mbardin/Cyberinet/zMusic Composition Scores/scores/puzzleFistCompleteDraft - 2023-05-08.pdf

# Puzzle of a Park

## for the Cyberinet

## Matthew A. Bardin

(2023)

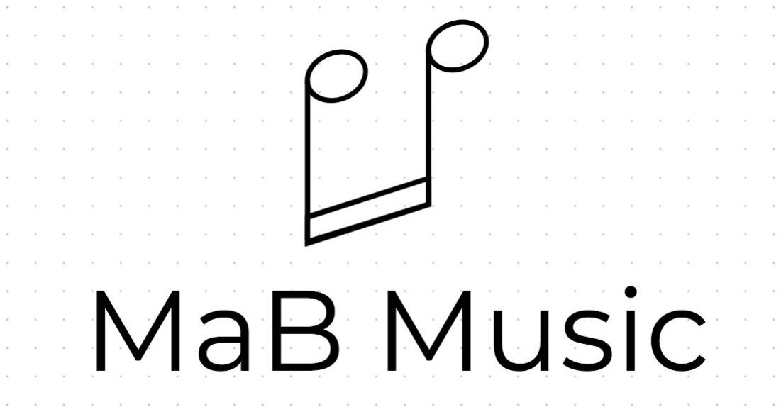
[picture p26: figure]

Program Note:
A pleasant stroll through a park, built through several interconnected ideas. The whole scene can'tcome together until it has been built up from its various smaller pieces. Ideas often take on a different context when observed in a vacuum instead of as a whole, much like putting a large puzzle together.

Performance Note:
While intended to be performed with the Cyberinet, this piece can be performed without it. To do this, a microphone and loop pedal are required. When using this setup, the Max patch (link given below) is not required. If one section of the music is performed out of sync, continue as if this was intended. Thematically, this represents trying to fit a piece of the puzzle where it doesn't actually go. At the beginning of the next section, pressing button 1 should resync the recordings. A short pause between each repetitsion can be done, but should not be an excessive pause.

When performing with the Cyberinet, the button expansion is required. Button 1 is programmed to trigger new recordings and playback, while button 2 can be used to stop the playback in the event of a chatastrophic failure. All of the electronic

On the Cyberinet:
The Cyberinet is an electronic enhancement to the standard B-flat clarinet. By replacing the mouthpiece and barrel with the Cyberinet, the performer and compsoer gain access to an integrated collection of sensors that collect various performance data. This data can be wirelessly transmitted to a computer for electronic processing and software control. An ever-growing list of optional expansions is also available to be connected to the Cyberinet to allow for the performer to customize the instrument ot their performance needs.

The complete list of hardware needed for this composition is:

The Cyberinet
Button Expansion
Microphone
Audio Interface
Computer running the Max patch available here:

On Notation:
This version of the score is intended to show the intended allignment of the previously recorded loops along with the voice currently being played by the soloist. If the solost only wants to look at their line without the playback indicated, that score is available at matthewbardin.com.
In this score, the performer should perform their line (the top of each system) from beginning to end without stopping. A short pause between each repetitsion can be done, but should not be an excessive pause.
Notes shown with a cross notehead indicate when a button should be pressed. These button presses, when performed in sync, will cause the current recording to stop, start the new recording, and playback all previous recordings in sync.

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

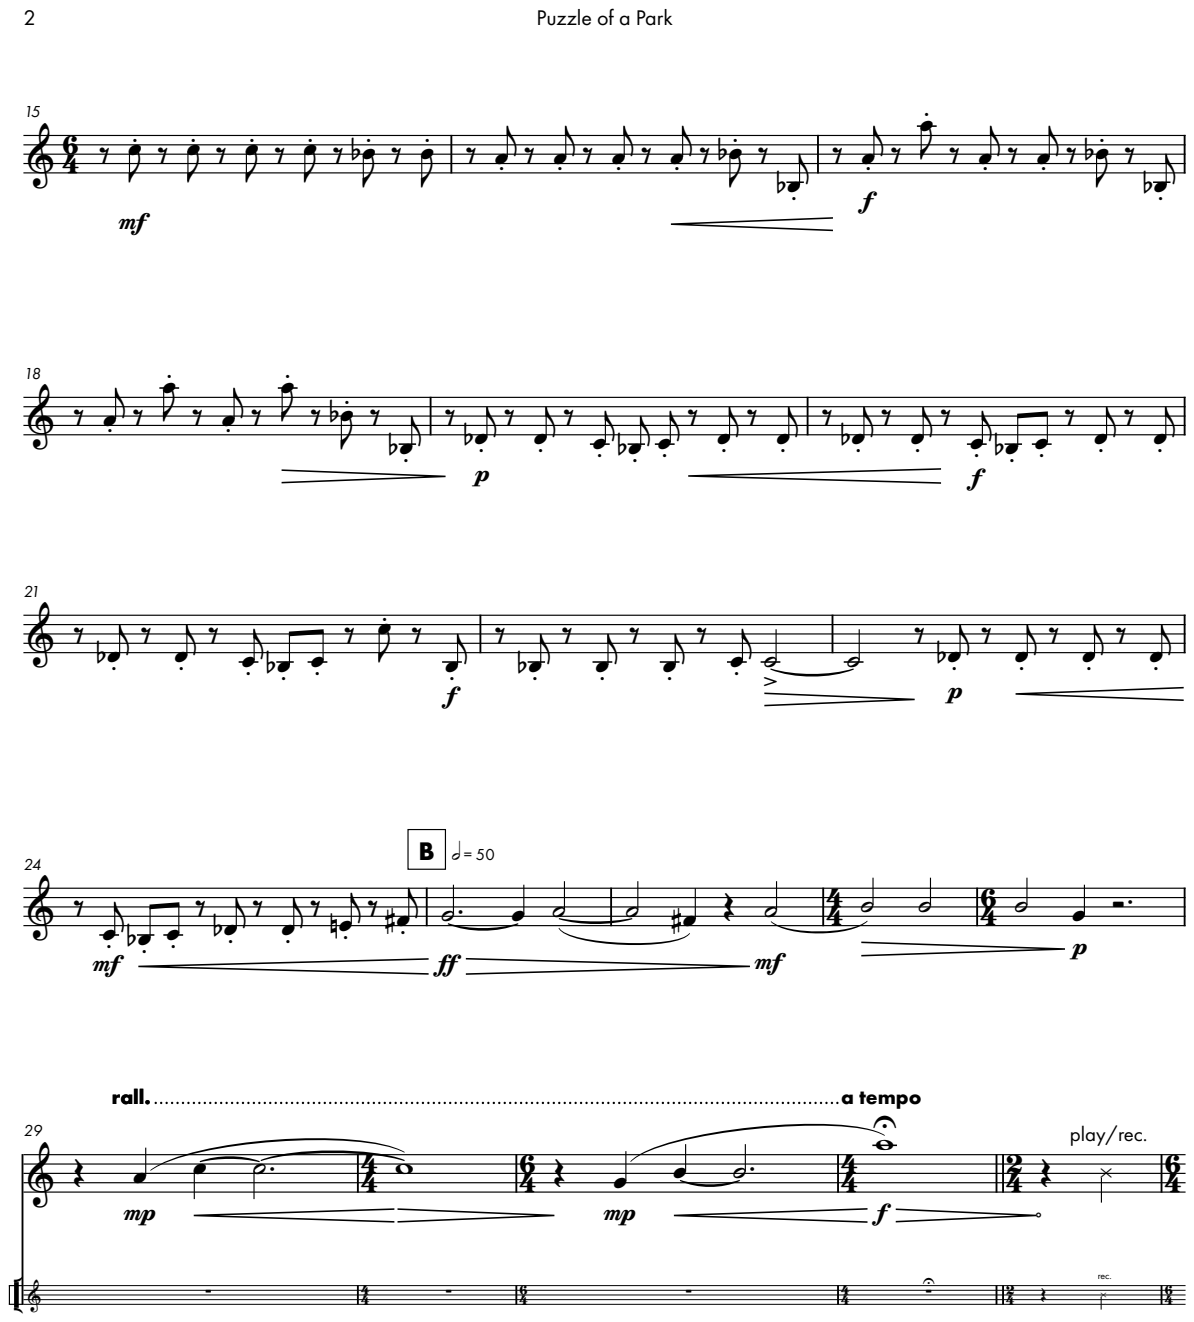
[picture p27: page 6]

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

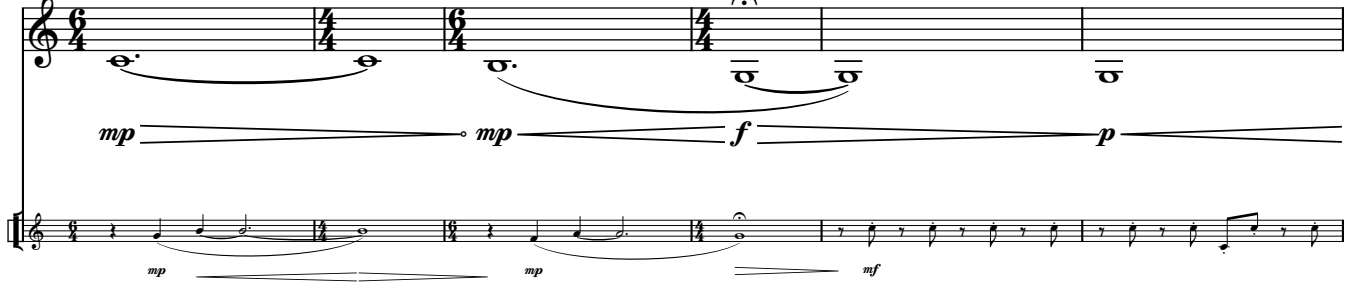
[picture p28: figure]

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

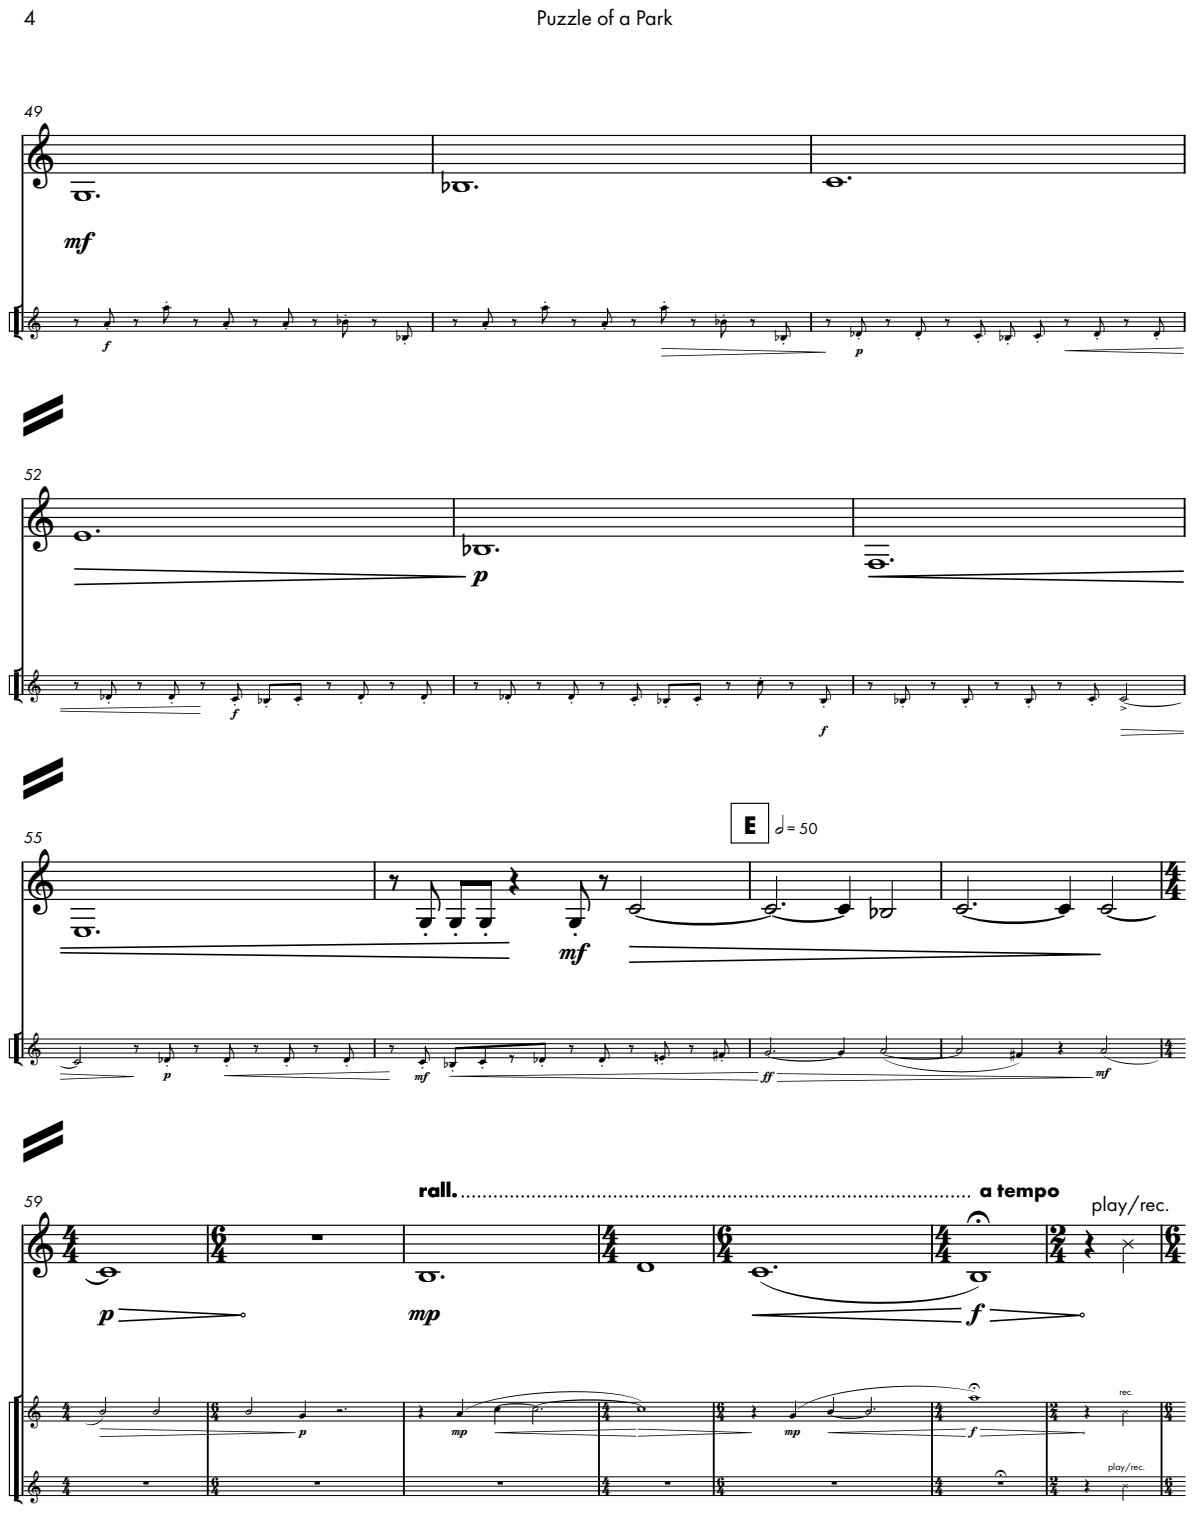
[picture p29: page 8]

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

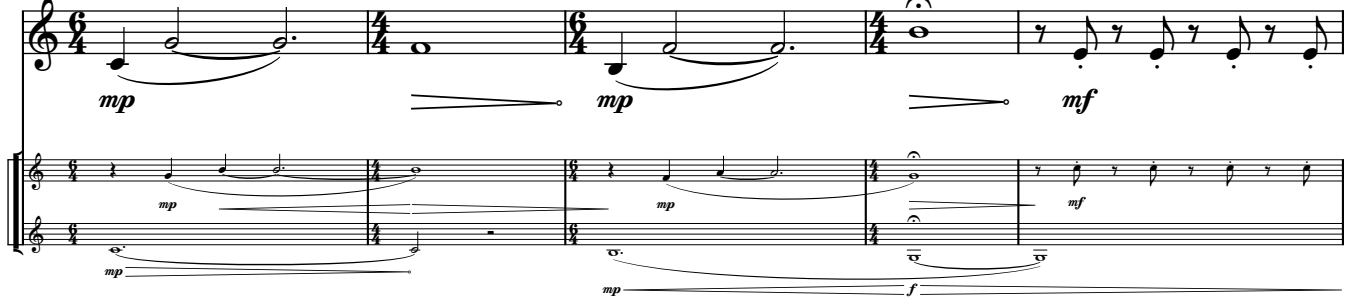
[picture p30: figure]

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

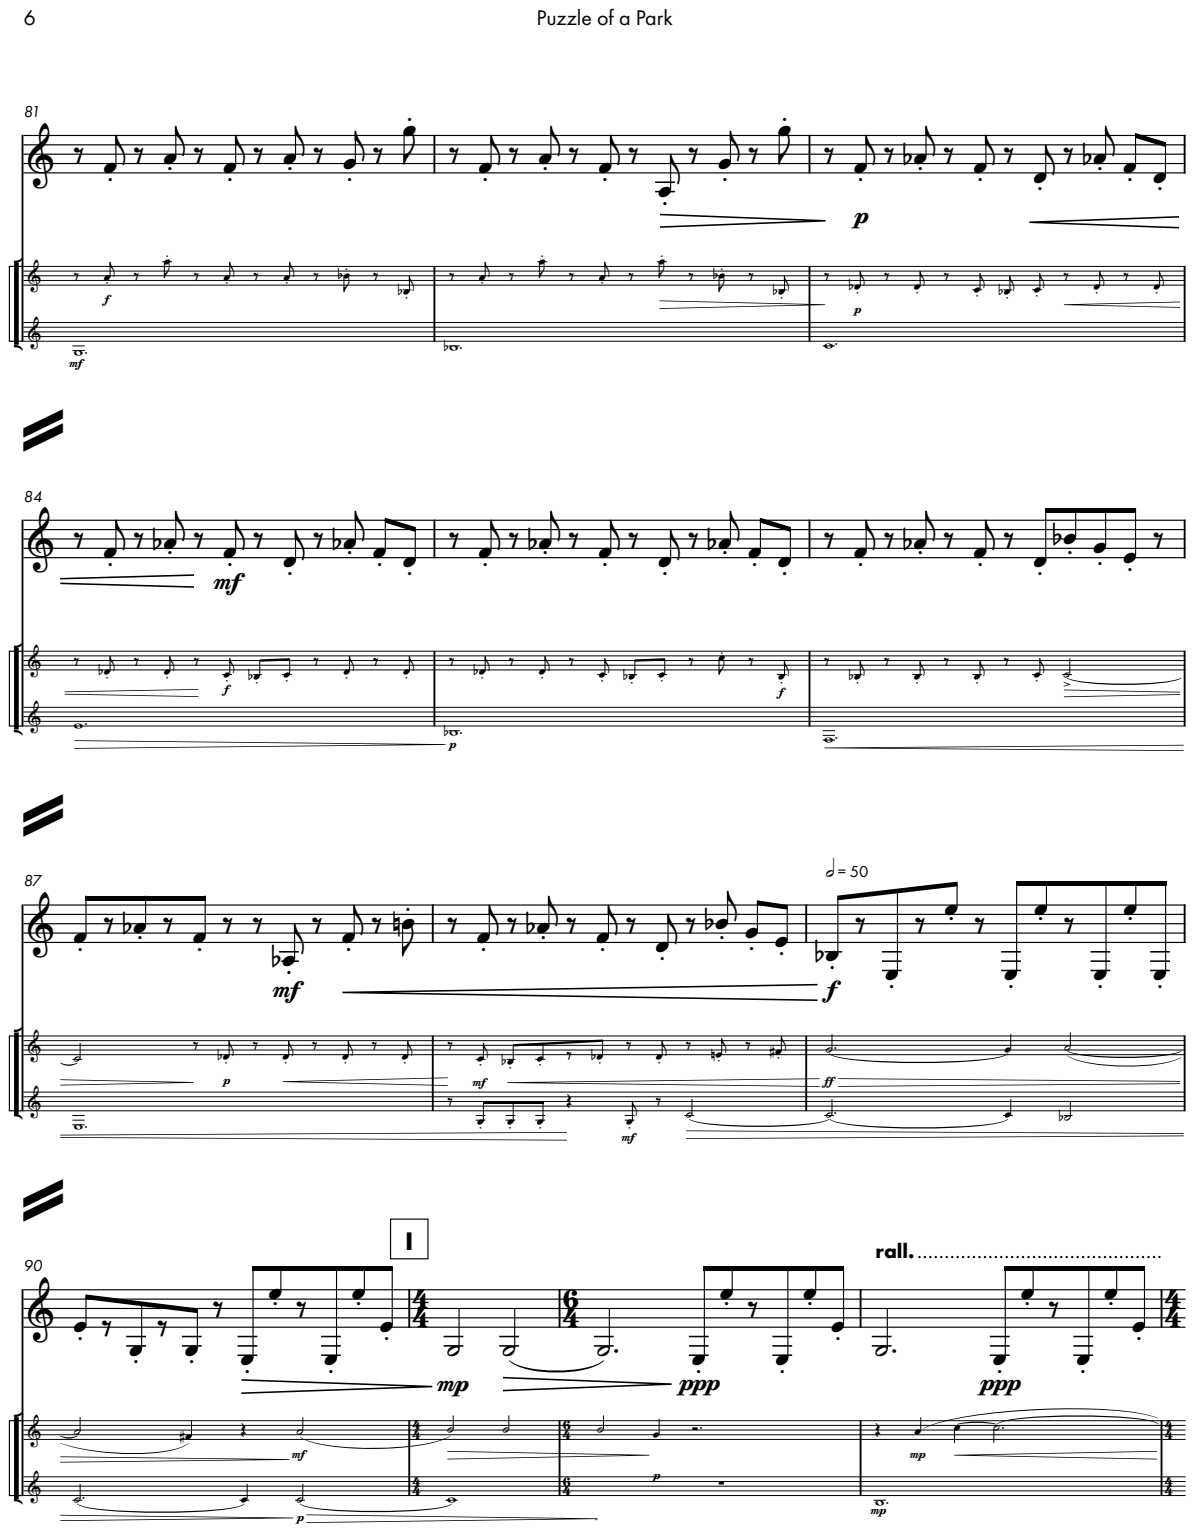
[picture p31: page 10]

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

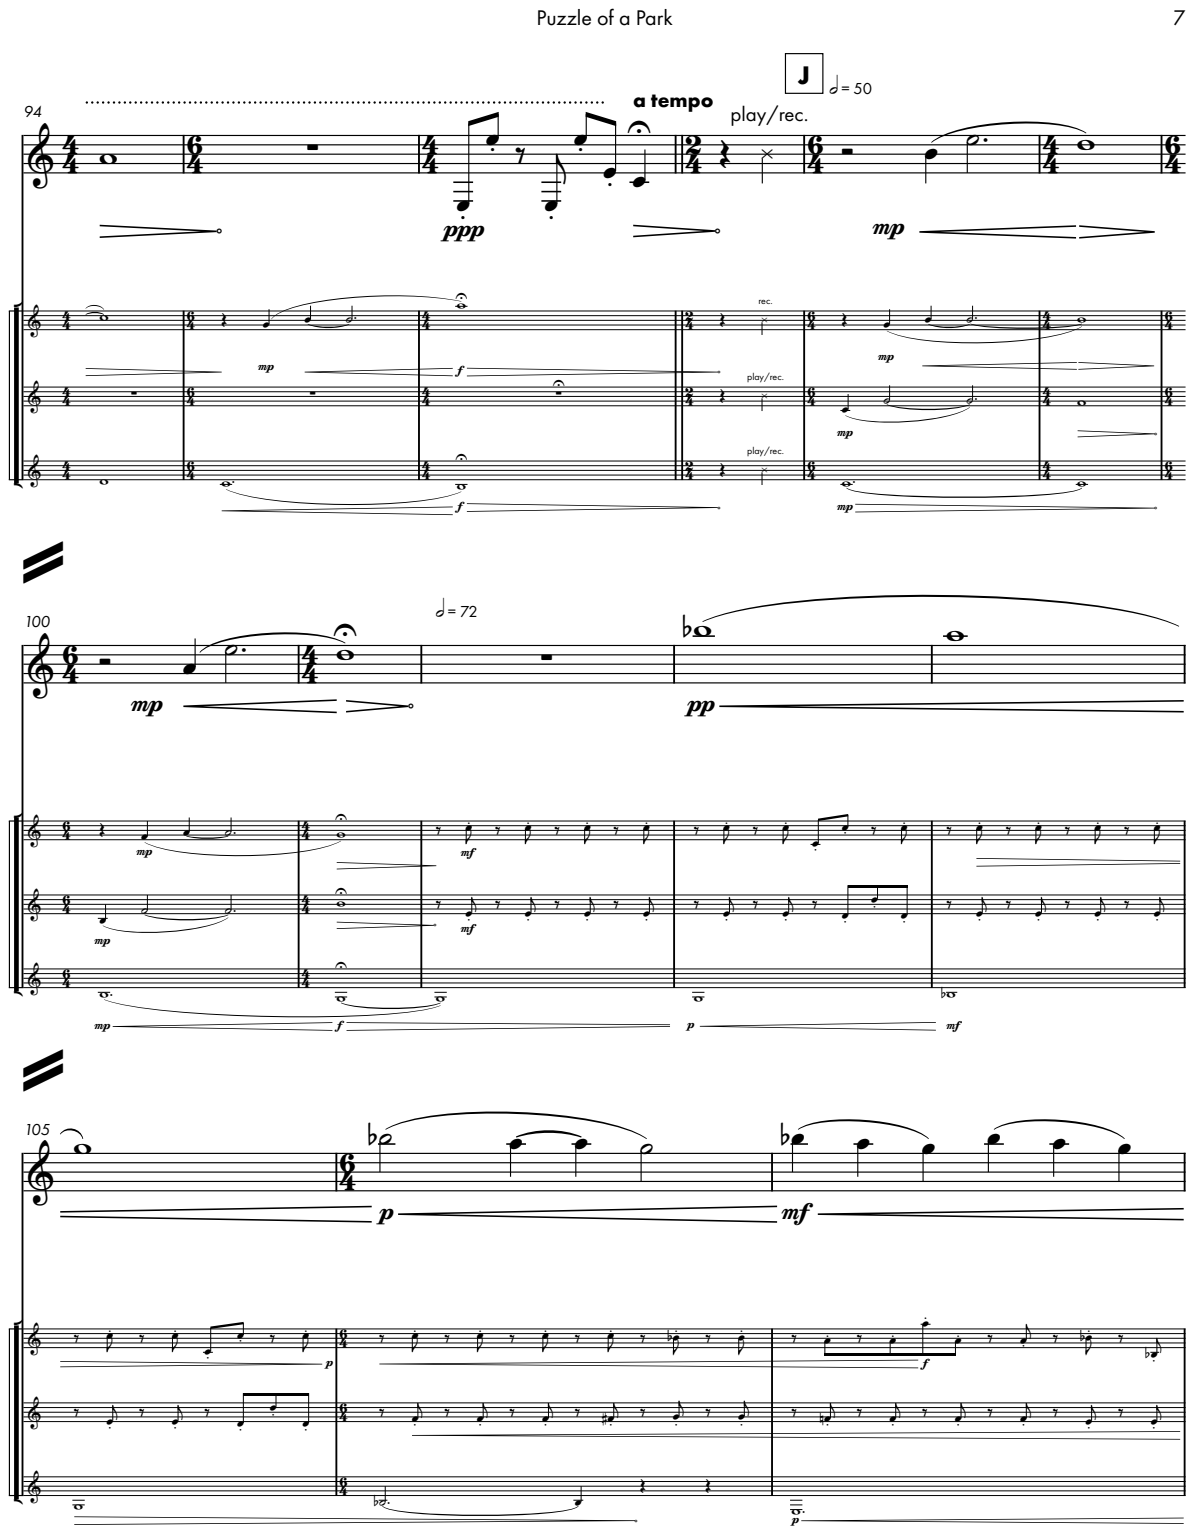
[picture p32: page 11]

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

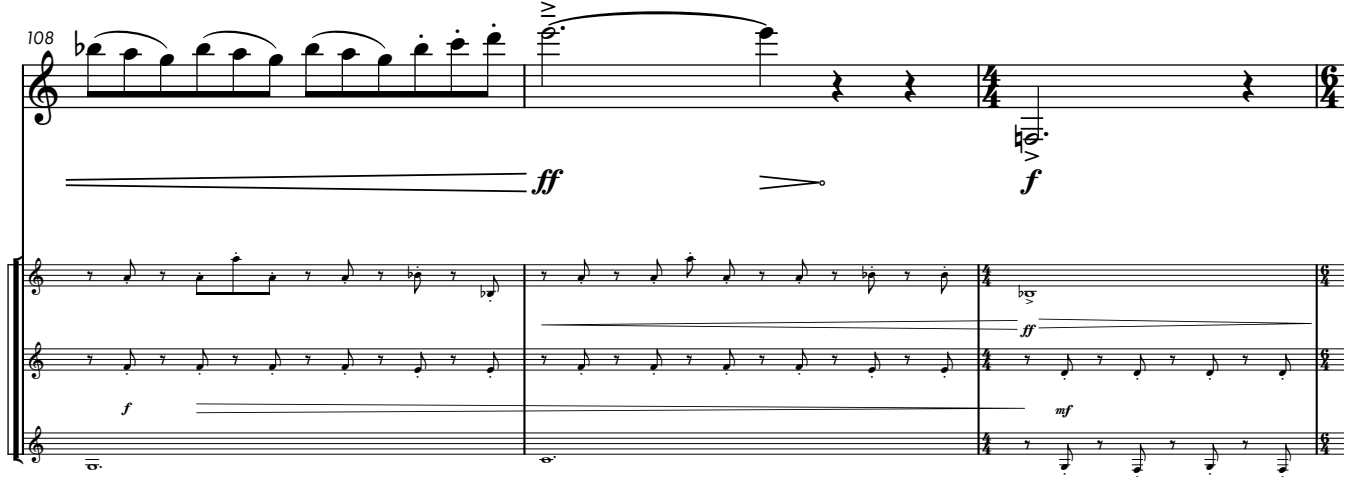
[picture p33: figure]
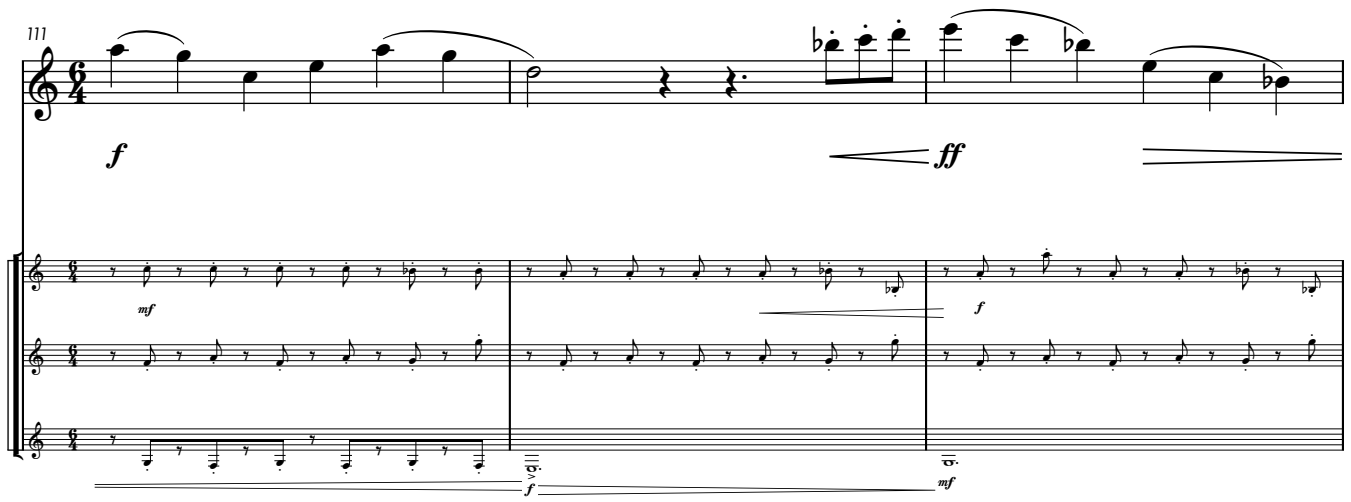
[picture p34: figure]
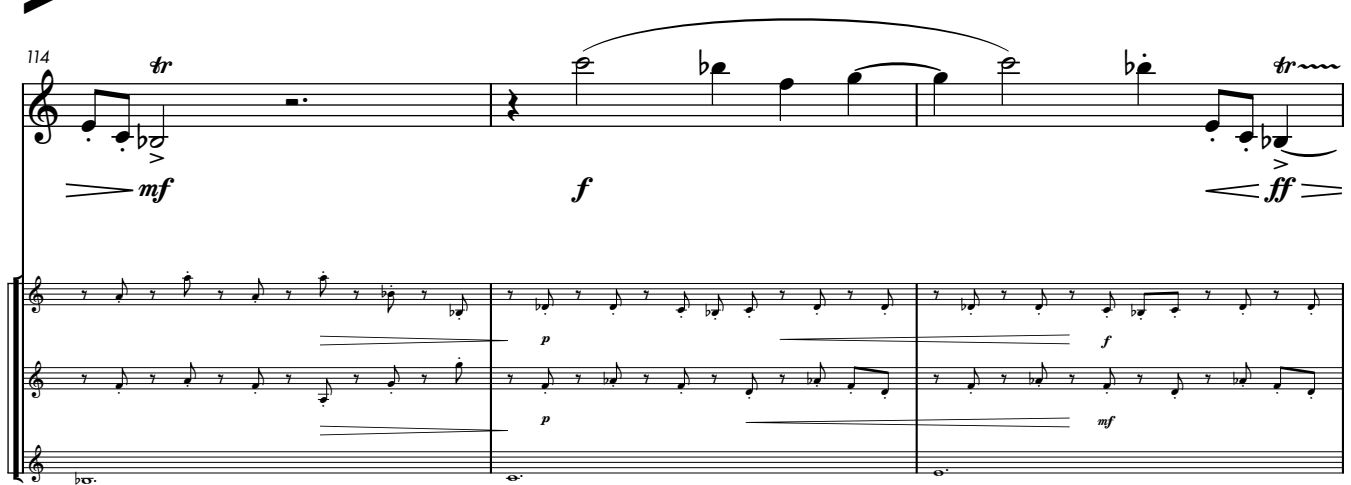
[picture p35: figure]

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

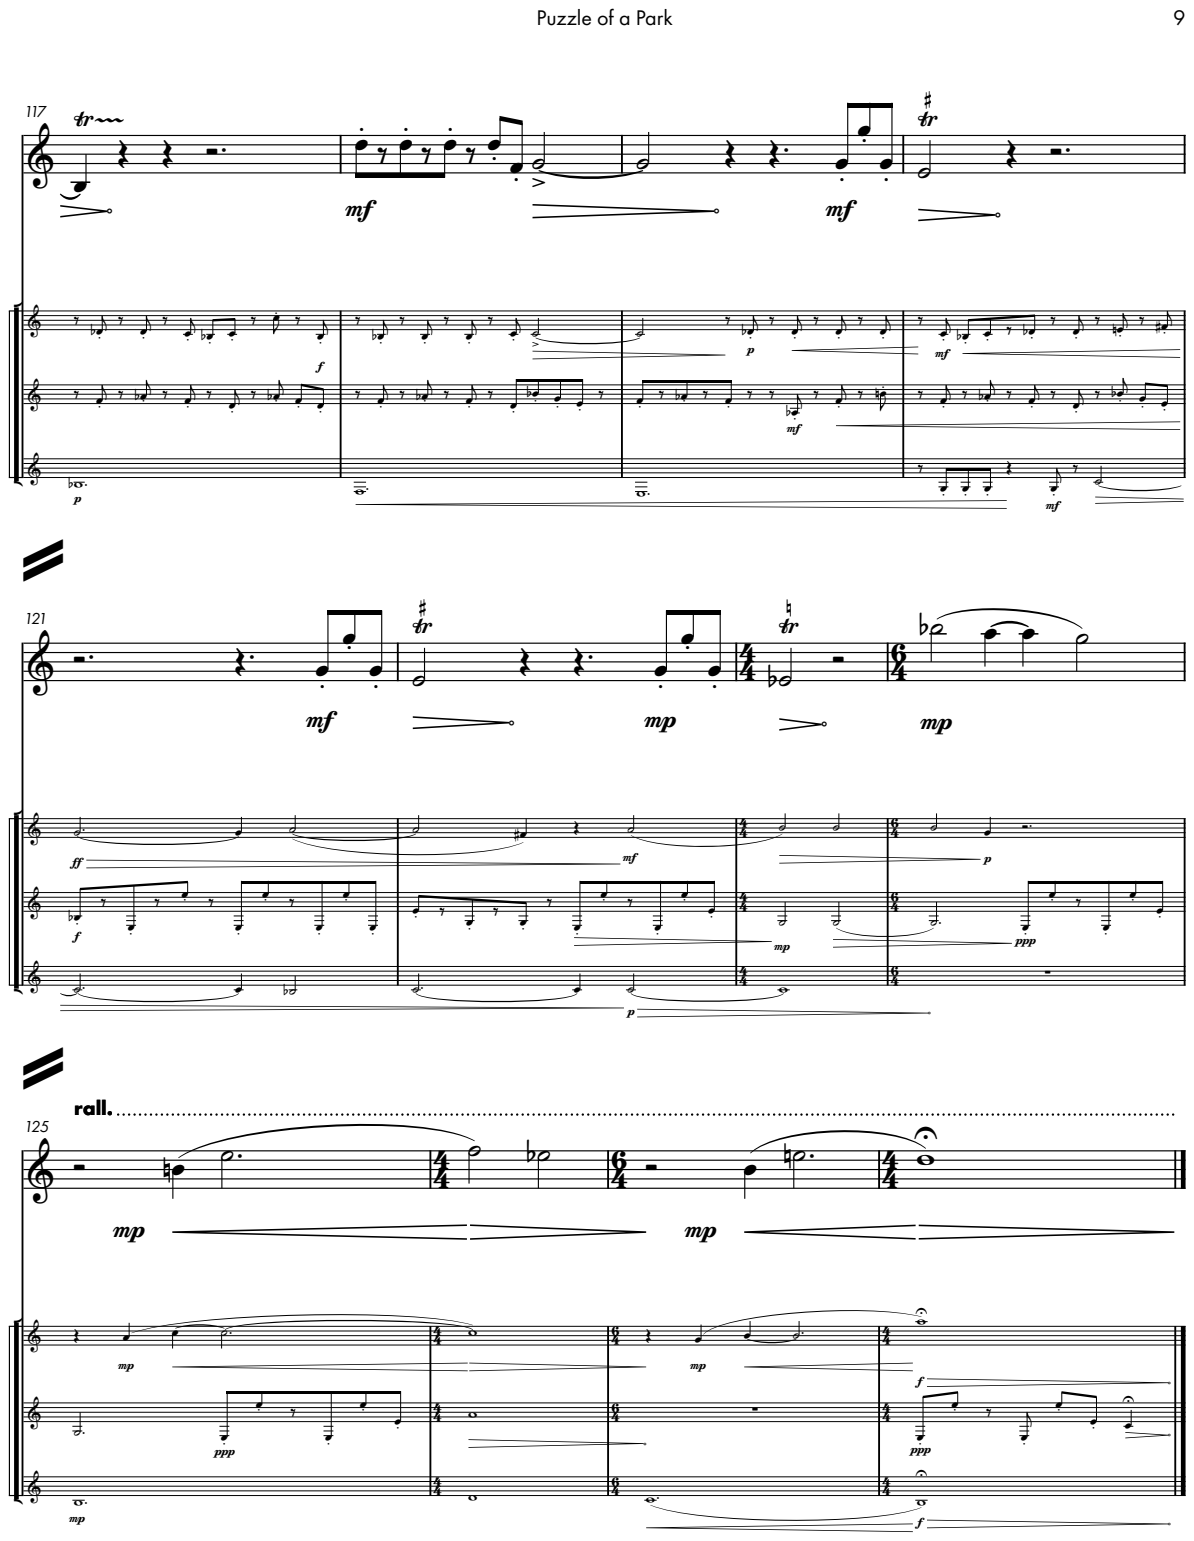
[picture p36: page 13]
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
