mbardin/Cyberinet/Music Composition Scores/raindrops/raindrops_Part1.pdf

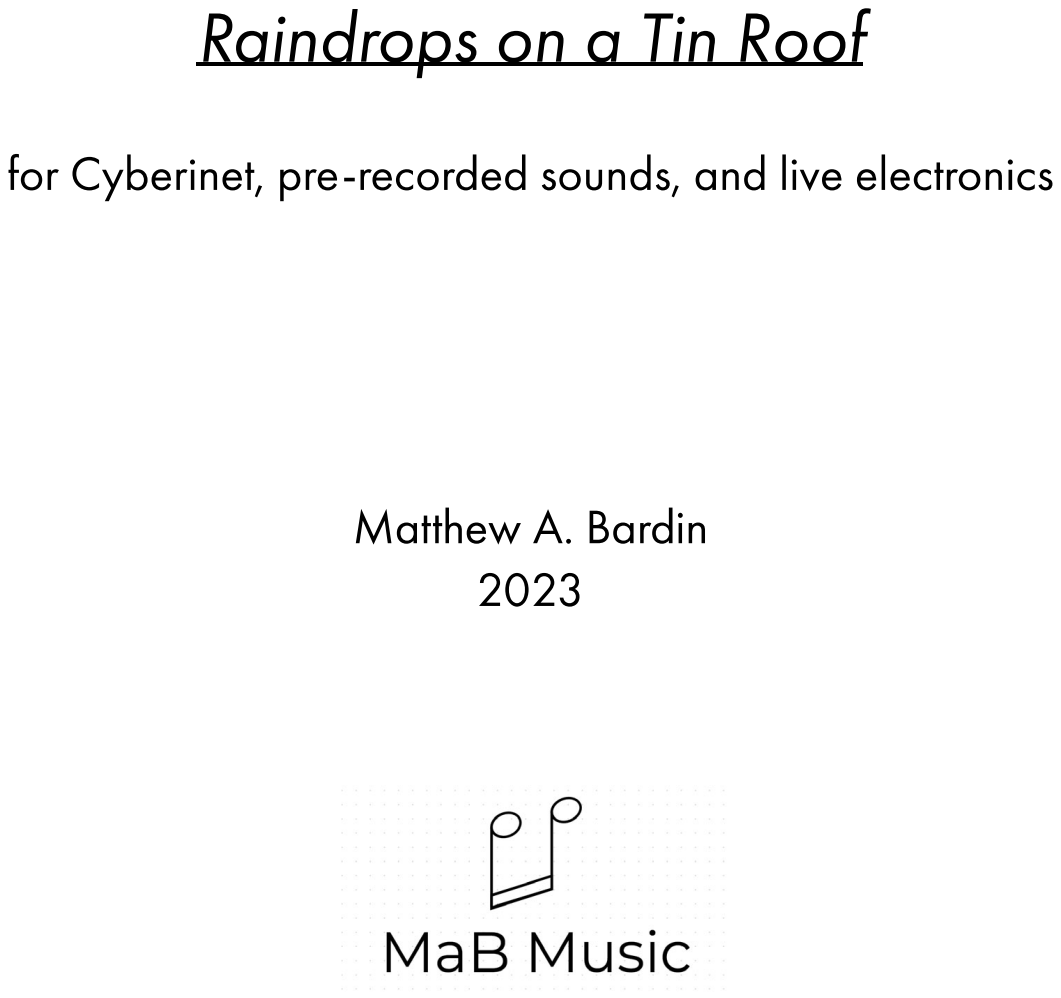
[picture p38: page 1]
