mbardin/Cyberinet/Music Composition Scores/raindrops/raindrops_Part19.pdf

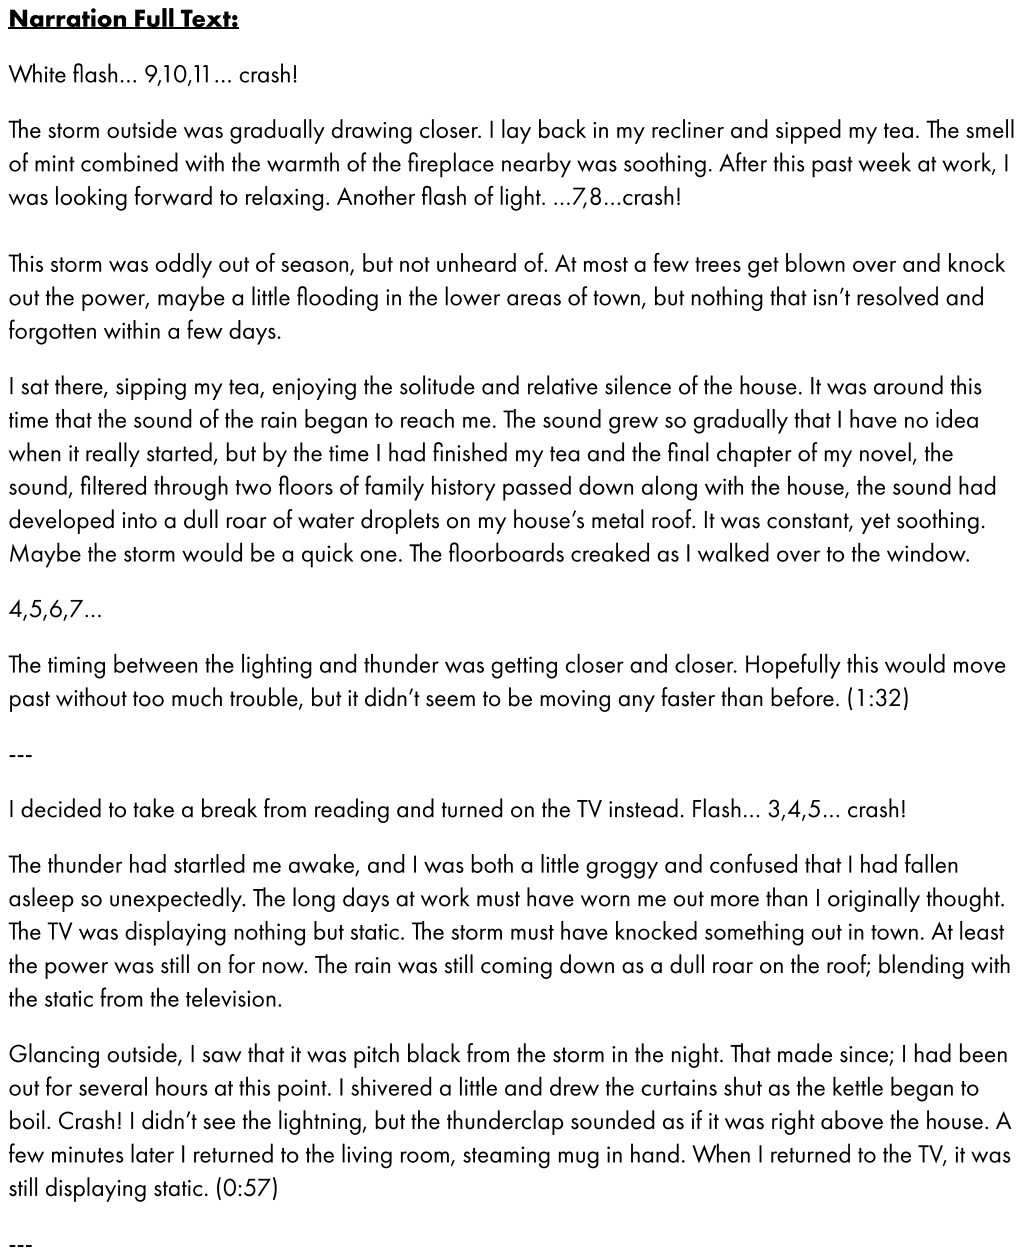
[picture p39: page 1]
