mbardin/Cyberinet/Music Composition Scores/raindrops/raindrops_Part21.pdf

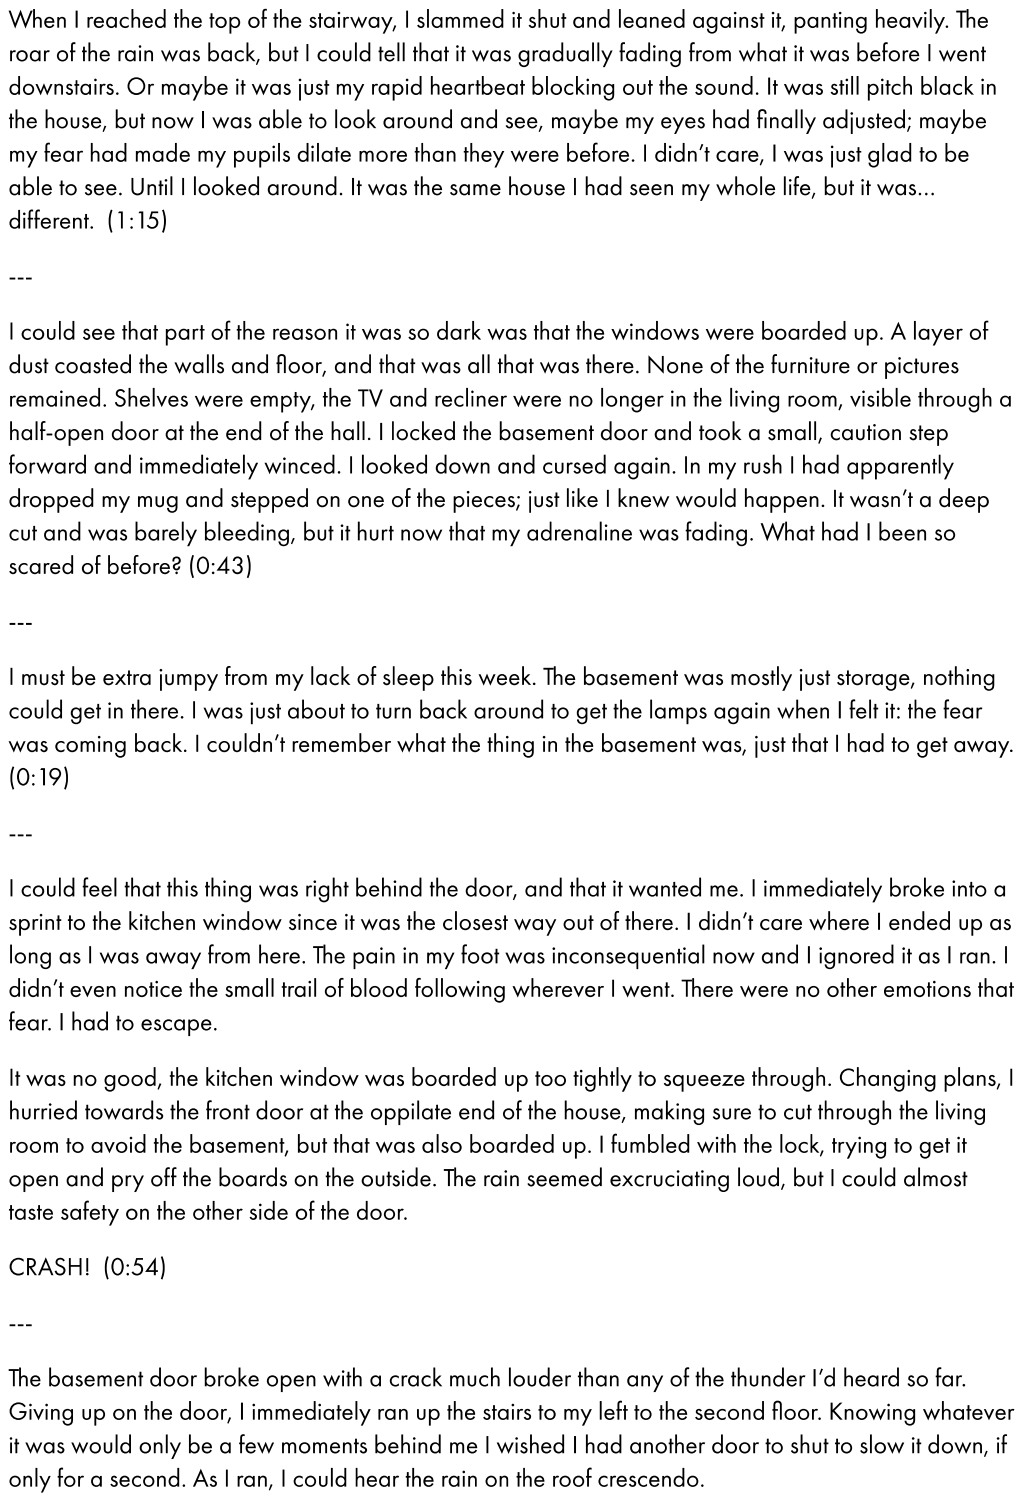
[picture p40: page 1]
