mbardin/Cyberinet/Music Composition Scores/raindrops/raindrops_Part22.pdf

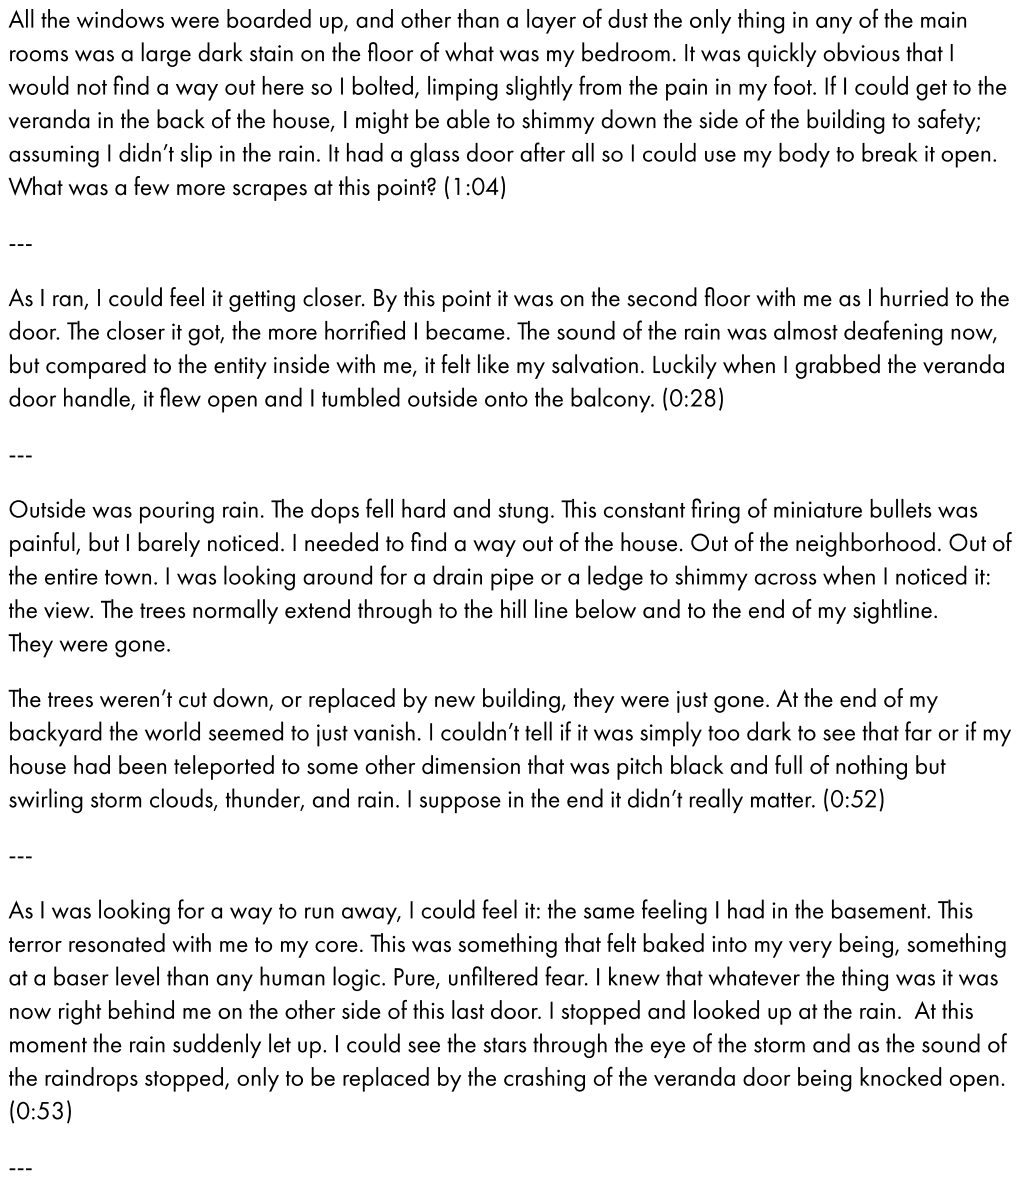
[picture p41: page 1]
