mbardin/Cyberinet/Music Composition Scores/raindrops/raindrops_Part3.pdf

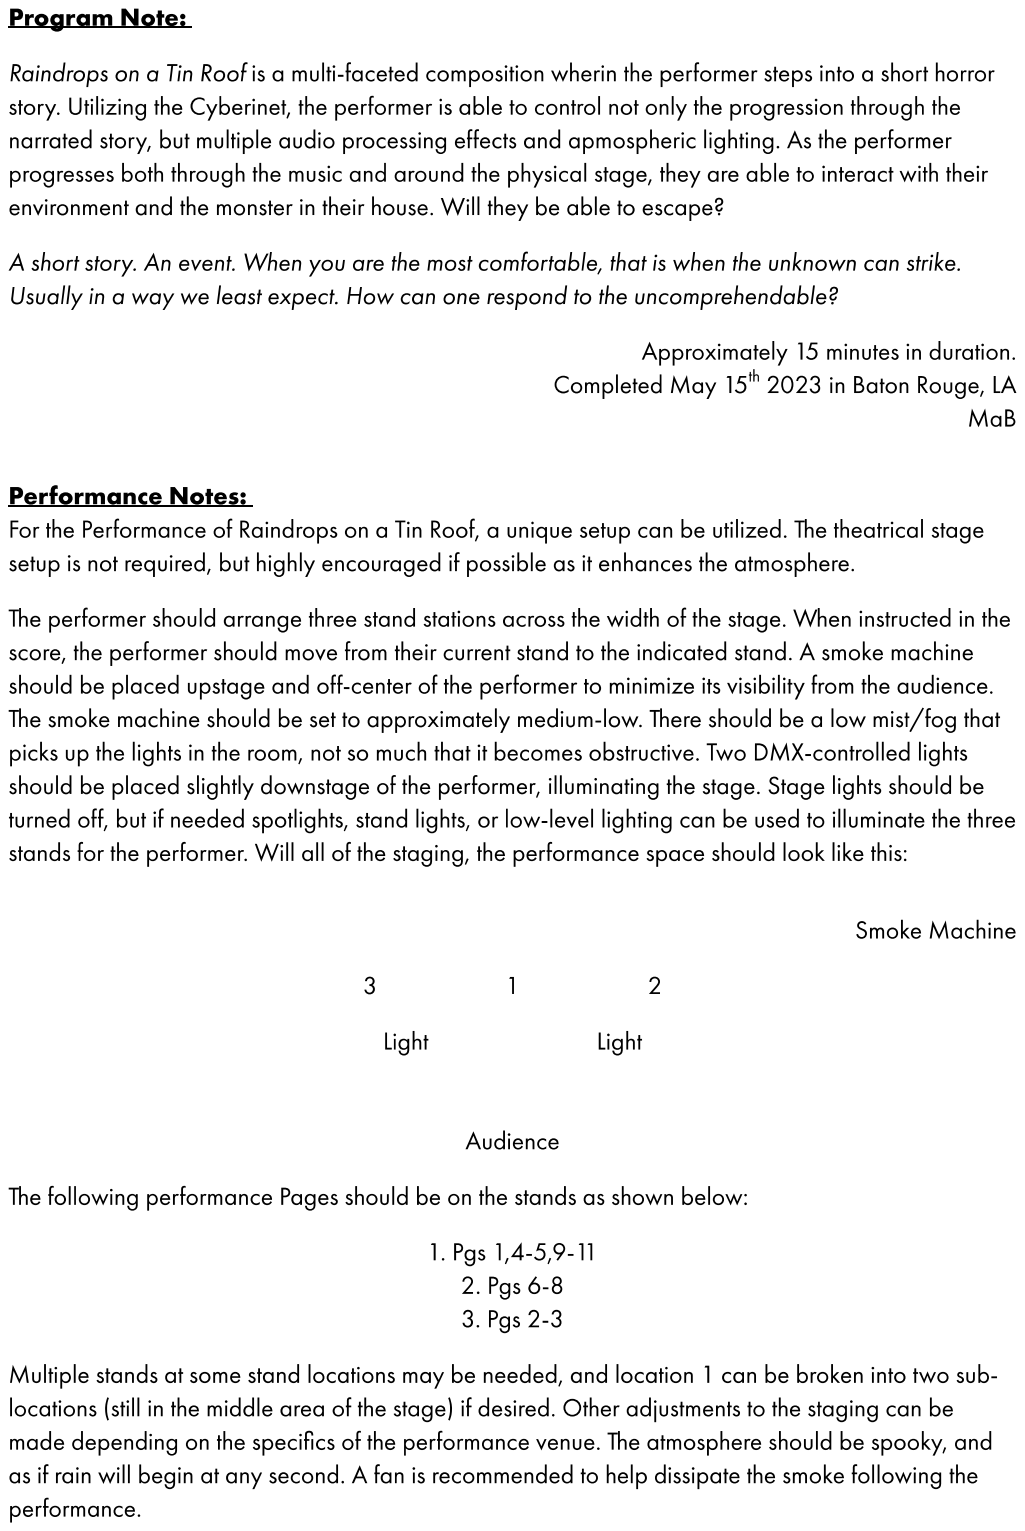
[picture p42: page 1]
