mbardin/Cyberinet/Music Composition Scores/raindrops/raindrops_Part4.pdf

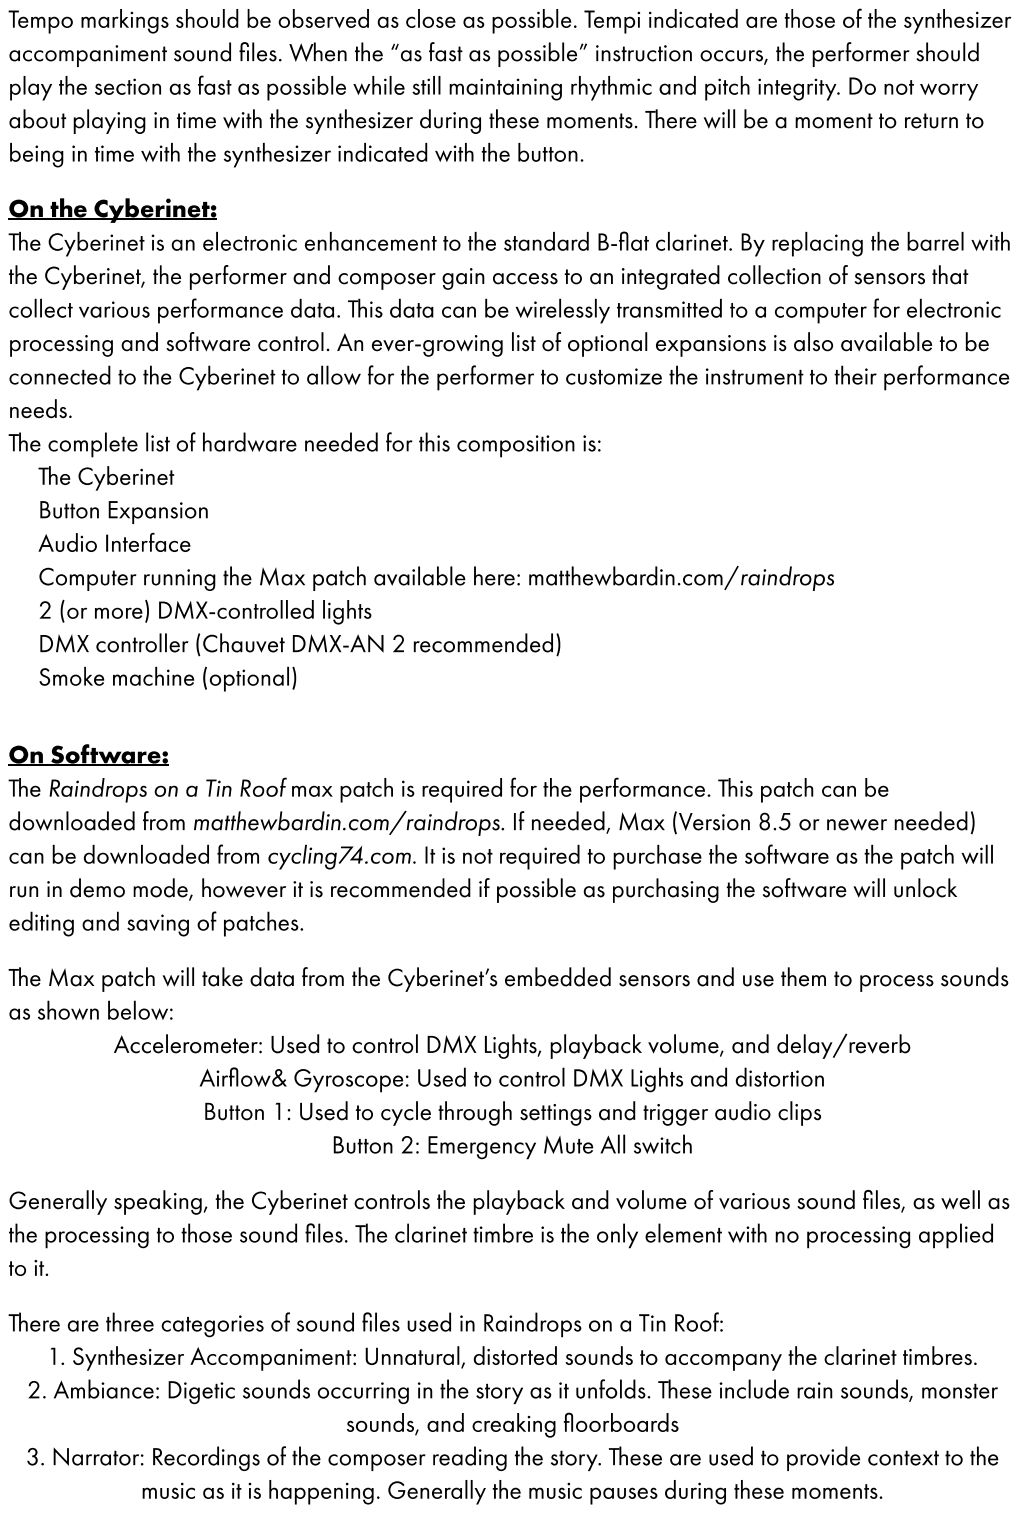
[picture p43: page 1]
