mbardin/Cyberinet/Music Composition Scores/raindrops/raindrops_Part5.pdf

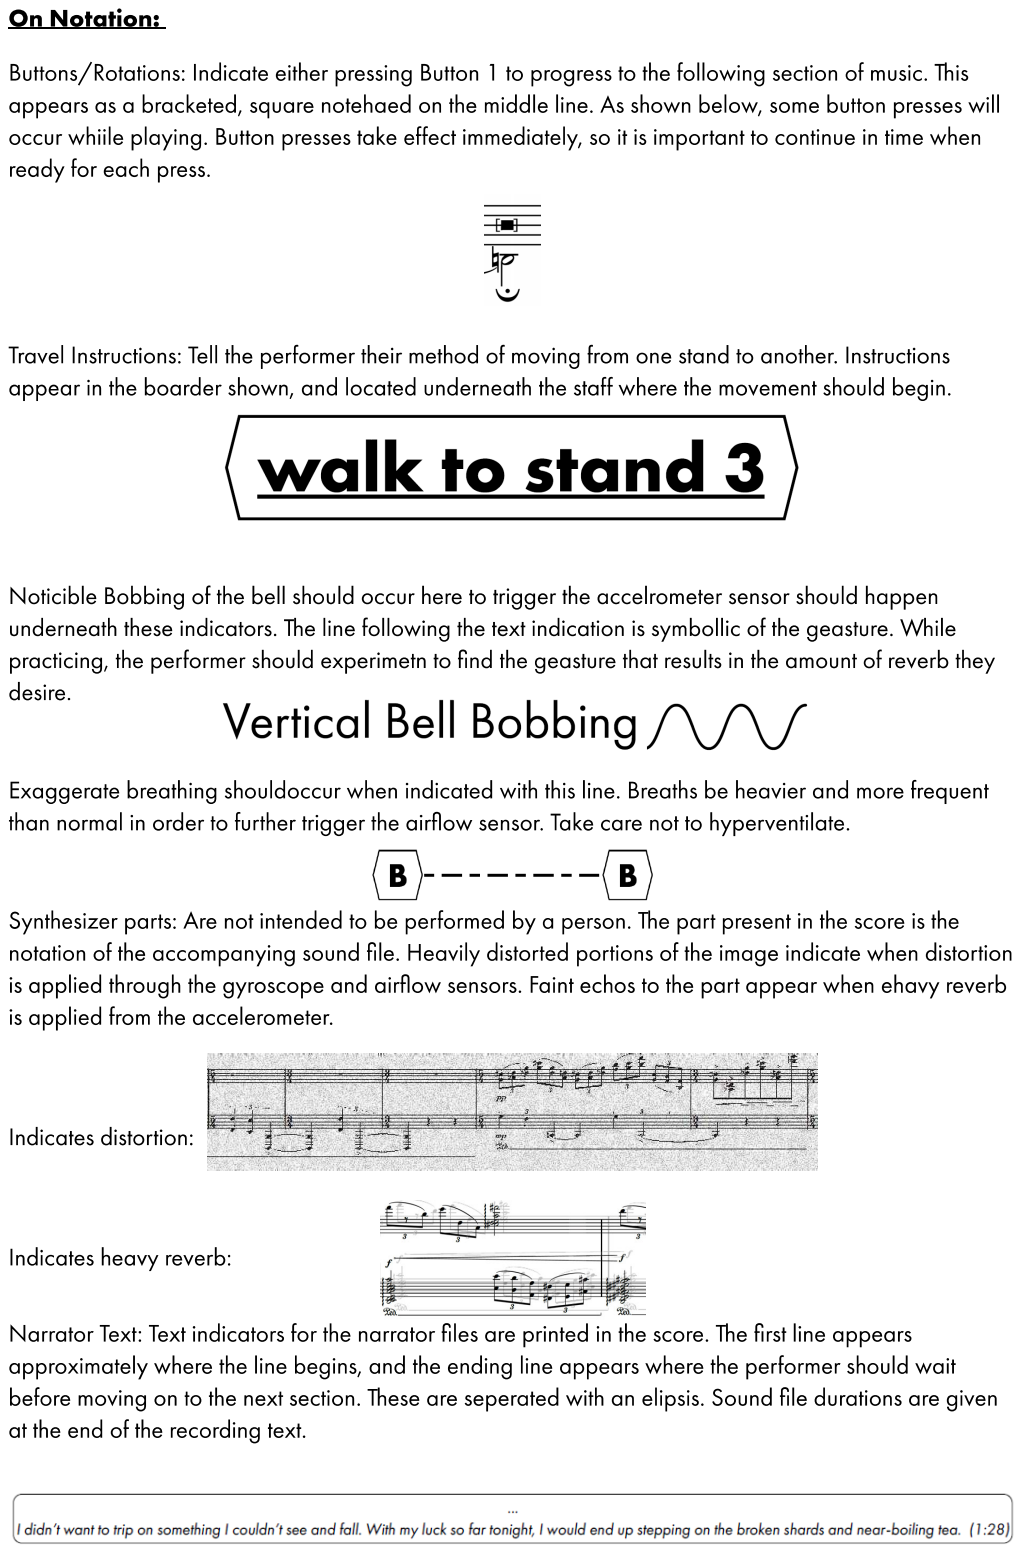
[picture p44: page 1]
