mbardin/Cyberinet/Music Composition Scores/New folder/Ethereal Presence - 2023-05-20_Part1.pdf

## Ethereal Presence

for Cyberinet

Matthew A. Bardin

2023
