mbardin/Cyberinet/Music Composition Scores/New folder/Ethereal Presence - 2023-05-20_Part13.pdf

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
