mbardin/Cyberinet/Music Composition Scores/New folder/puzzleFistCompleteDraft - 2023-05-20_Part1.pdf

# Puzzle of a Park

for the Cyberinet

Matthew A. Bardin
(2023)

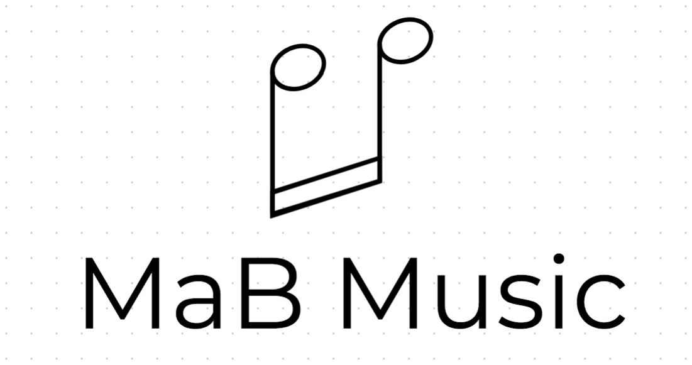
[picture p45: figure]
