mbardin/Cyberinet/other documentation/photos/71ZmRaGMQ4L._AC_SX679_.jpg

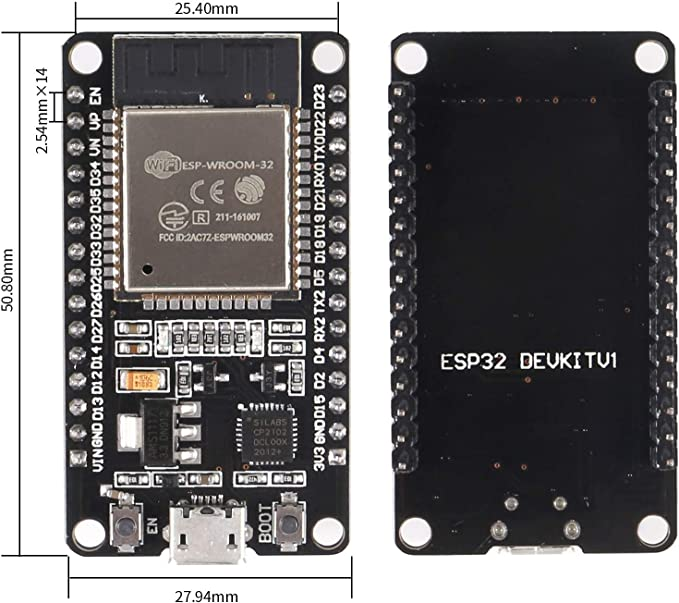
other documentation/photos/71ZmRaGMQ4L._AC_SX679_.jpg
