mbardin/Cyberinet/other documentation/photos/1683-07.jpg

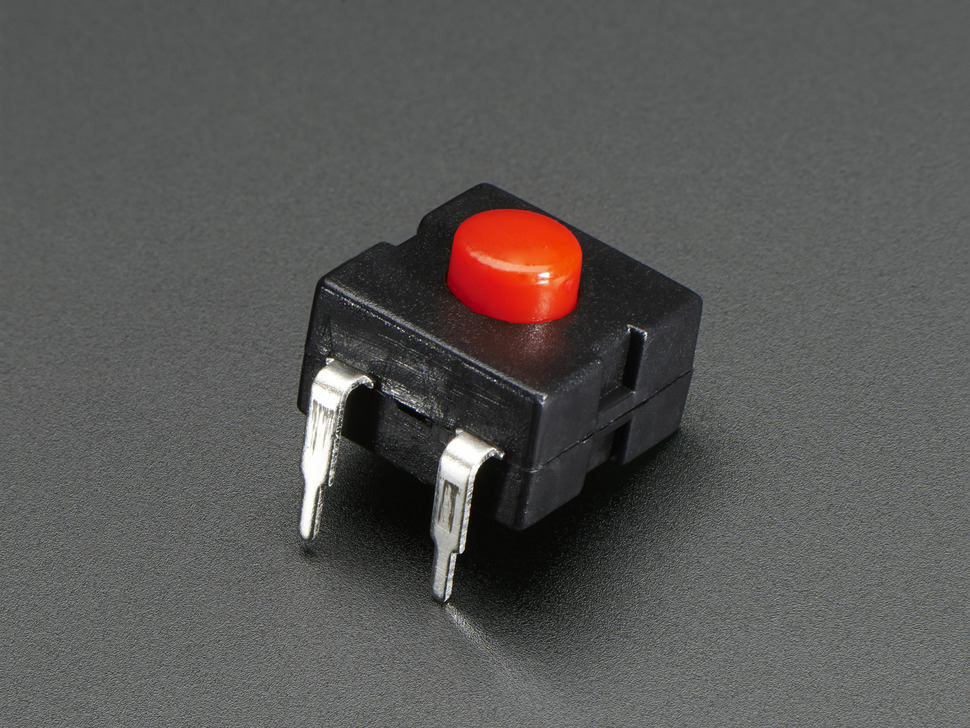
other documentation/photos/1683-07.jpg
