mbardin/Cyberinet/other documentation/photos/5180-01.jpg

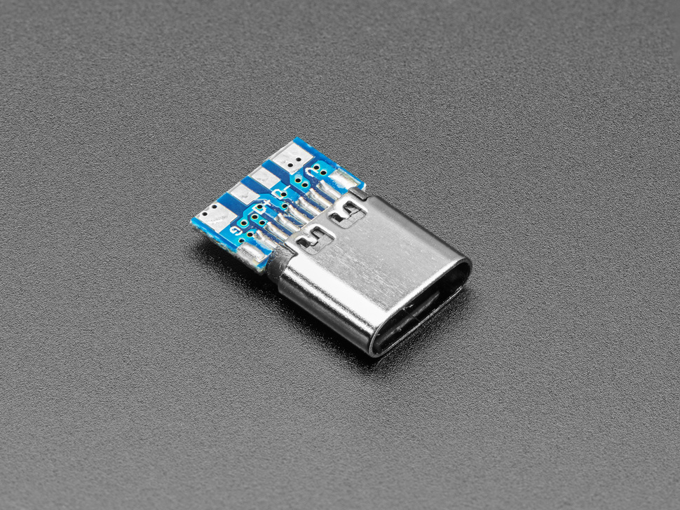
other documentation/photos/5180-01.jpg
