mbardin/Cyberinet/other documentation/photos/brun.jpg

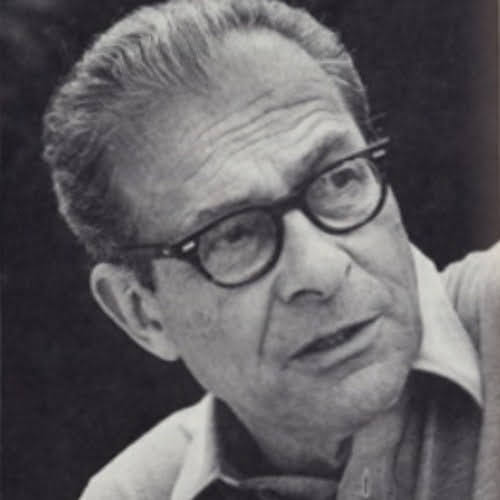
other documentation/photos/brun.jpg
