mbardin/Cyberinet/other documentation/photos/buttons1.2.png

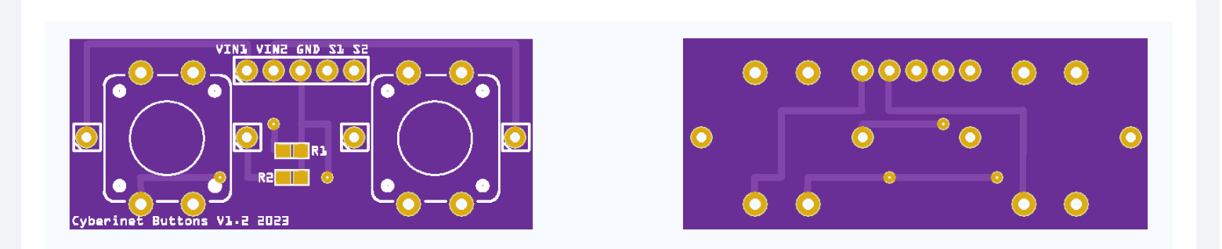
other documentation/photos/buttons1.2.png
