mbardin/Cyberinet/other documentation/photos/cage2.webp

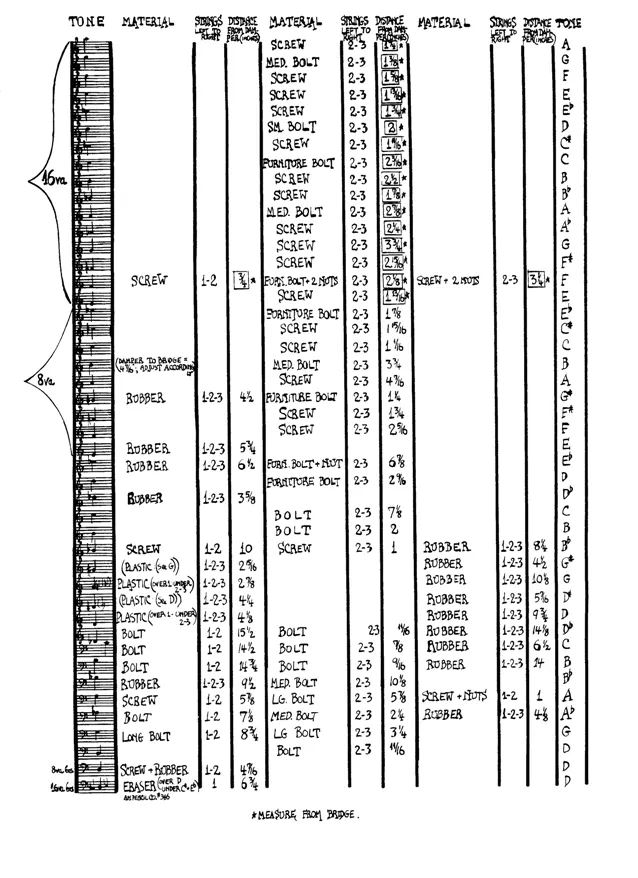
other documentation/photos/cage2.webp
