mbardin/Cyberinet/other documentation/photos/CNET.click~.png

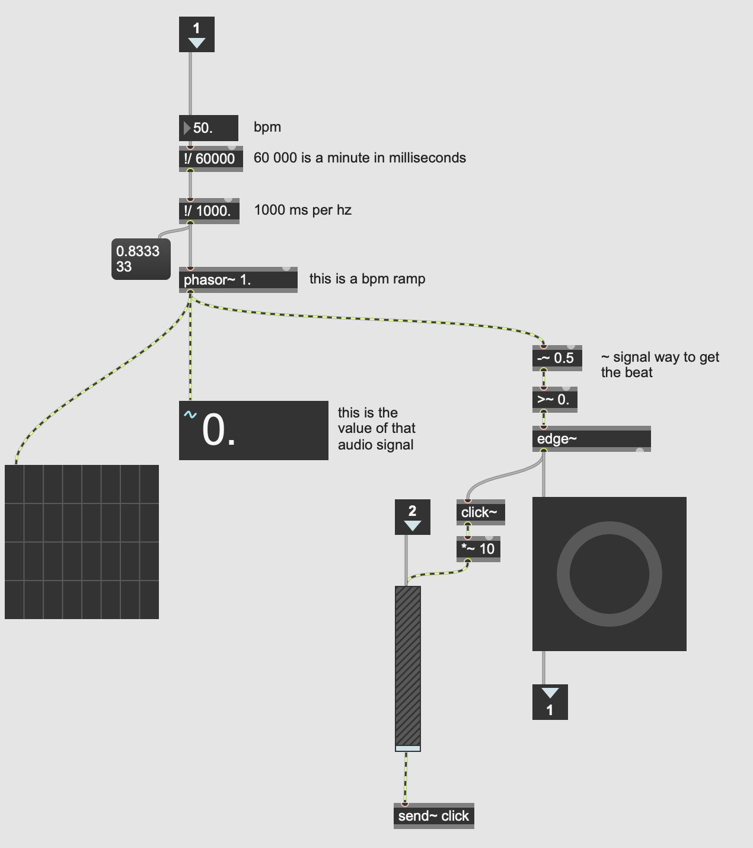
other documentation/photos/CNET.click~.png
