mbardin/Cyberinet/other documentation/photos/CNET.compressor~.png

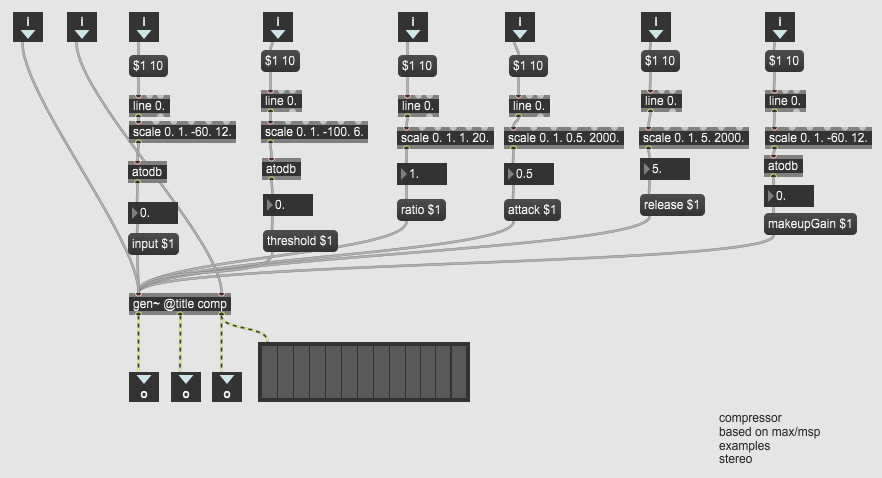
other documentation/photos/CNET.compressor~.png
