mbardin/Cyberinet/other documentation/photos/CNET.delay~.png

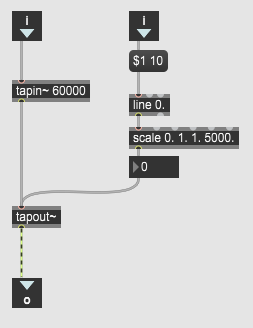
other documentation/photos/CNET.delay~.png
