mbardin/Cyberinet/other documentation/photos/CNET.dmx.png

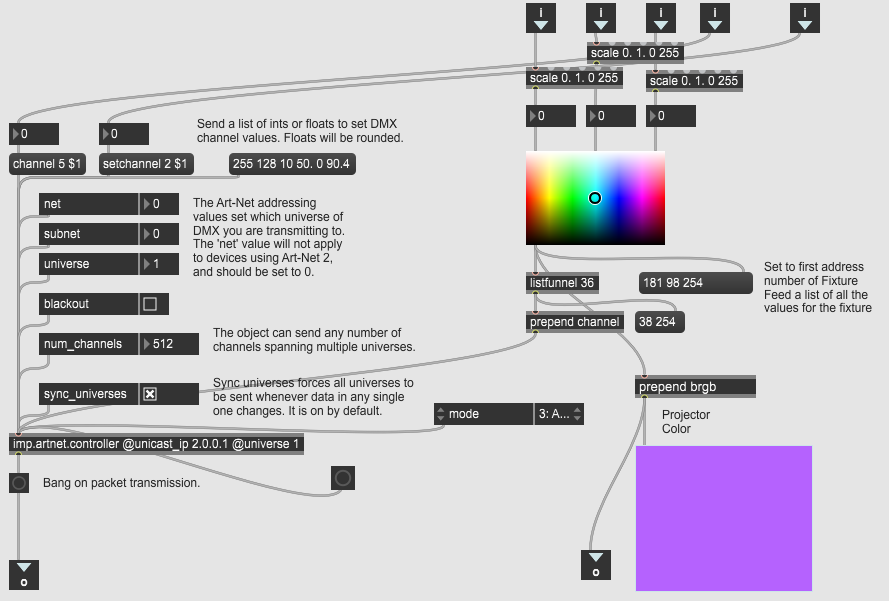
other documentation/photos/CNET.dmx.png
