mbardin/Cyberinet/other documentation/photos/CNET.feedbackDelay~.png

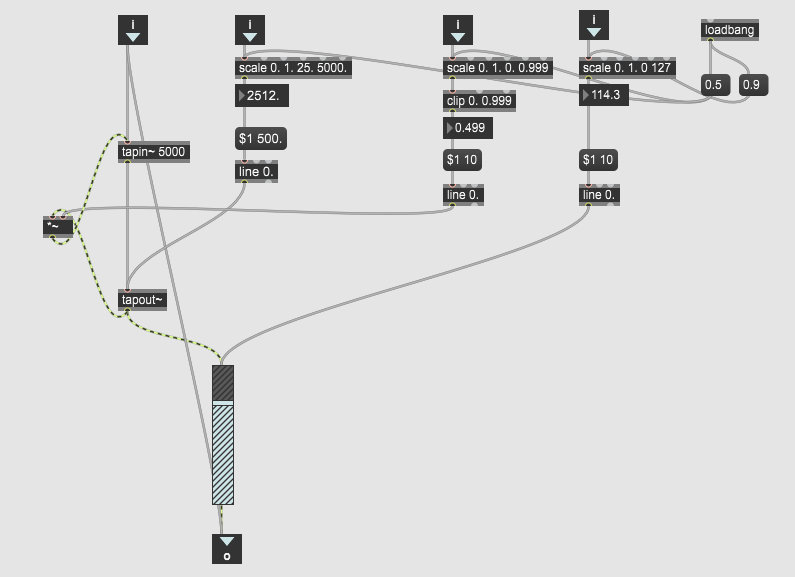
other documentation/photos/CNET.feedbackDelay~.png
