mbardin/Cyberinet/other documentation/photos/CNET.kStrong.png

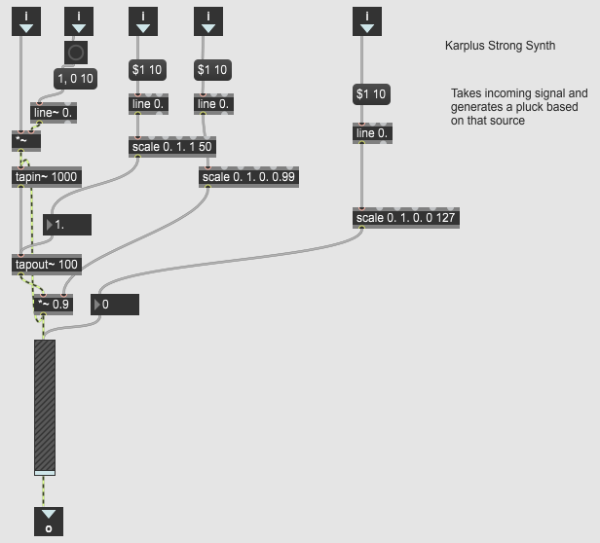
other documentation/photos/CNET.kStrong.png
