mbardin/Cyberinet/other documentation/photos/CNET.multDel~.png

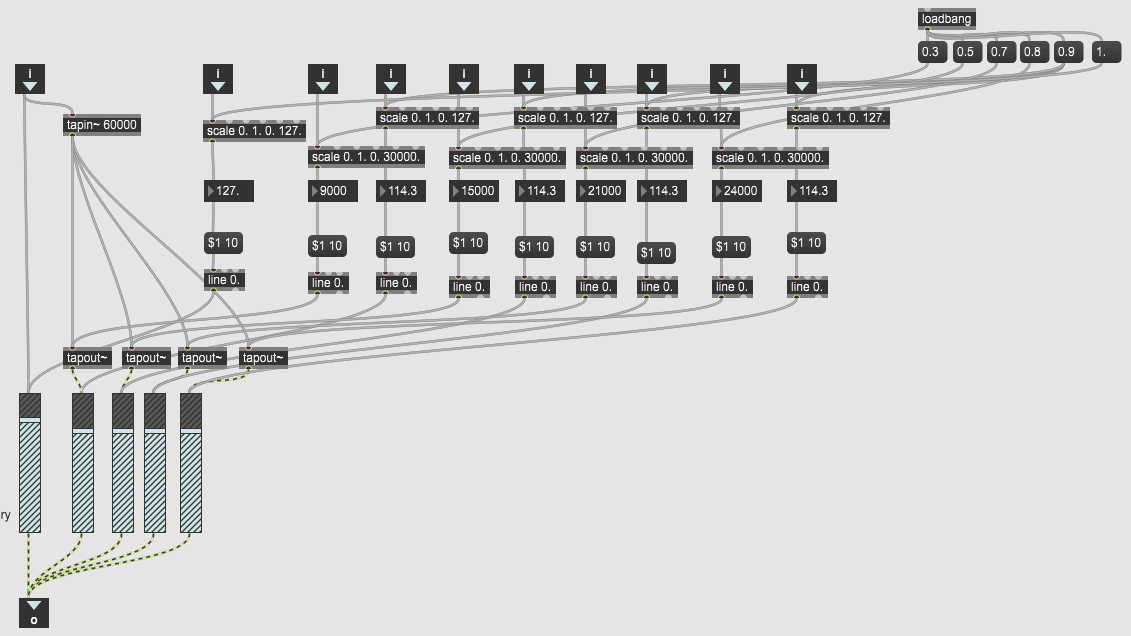
other documentation/photos/CNET.multDel~.png
