mbardin/Cyberinet/other documentation/photos/CNET.pitchShift~.png

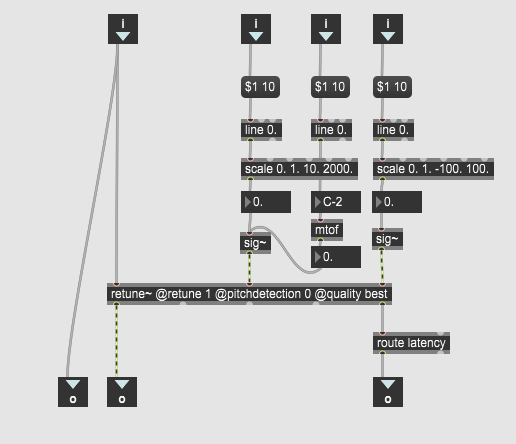
other documentation/photos/CNET.pitchShift~.png
