mbardin/Cyberinet/other documentation/photos/CNET.rangeSet.png

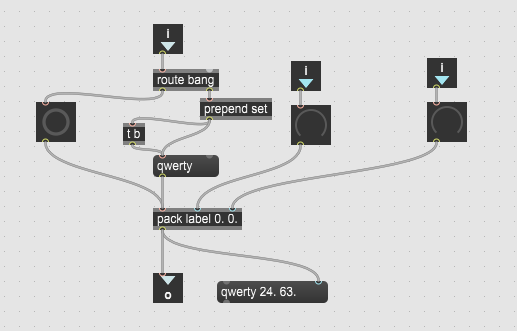
other documentation/photos/CNET.rangeSet.png
