mbardin/Cyberinet/other documentation/photos/CNET.receive.png

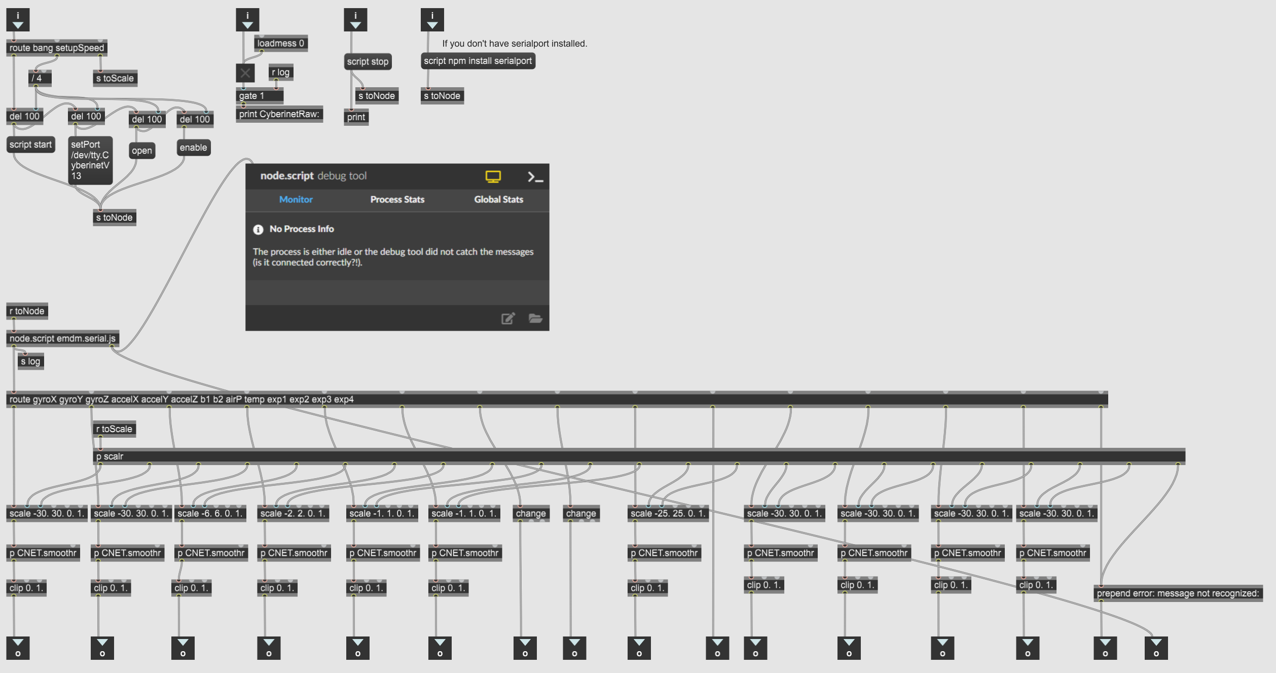
other documentation/photos/CNET.receive.png
