mbardin/Cyberinet/other documentation/photos/CNET.reverb~.png

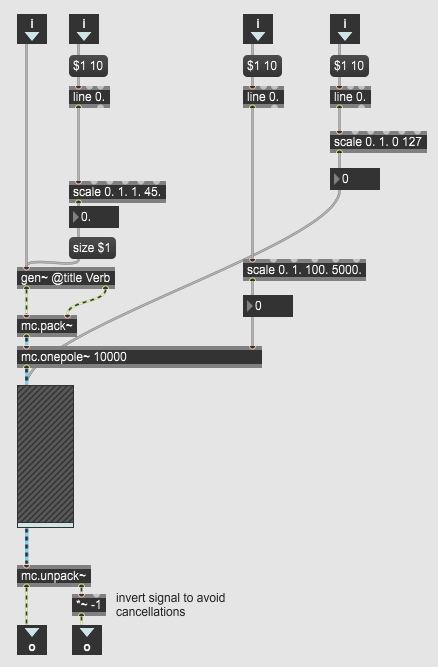
other documentation/photos/CNET.reverb~.png
