mbardin/Cyberinet/other documentation/photos/CNET.tuner~.png

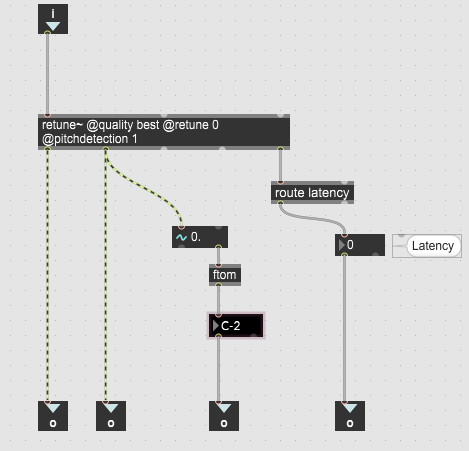
other documentation/photos/CNET.tuner~.png
