mbardin/Cyberinet/other documentation/photos/CNET.vibDelay~.png

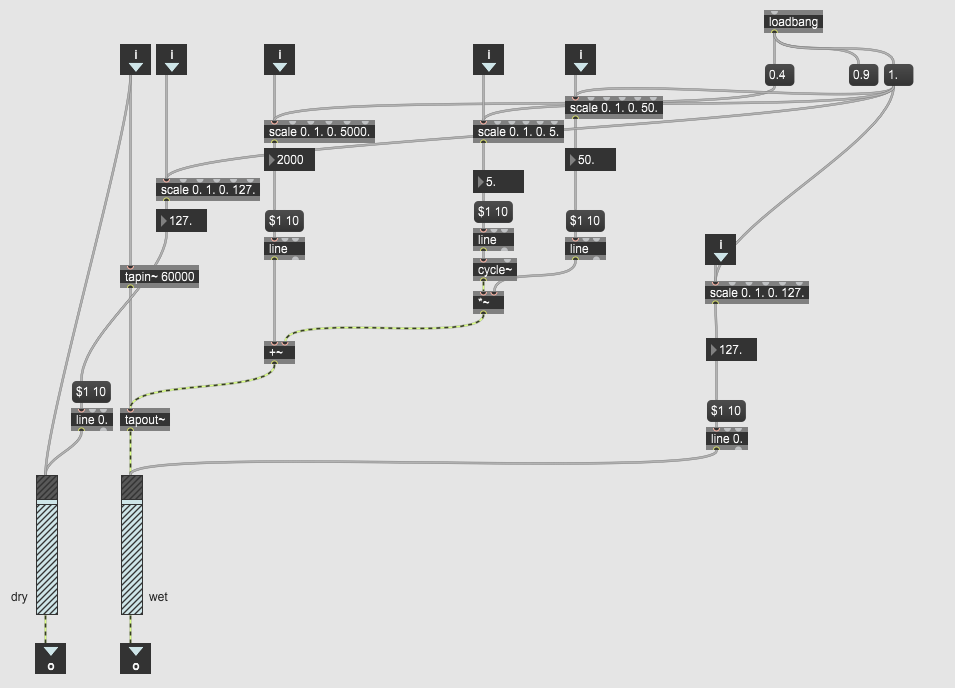
other documentation/photos/CNET.vibDelay~.png
