mbardin/Cyberinet/other documentation/photos/compInner.png

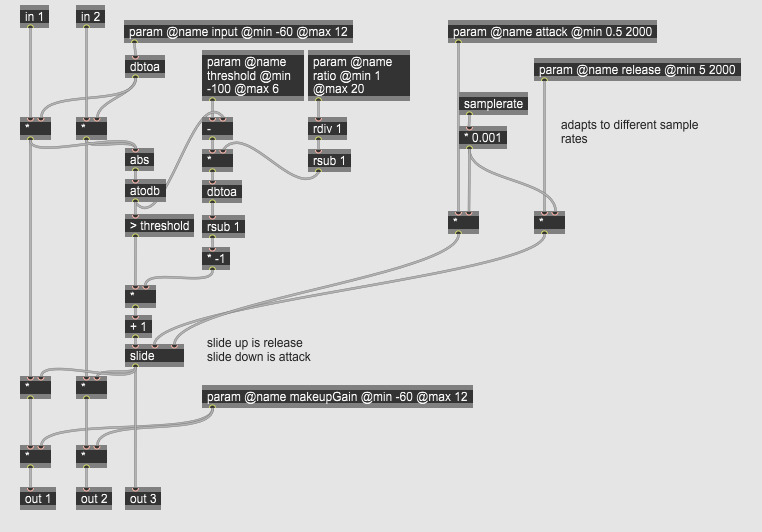
other documentation/photos/compInner.png
