mbardin/Cyberinet/other documentation/photos/compressorHelp.png

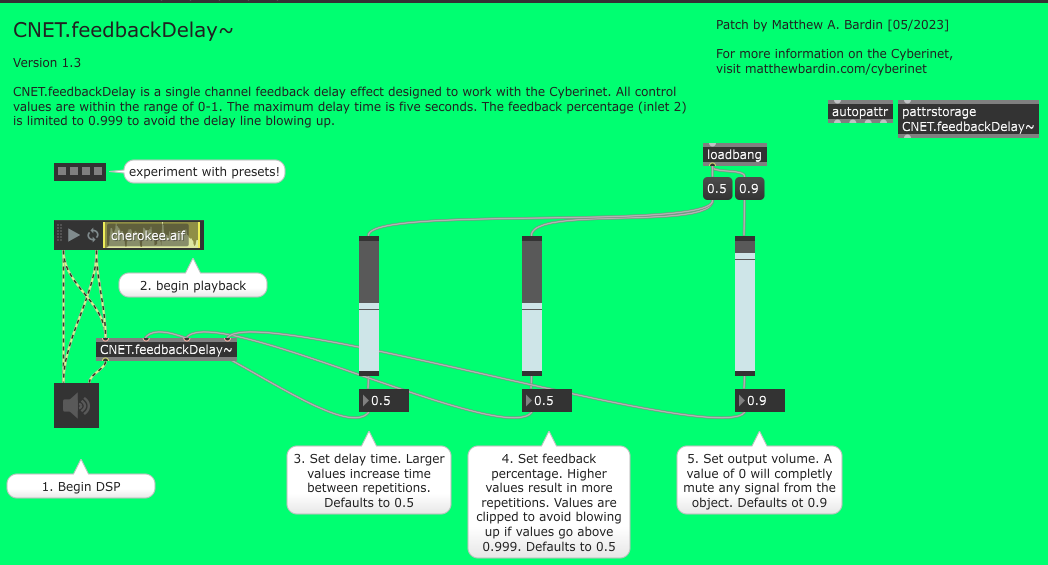
other documentation/photos/compressorHelp.png
