mbardin/Cyberinet/other documentation/photos/cyberinet v 1.3.png

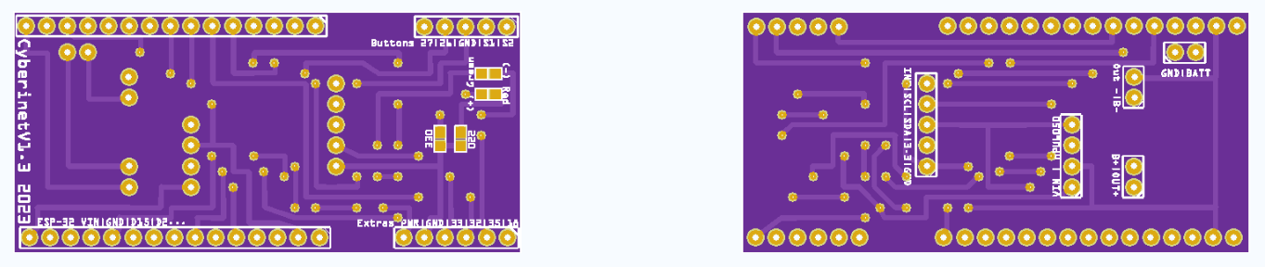
other documentation/photos/cyberinet v 1.3.png
