mbardin/Cyberinet/other documentation/photos/CyberneticsBook.jpg

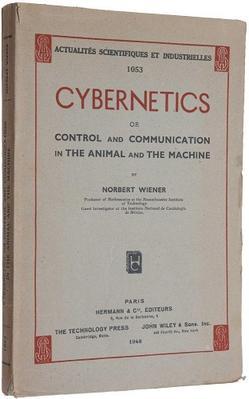
other documentation/photos/CyberneticsBook.jpg
