mbardin/Cyberinet/other documentation/photos/ethereal_pres.png

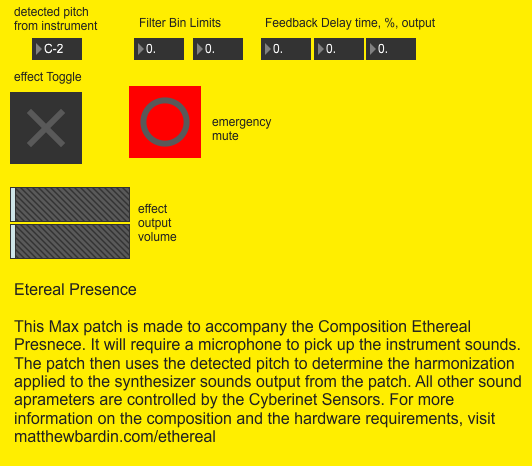
other documentation/photos/ethereal_pres.png
