mbardin/Cyberinet/other documentation/photos/ethereal_raw.png

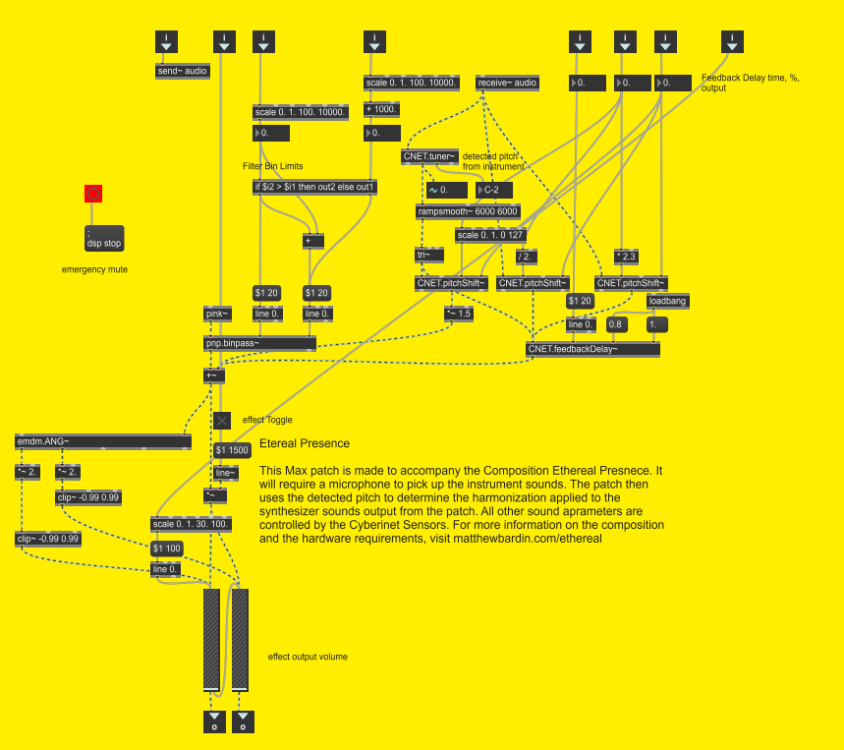
other documentation/photos/ethereal_raw.png
