mbardin/Cyberinet/other documentation/photos/frame.png

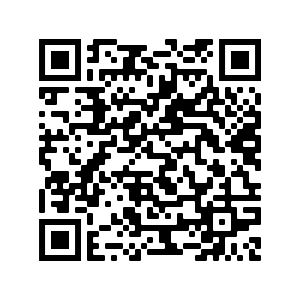
other documentation/photos/frame.png
