mbardin/Cyberinet/other documentation/photos/get6050.png

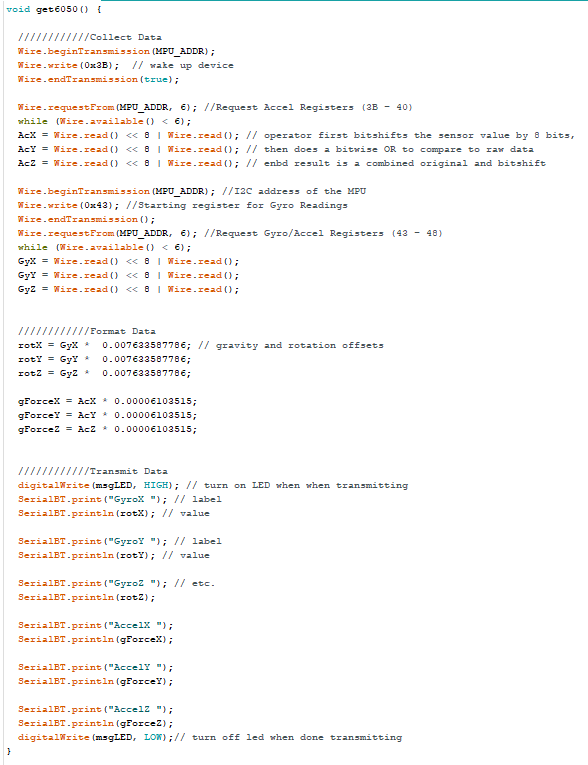
other documentation/photos/get6050.png
