mbardin/Cyberinet/other documentation/photos/getbuttonsgetair.png

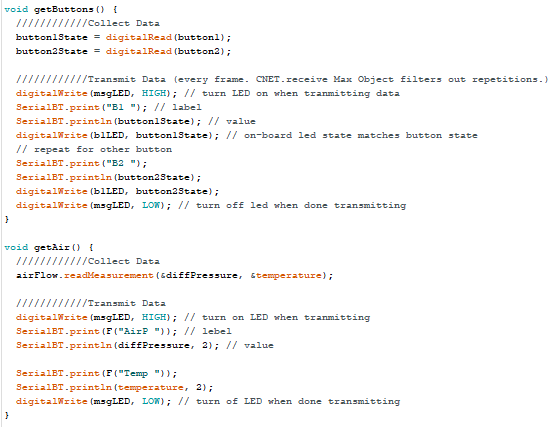
other documentation/photos/getbuttonsgetair.png
