mbardin/Cyberinet/other documentation/photos/github.png

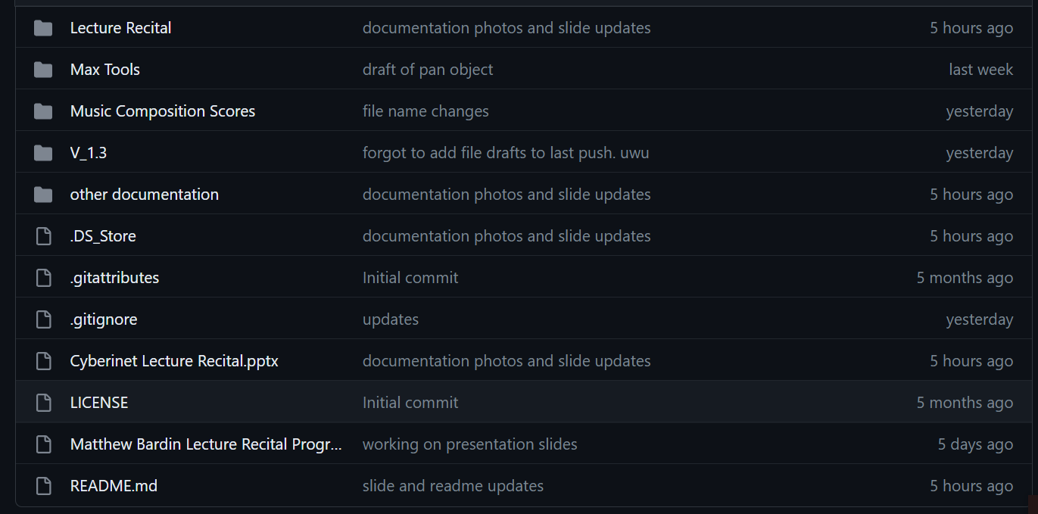
other documentation/photos/github.png
