mbardin/Cyberinet/other documentation/photos/IMG_0045.JPG

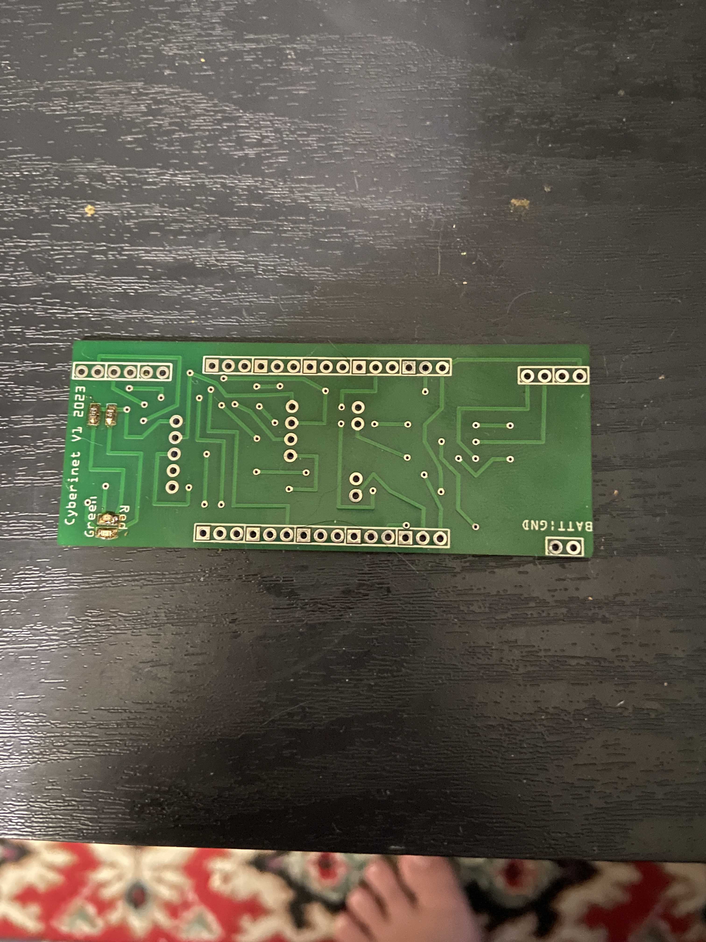
other documentation/photos/IMG_0045.JPG
