mbardin/Cyberinet/other documentation/photos/IMG_0046.JPG

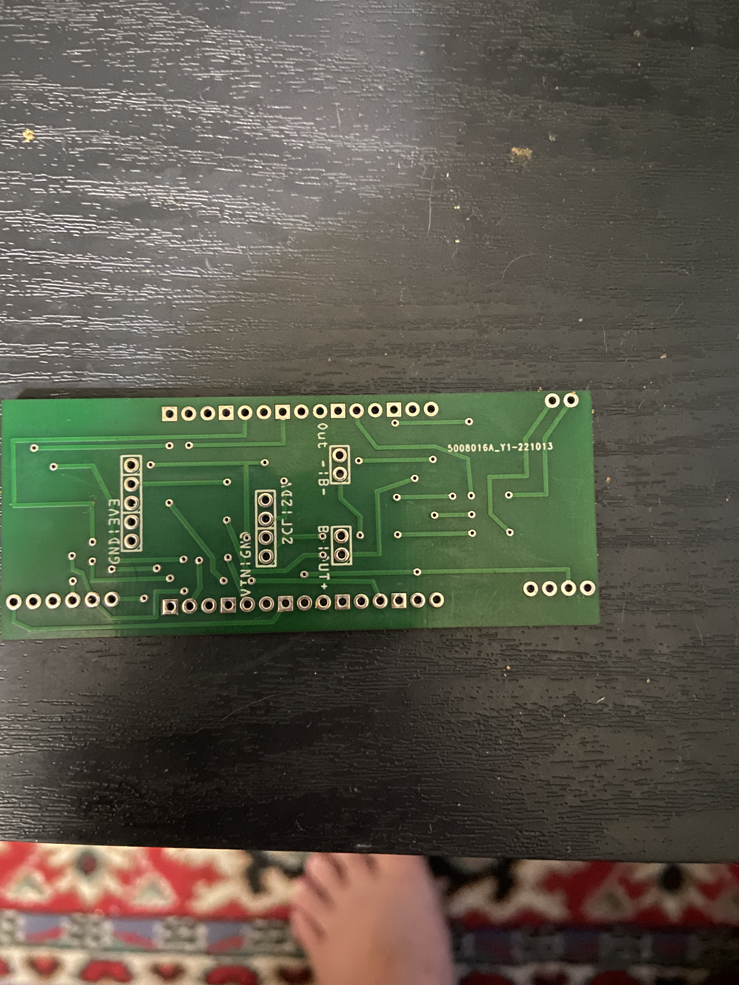
other documentation/photos/IMG_0046.JPG
