mbardin/Cyberinet/other documentation/photos/IMG_0047.JPG

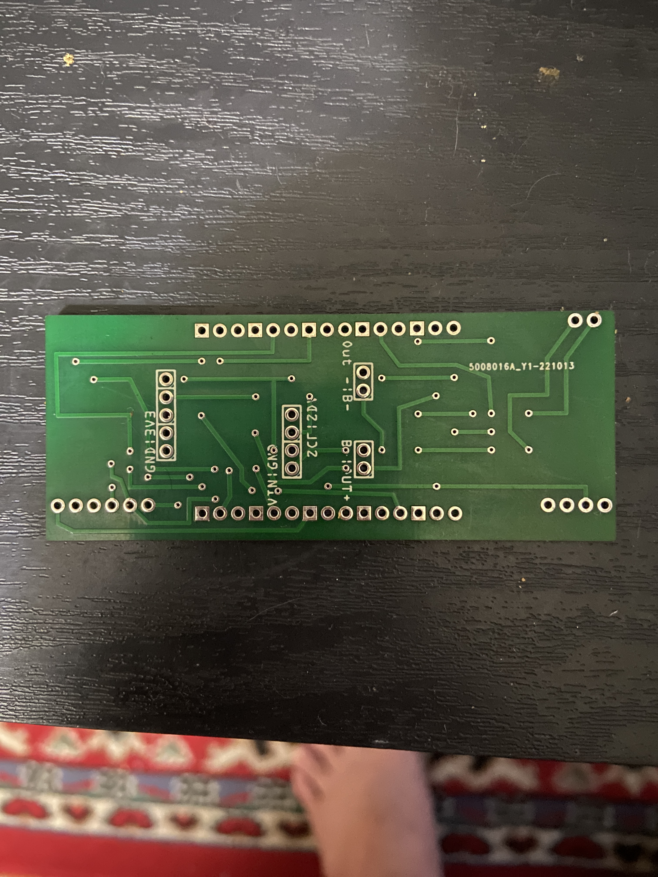
other documentation/photos/IMG_0047.JPG
