mbardin/Cyberinet/other documentation/photos/IMG_0048.JPG

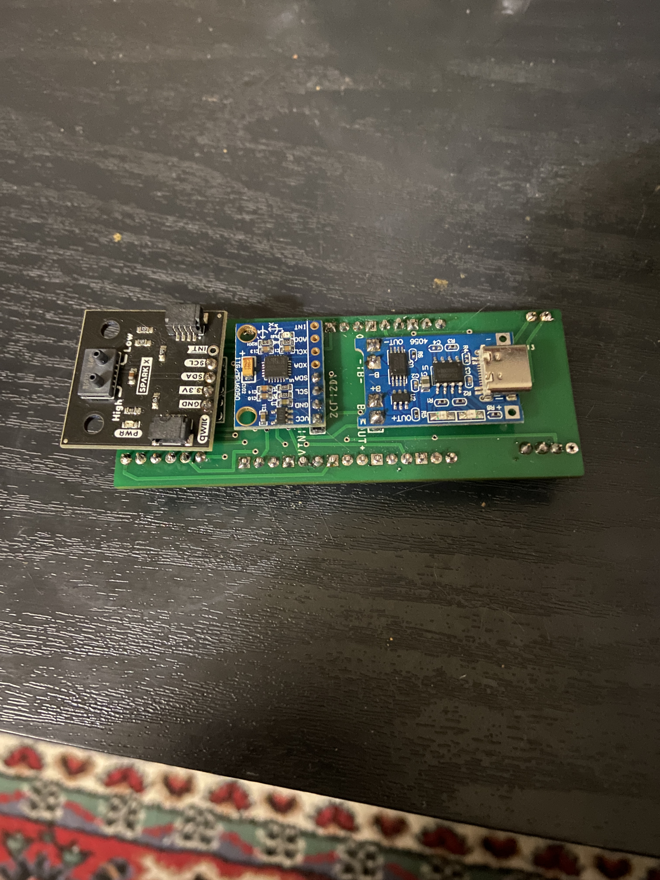
other documentation/photos/IMG_0048.JPG
