mbardin/Cyberinet/other documentation/photos/IMG_0049.JPG

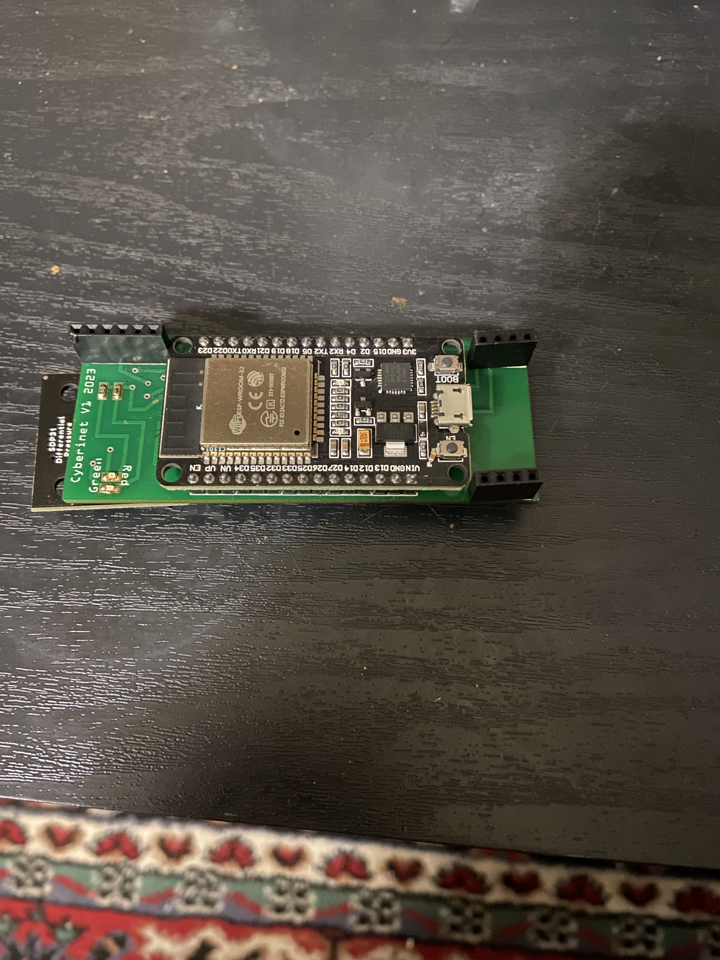
other documentation/photos/IMG_0049.JPG
