mbardin/Cyberinet/other documentation/photos/IMG_0824.JPG

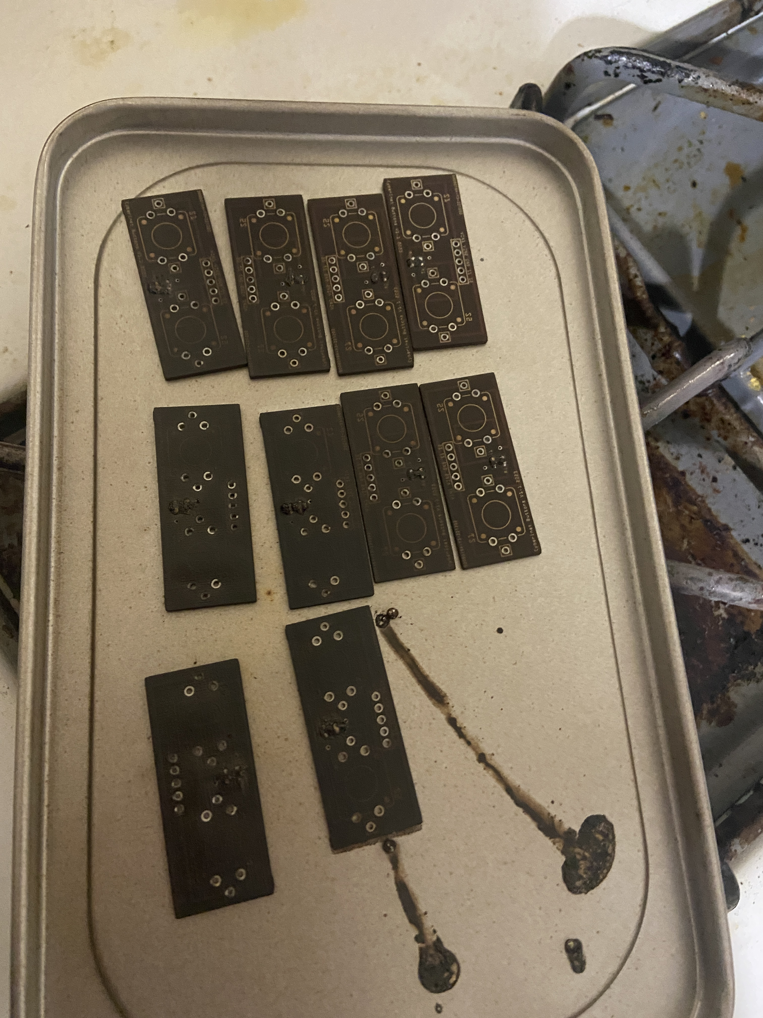
other documentation/photos/IMG_0824.JPG
