mbardin/Cyberinet/other documentation/photos/IMG_1205.JPG

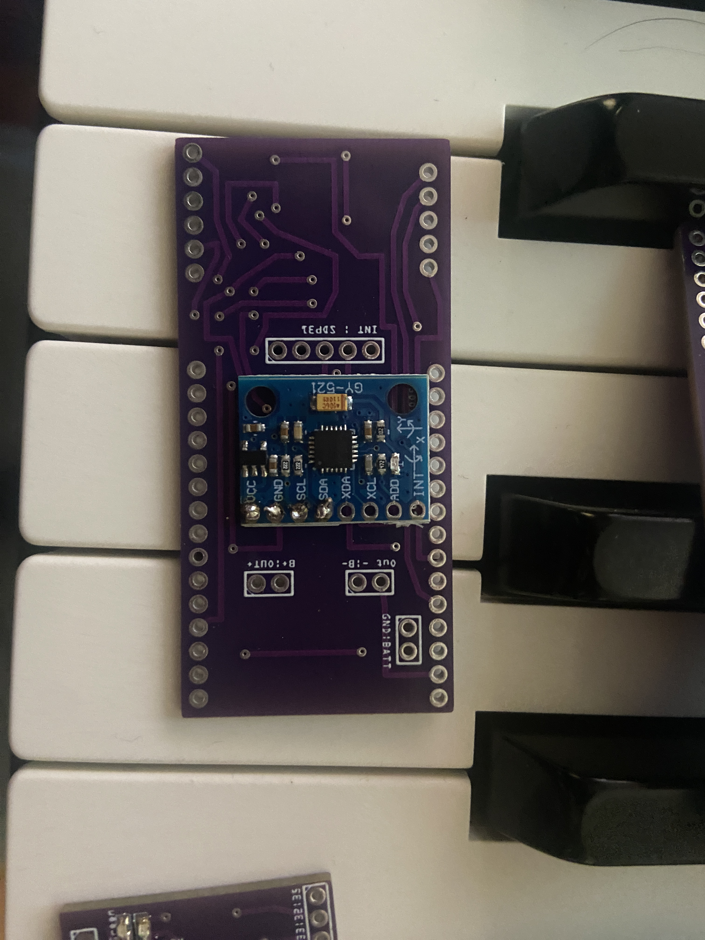
other documentation/photos/IMG_1205.JPG
