mbardin/Cyberinet/other documentation/photos/IMG_1206.JPG

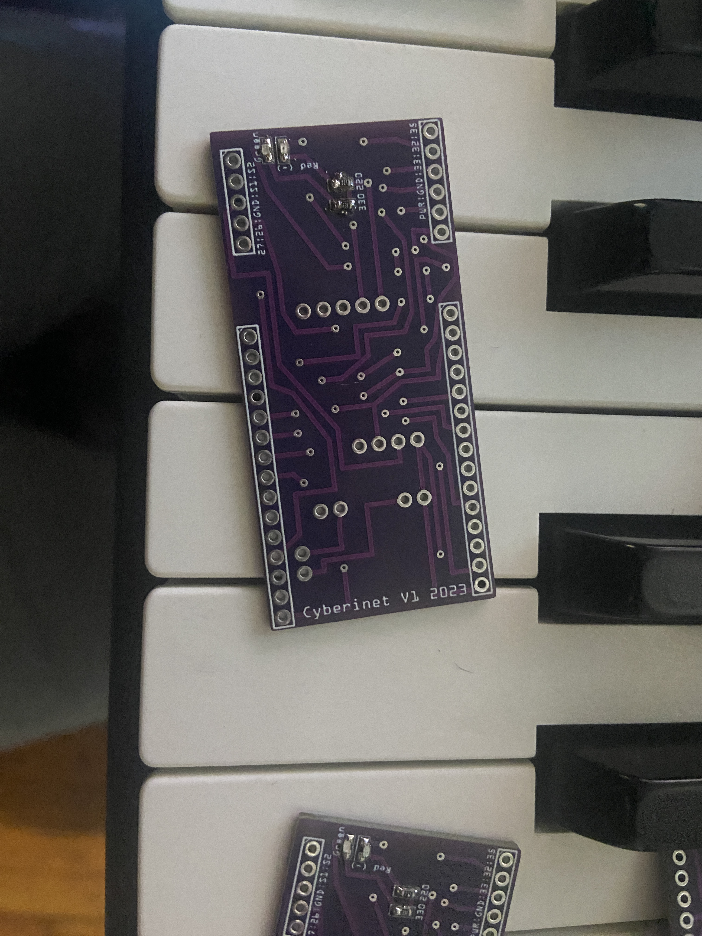
other documentation/photos/IMG_1206.JPG
