mbardin/Cyberinet/other documentation/photos/IMG_1208.JPG

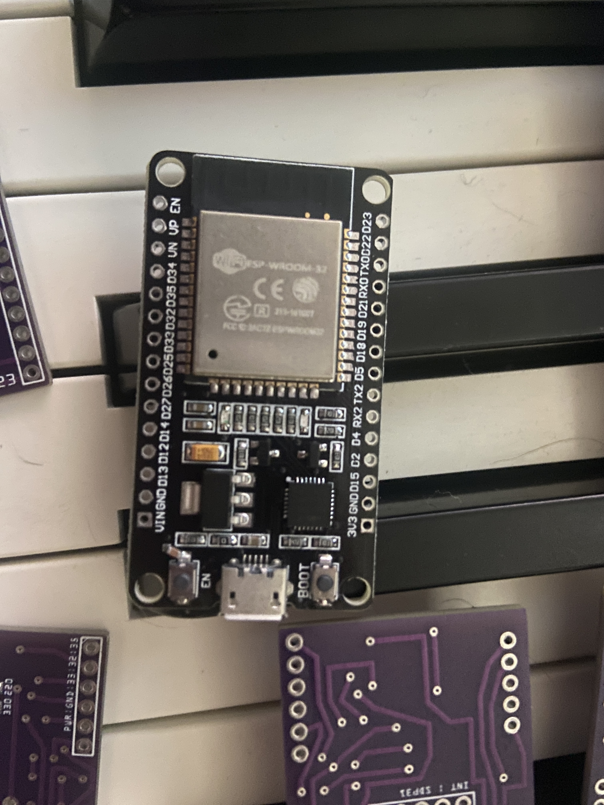
other documentation/photos/IMG_1208.JPG
