mbardin/Cyberinet/other documentation/photos/IMG_1250.PNG

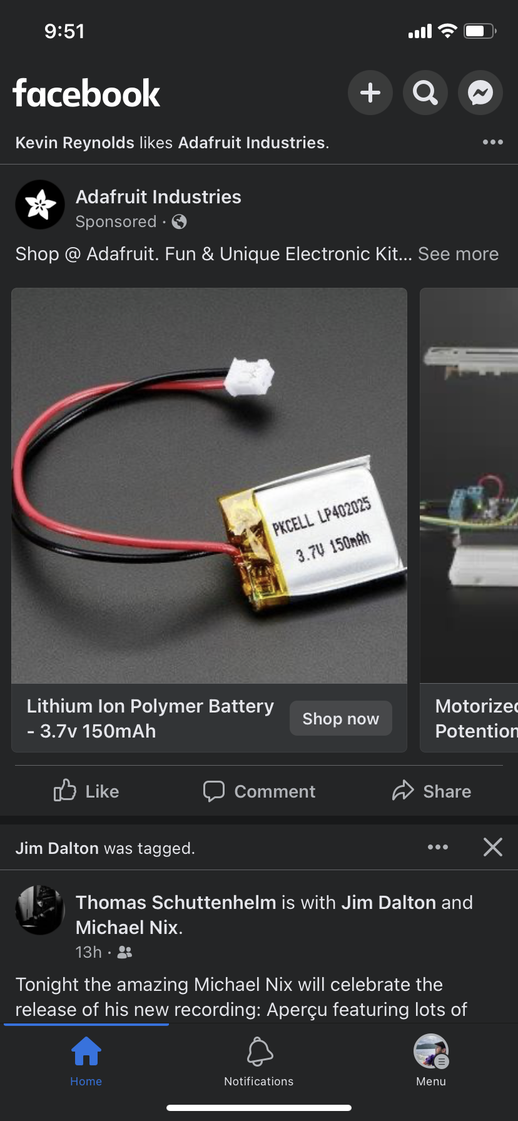
other documentation/photos/IMG_1250.PNG
