mbardin/Cyberinet/other documentation/photos/IMG_1270.JPG

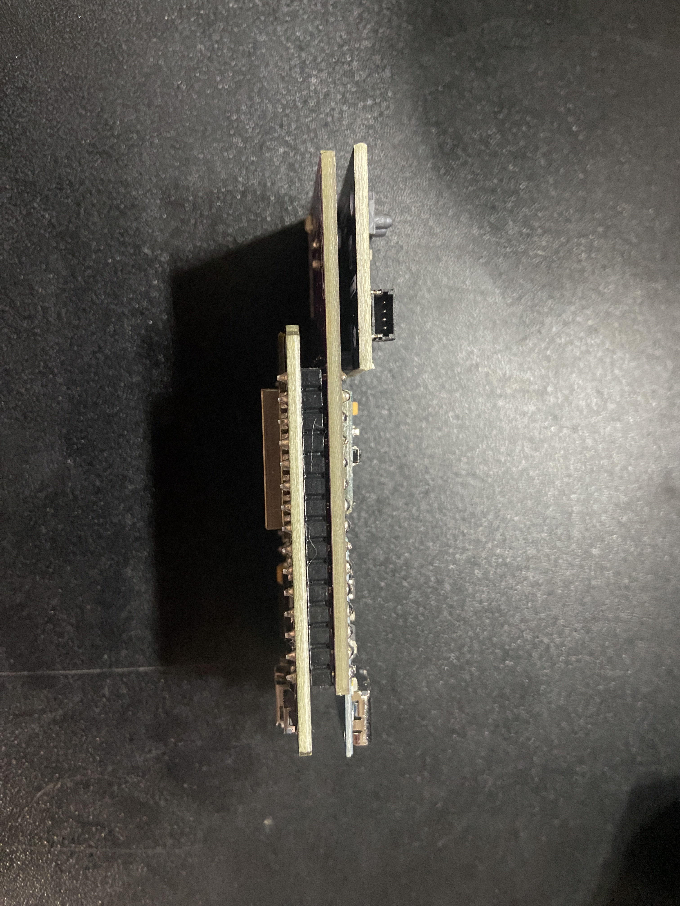
other documentation/photos/IMG_1270.JPG
