mbardin/Cyberinet/other documentation/photos/IMG_1960.JPG

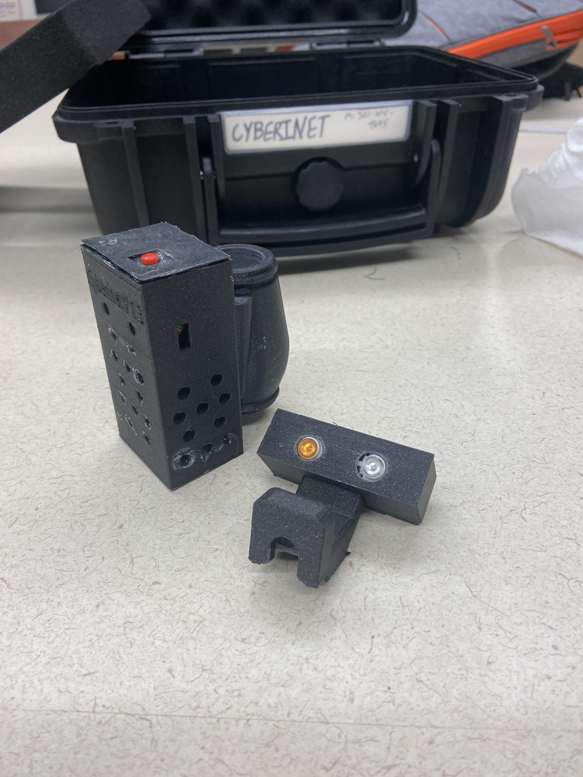
other documentation/photos/IMG_1960.JPG
