mbardin/Cyberinet/other documentation/photos/IMG_1961.JPG

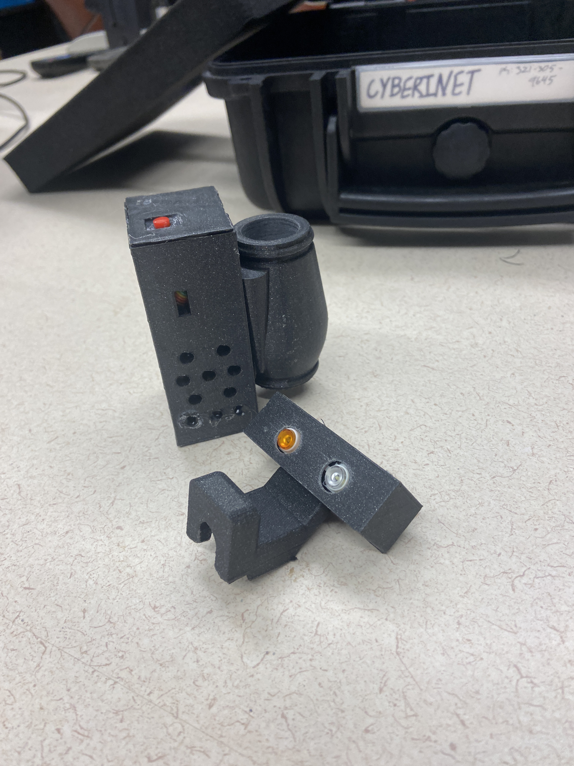
other documentation/photos/IMG_1961.JPG
