mbardin/Cyberinet/other documentation/photos/IMG_1962.JPG

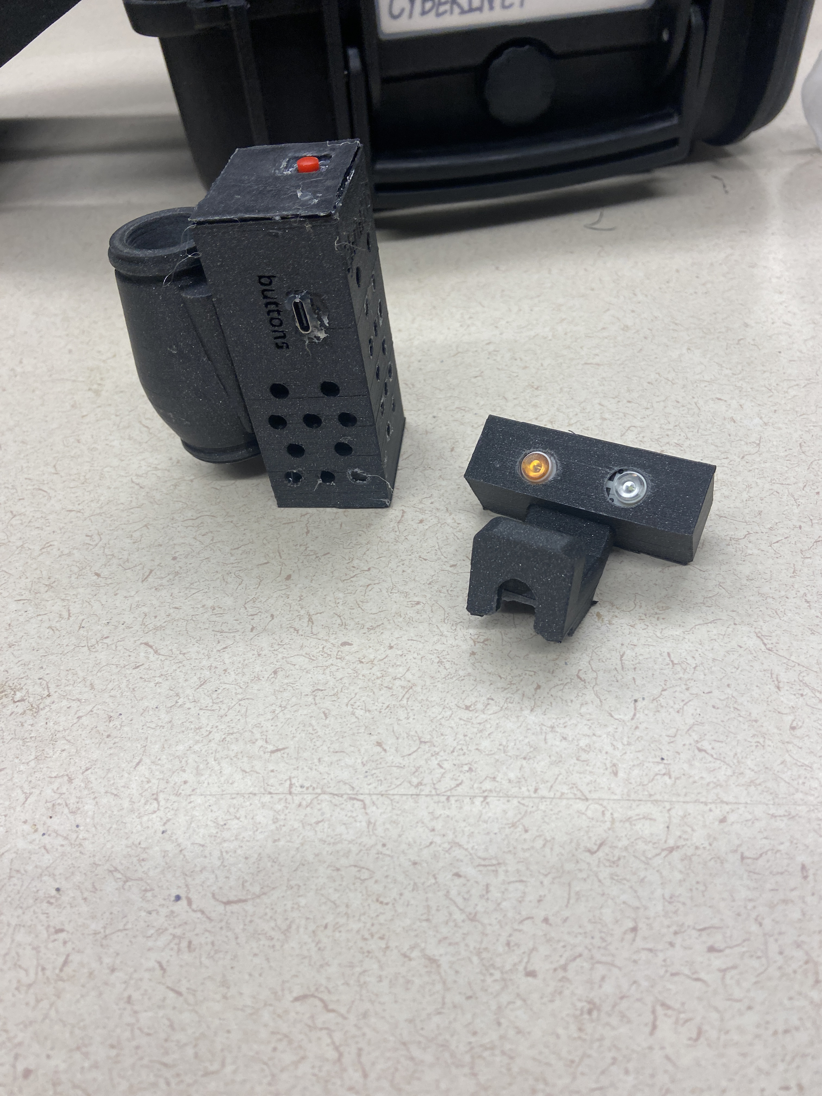
other documentation/photos/IMG_1962.JPG
