mbardin/Cyberinet/other documentation/photos/IMG_1963.JPG

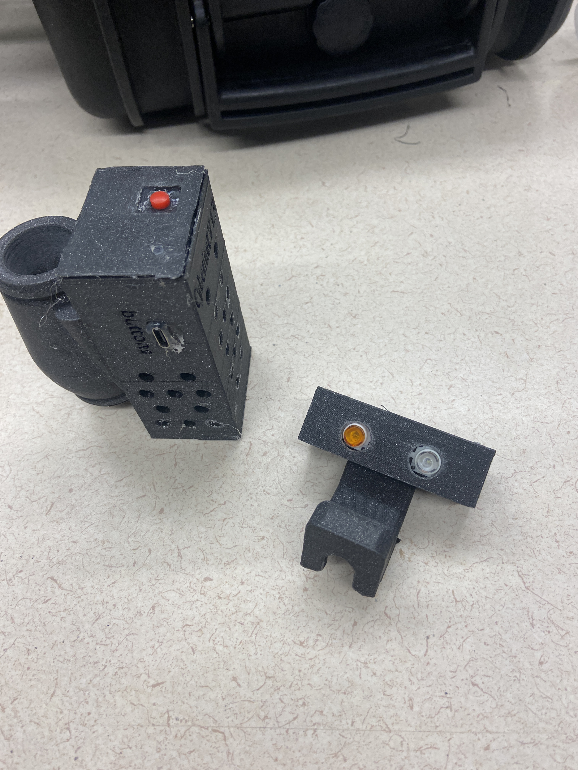
other documentation/photos/IMG_1963.JPG
