mbardin/Cyberinet/other documentation/photos/IMG_1964.JPG

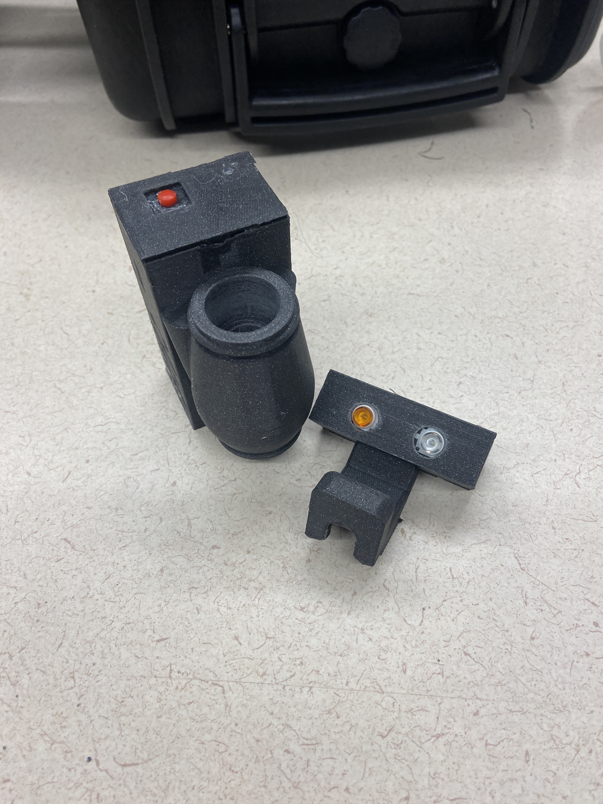
other documentation/photos/IMG_1964.JPG
