mbardin/Cyberinet/other documentation/photos/IMG_9734_1.jpg

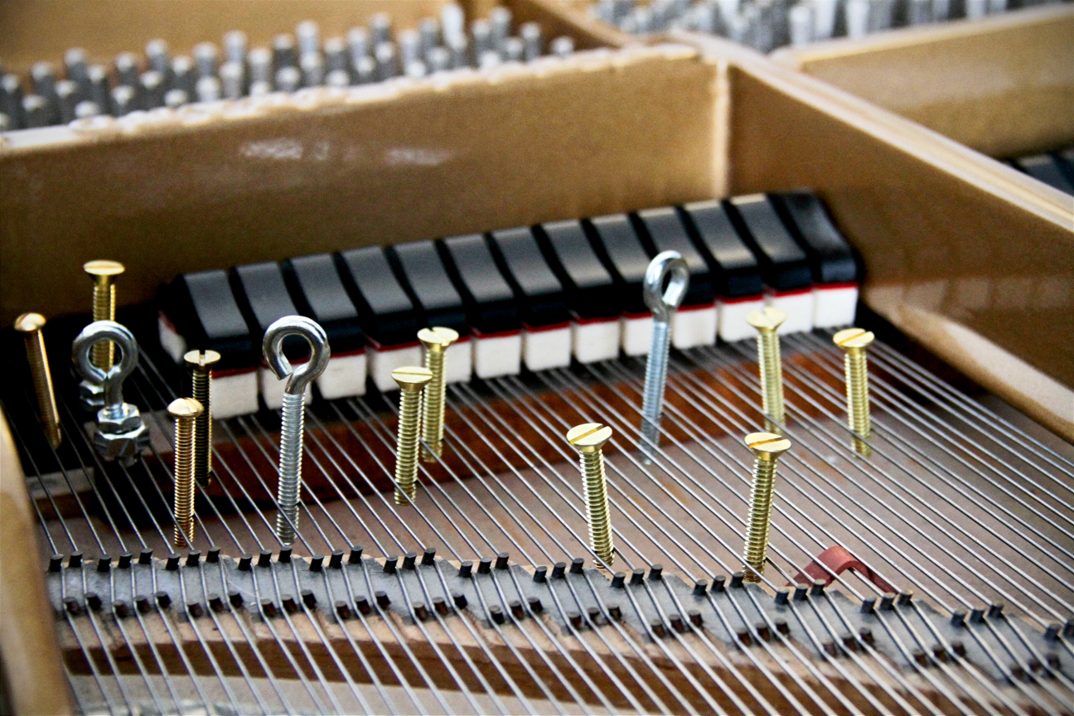
other documentation/photos/IMG_9734_1.jpg
