mbardin/Cyberinet/other documentation/photos/imporvPres.png

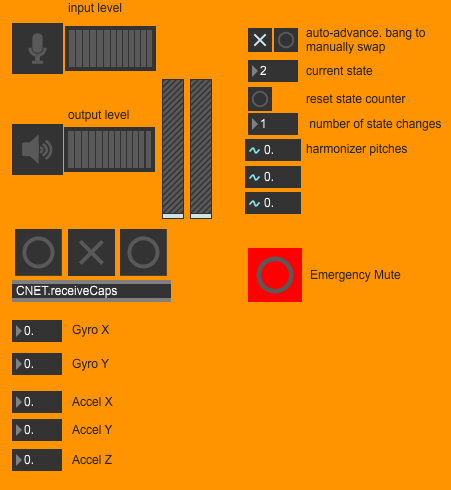
other documentation/photos/imporvPres.png
