mbardin/Cyberinet/other documentation/photos/improvRaw.png

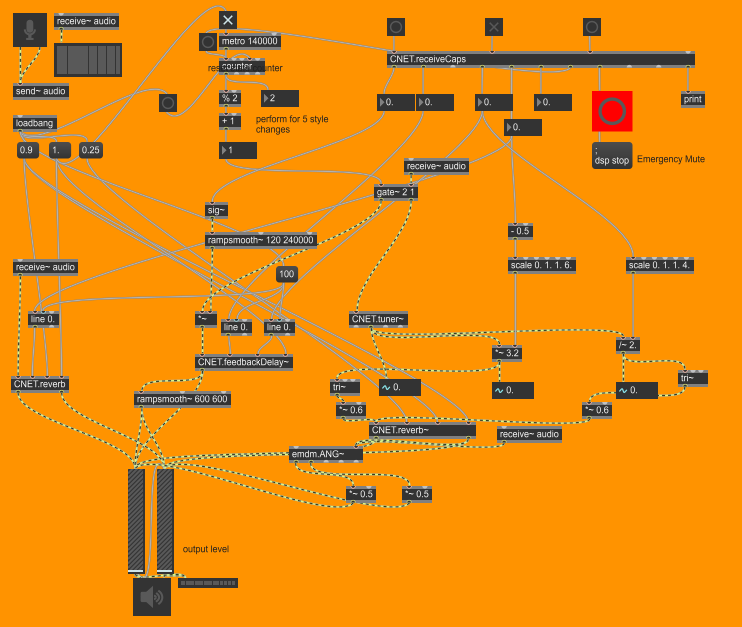
other documentation/photos/improvRaw.png
