mbardin/Cyberinet/other documentation/photos/kayn.jpg

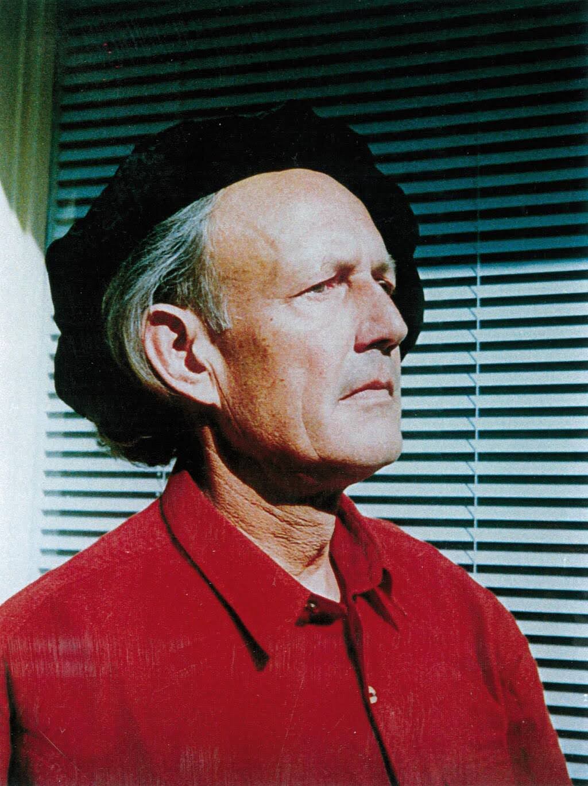
other documentation/photos/kayn.jpg
