mbardin/Cyberinet/other documentation/photos/Korg_microSAMPLER.jpg

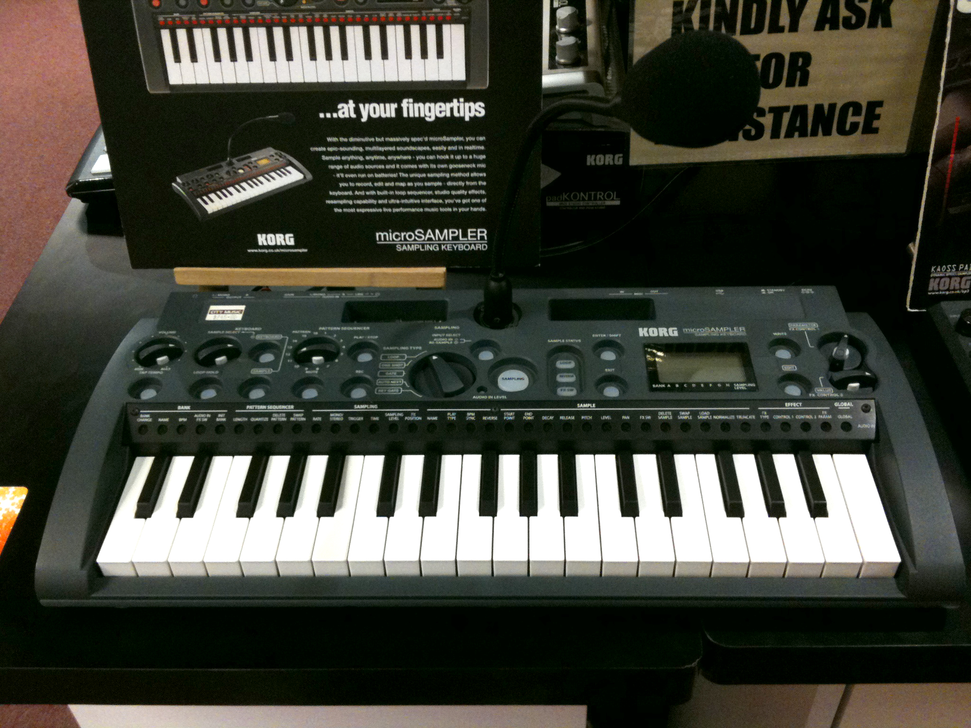
other documentation/photos/Korg_microSAMPLER.jpg
