mbardin/Cyberinet/other documentation/photos/M-A-O-clarinets.jpg

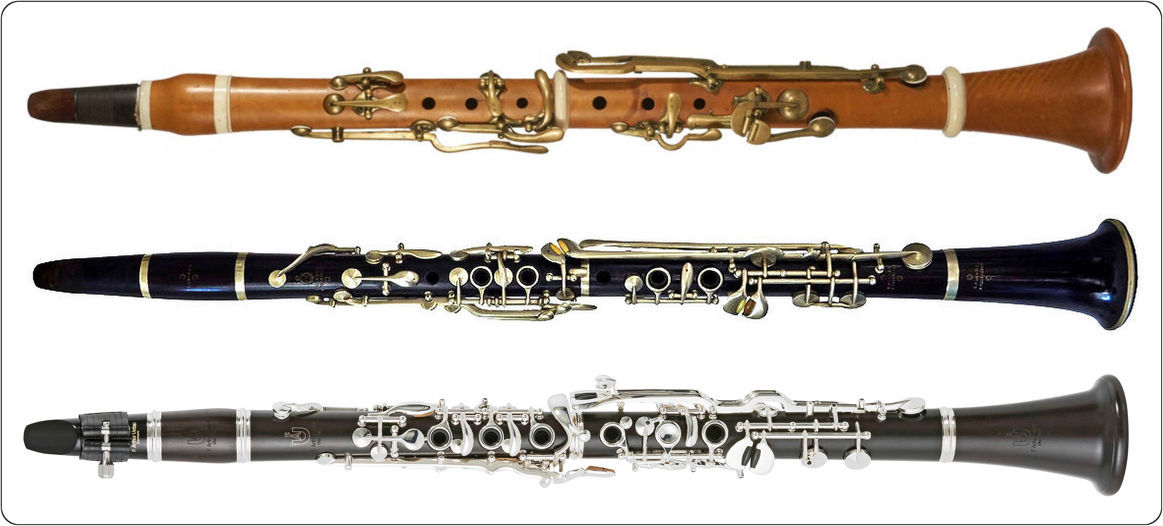
other documentation/photos/M-A-O-clarinets.jpg
