mbardin/Cyberinet/other documentation/photos/MIGSI.jpg

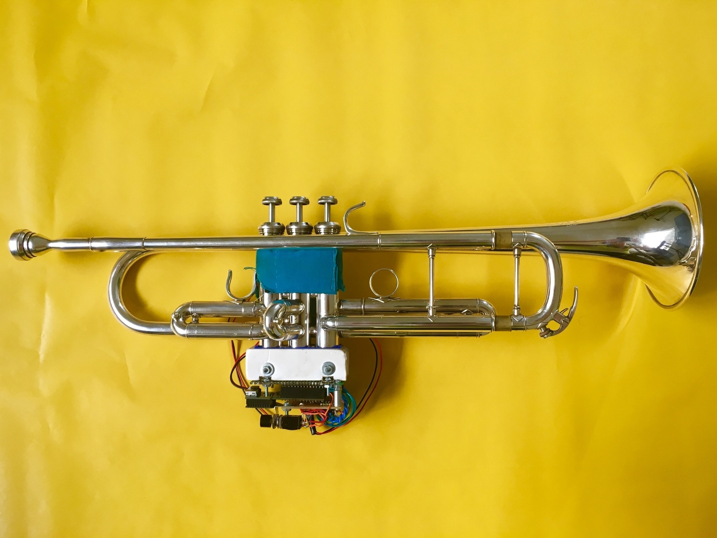
other documentation/photos/MIGSI.jpg
