mbardin/Cyberinet/other documentation/photos/migsi_mockup.jpg

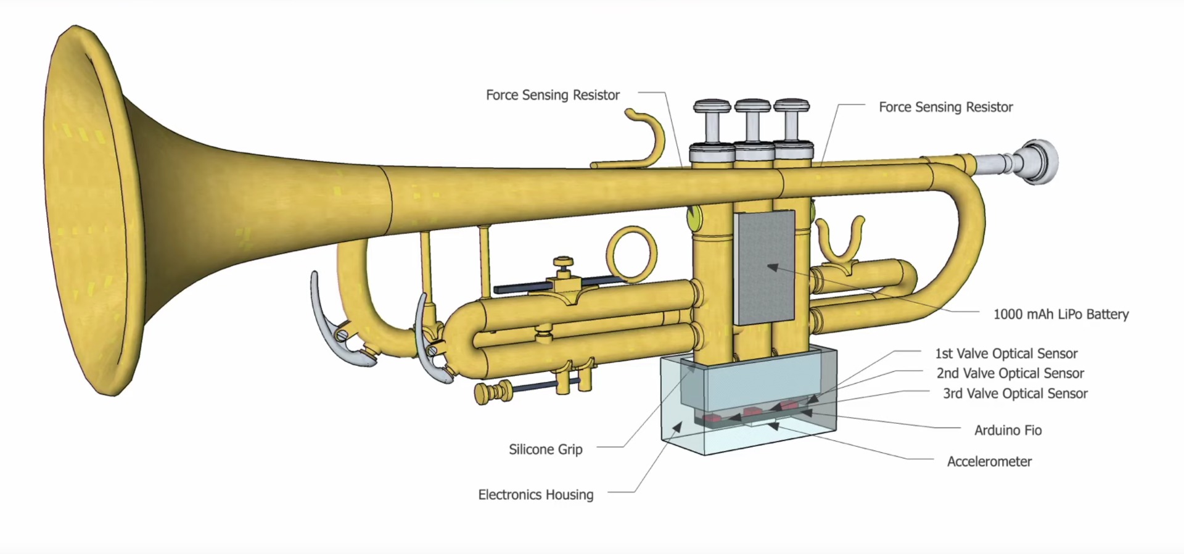
other documentation/photos/migsi_mockup.jpg
