mbardin/Cyberinet/other documentation/photos/oliveros.jpg

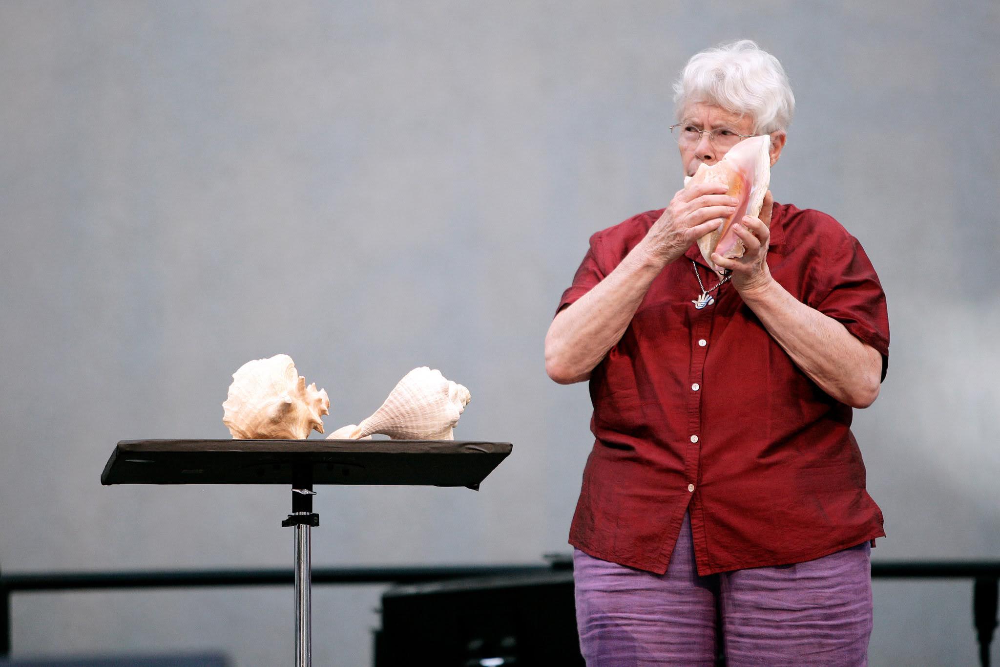
other documentation/photos/oliveros.jpg
