mbardin/Cyberinet/other documentation/photos/Omnipod-5_CGM_Pod_BT_1040x277.jpg

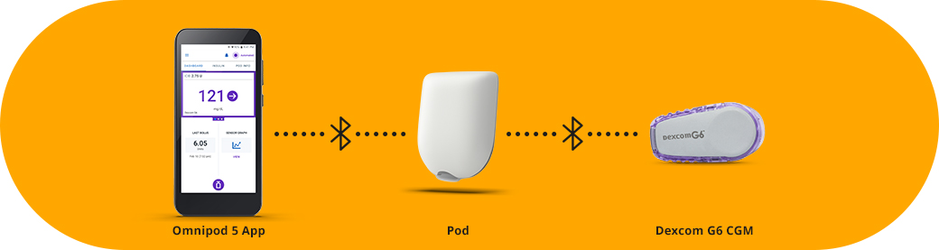
other documentation/photos/Omnipod-5_CGM_Pod_BT_1040x277.jpg
