mbardin/Cyberinet/other documentation/photos/palacio_quintin_cleo.jpg

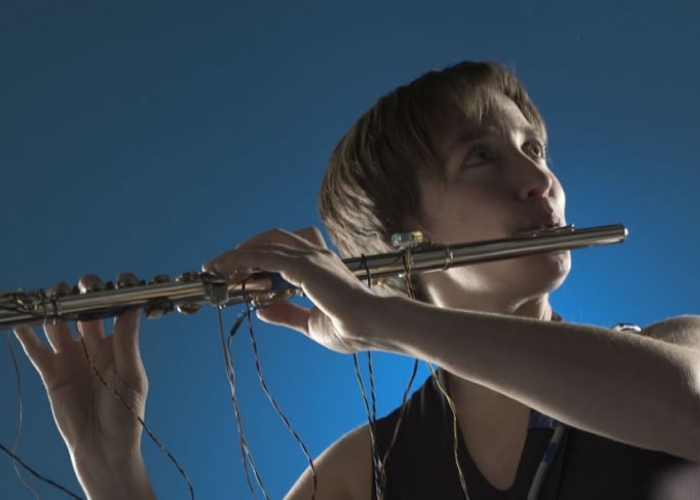
other documentation/photos/palacio_quintin_cleo.jpg
