mbardin/Cyberinet/other documentation/photos/PlayerPianoRoll.jpg

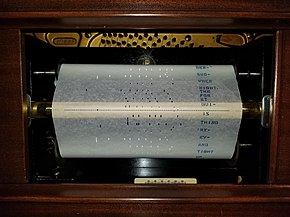
other documentation/photos/PlayerPianoRoll.jpg
