mbardin/Cyberinet/other documentation/photos/raindropspres.png

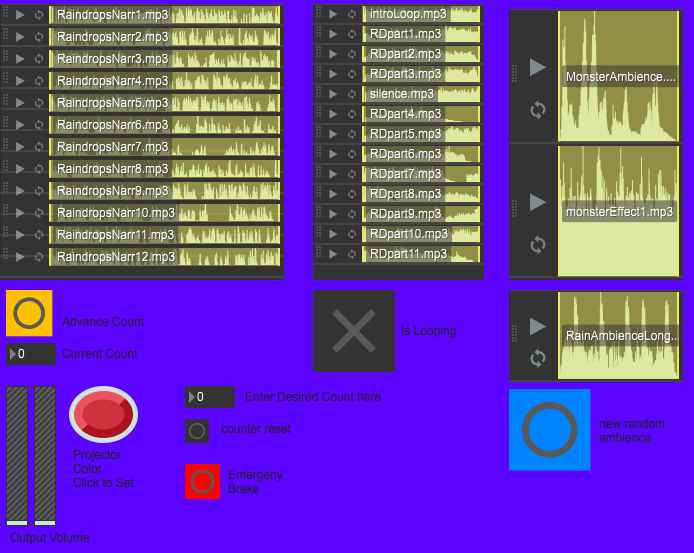
other documentation/photos/raindropspres.png
