mbardin/Cyberinet/other documentation/photos/raindropsRaw.png

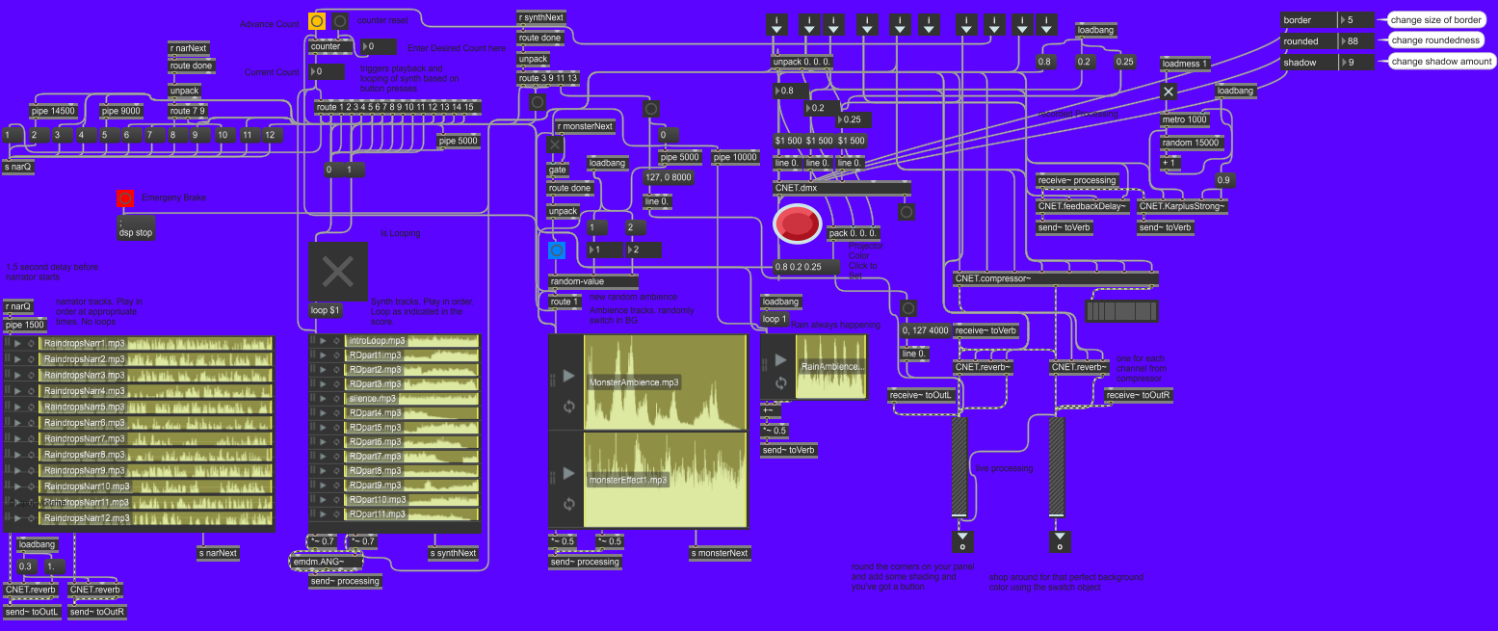
other documentation/photos/raindropsRaw.png
