mbardin/Cyberinet/other documentation/photos/sabre-right-hand.jpg

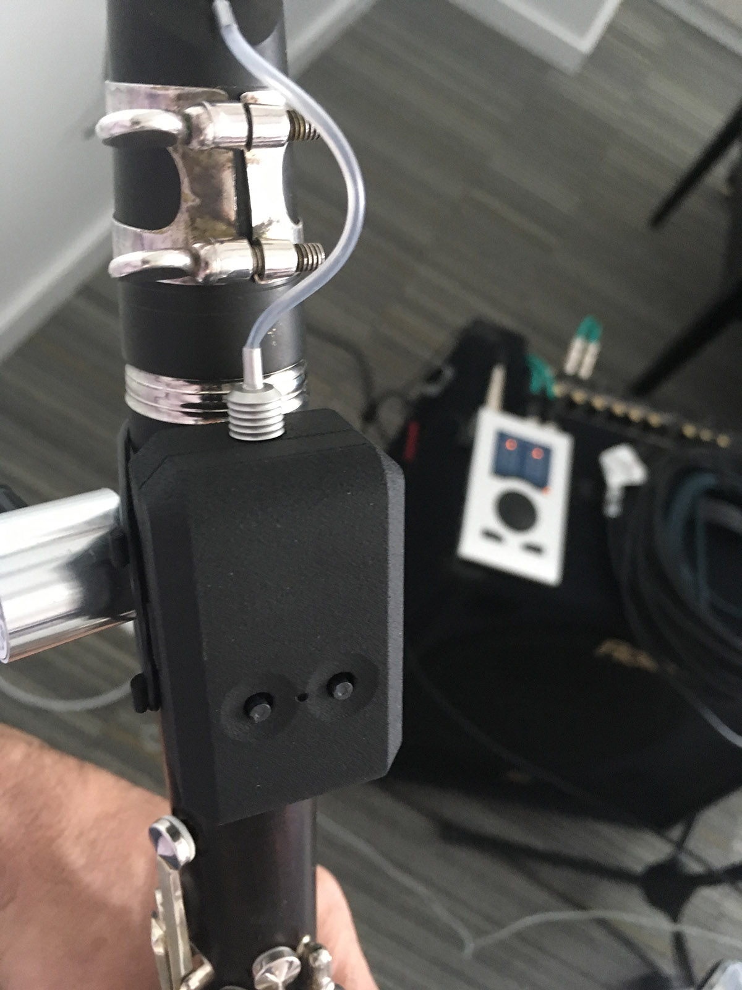
other documentation/photos/sabre-right-hand.jpg
