mbardin/Cyberinet/other documentation/photos/Screenshot 2023-03-19 142755.png

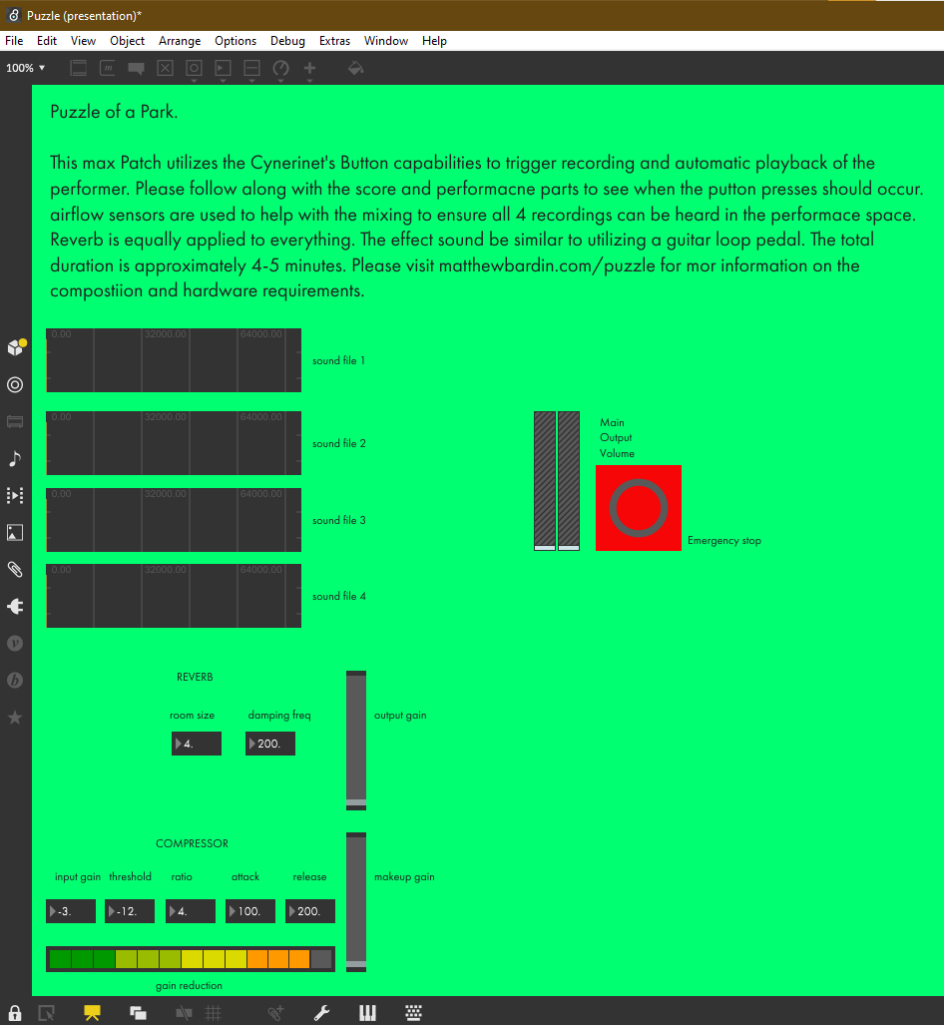
other documentation/photos/Screenshot 2023-03-19 142755.png
