mbardin/Cyberinet/other documentation/photos/Screenshot 2023-04-06 at 8.04.19 AM.png

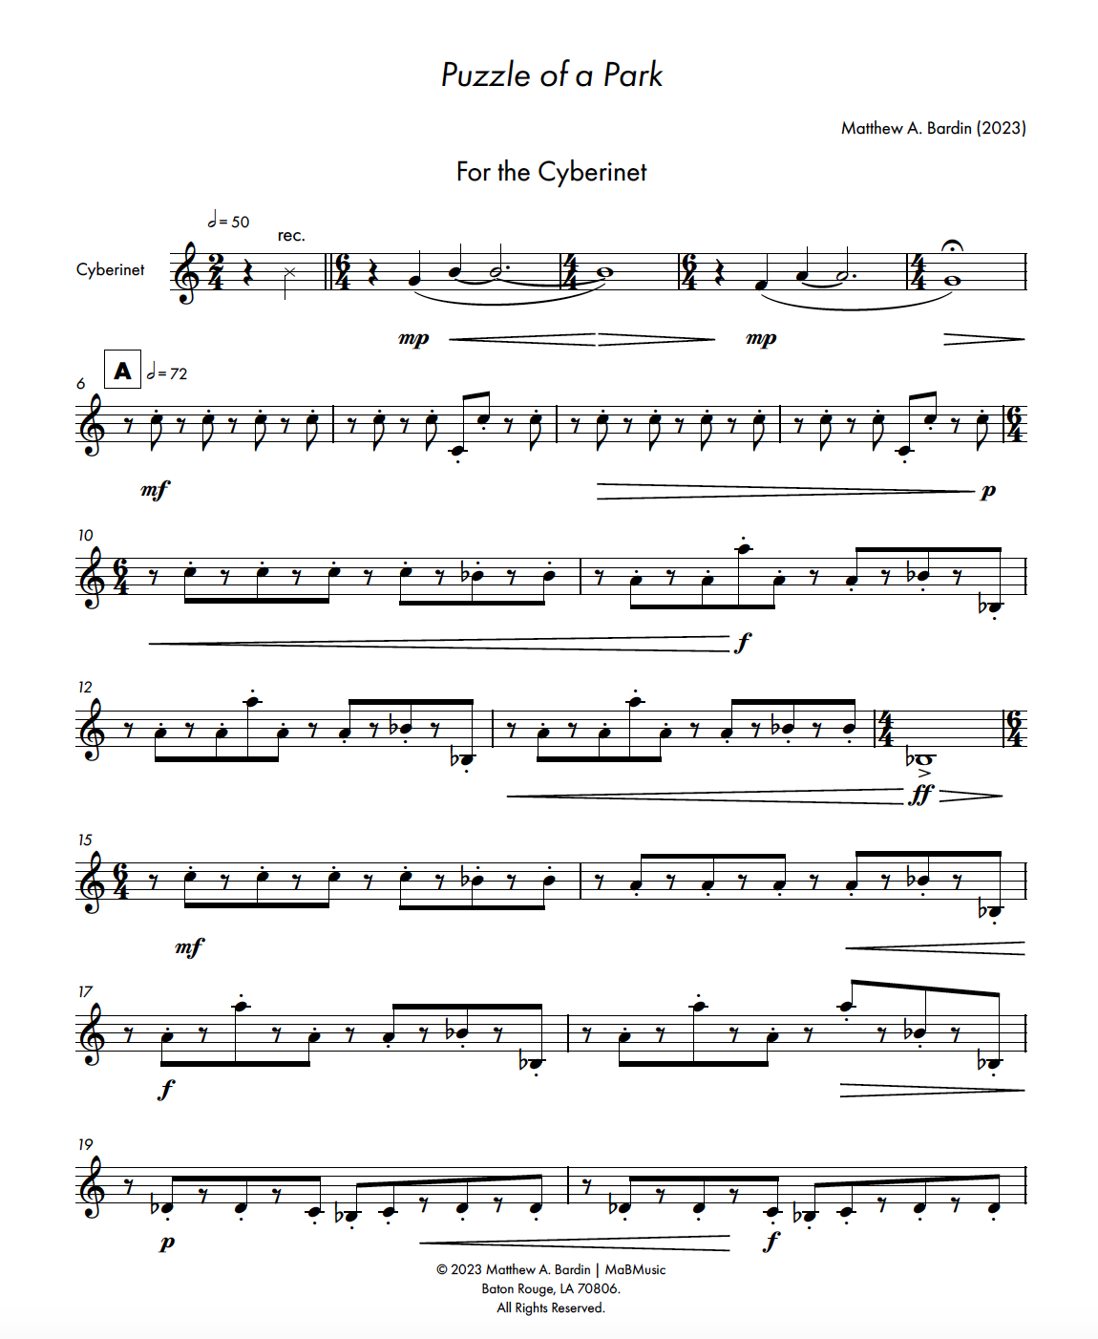
other documentation/photos/Screenshot 2023-04-06 at 8.04.19 AM.png
