mbardin/Cyberinet/other documentation/photos/Screenshot 2023-04-06 at 9.55.02 AM.png

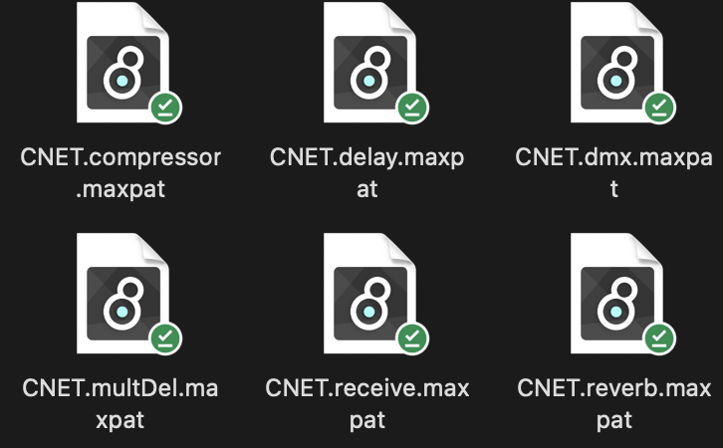
other documentation/photos/Screenshot 2023-04-06 at 9.55.02 AM.png
