mbardin/Cyberinet/other documentation/photos/Screenshot 2023-04-10 at 3.09.34 PM.png

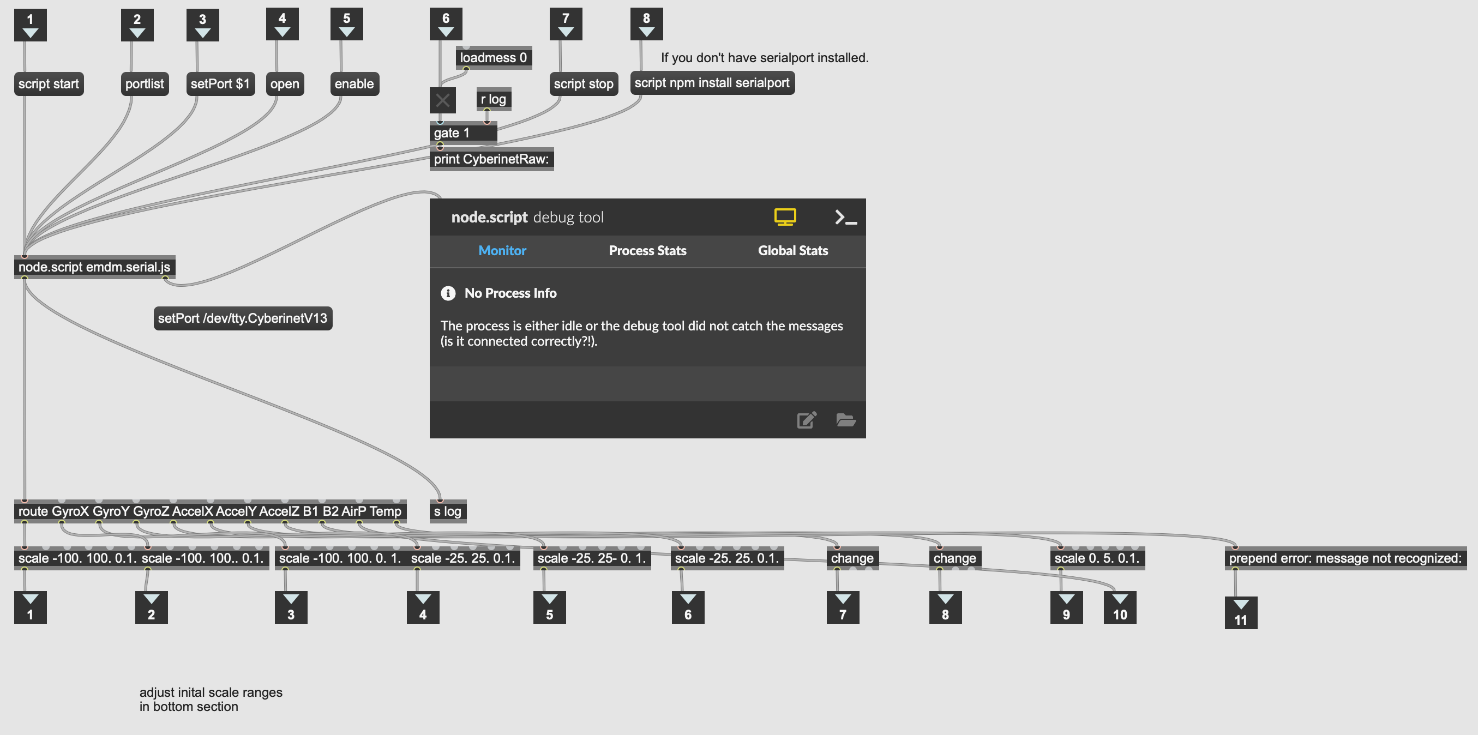
other documentation/photos/Screenshot 2023-04-10 at 3.09.34 PM.png
