mbardin/Cyberinet/other documentation/photos/Screenshot 2023-04-12 at 7.23.41 PM.png

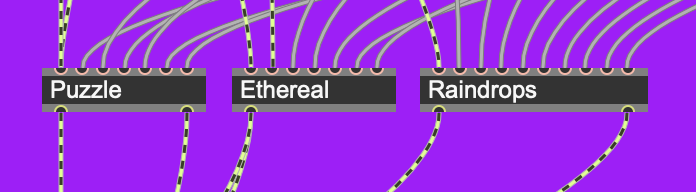
other documentation/photos/Screenshot 2023-04-12 at 7.23.41 PM.png
