mbardin/Cyberinet/other documentation/photos/Screenshot 2023-04-15 at 8.12.05 PM.png

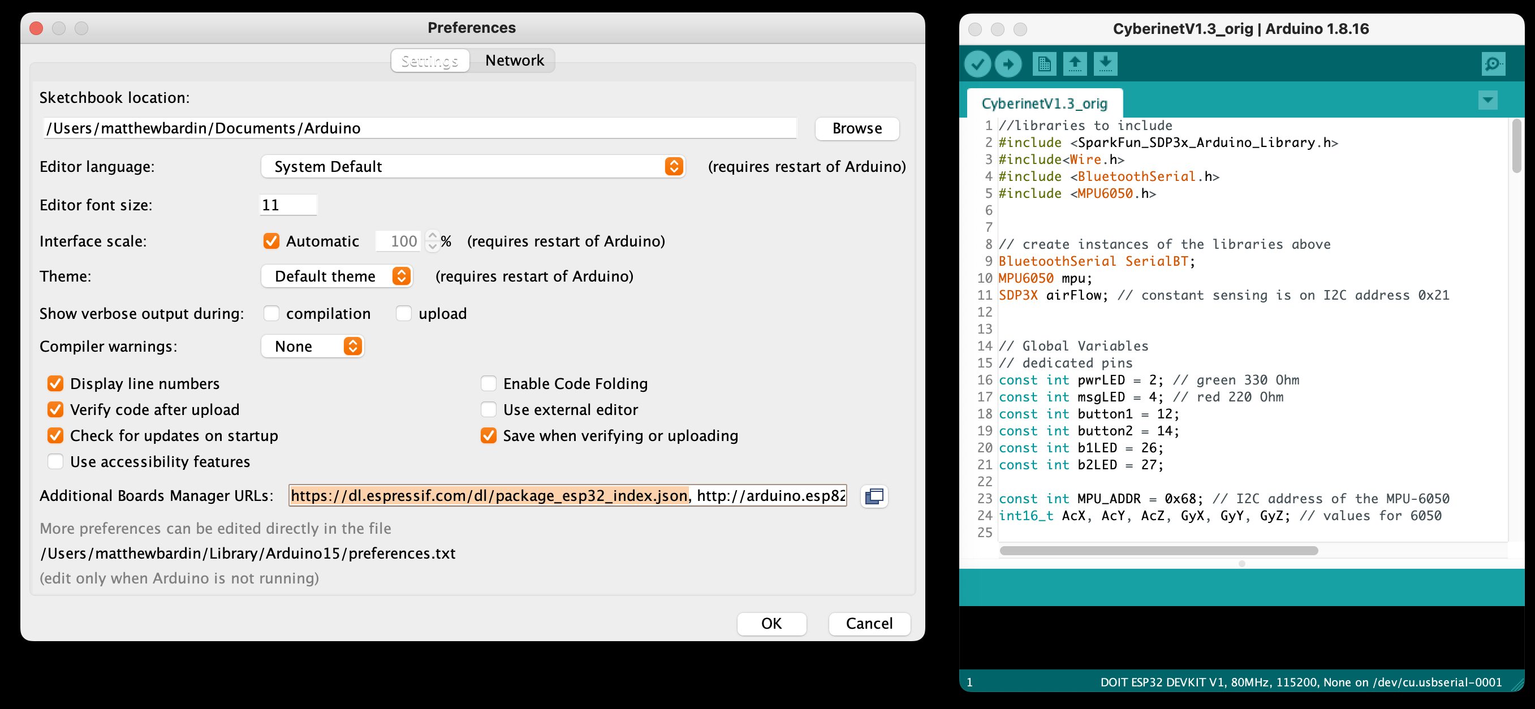
other documentation/photos/Screenshot 2023-04-15 at 8.12.05 PM.png
