mbardin/Cyberinet/other documentation/photos/Screenshot 2023-04-25 at 6.40.11 PM.png

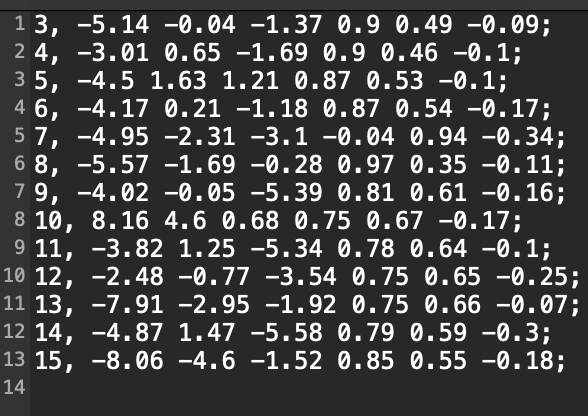
other documentation/photos/Screenshot 2023-04-25 at 6.40.11 PM.png
