mbardin/Cyberinet/other documentation/photos/Screenshot 2023-05-01 at 4.10.51 PM.png

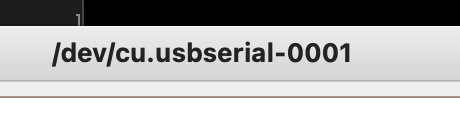
other documentation/photos/Screenshot 2023-05-01 at 4.10.51 PM.png
