mbardin/Cyberinet/other documentation/photos/Screenshot 2023-05-17 at 7.47.59 PM.png

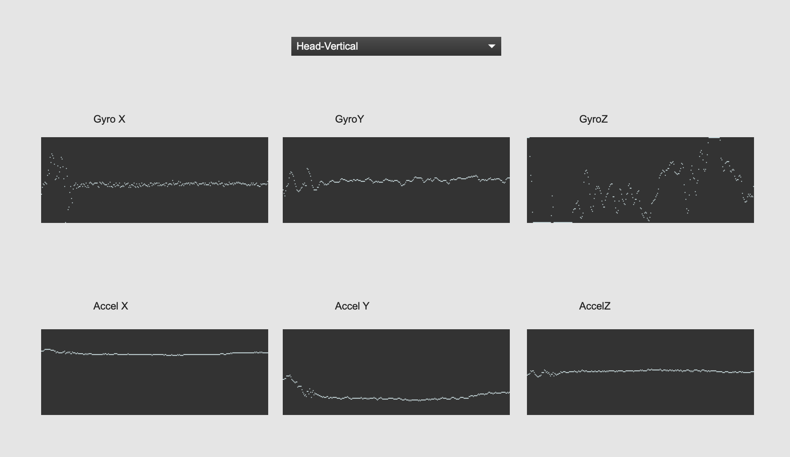
other documentation/photos/Screenshot 2023-05-17 at 7.47.59 PM.png
