mbardin/Cyberinet/other documentation/photos/Screenshot 2023-05-17 at 8.25.25 PM.png

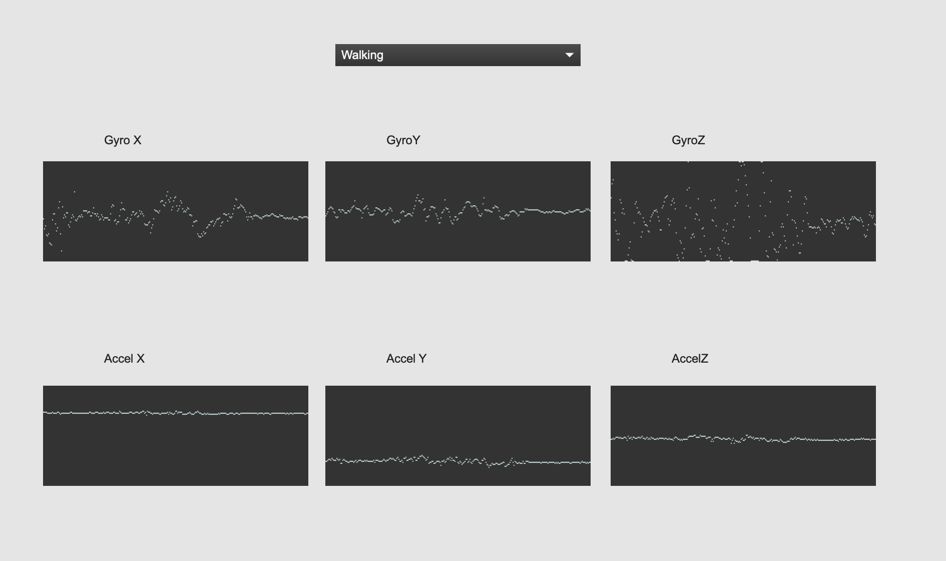
other documentation/photos/Screenshot 2023-05-17 at 8.25.25 PM.png
