mbardin/Cyberinet/other documentation/photos/Screenshot 2023-05-17 at 8.41.33 PM.png

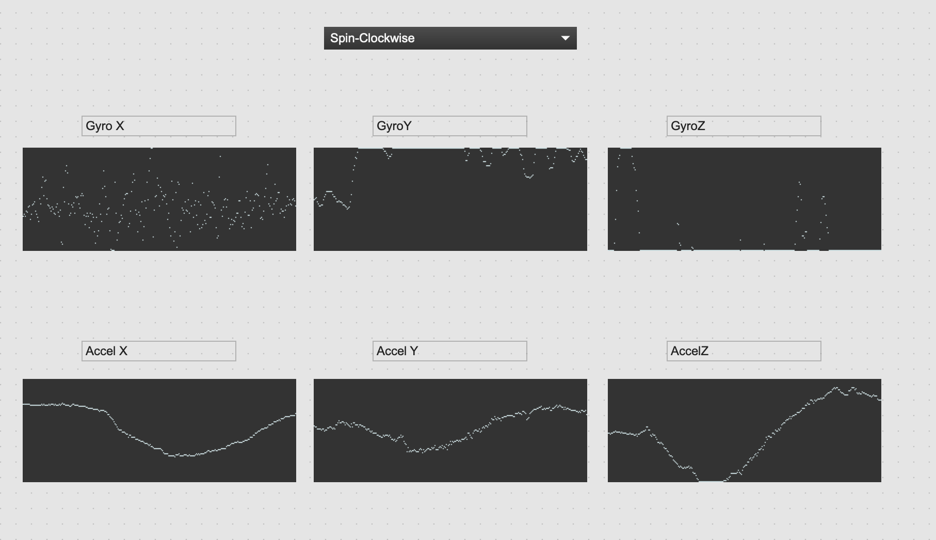
other documentation/photos/Screenshot 2023-05-17 at 8.41.33 PM.png
