mbardin/Cyberinet/other documentation/photos/Screenshot 2023-05-17 at 8.44.49 PM.png

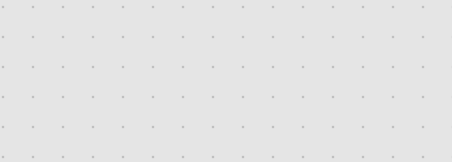
other documentation/photos/Screenshot 2023-05-17 at 8.44.49 PM.png
