mbardin/Cyberinet/other documentation/photos/Screenshot 2023-05-17 at 8.46.02 PM.png

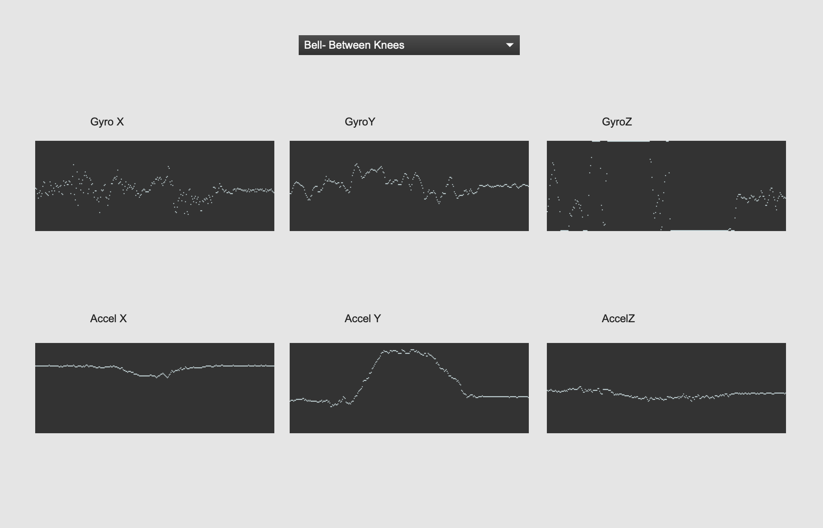
other documentation/photos/Screenshot 2023-05-17 at 8.46.02 PM.png
