mbardin/Cyberinet/other documentation/photos/smoothr.png

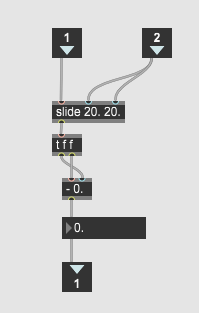
other documentation/photos/smoothr.png
