mbardin/Cyberinet/other documentation/photos/switchHelp.png

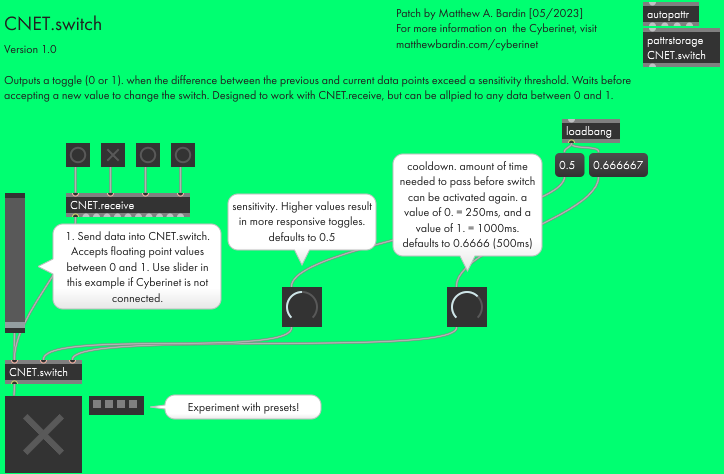
other documentation/photos/switchHelp.png
