mbardin/Cyberinet/other documentation/photos/TrumpetMutes.jpg

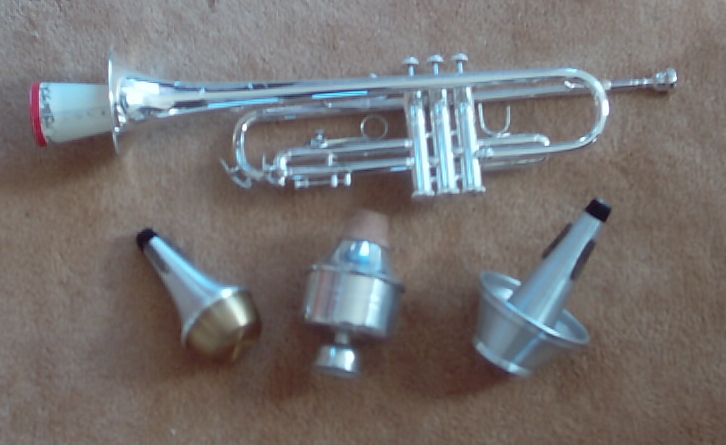
other documentation/photos/TrumpetMutes.jpg
