mbardin/Cyberinet/other documentation/photos/YSH000914_MIDI-Production-Center-3000-Limited-Edition-used-by-J-Dilla.jpg

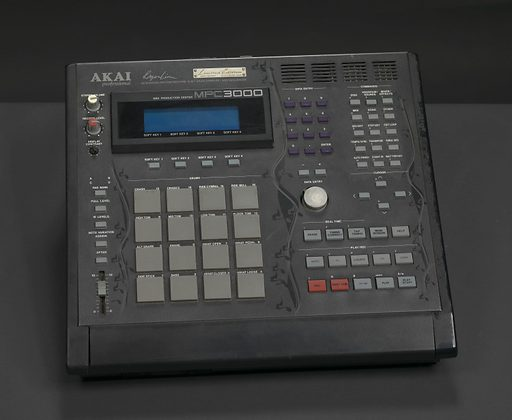
other documentation/photos/YSH000914_MIDI-Production-Center-3000-Limited-Edition-used-by-J-Dilla.jpg
