mbardin/Cyberinet/V1.3/PCBs/fsr_bb.png

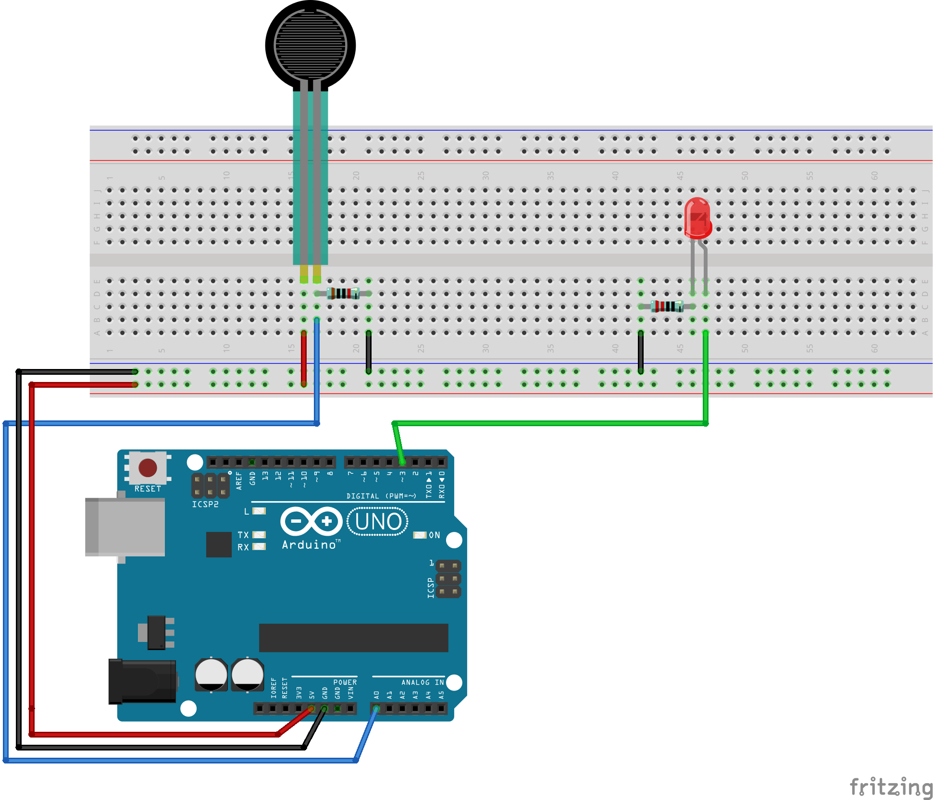
V1.3/PCBs/fsr_bb.png
