mbardin/Cyberinet/V1.3/PCBs/microphone/micBasic_pcb.png

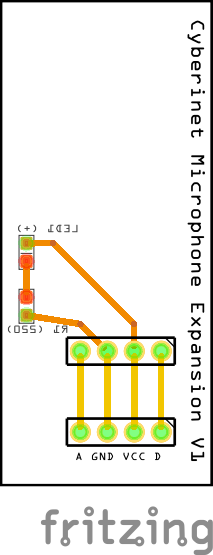
V1.3/PCBs/microphone/micBasic_pcb.png
