mbardin/Cyberinet/V_1.3/PCB Diagrams/Button Board/Screen Shot 2022-11-11 at 10.34.00 PM.png

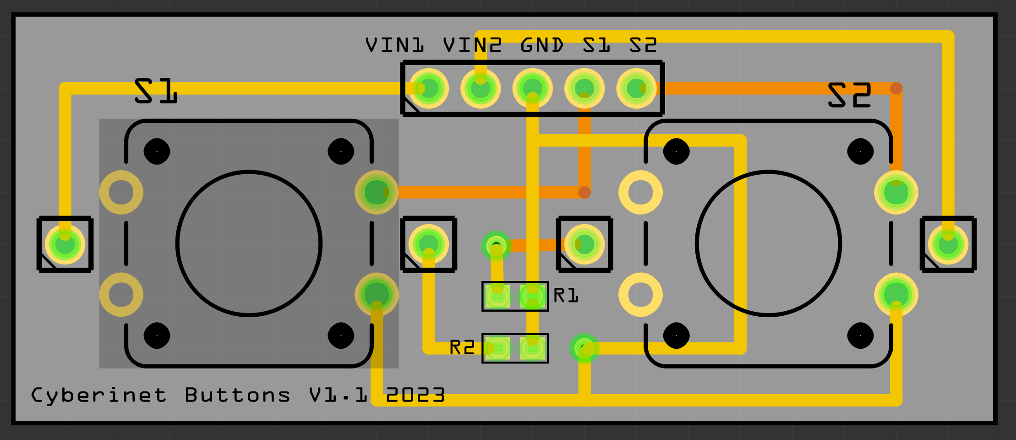
V_1.3/PCB Diagrams/Button Board/Screen Shot 2022-11-11 at 10.34.00 PM.png
