mbardin/Cyberinet/V_1.3/PCB Diagrams/Main Board/mainBoard.png

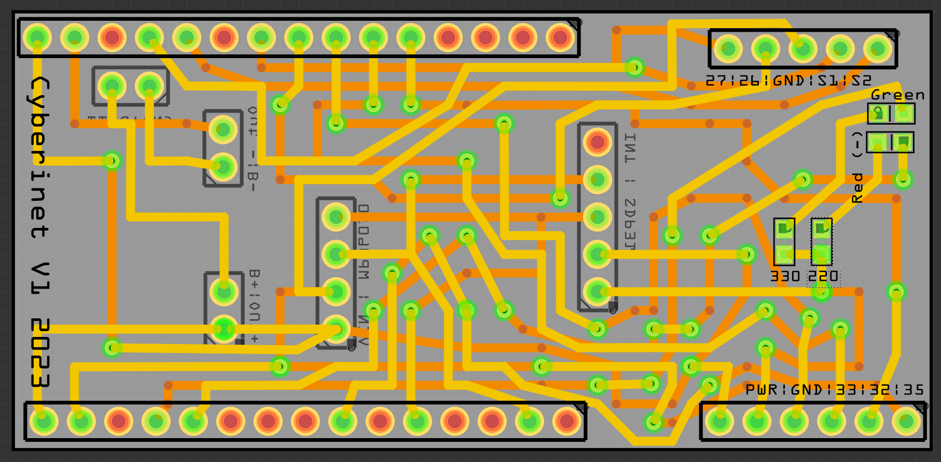
V_1.3/PCB Diagrams/Main Board/mainBoard.png
