mbardin/Cyberinet/zMusic Composition Scores/scores/materials/raindrops/planning diagrams/raindrops - 2023-03-05.pdf

# Raindrops on a Tin Roof

# for Cyberinet, pre-recorded sounds, and live electronics

# Matthew A. Bardin

2023


Program Note:
A short story. When you are the most comfortable, that is when the unknown can strike. Usually in a way we least expect.

Performance Notes:
For the Performance of Raindrops on a Tin Roof, a unique setup can be utilized. The theatrical stage setup is not required, but highly encouraged by the composer if possible as they enhance the atmosphere.

The performer should arrange three stands across the width of the stage. When instructed in the score, the performer should move from their current stand to the indicated stand. A smoke machine should be placed upstage and off-center of the performer to minimize its visibility from the audience. The smoke machine should be set to approximately medium-low. There should be a low mist/fog that picks up the lights in the room, not so much that it becomes obstructive.Two DMX-controlled lights should be placed slightly downstage of the performer, illuminating the stage. Stage lights should be turned off, but if needed spotlights, stand lights, or low-level lighting can be used to illuminate the three stands for the performer. Will all of the staging, the performance space should look like this:

Smoke Machine

3 | 1 | 2
Light | Light
| Audience

The following Performance Pages should be on the stands as shown below:

1. Pgs 1-2, 4-5, 9-10
2. Pgs 5-8
3. Pgs 2-4

Multiple stands at some stanf locations may be needed.

Adjustments to the staging can be made depending on the specifics of the performance venue. The atmosphere should be spooky, and as if rain will begin at any second. A fan is recommended to help dissipate the smoke following the performance.

Tempo markings should be observed as close as possible. Tempi indicated are those of the synthesizer accompaniment sound files. When the “as fast as possible” instruction occurs, the performer should play the section as fast as possible while still maintaining rhythmic and pitch integrity. Do not worry about playing in time with the synthesizer during these moments. There will be a moment to return to being in time with the synthesizer indicated with the button.

On Software:
The Raindrops on a Tin Roof Max Patch is required for the performance. This patch can be downloaded from matthewbardin.com/raindrops. If needed, Max (Version 8.5 or newer needed) can be downloaded from cycling74.com. It is not required to purchase the software as the patch will run in demo mode, however it is recommended if possible as purchasing the software will unlock editing and saving of patches.

The Max patch will take data from the Cyberinet’s embedded sensors and use them to process sounds as shown below:

Gyroscope:Used to control reverb and panning Accelerometer: Used to control DMX Lights, playback volume, and delay Airflow: Used to control DMX Lights, playback volume, and distortion Button 1: Used to cycle through settings and trigger audio clips Button 2: Emergency Mute All switch

Largely speaking, the Cyberinet controls the volume of various sound files on playback, as well as the processing to those sound files. The clarinet timbre is the only element with no processing applied to it.

There are three categories of sound files used in Raindrops on a Tin Roof:
1. Synthesizer Accompaniment: Unnatural, distorted sounds to accompany the clarinet timbres.
2. Ambiance: Digetic sounds occurring in the story as it unfolds. These include rain sounds, monster sounds, and creaking floorboards
3. Narrator: Recordings of the composer reading the story. These are used to provide context to the music as it is happening. Generally the music pauses during these moments.

On Hardware:
The performer will need the Cyberinet as well as the button expansion to perform Raindrops on a Tin Roof. In addition to the items listed under ‘Performance Notes’, The performer will require a computer to run the software patch. This computer can be either Windows or MacOS. The software patch will run on either devices. A USB-to-DMX adapter for each of the lights are also needed as they will be controlled from the max patch.

On Notation:
Cross Noteheads: Indicate pressing Button 1 to progress to the following section of music.

Vamp: Repeat the indicated music as many times as wanted or needed. Each vamp should occur at least 3 times. All other repeats occur once.

Metric Relations: eighth notes are constant throughout whenever a time signature change occurs.

Travel Instructions: Tell the performer their method of moving from one stand to another. This text is always underlined.

Movement Indicators: Indicate exaggerated movements or breathing. Exaggerated movements should generally be swaying or small steps to trigger the gyroscope more. Exaggerate breathing should be heavier and more frequent breaths than normal in order to further trigger the airflow sensor. Take care not to hyperventilate.

Synthesizer parts: Are not intended to be performed by a person. The part present in the score is the notation of the accompanying sound file. This notation does not reflect the specific processing applied to the sounds as that will change with each performance, but general indications are given to help the performer stay in time with the accompaniment.

Narrator Text: Text indicators for the narrator files are printed in the score. The first and last line are printed; separated with an ellipsis (...). The duration of the file is also provided. This text is always boxed and italicized.

Print Versions of the score arrive hole punched for storage, but are kept loose for arrangement on the stands. Extra copies of necessary pages are provided

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

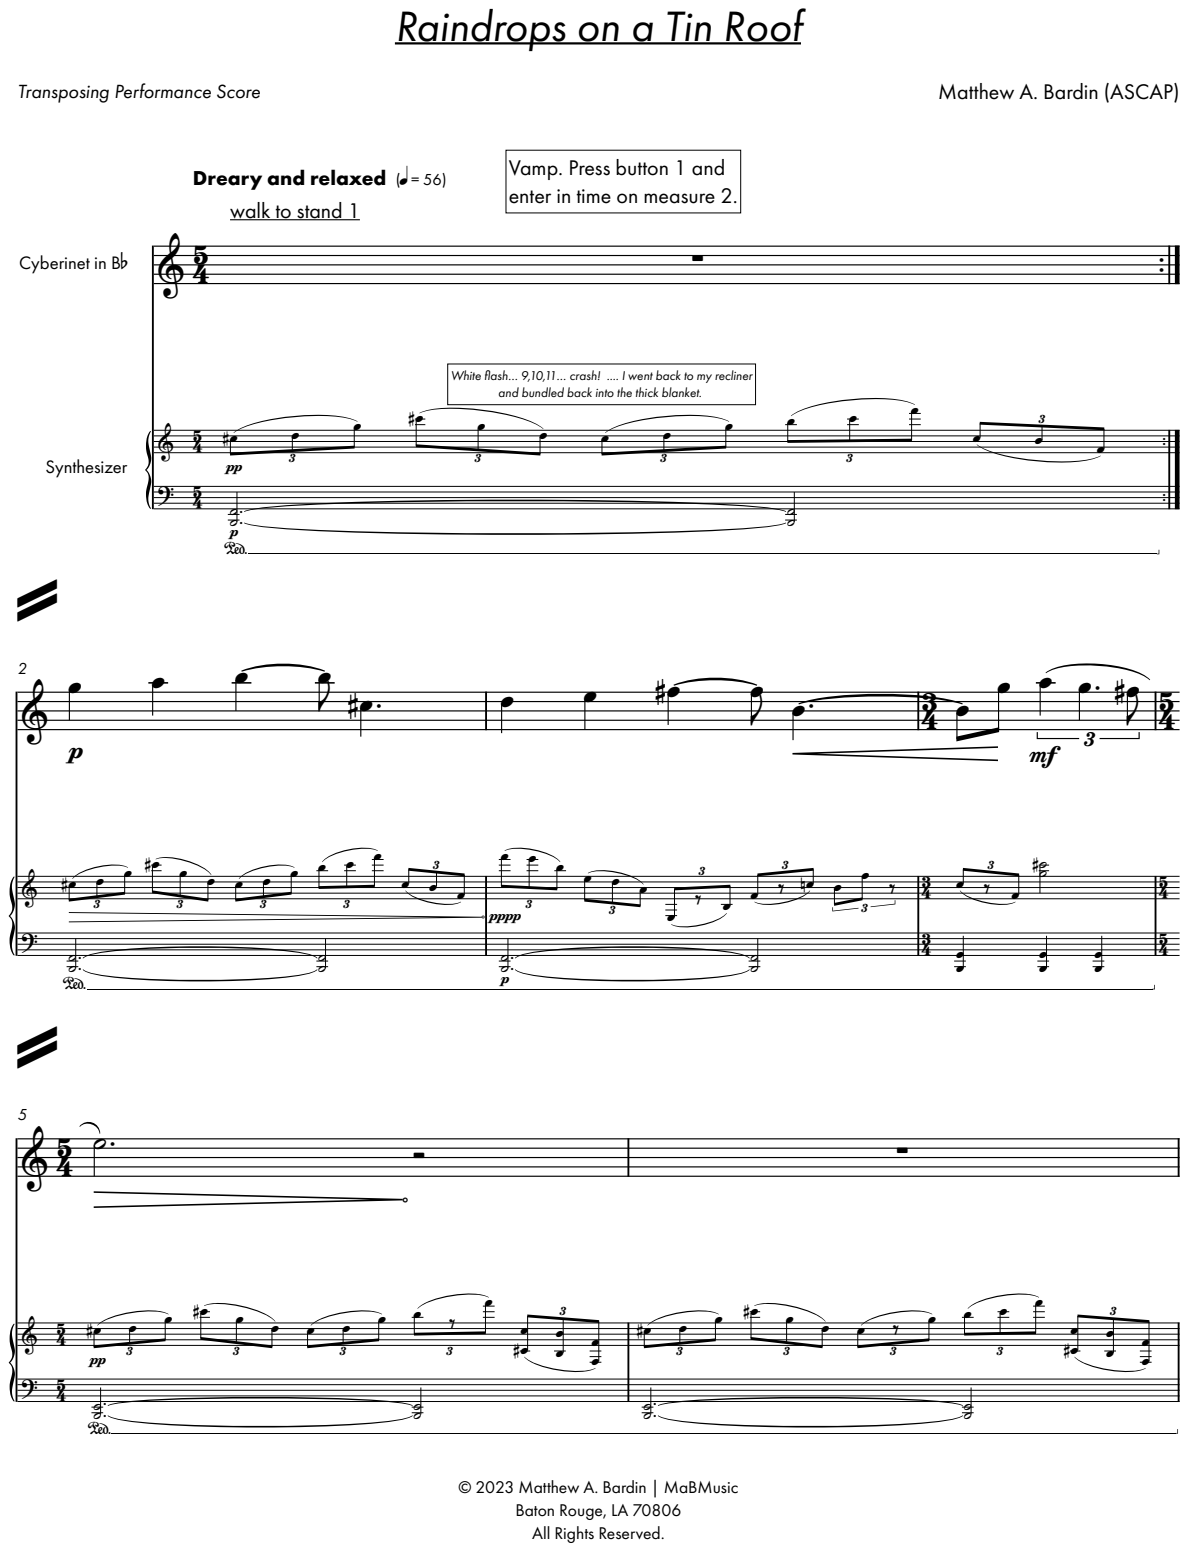
[picture p199: page 7]

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

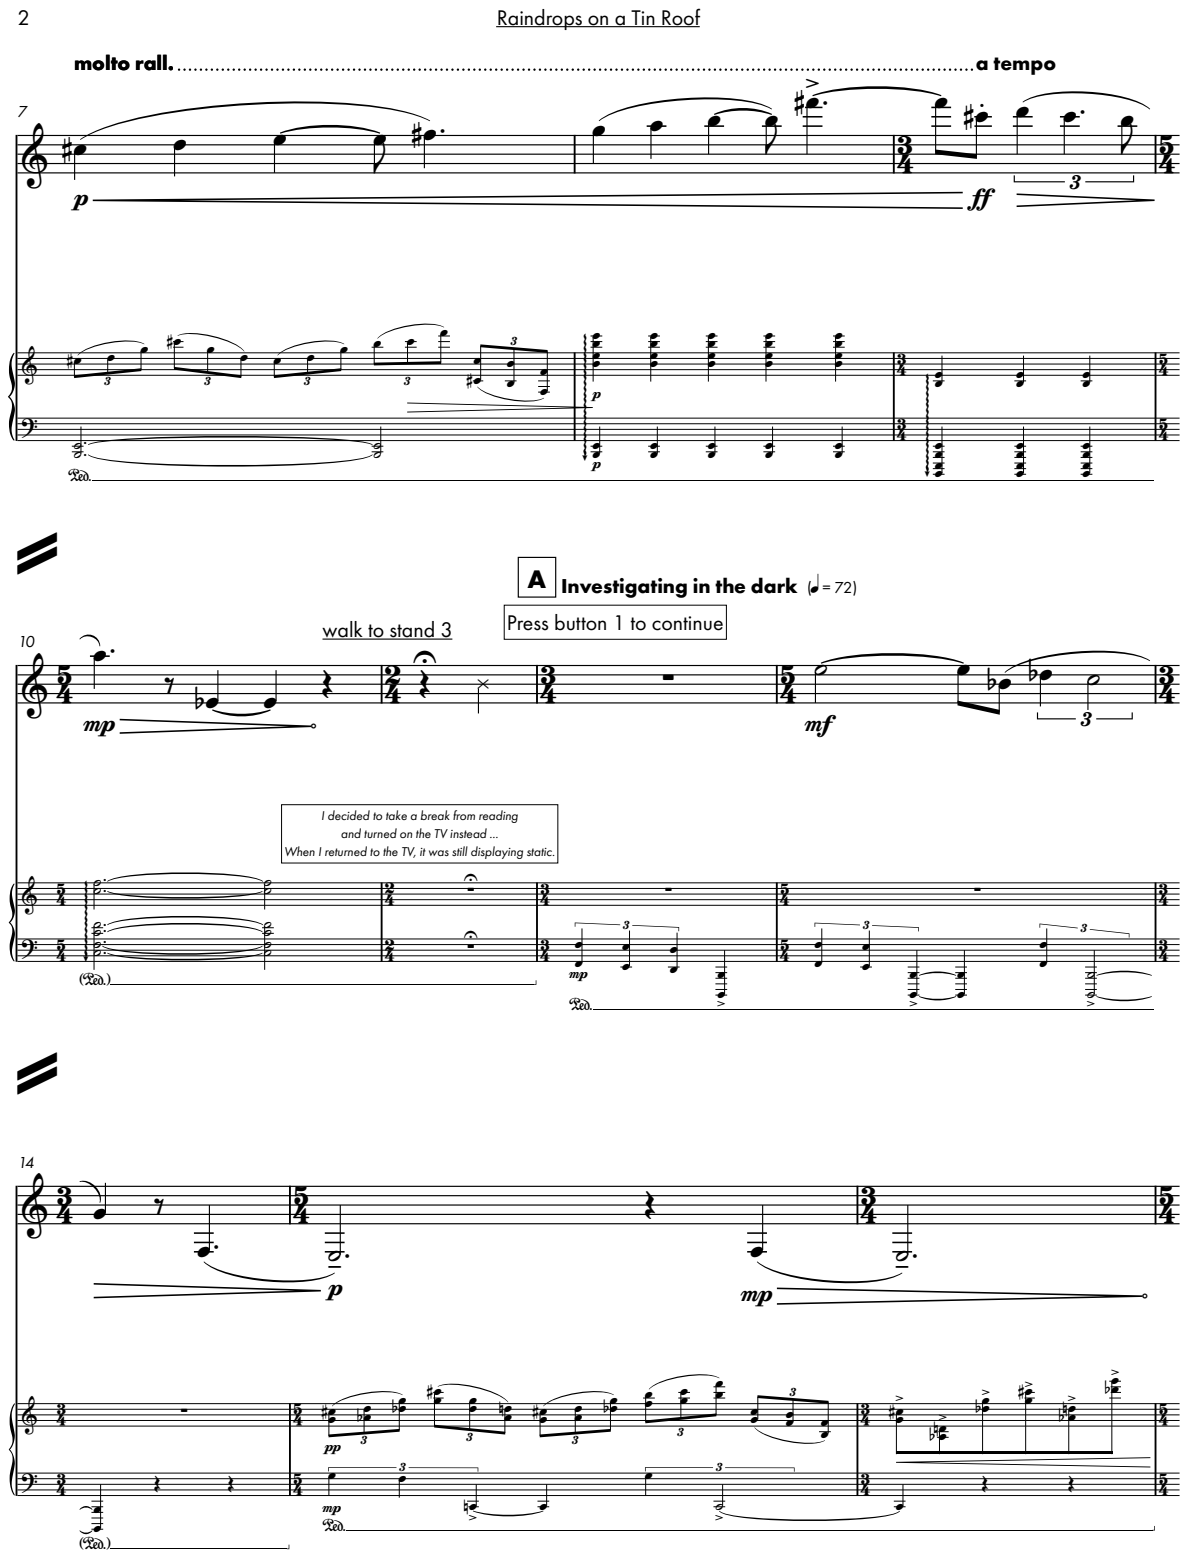
[picture p200: page 8]

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

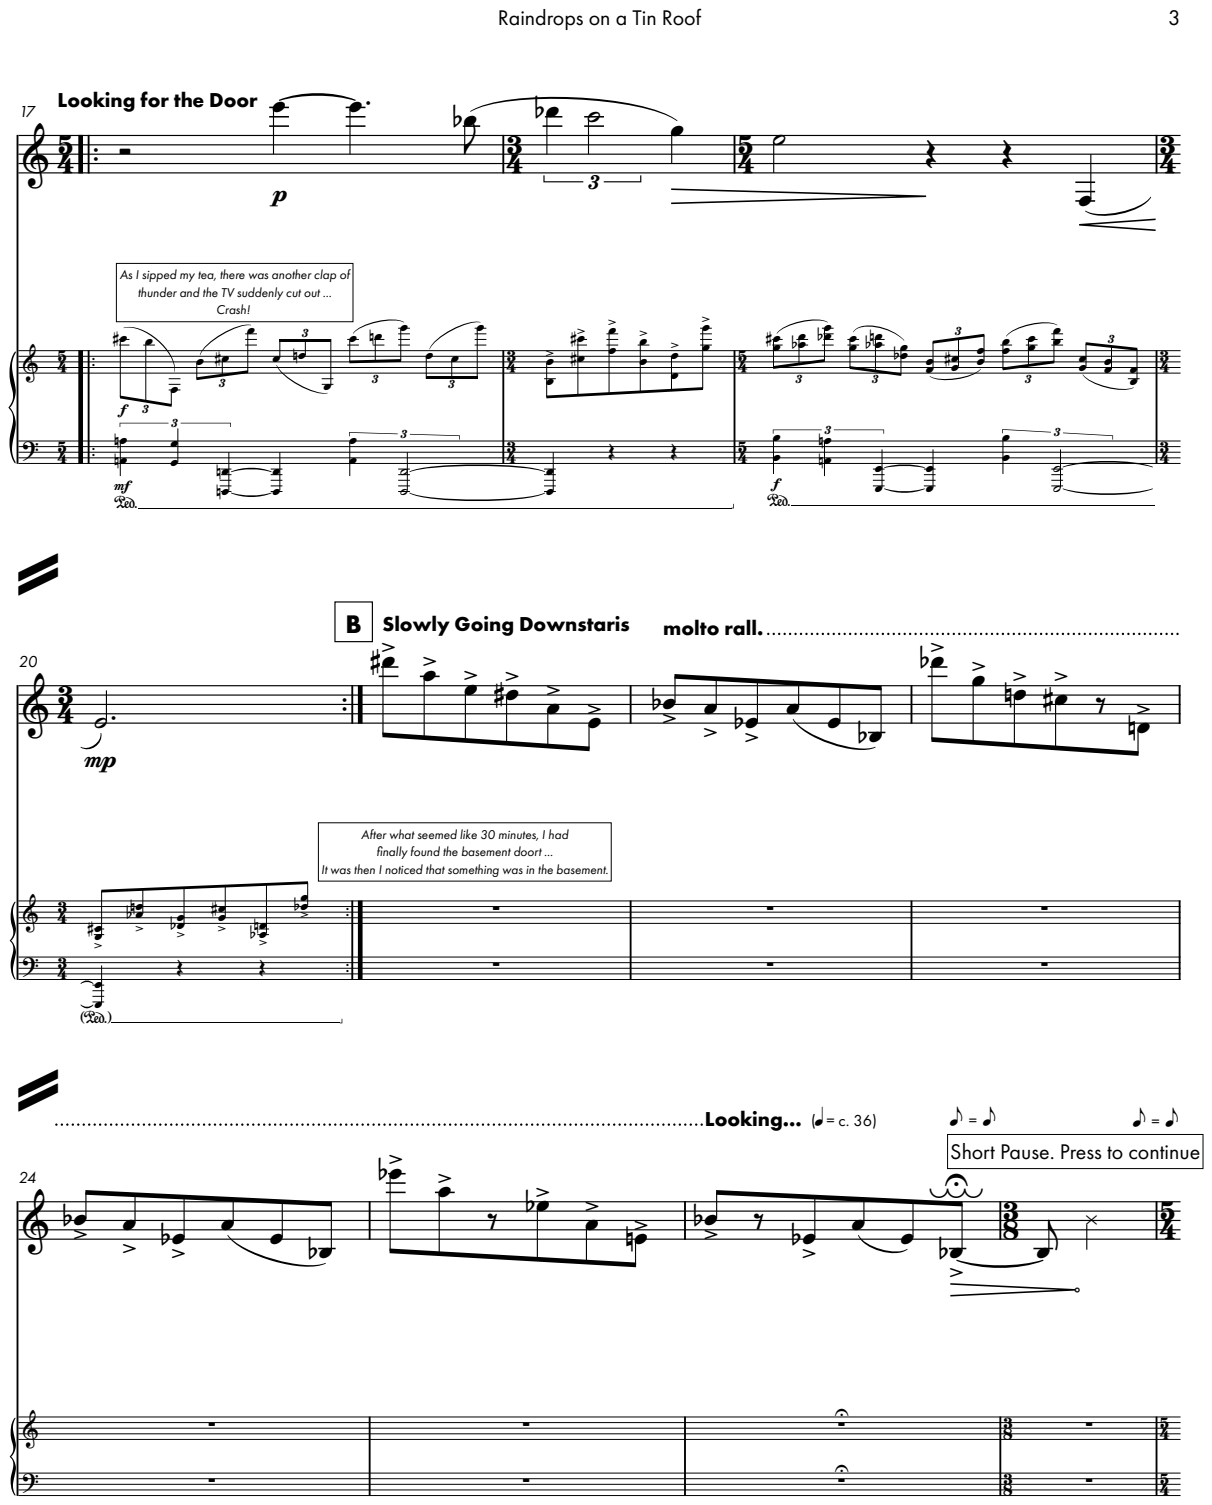
[picture p201: page 9]

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

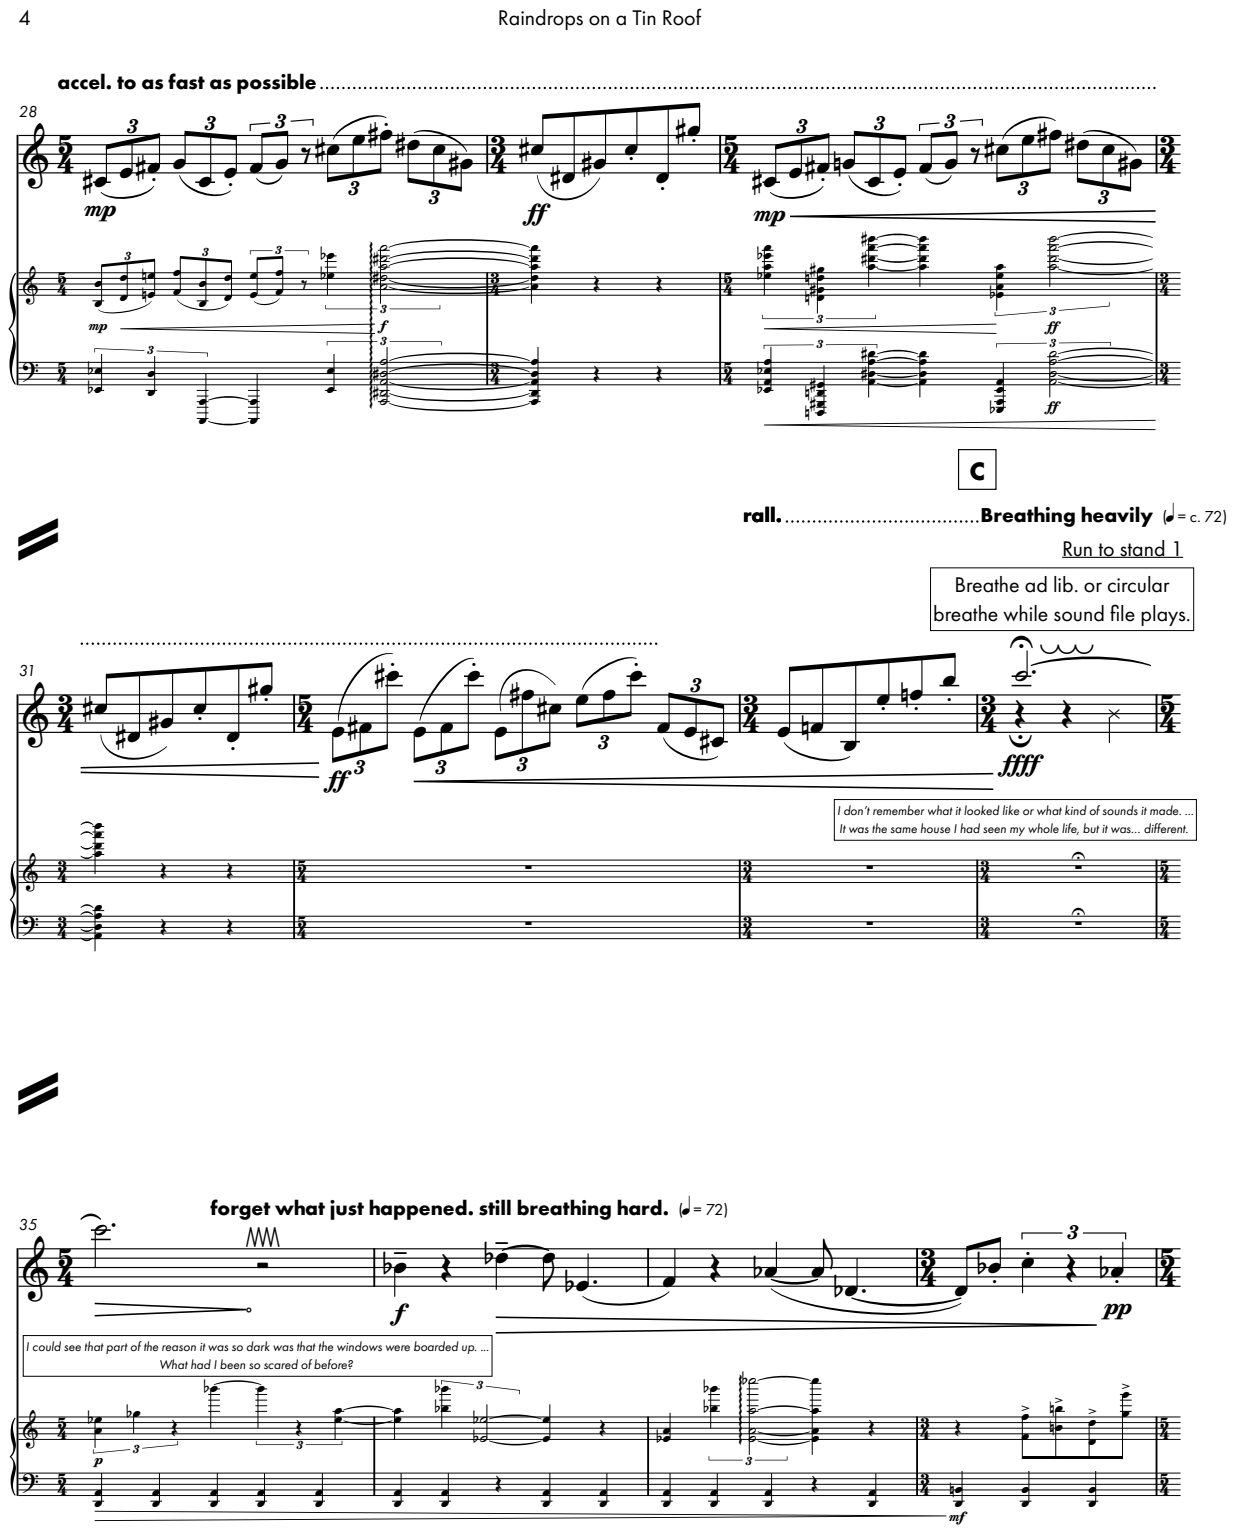
[picture p202: page 10]

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

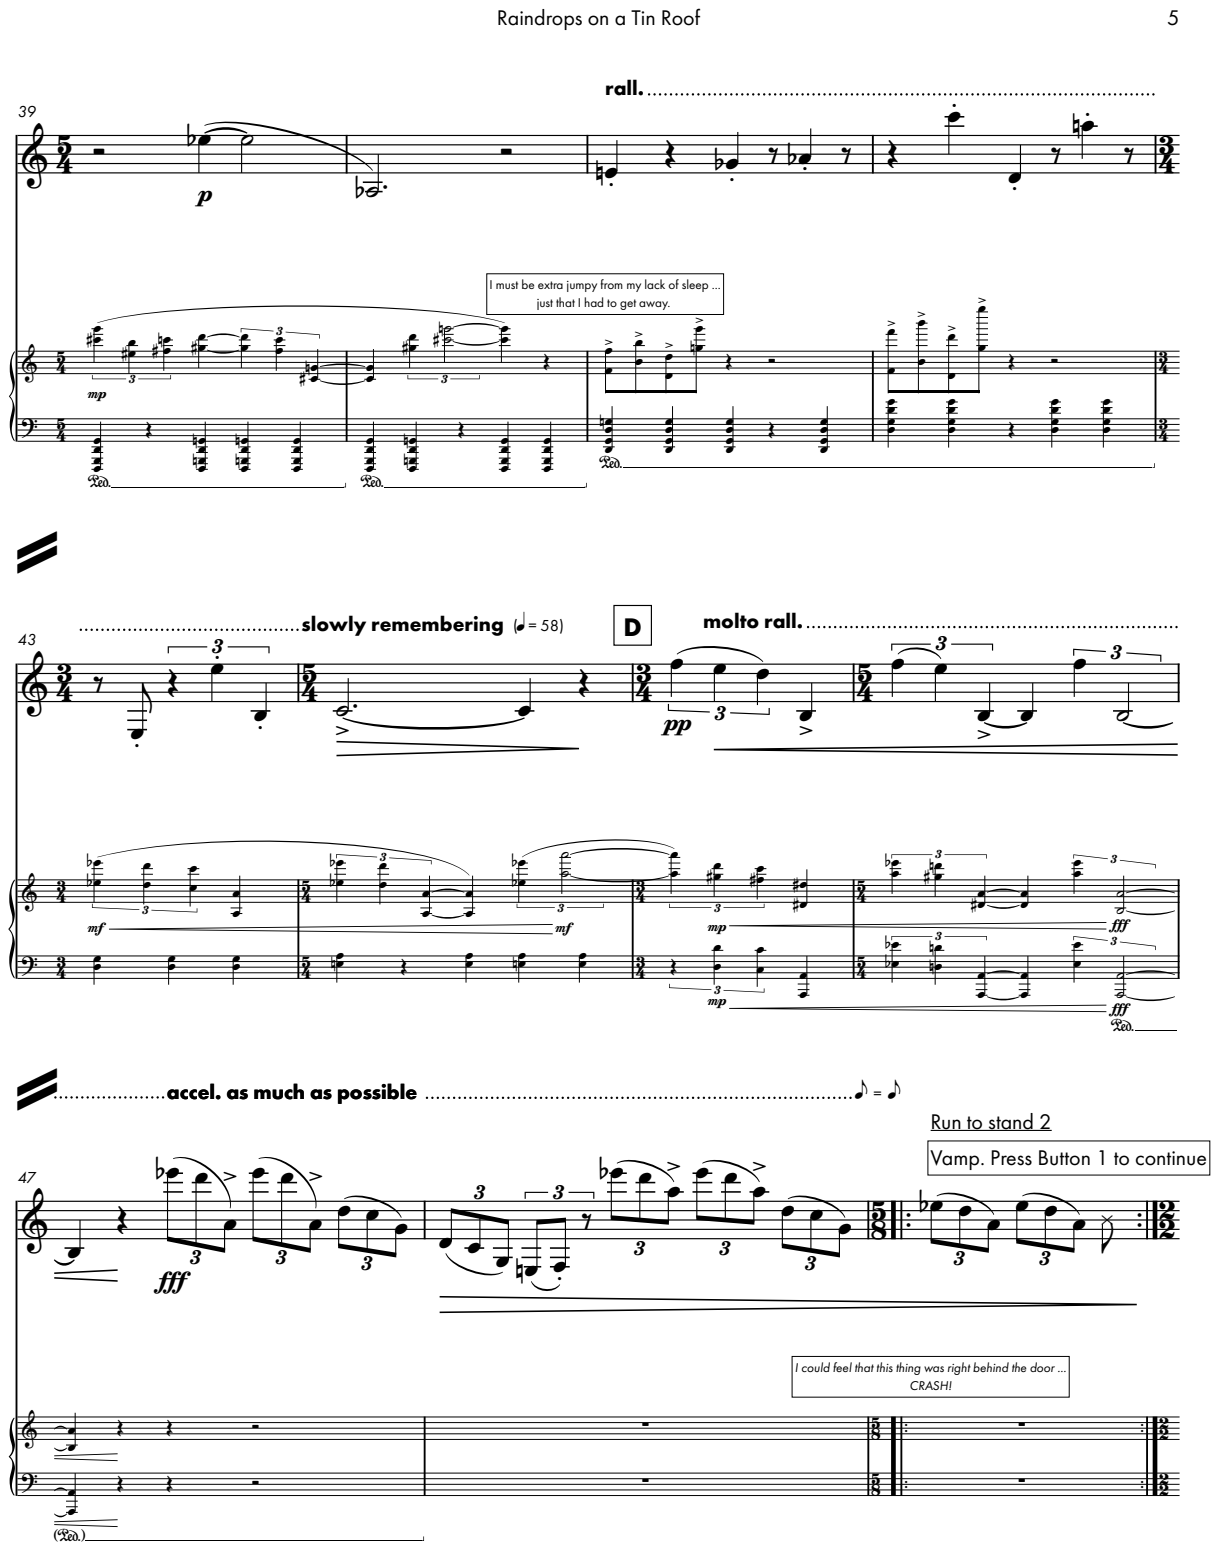
[picture p203: page 11]

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

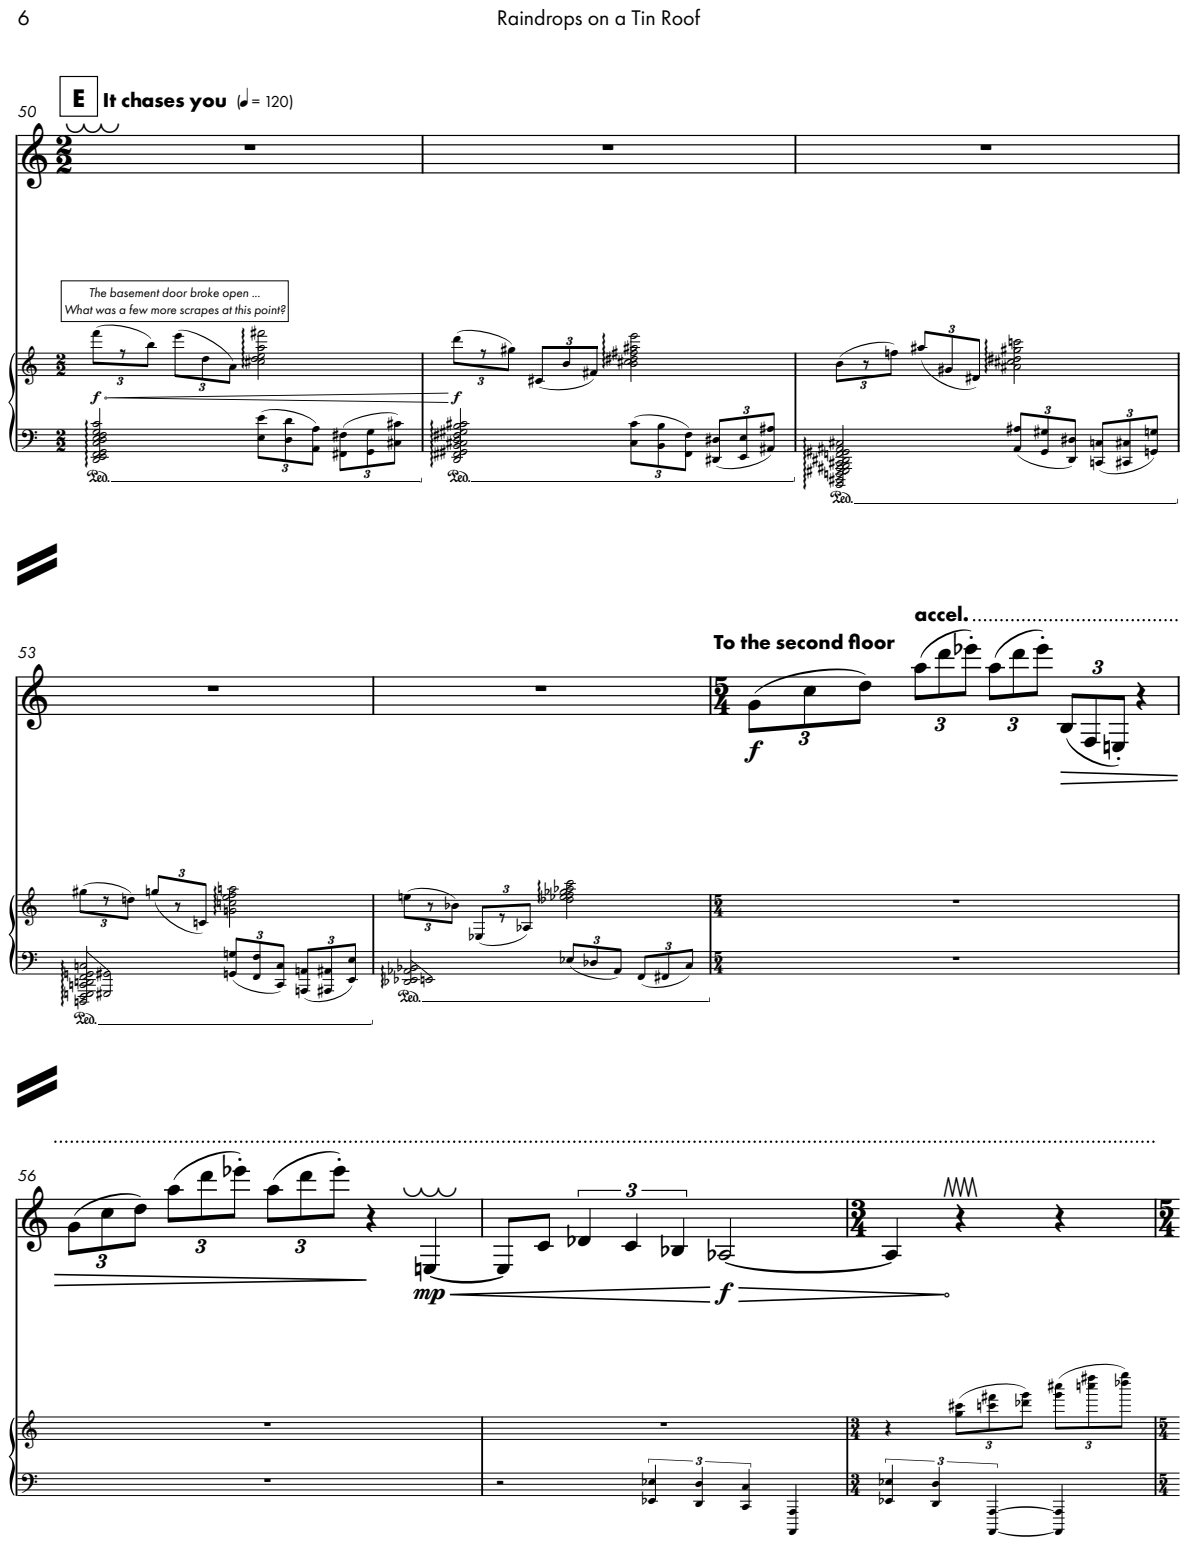
[picture p204: page 12]

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

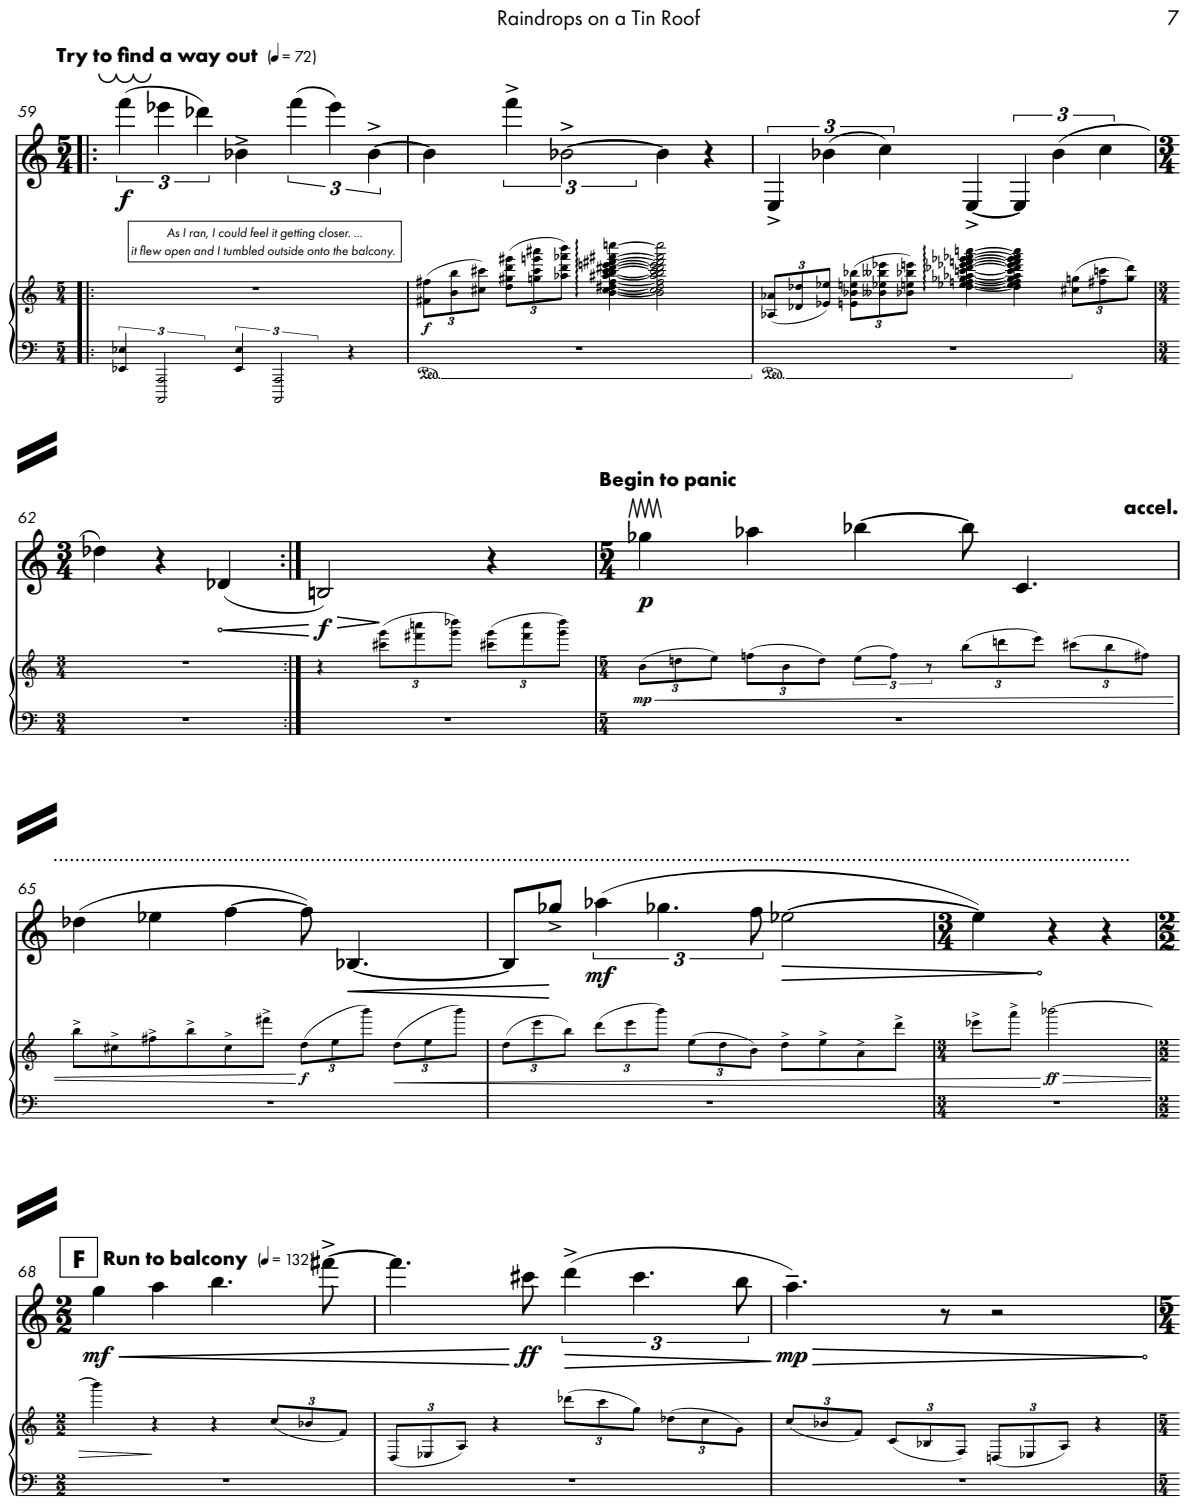
[picture p205: page 13]

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

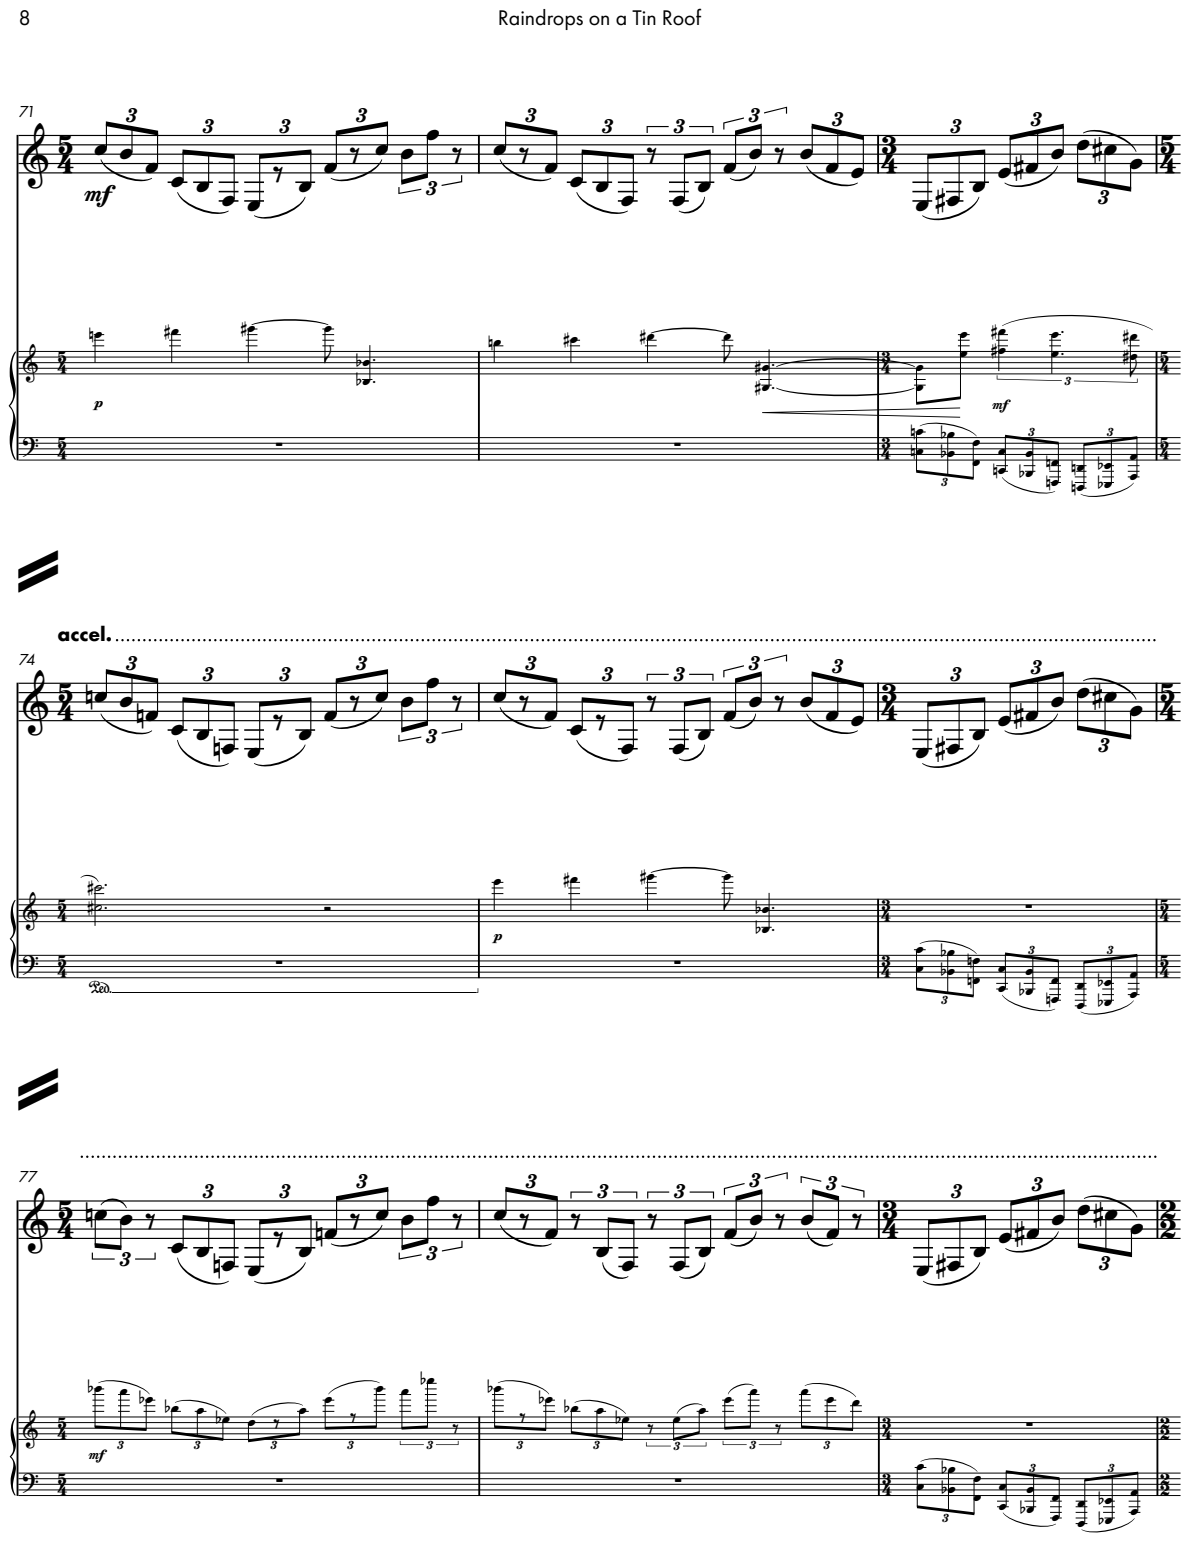
[picture p206: page 14]

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

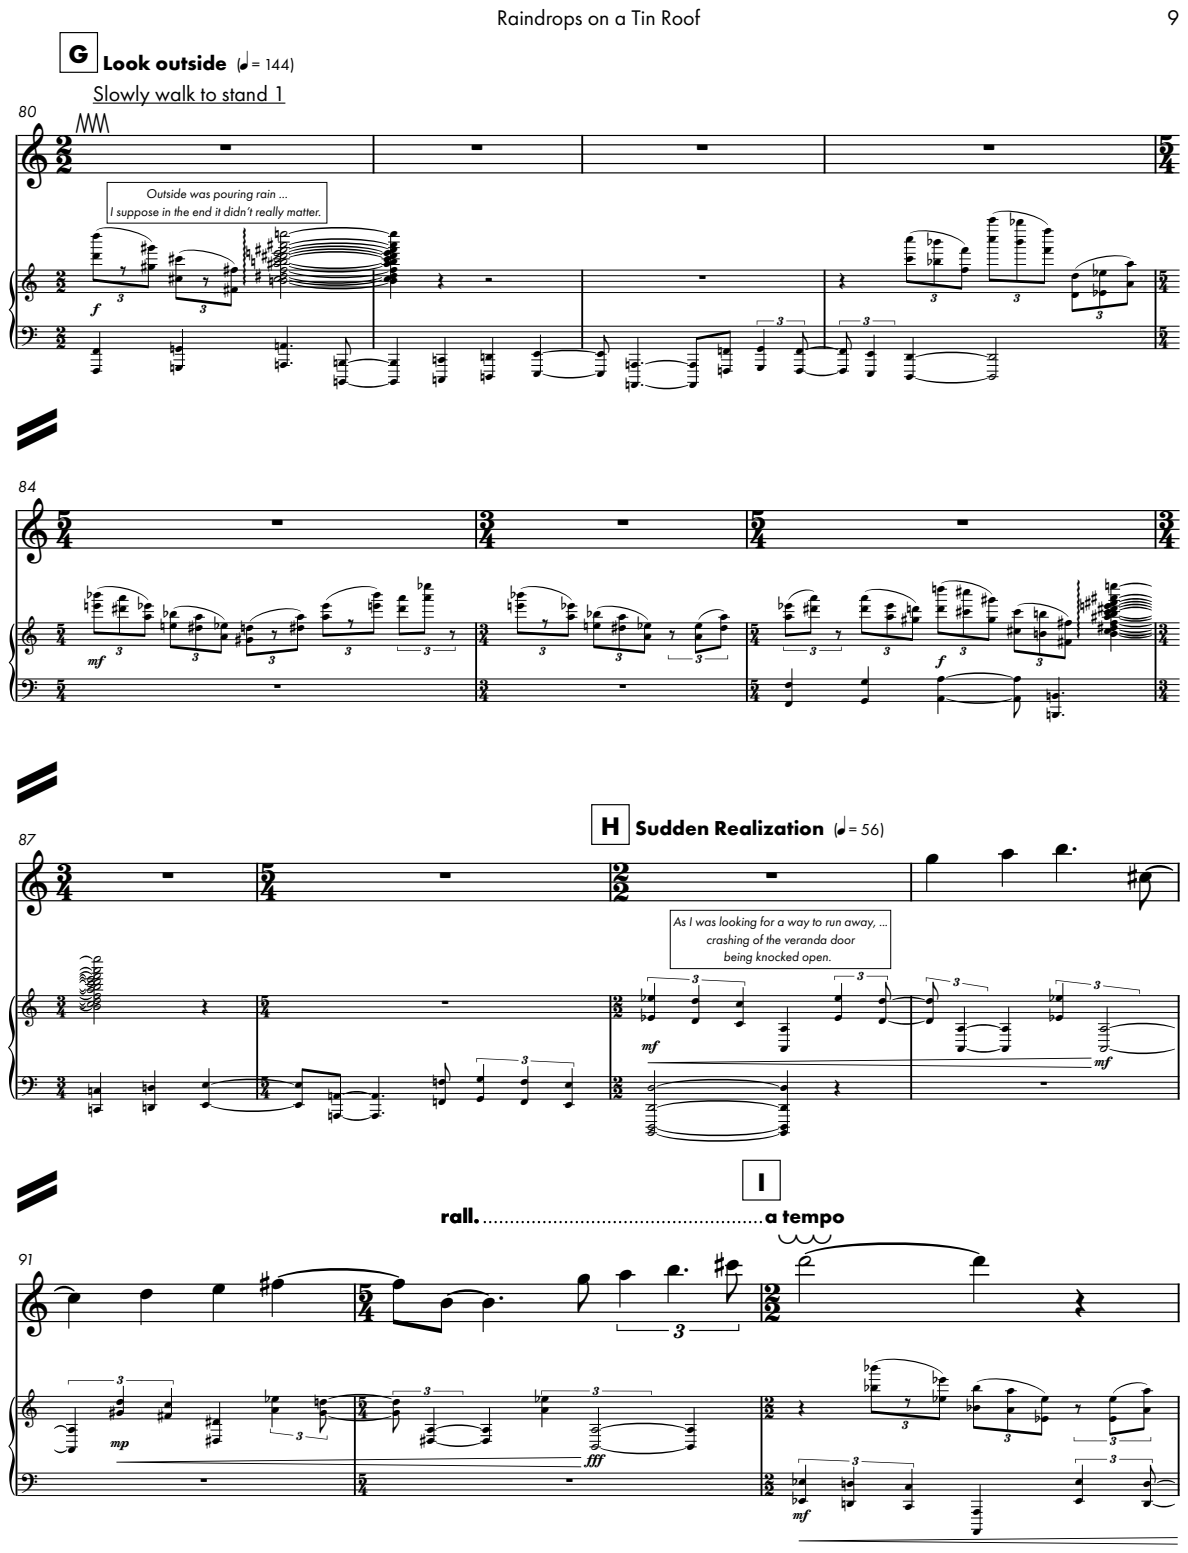
[picture p207: page 15]

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

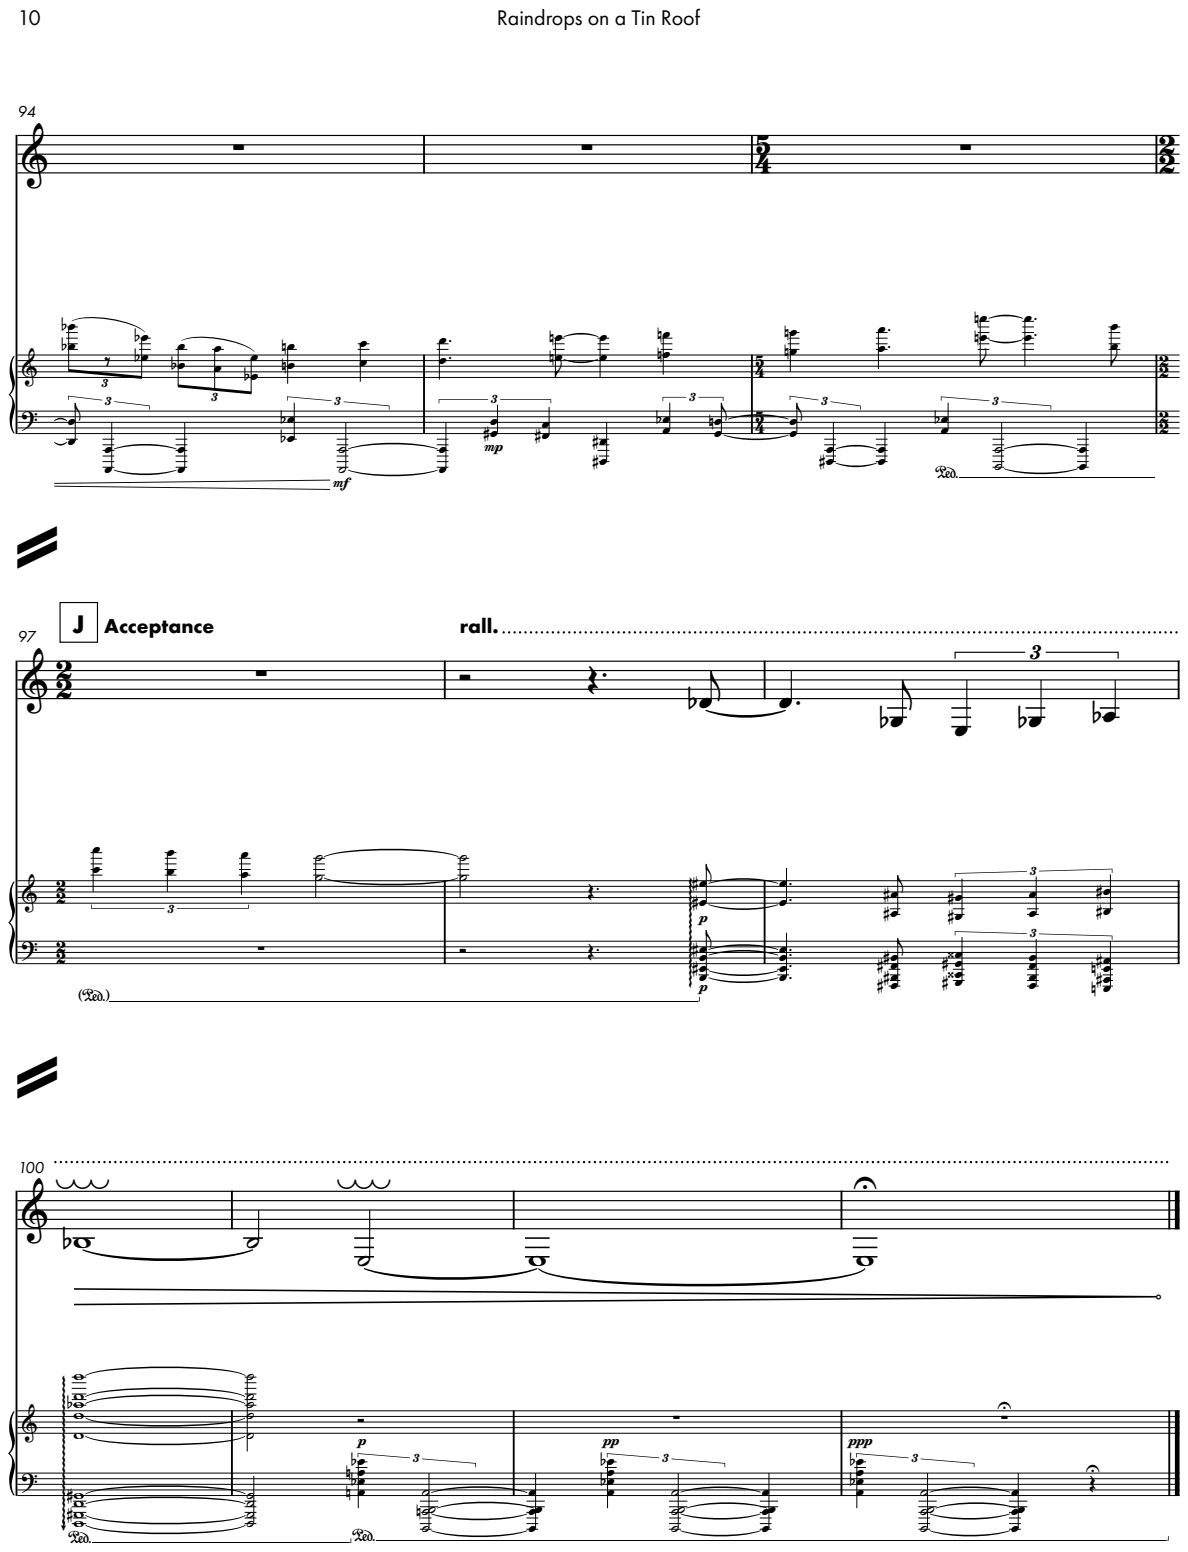
[picture p208: page 16]
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
