mbardin/Cyberinet/zMusic Composition Scores/performances/Lecture Recital/Bardin Lecture Recital Materials/compressorGen.png

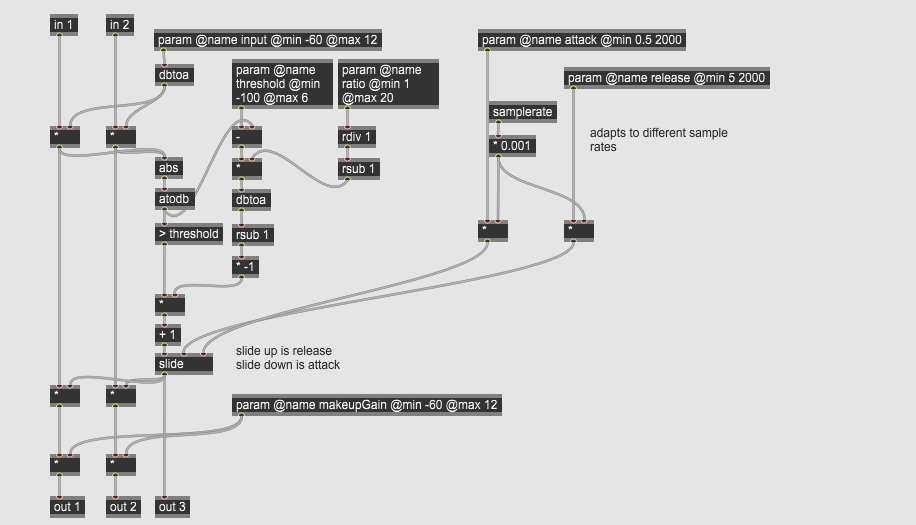
zMusic Composition Scores/performances/Lecture Recital/Bardin Lecture Recital Materials/compressorGen.png
