mbardin/Cyberinet/zMusic Composition Scores/scores/materials/raindrops/planning diagrams/IMG_1228.JPG

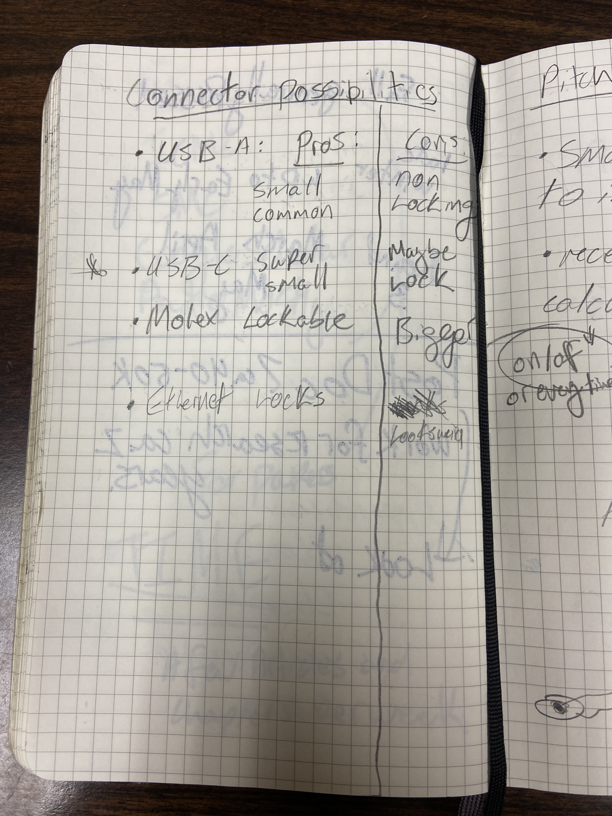
zMusic Composition Scores/scores/materials/raindrops/planning diagrams/IMG_1228.JPG
