mbardin/Cyberinet/other documentation/photos/CNET.test.png

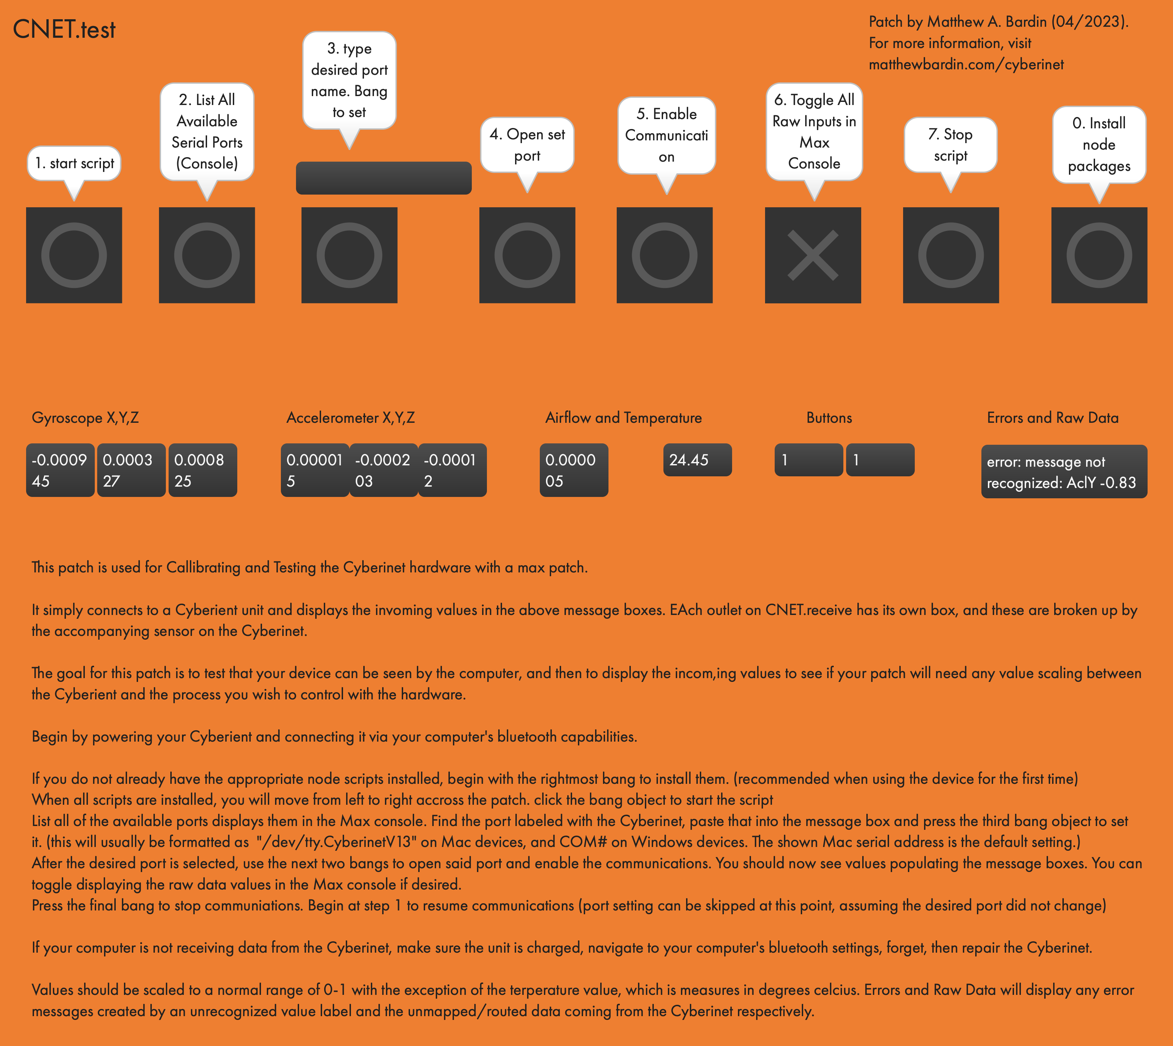
other documentation/photos/CNET.test.png
