mbardin/Cyberinet/zMusic Composition Scores/performances/Lecture Recital/Bardin Lecture Recital Materials/Puzzle of a park - Solo Voice Only.pdf

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

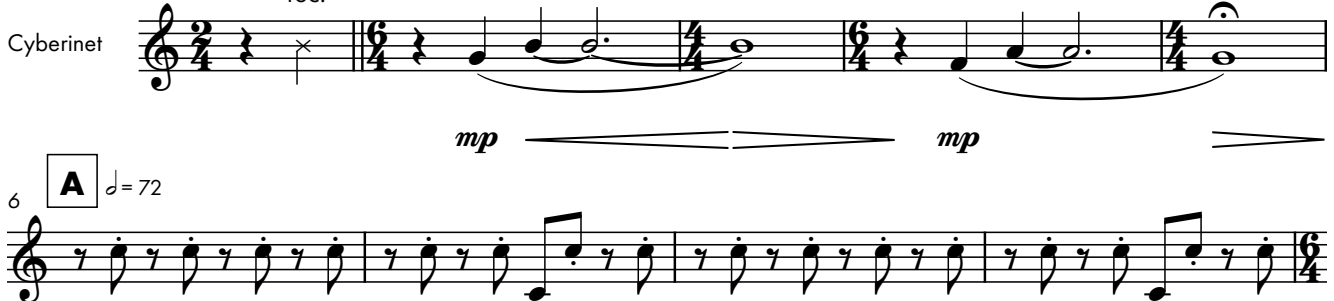
[picture p242: figure]

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

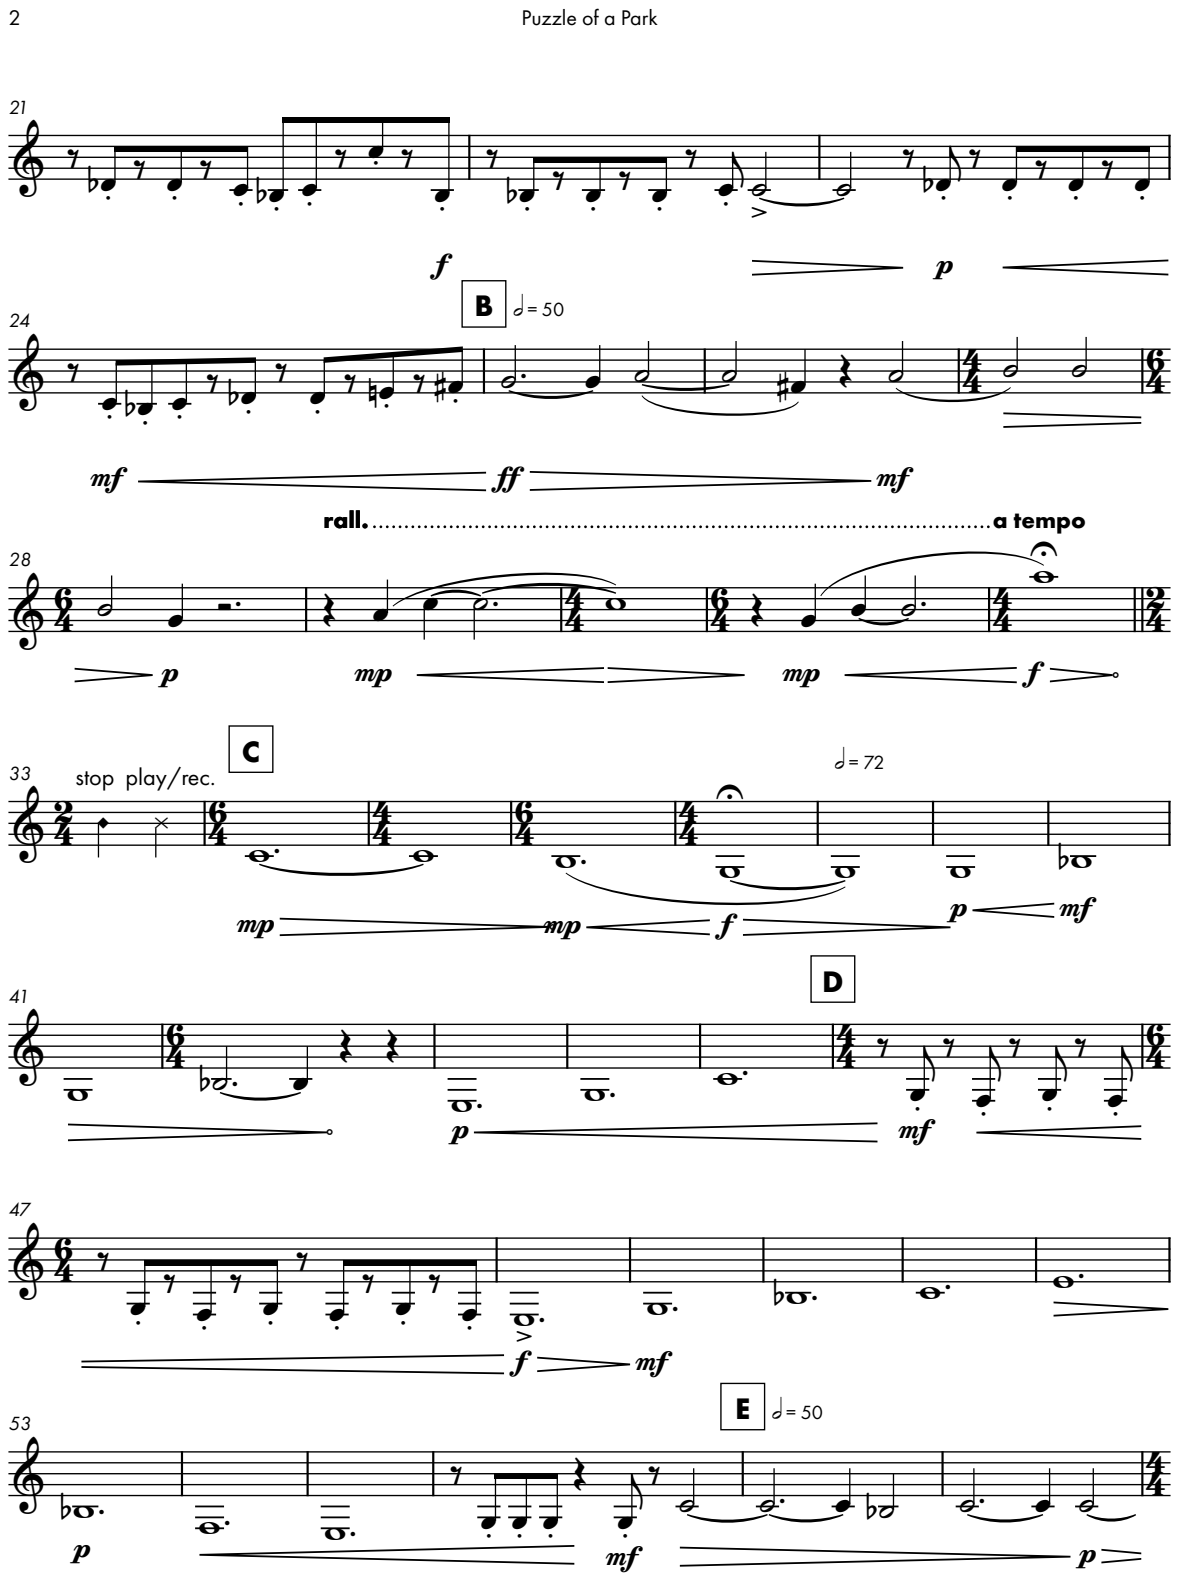
[picture p243: page 2]

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

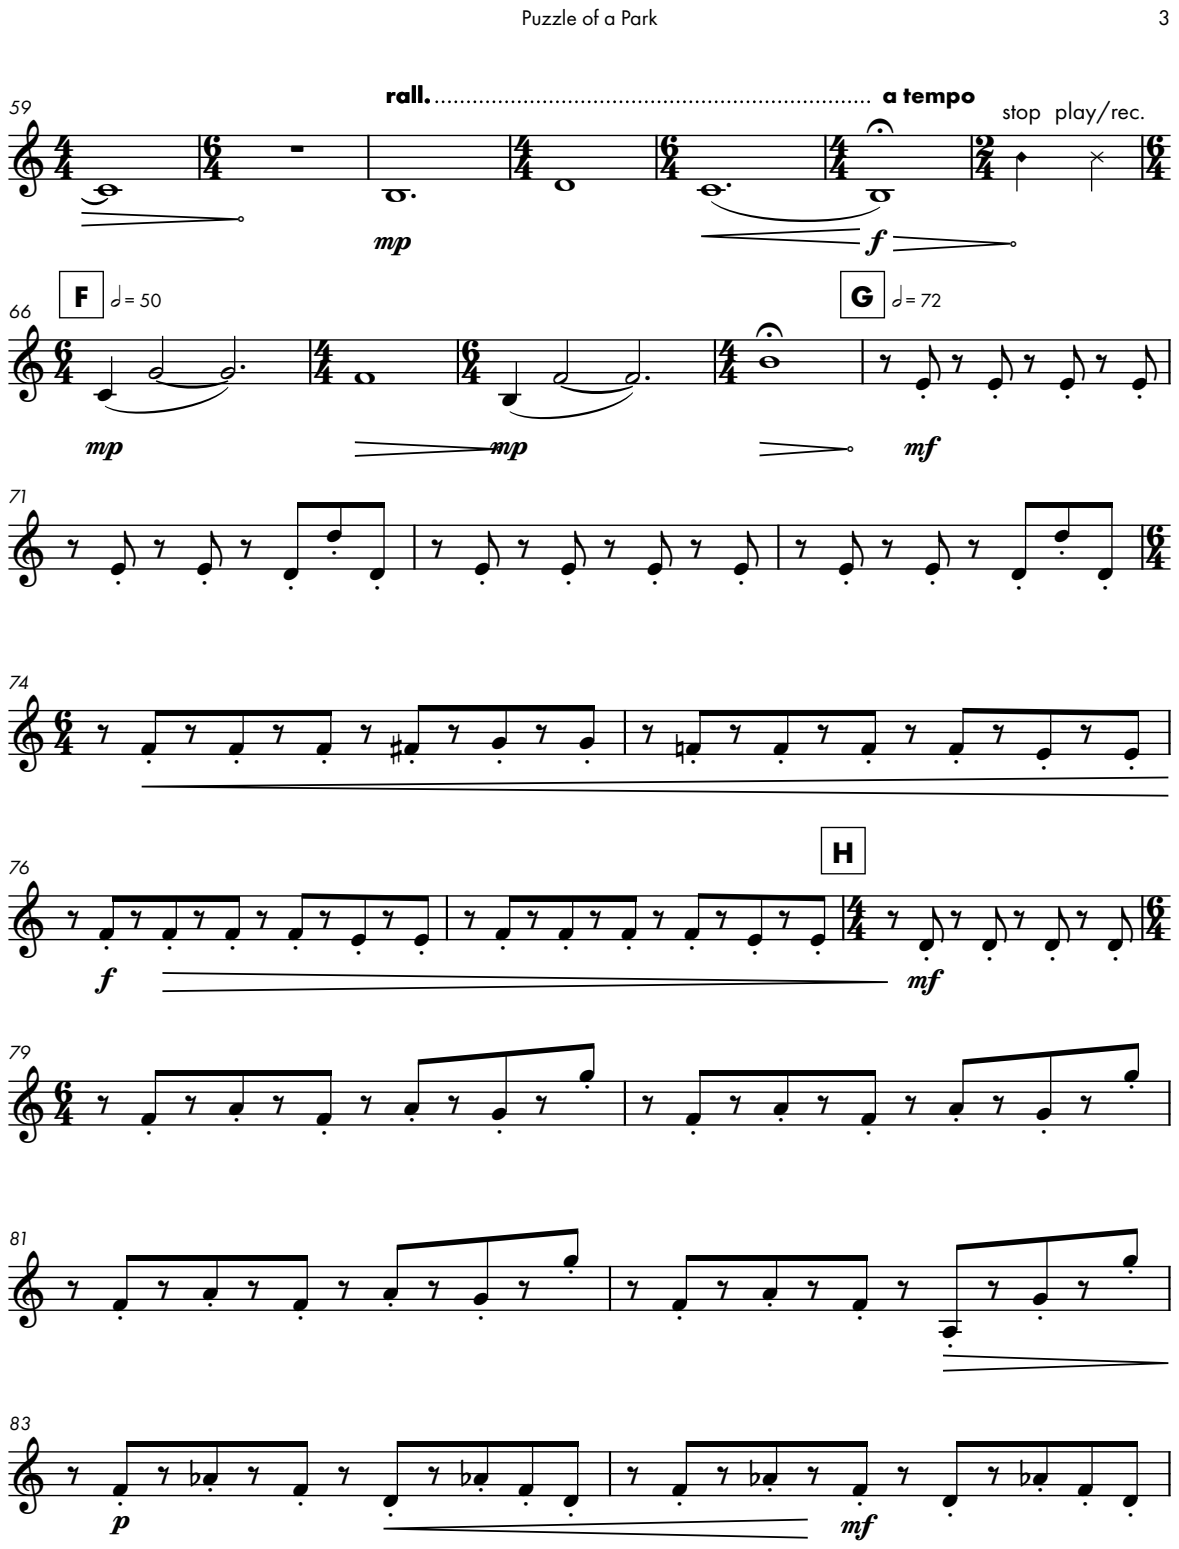
[picture p244: page 3]

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

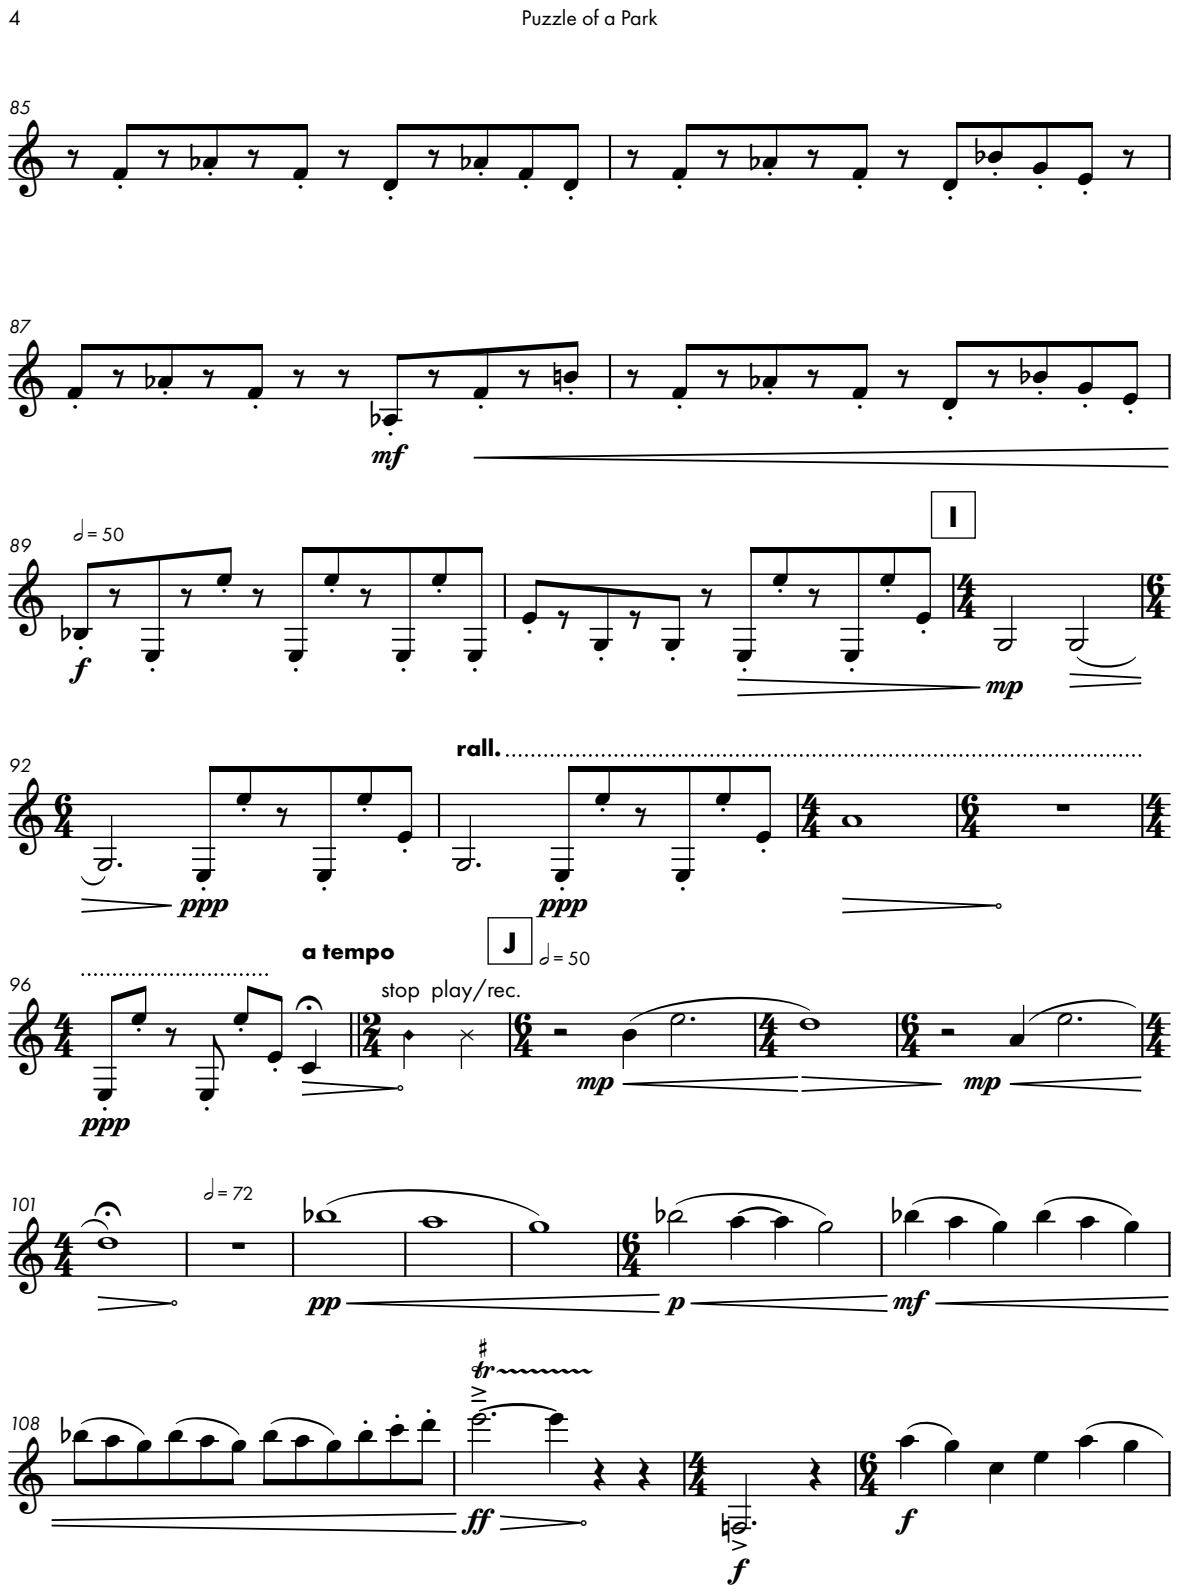
[picture p245: page 4]

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

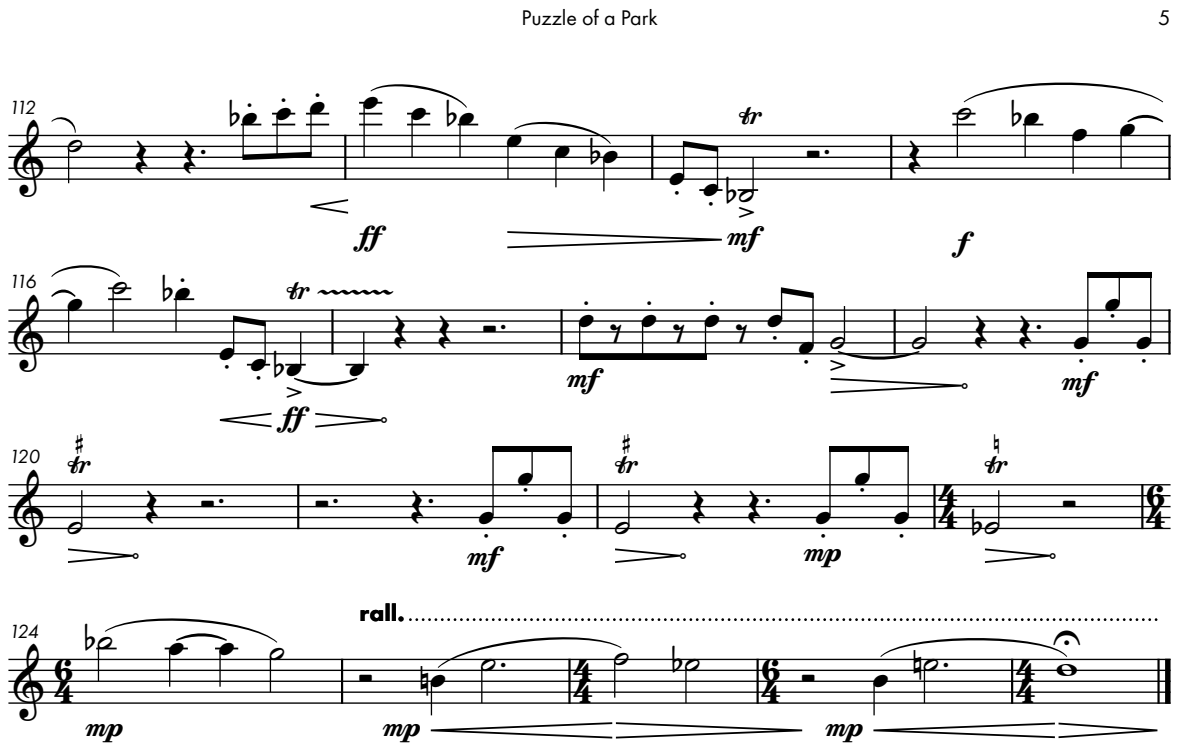
[picture p246: page 5]
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
