mbardin/Cyberinet/zMusic Composition Scores/scores/materials/raindrops/planning diagrams/raindrops - 2023-02-22.pdf

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

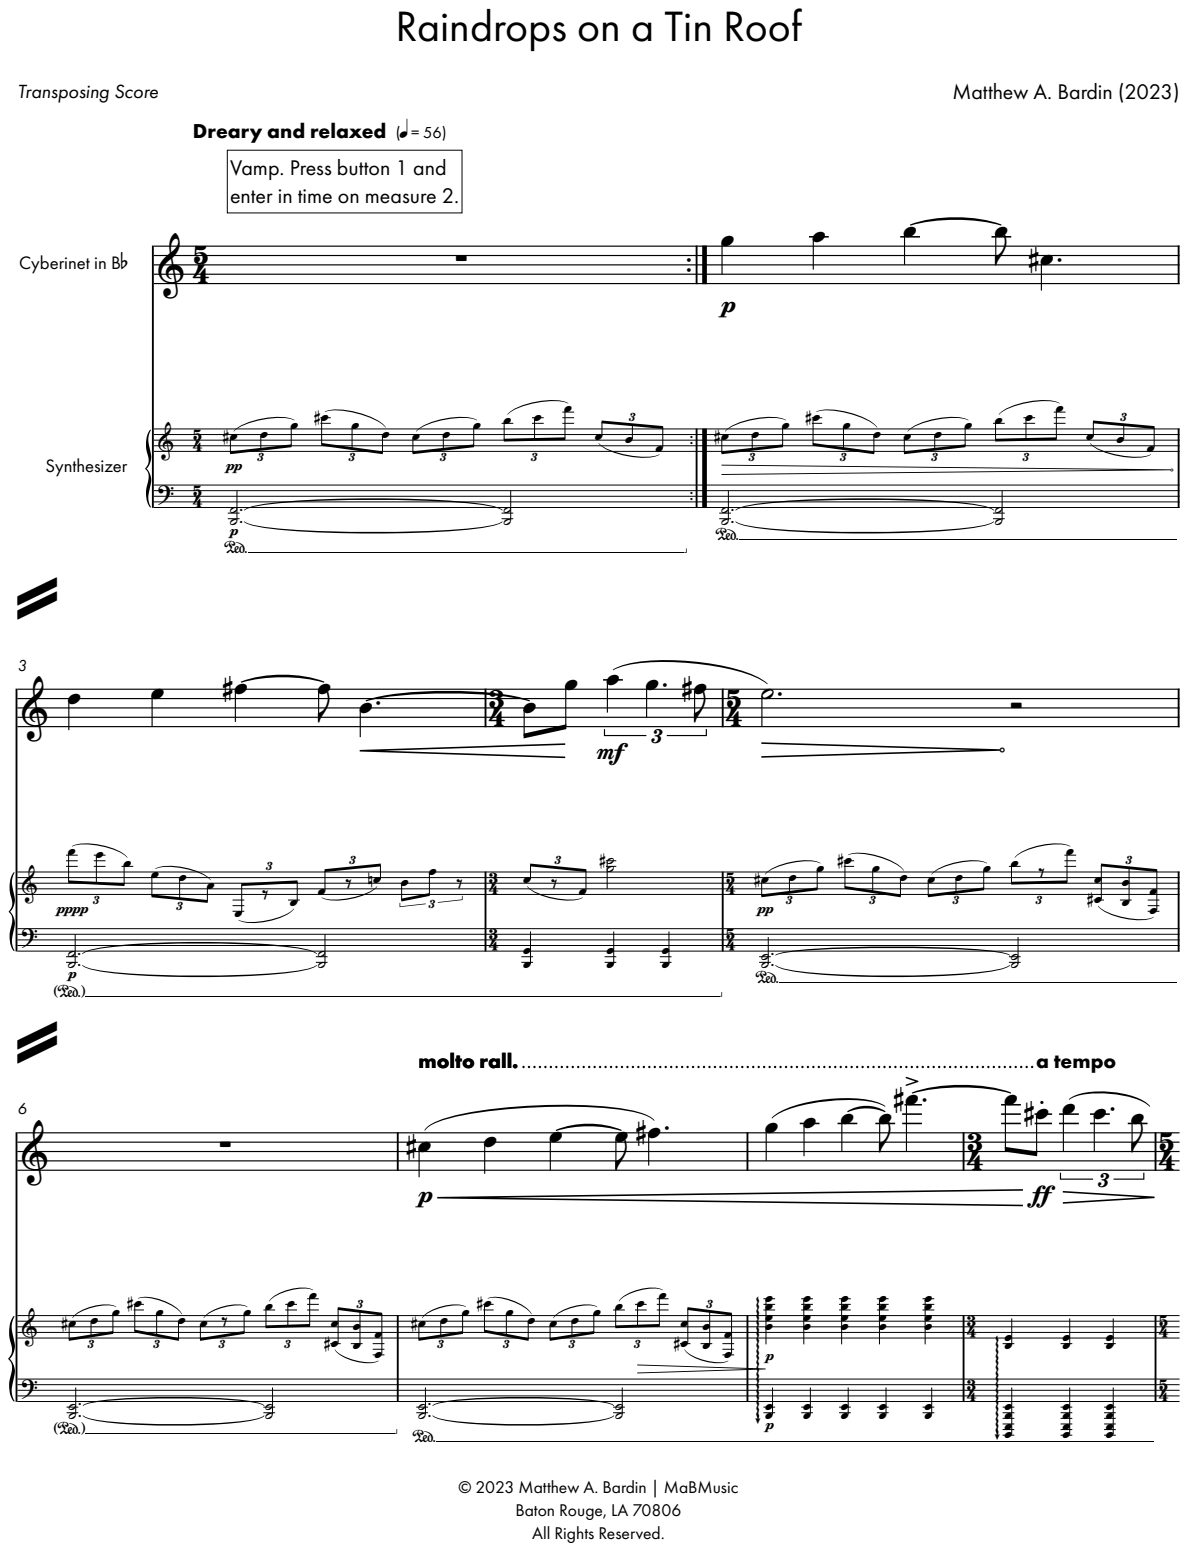
[picture p247: page 1]

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

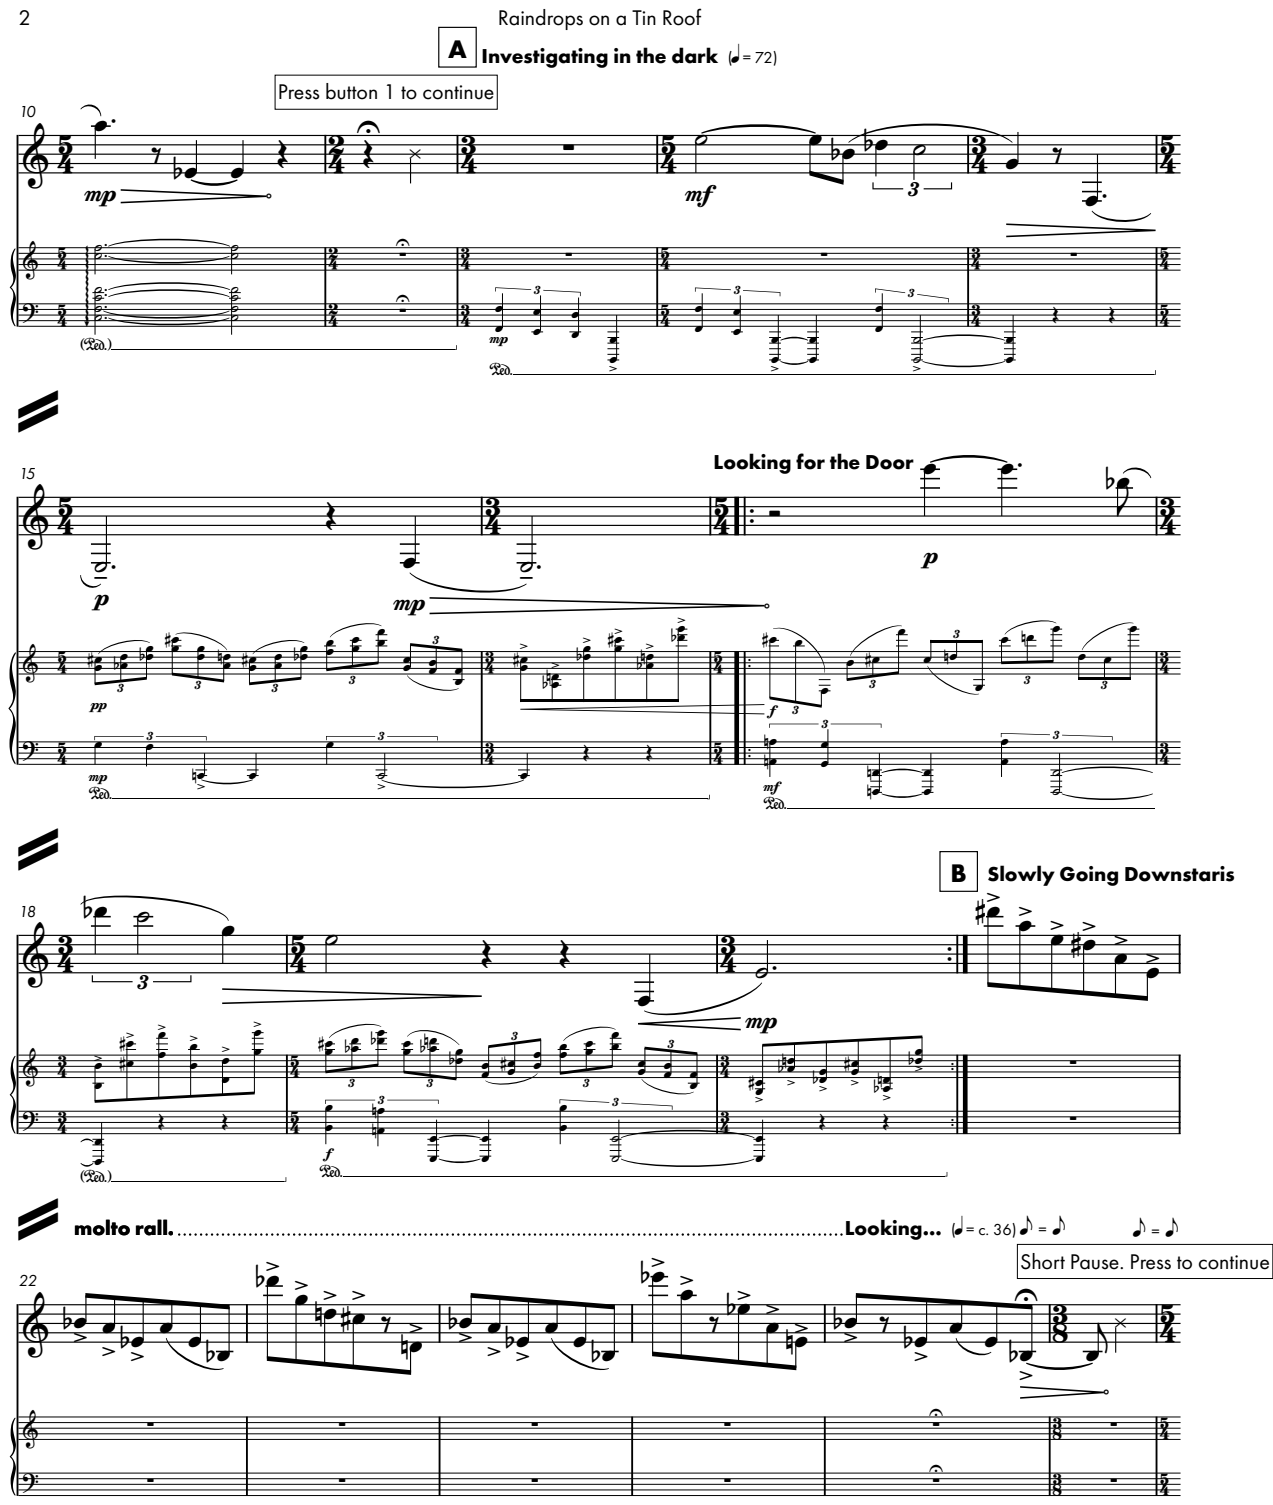
[picture p248: page 2]

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

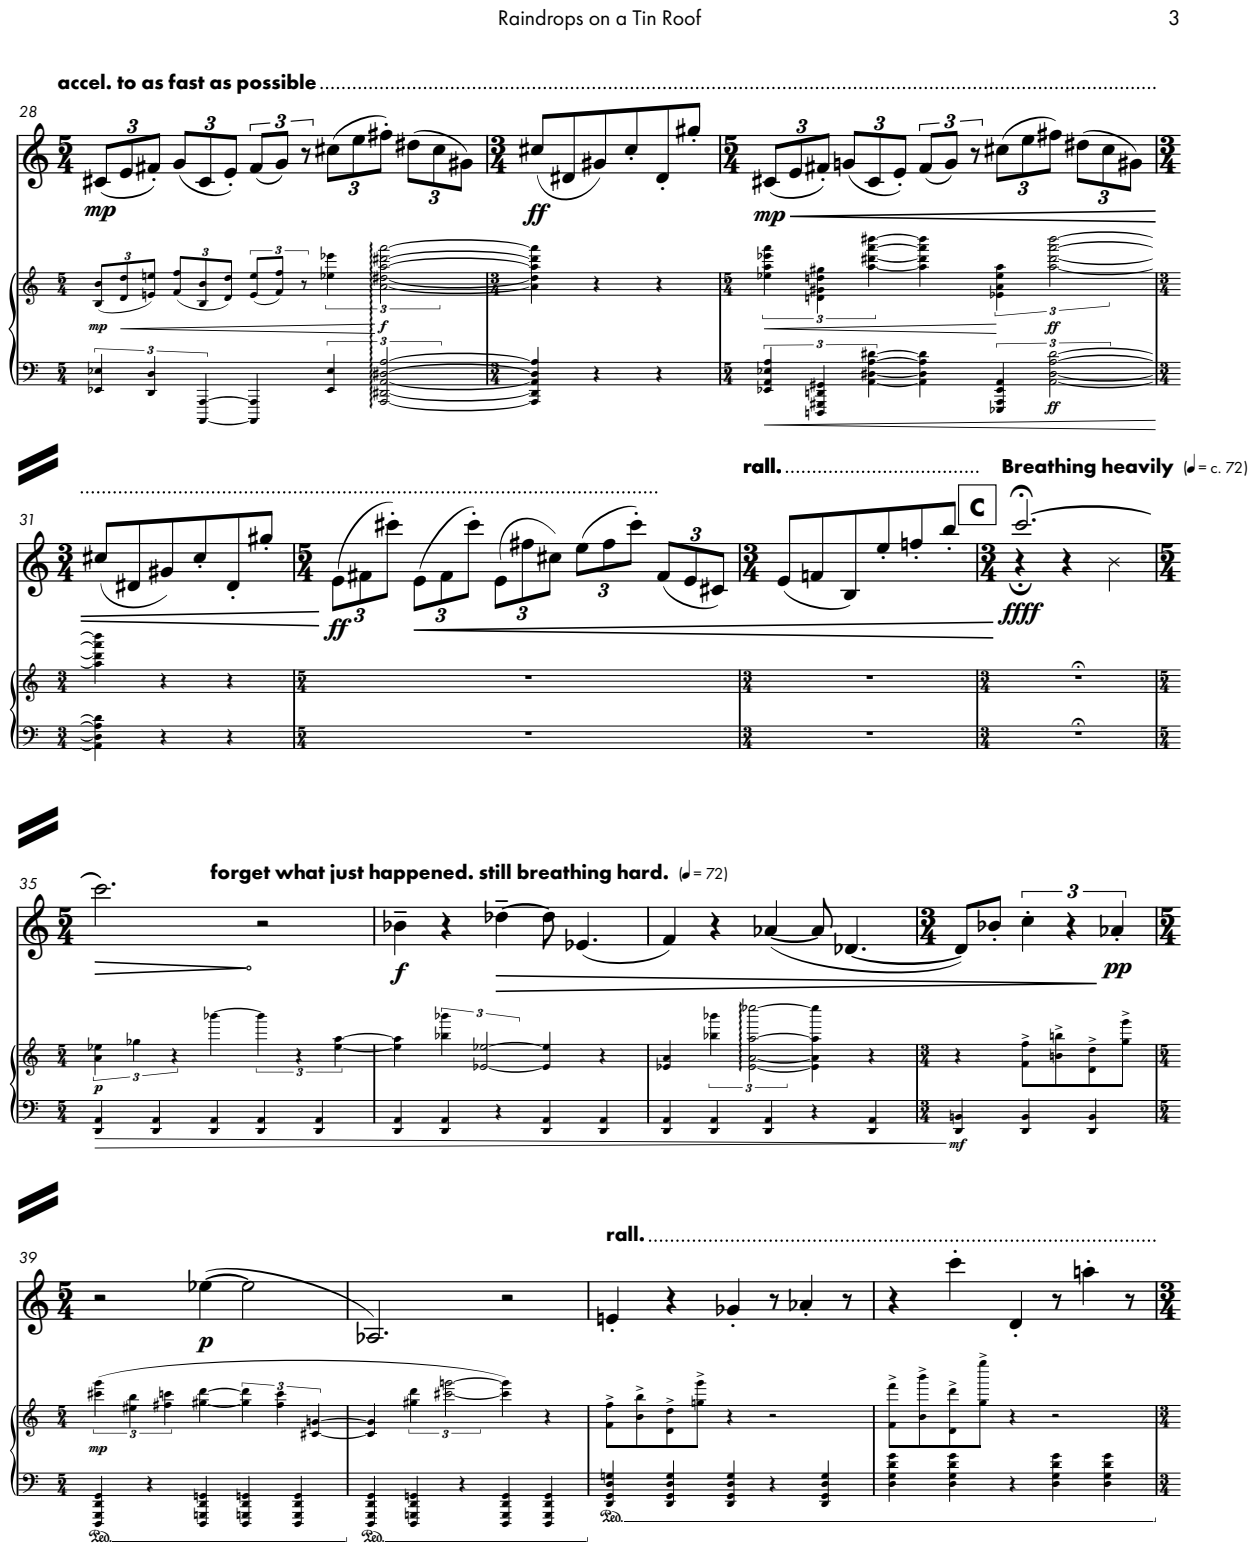
[picture p249: page 3]

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

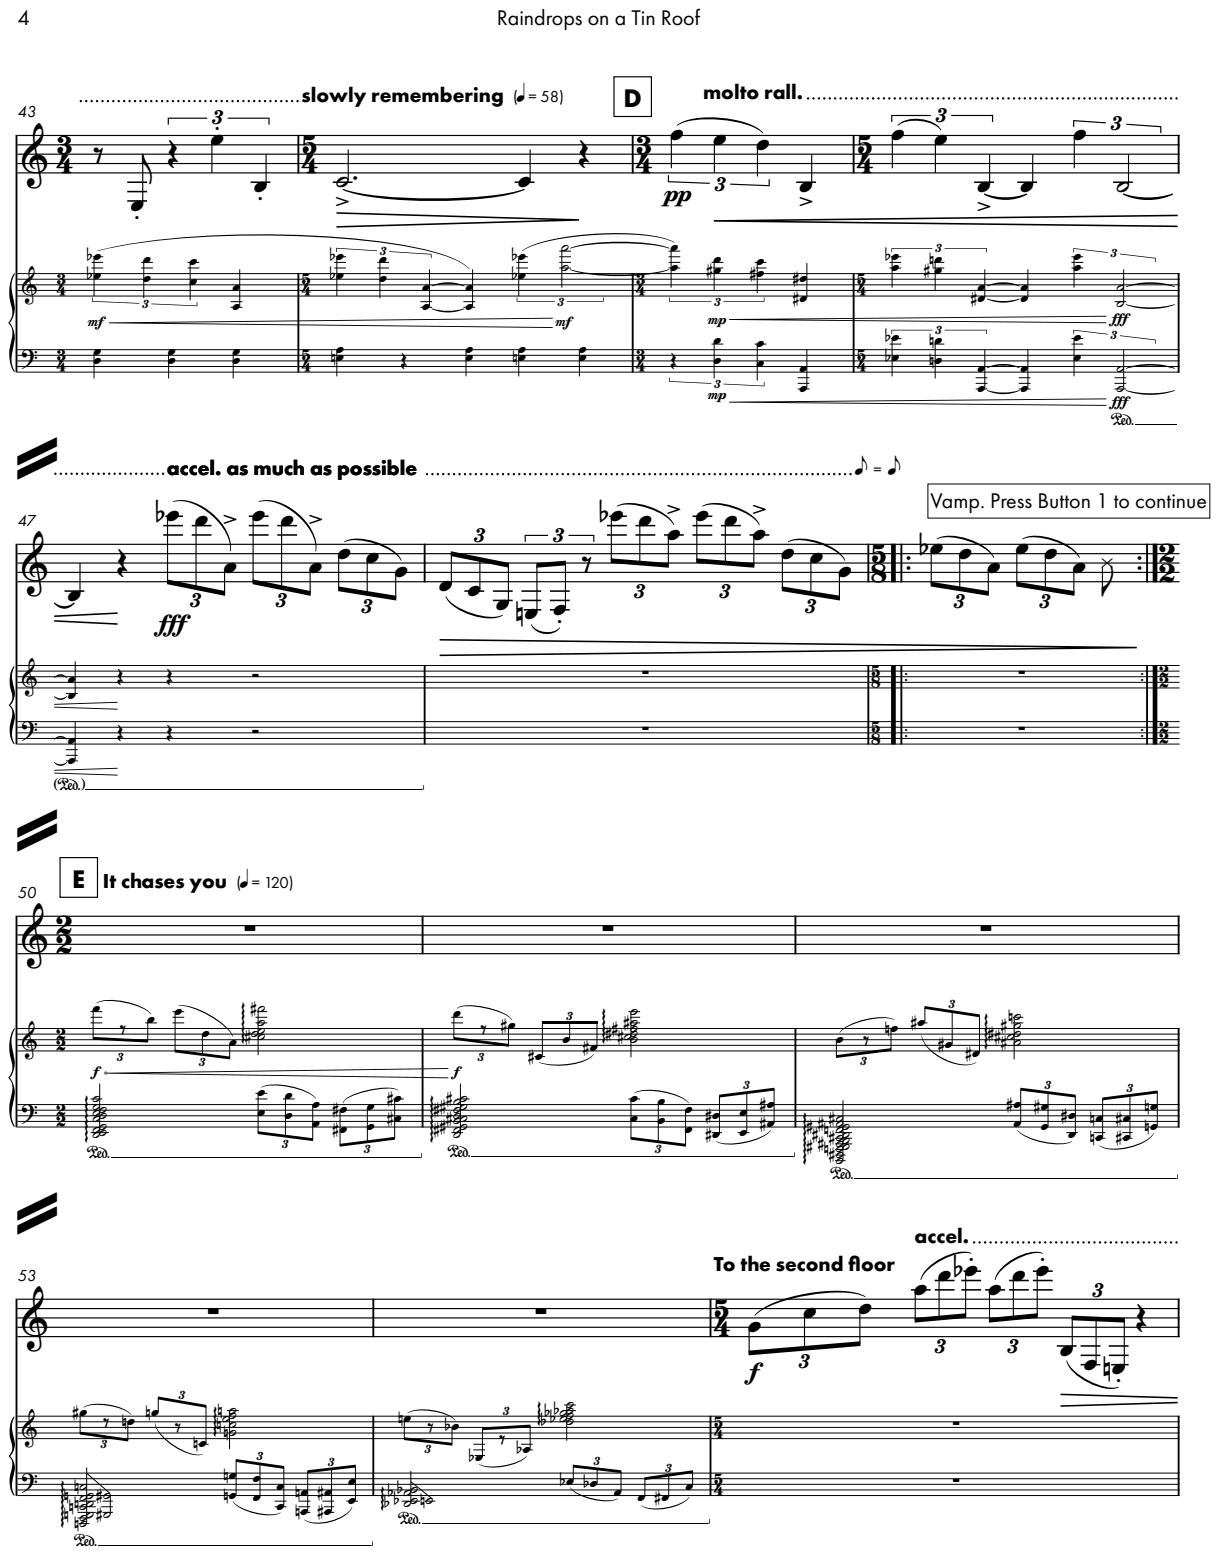
[picture p250: page 4]

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

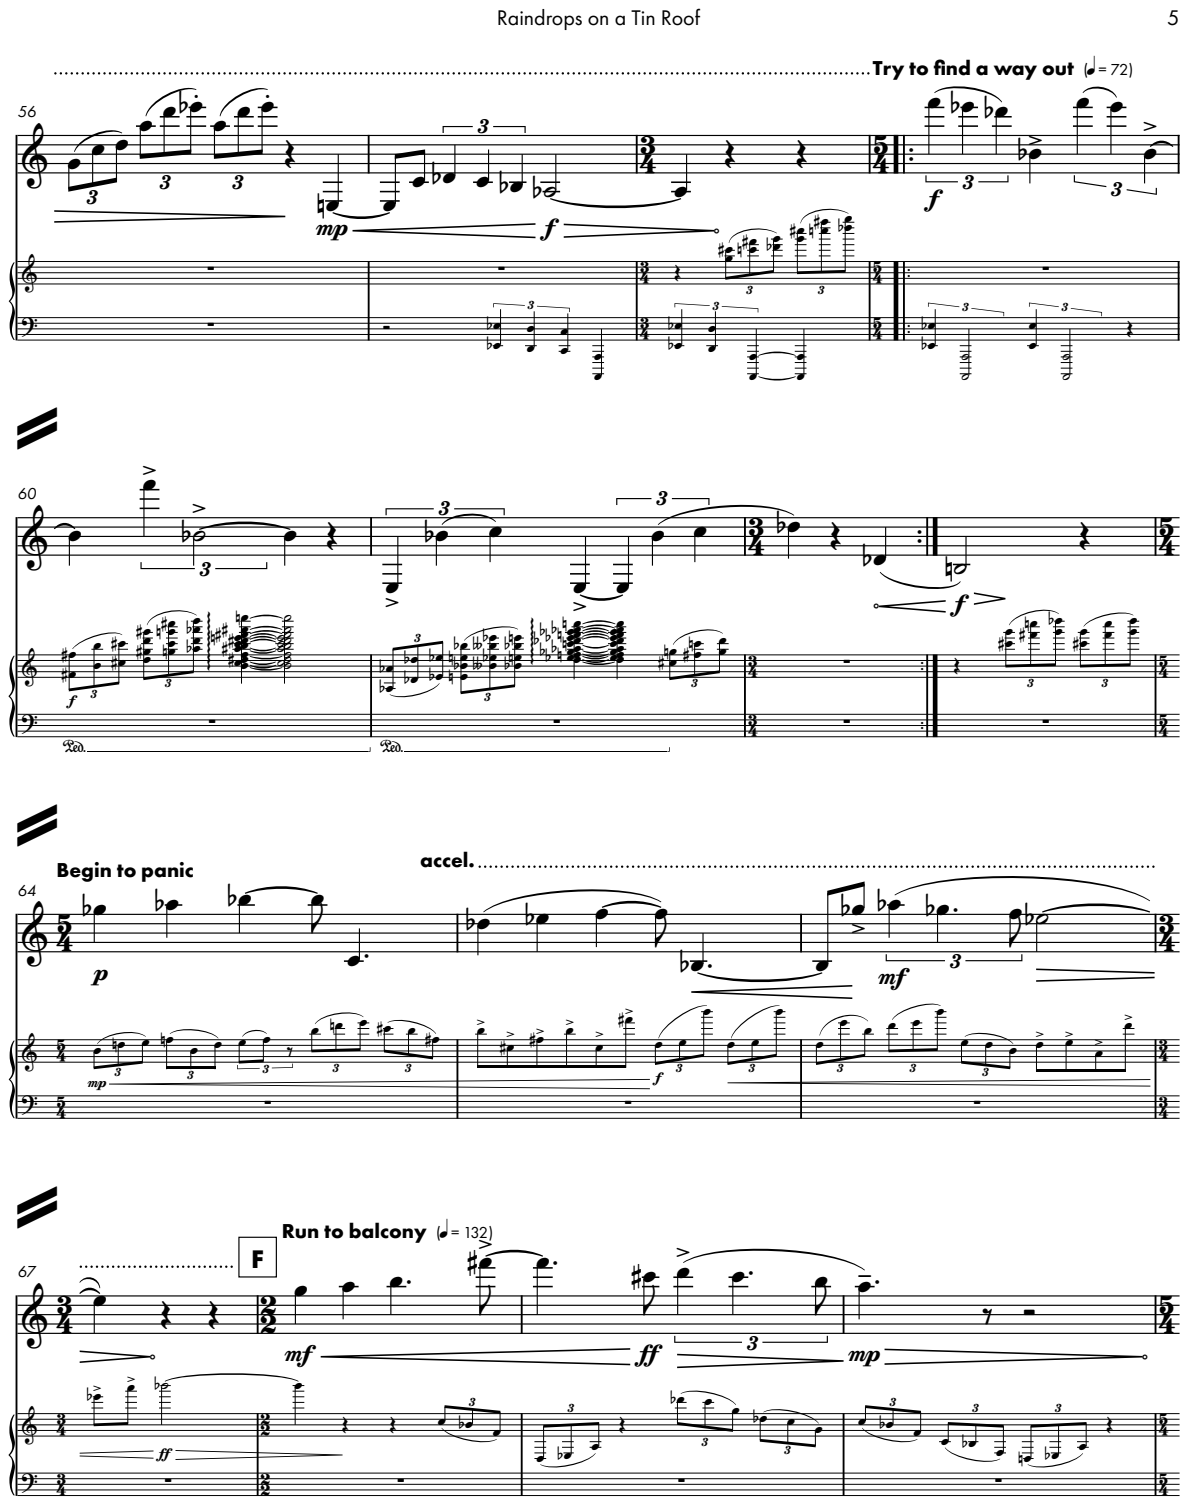
[picture p251: page 5]

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

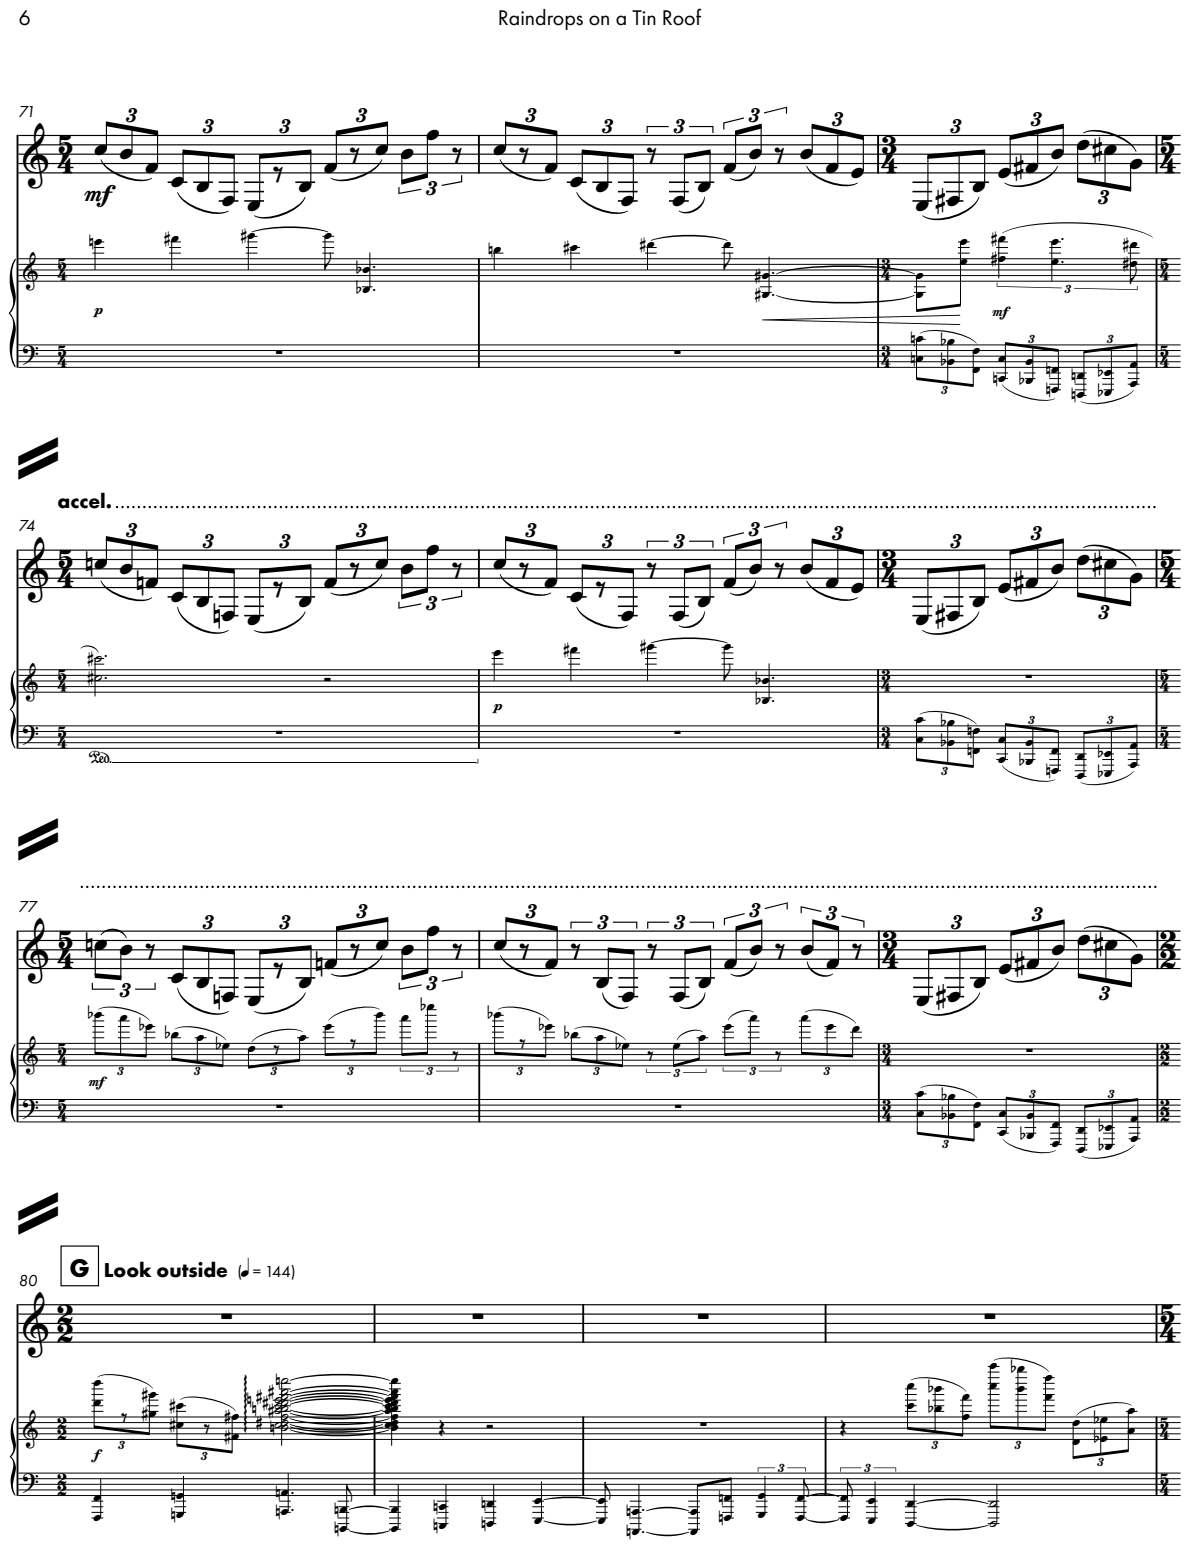
[picture p252: page 6]

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

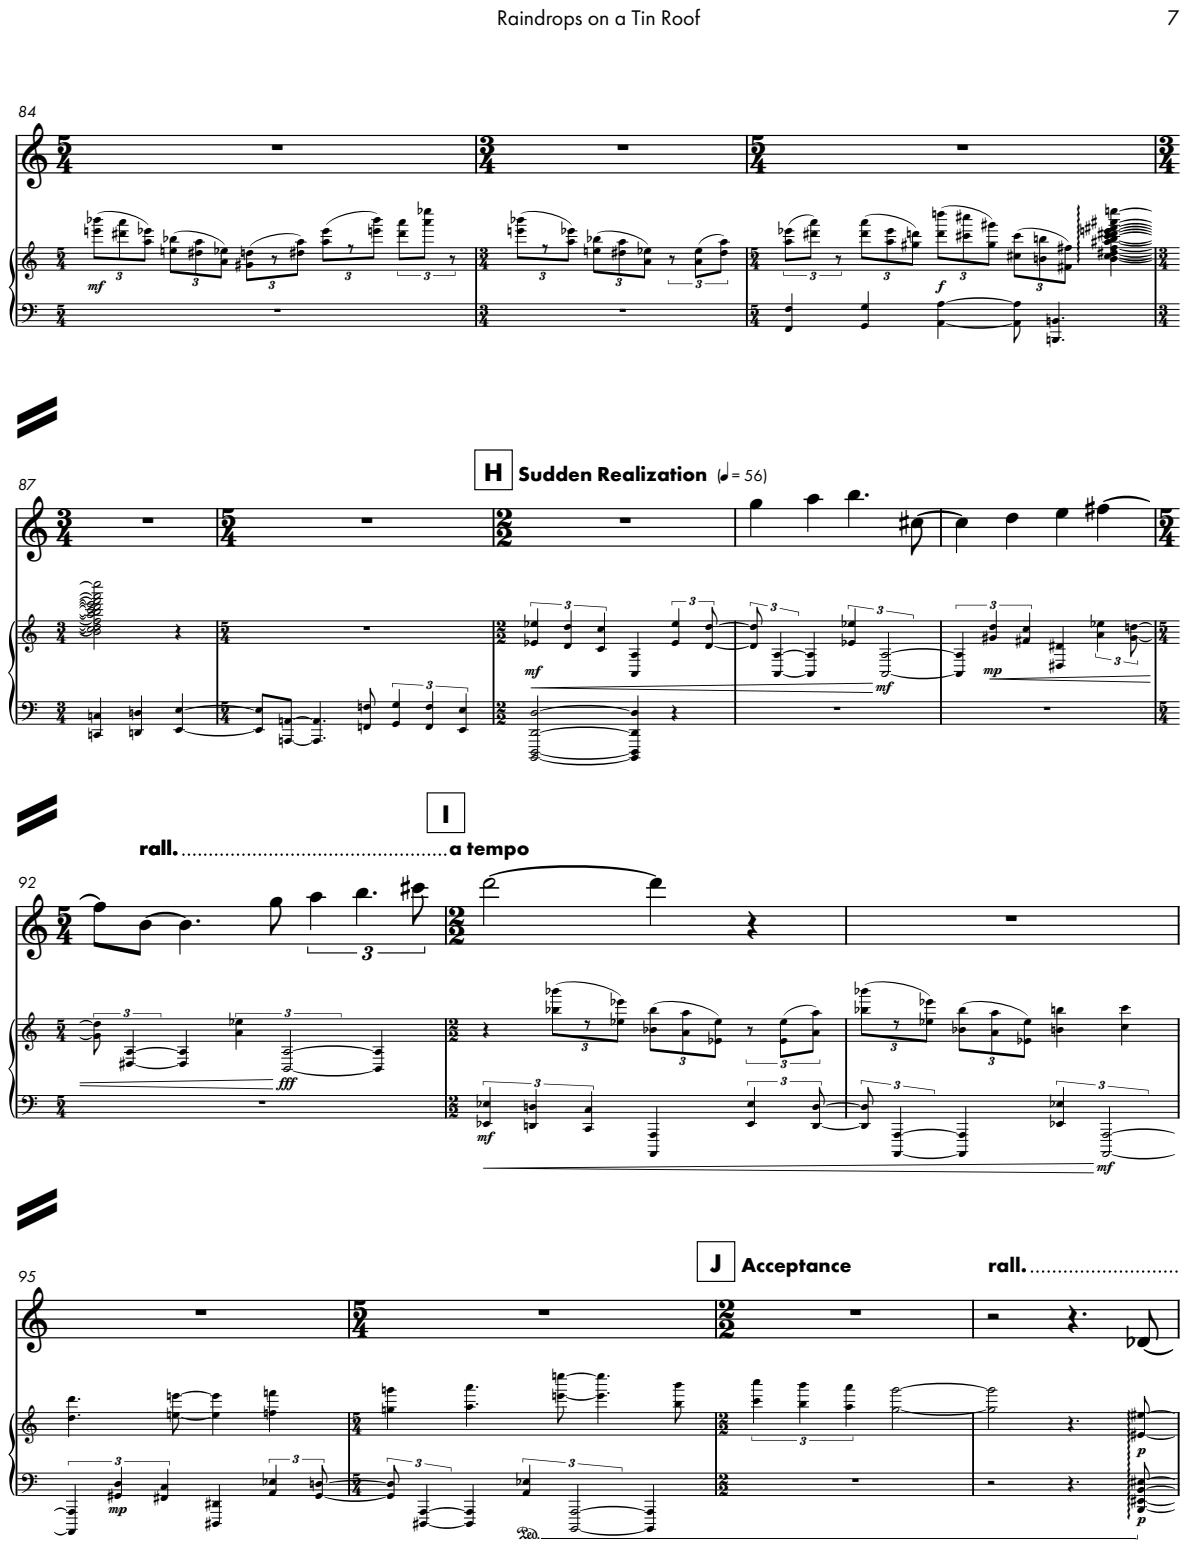
[picture p253: page 7]

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

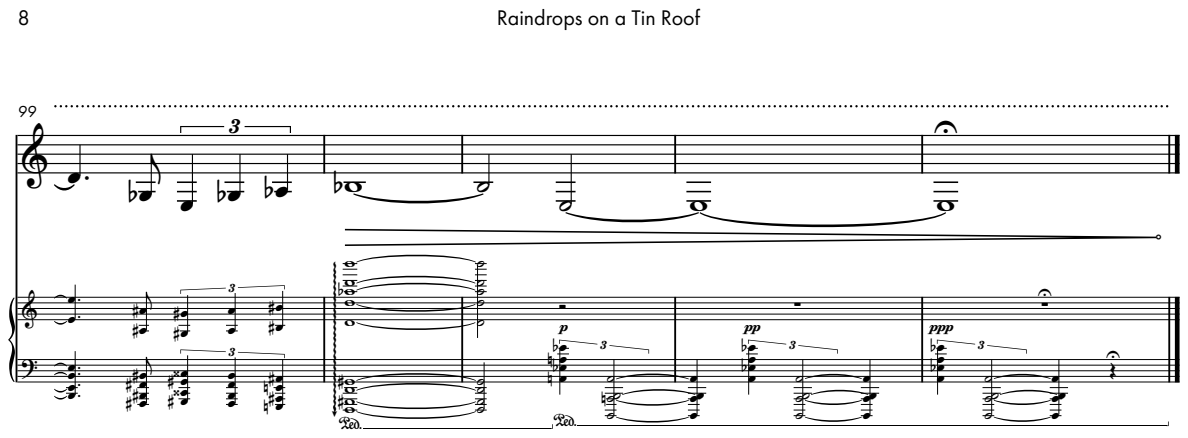
[picture p254: page 8]
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
