mbardin/Cyberinet/zMusic Composition Scores/scores/materials/raindrops/planning diagrams/raindrops - 2023-02-21.pdf

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

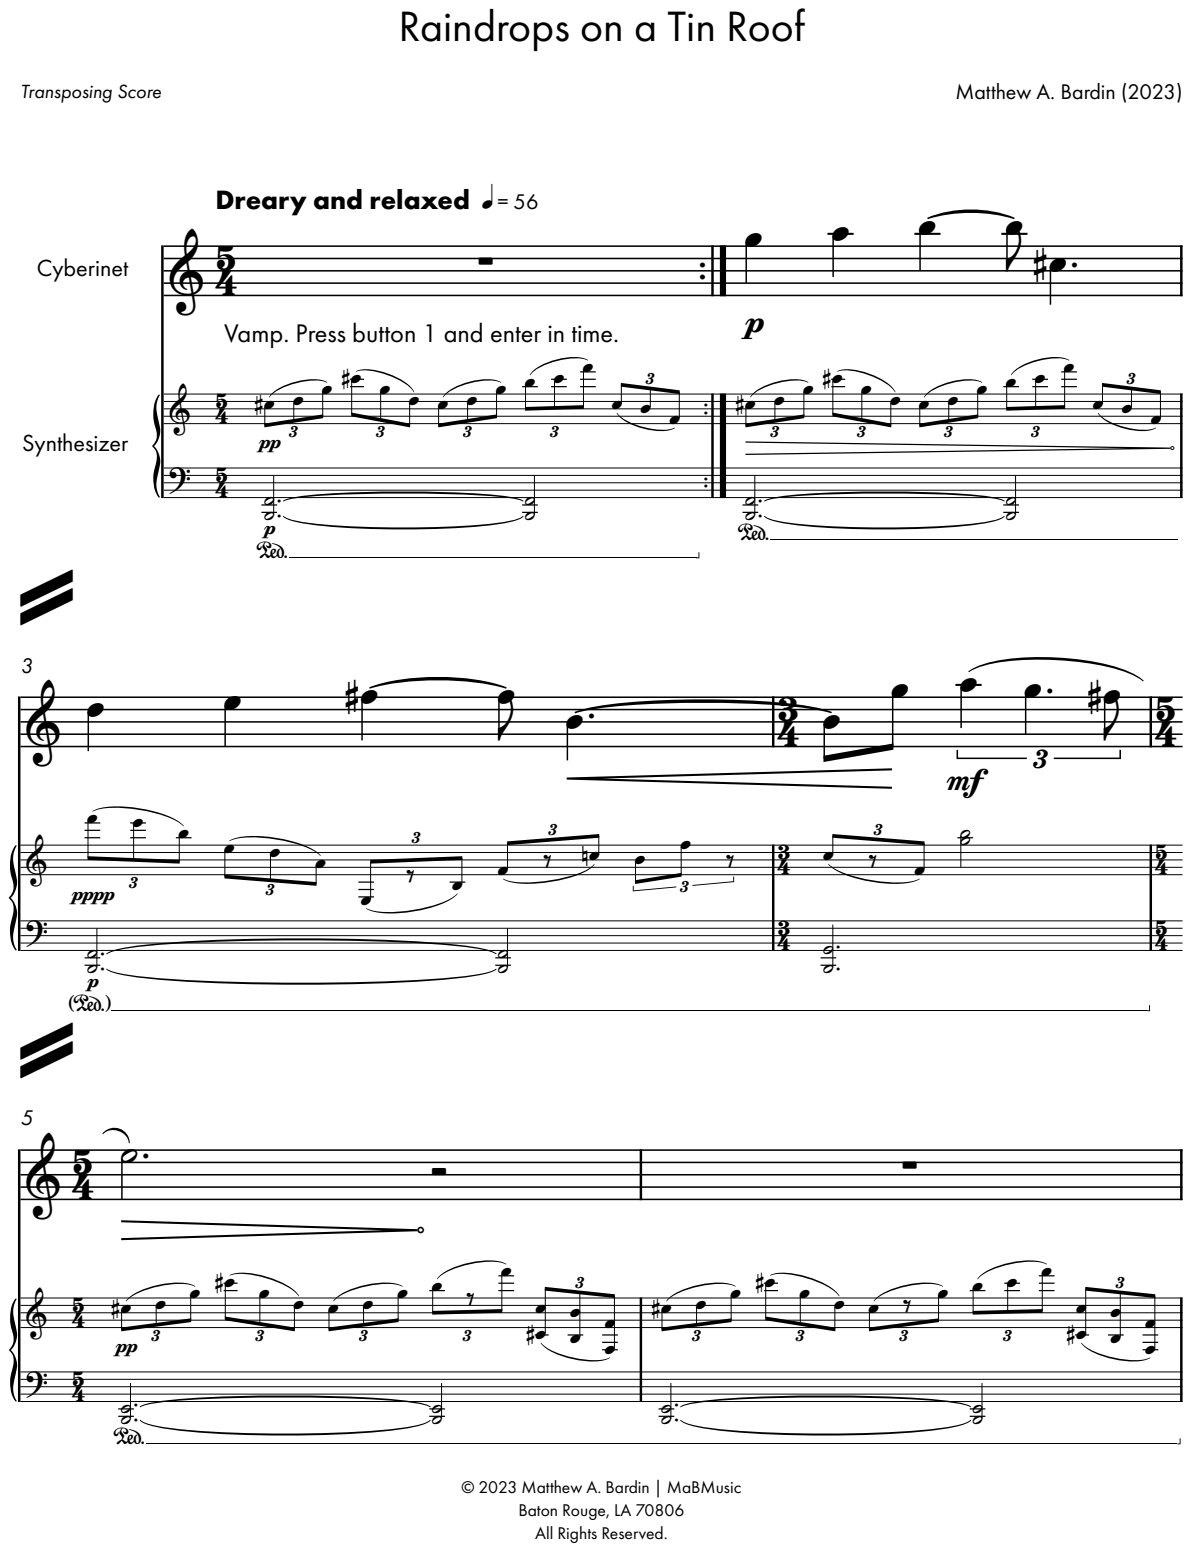
[picture p255: page 1]

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

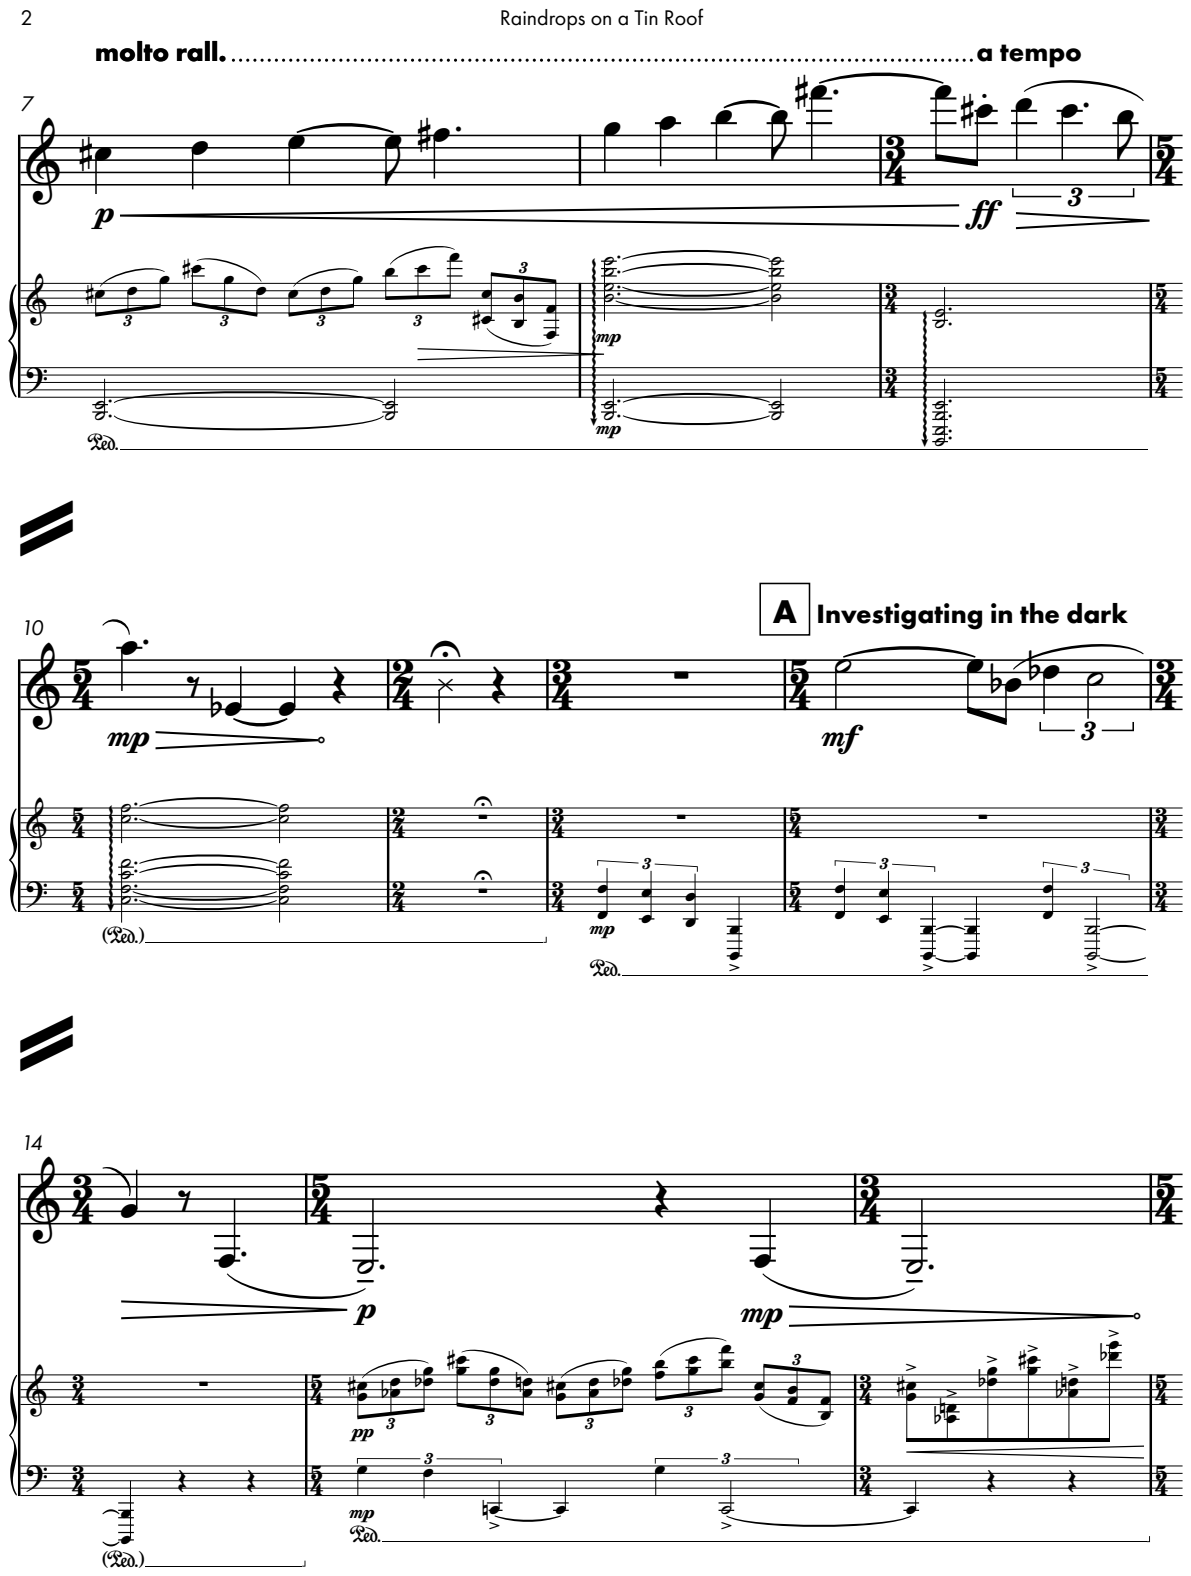
[picture p256: page 2]

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

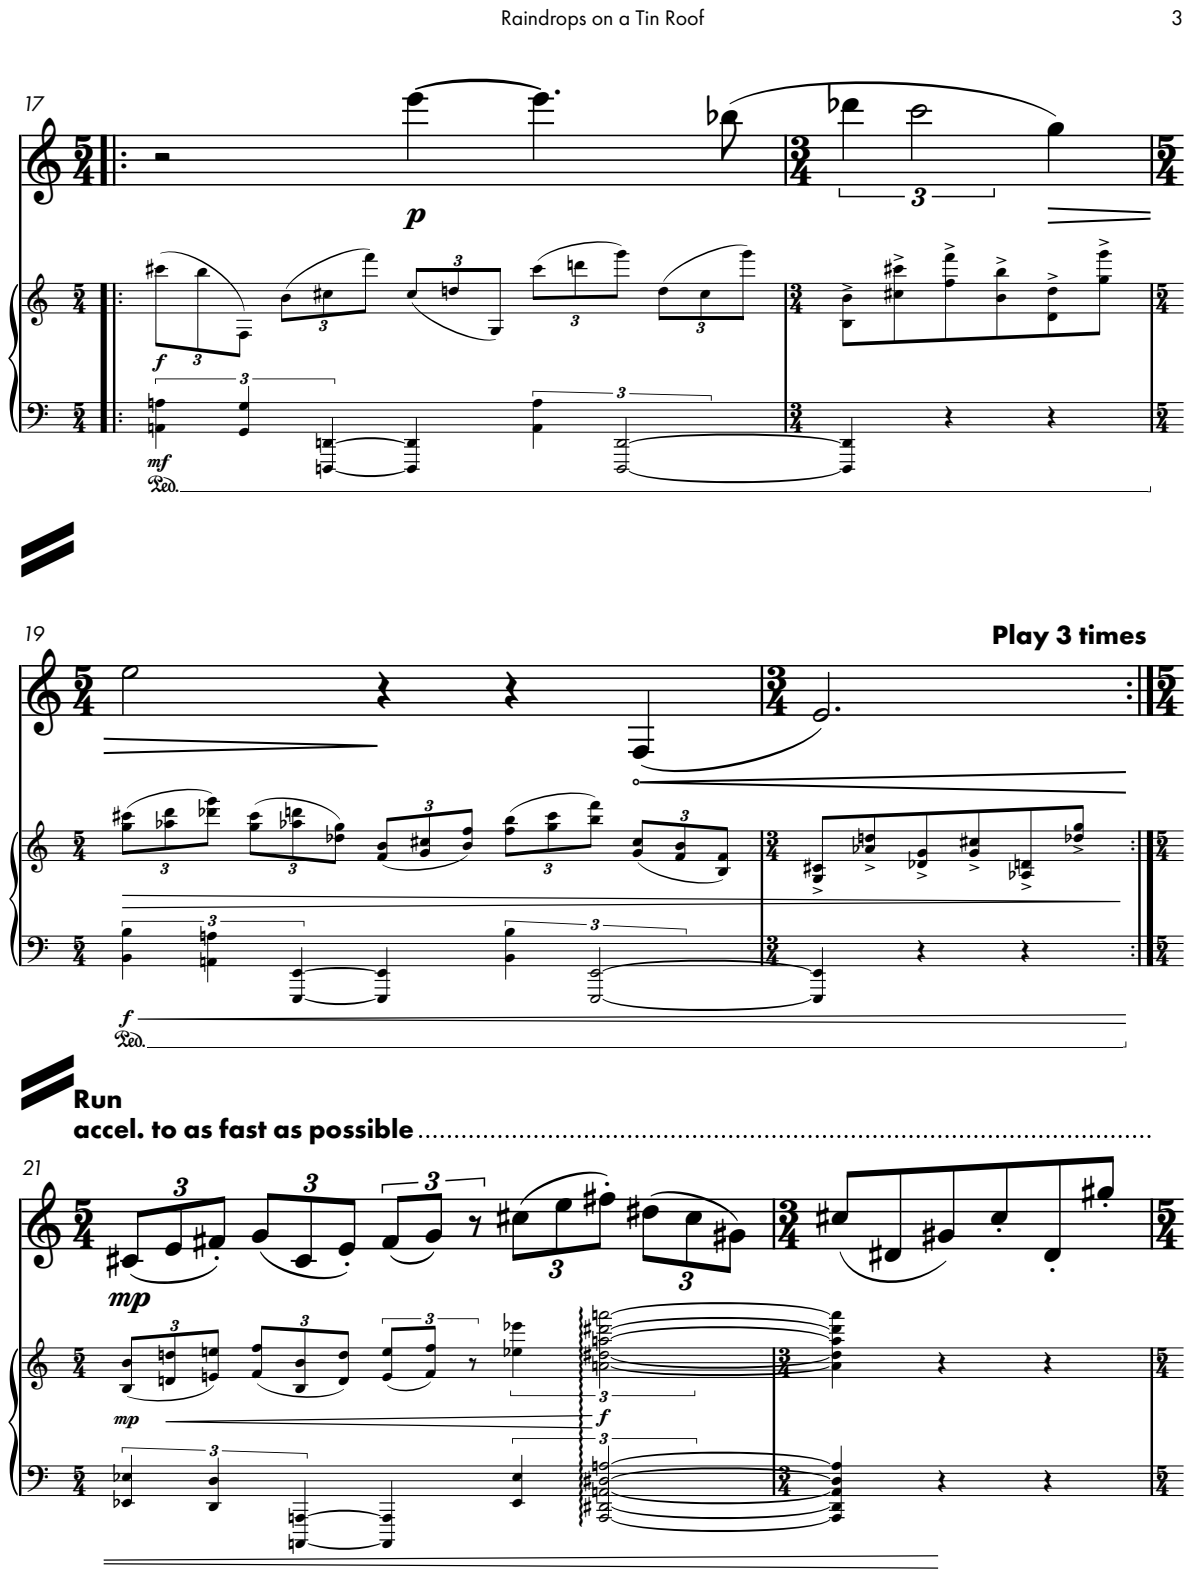
[picture p257: page 3]

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

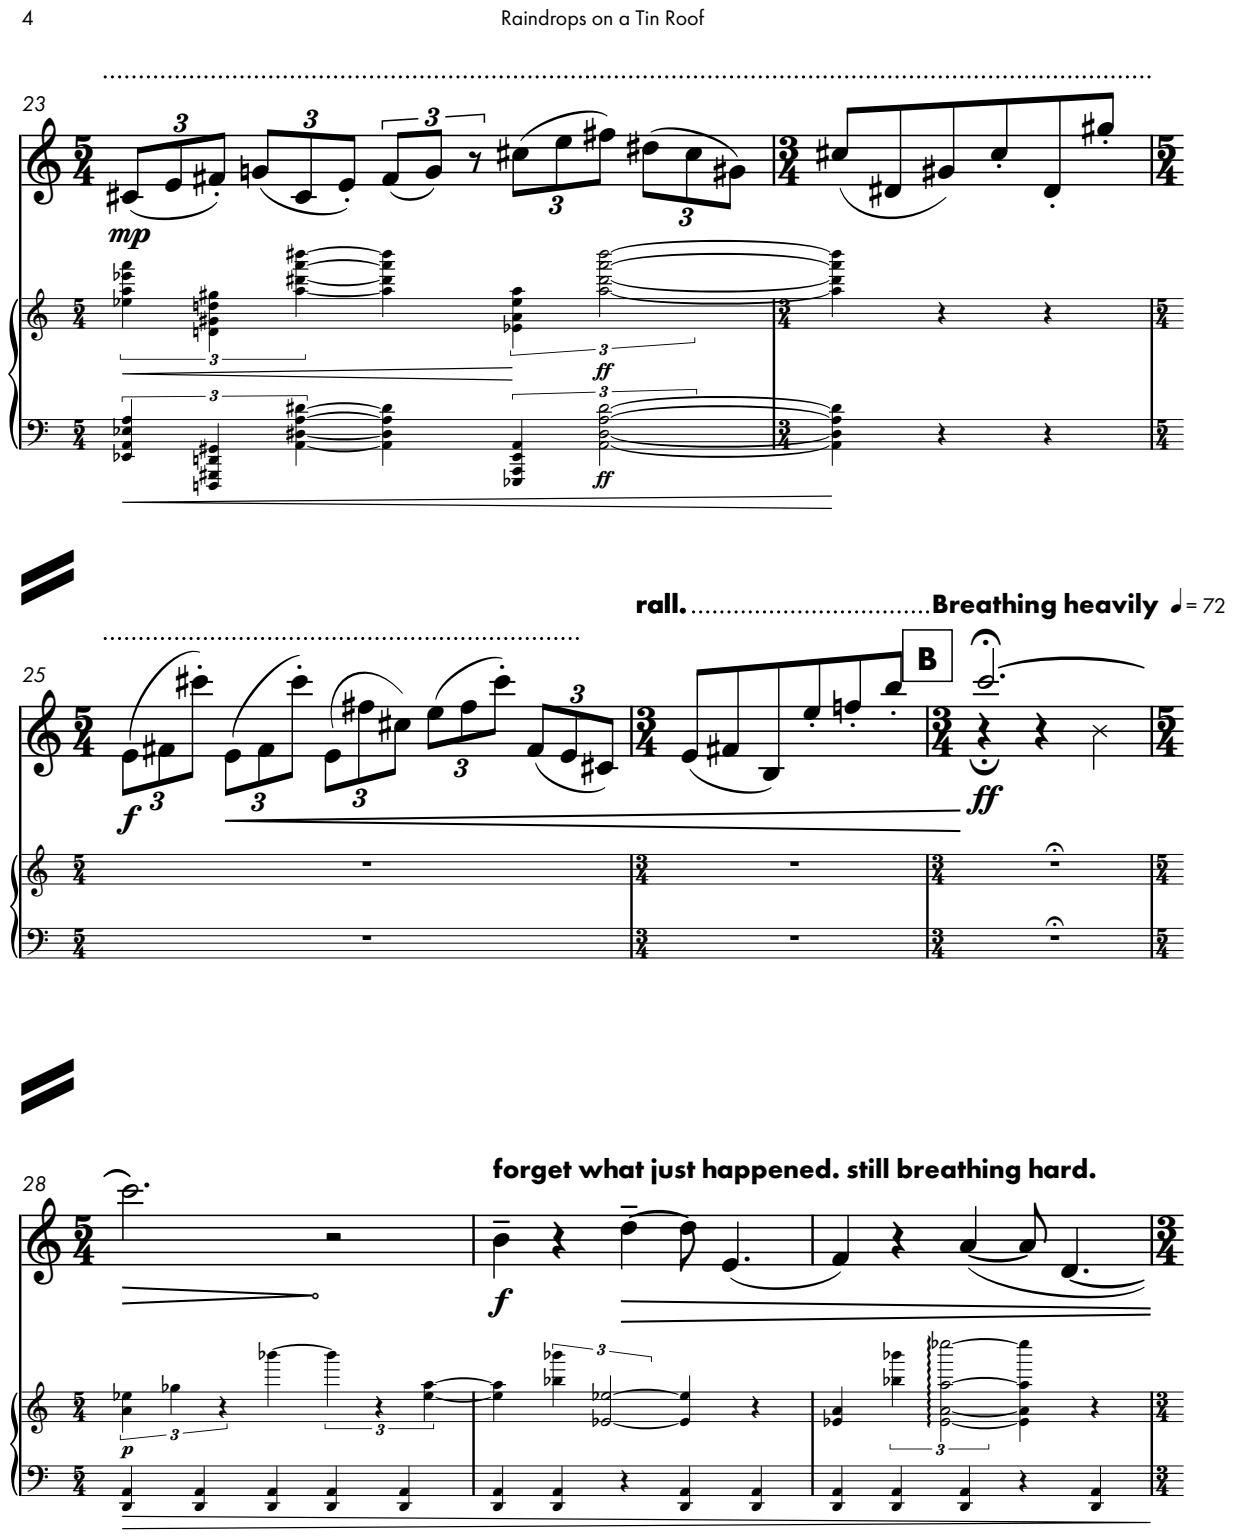
[picture p258: page 4]

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

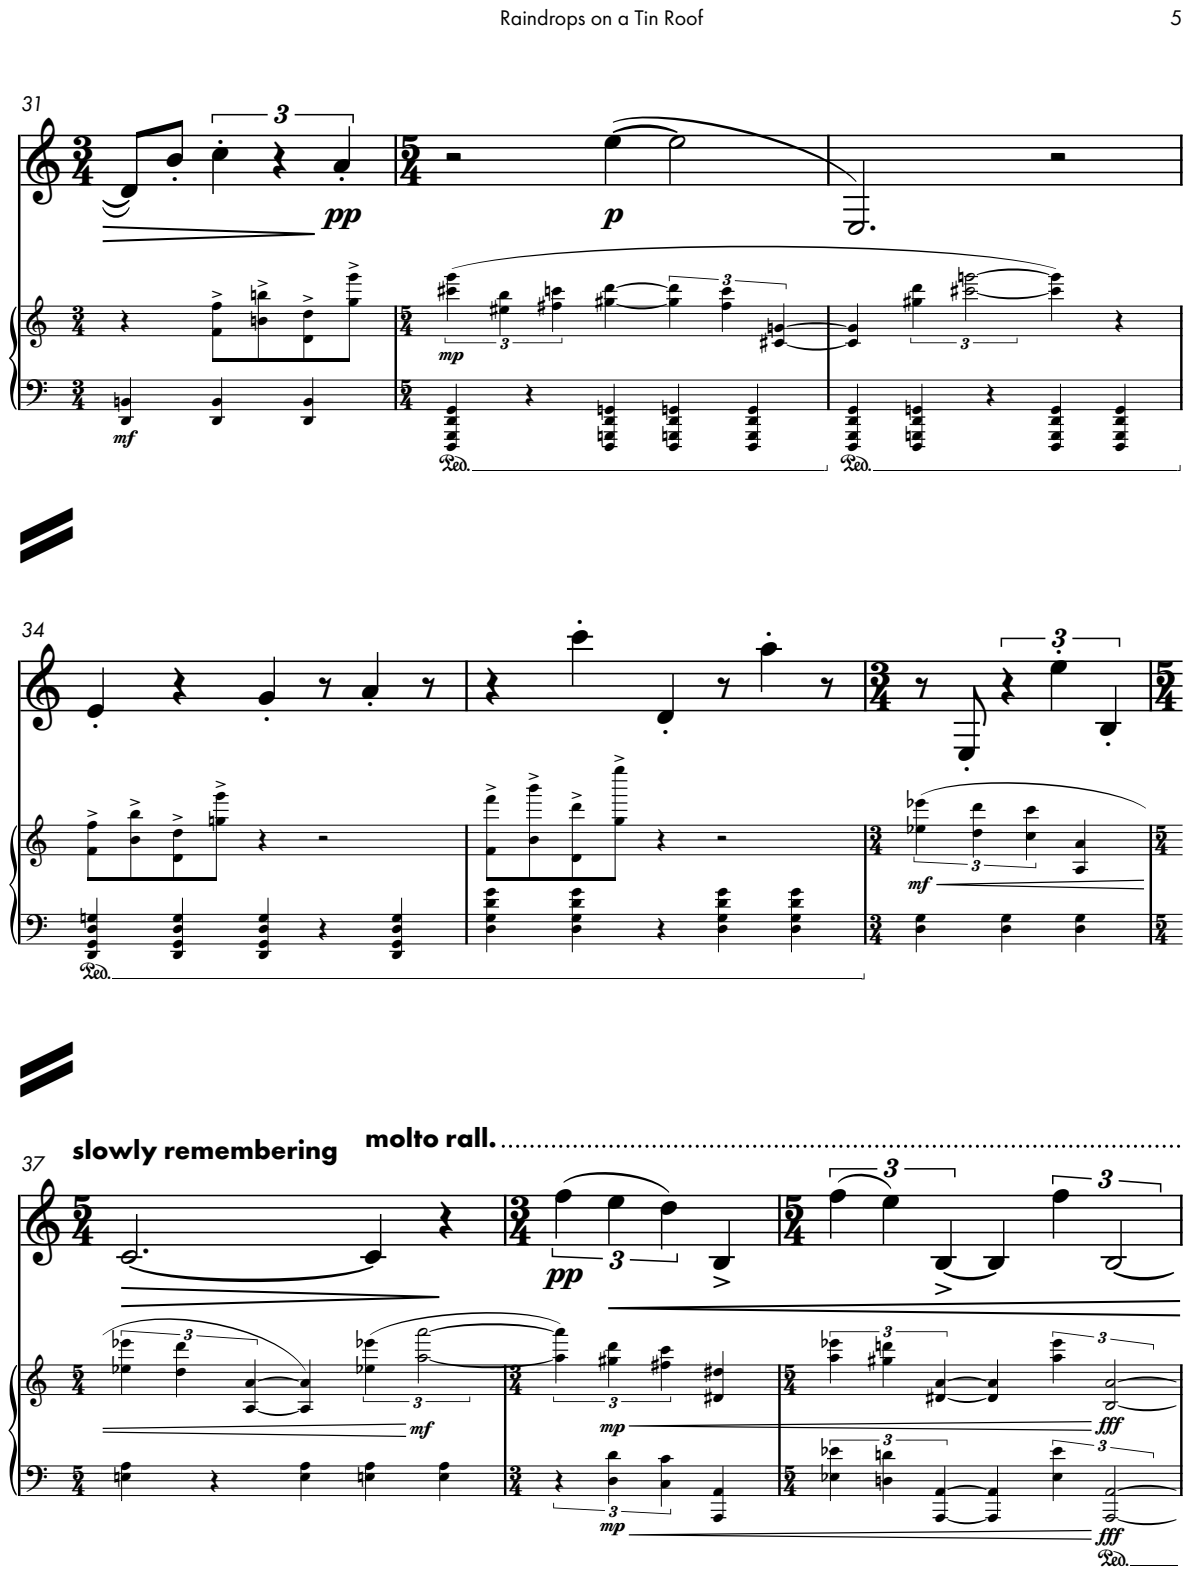
[picture p259: page 5]

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

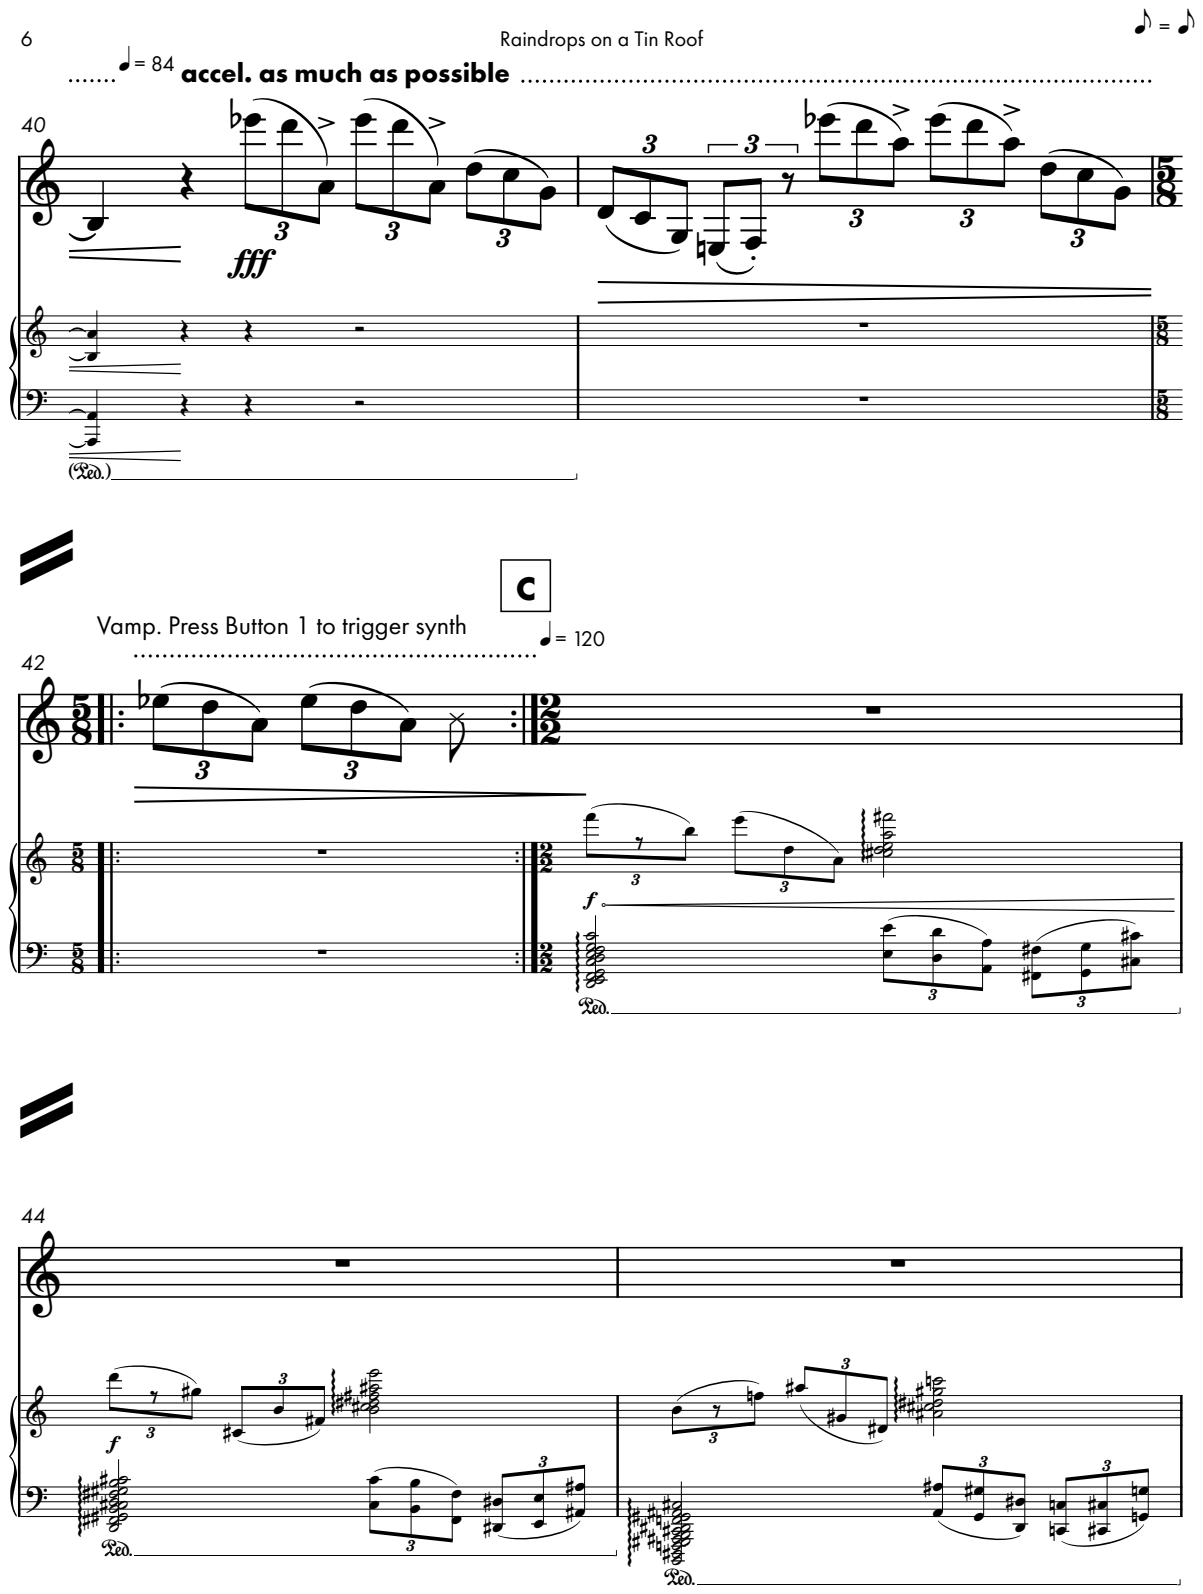
[picture p260: page 6]

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

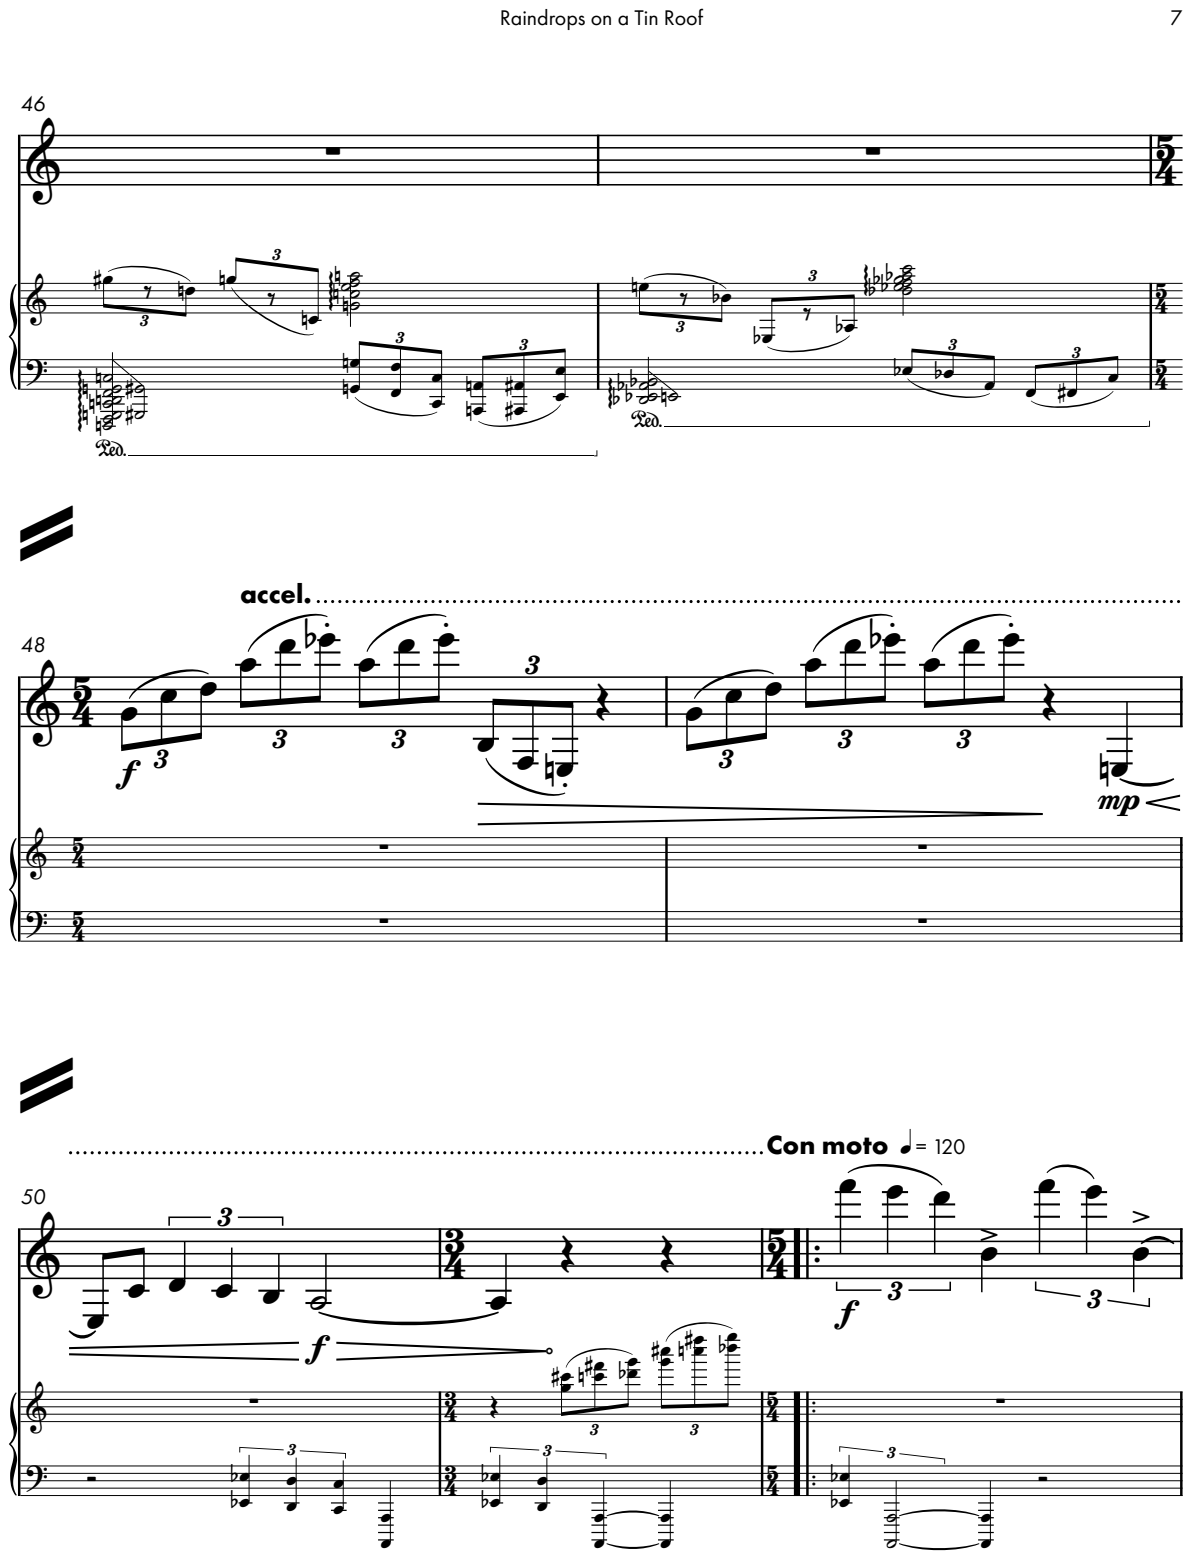
[picture p261: page 7]

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

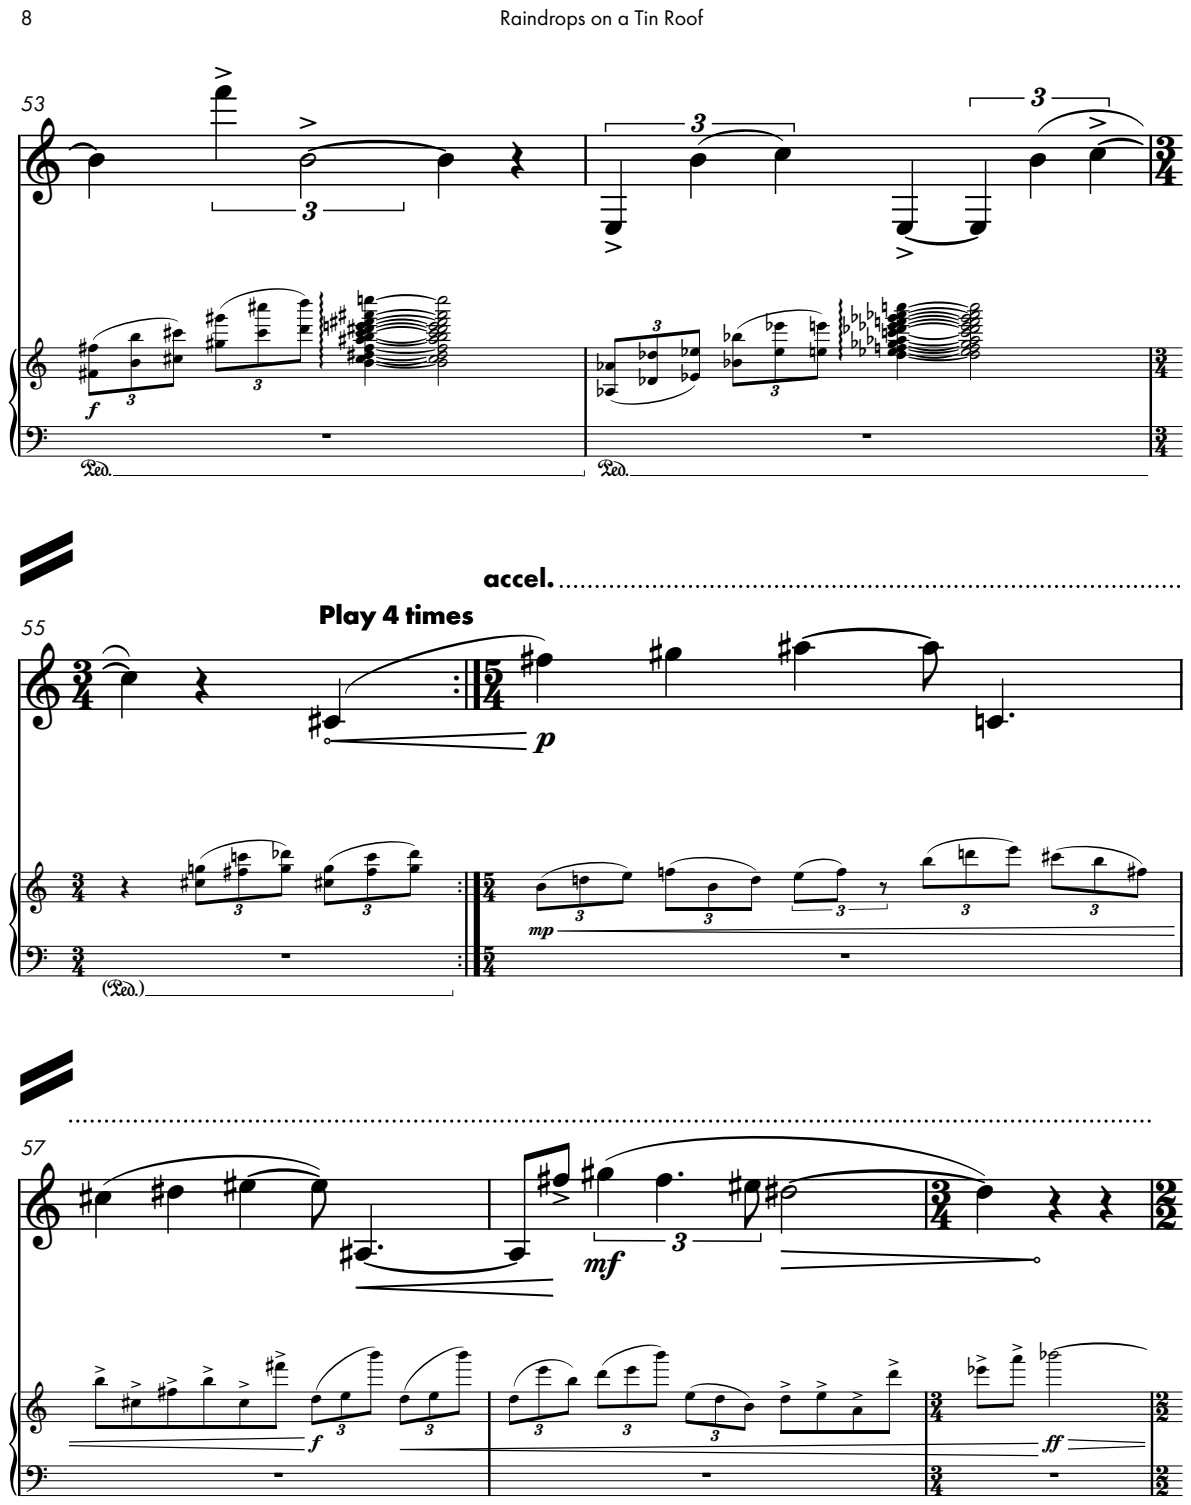
[picture p262: page 8]

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

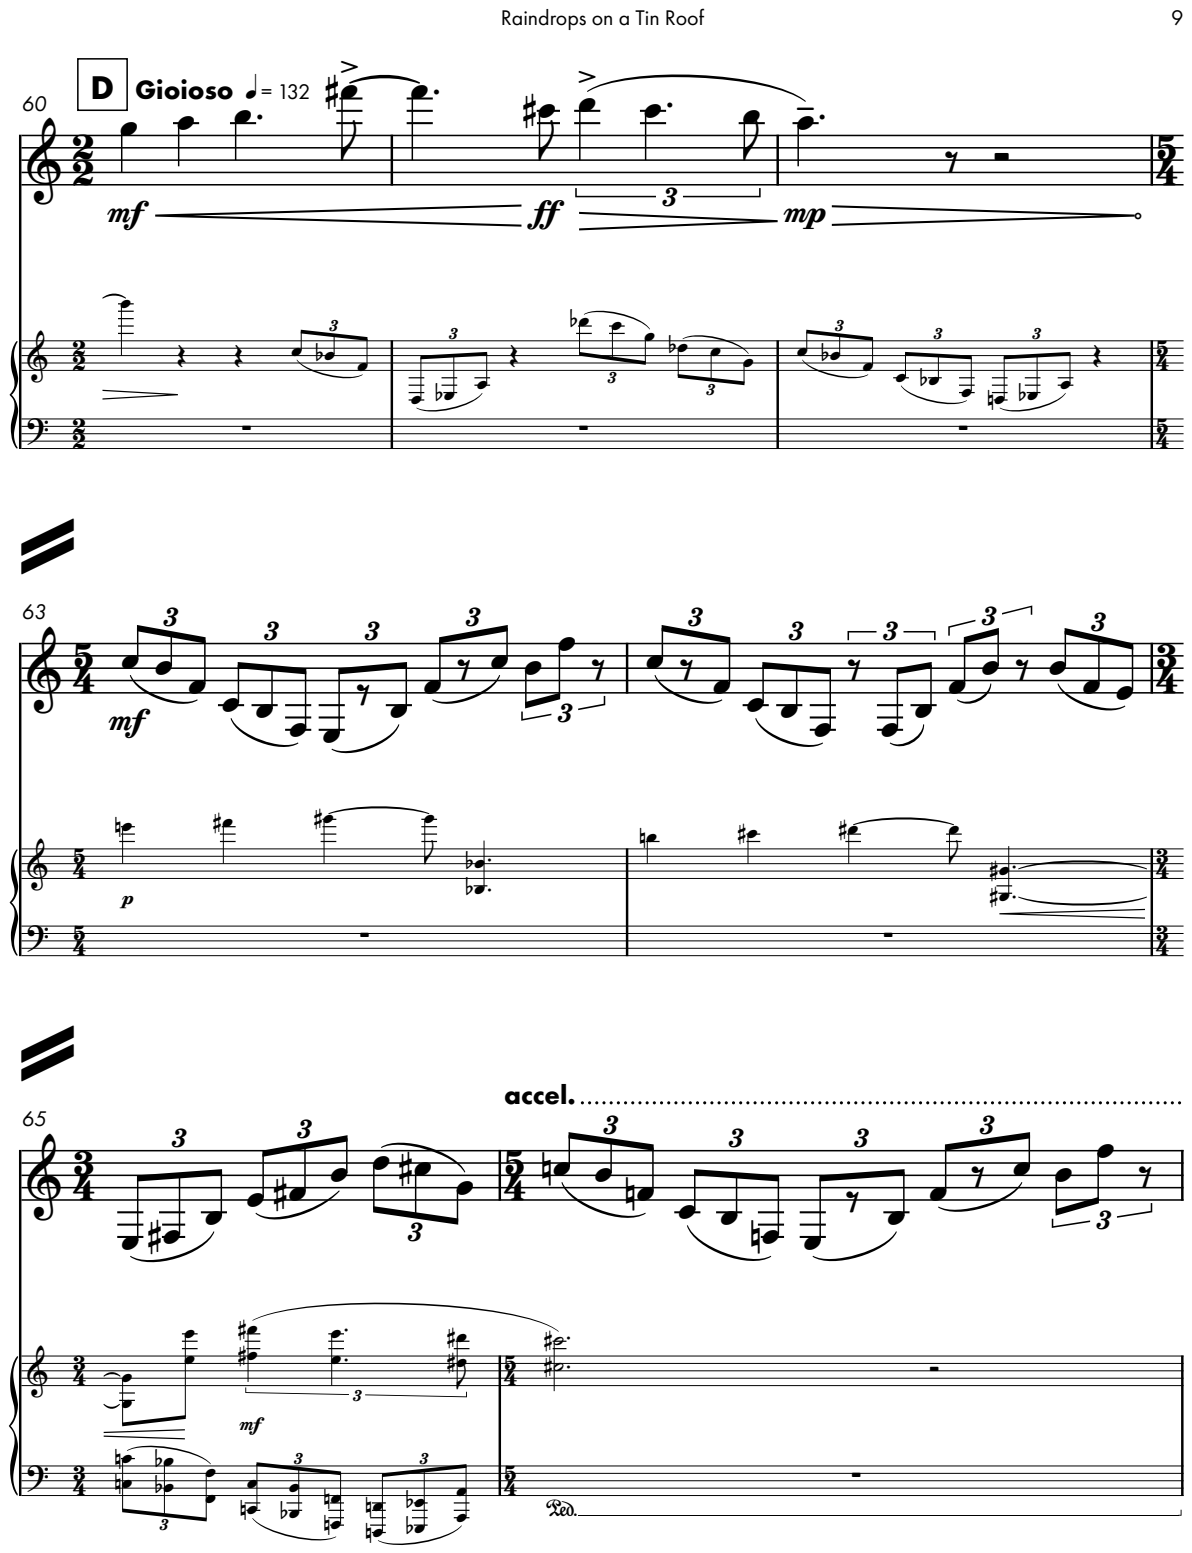
[picture p263: page 9]

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

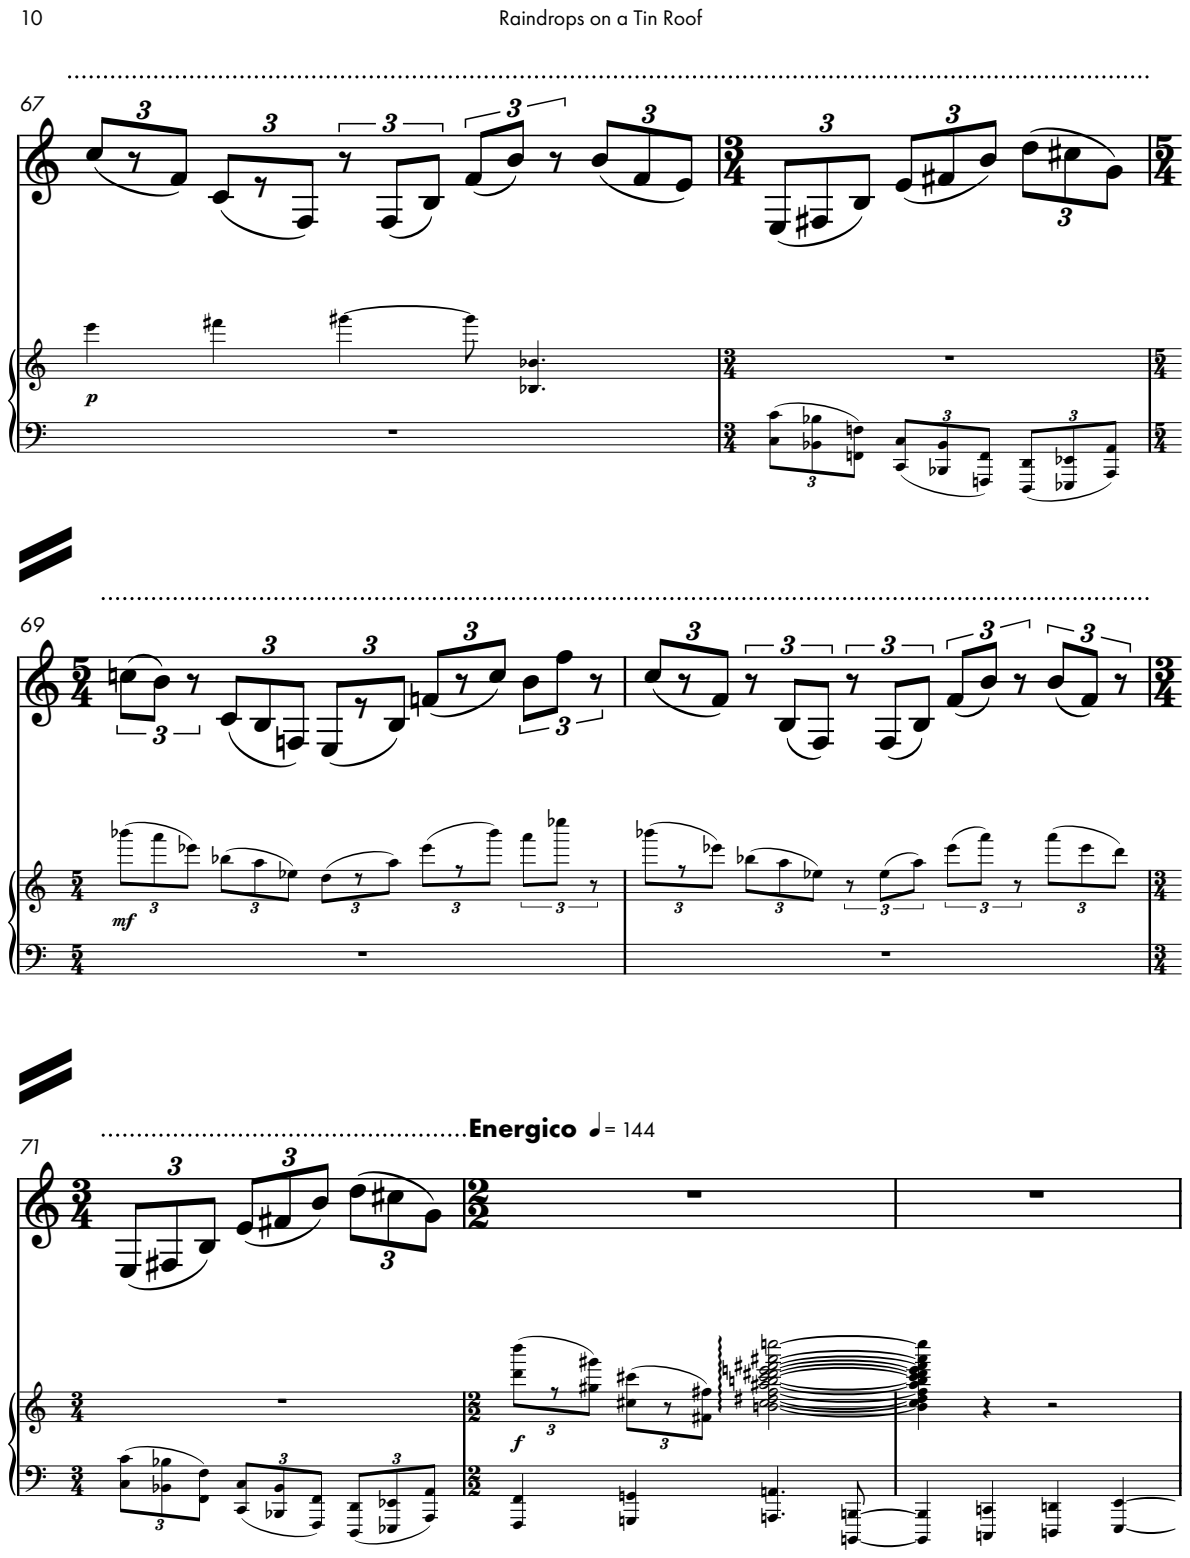
[picture p264: page 10]

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

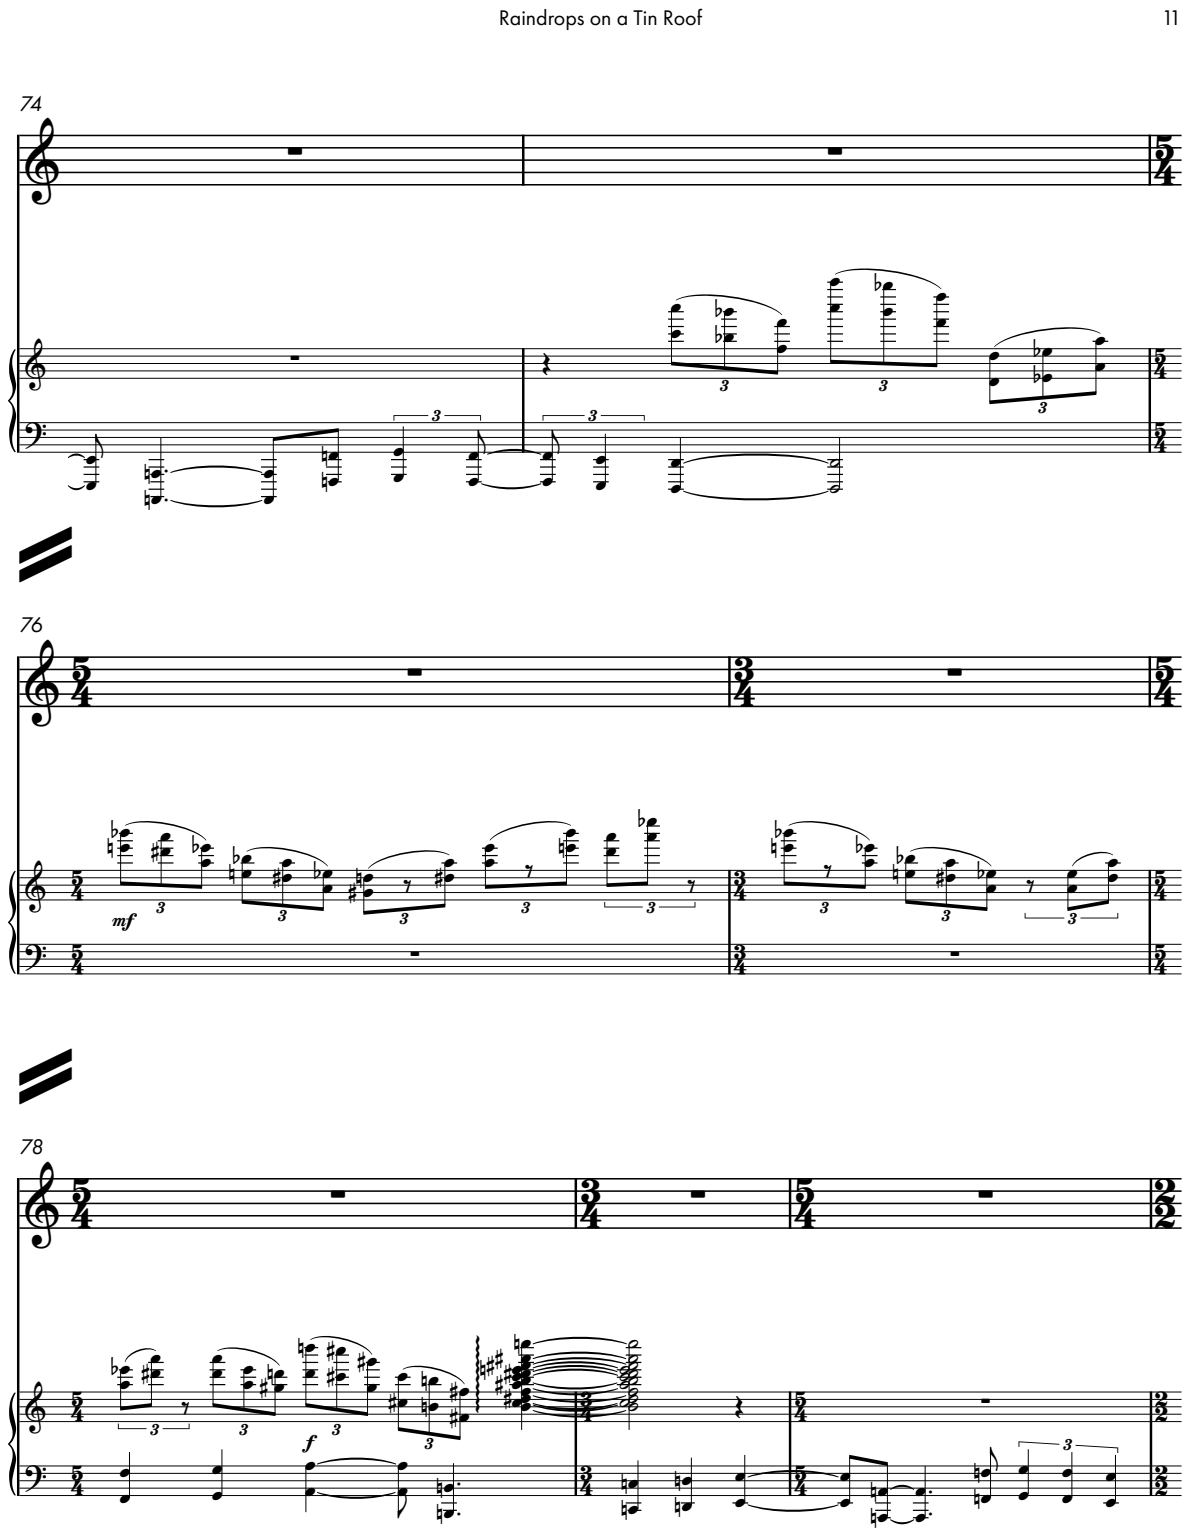
[picture p265: page 11]

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

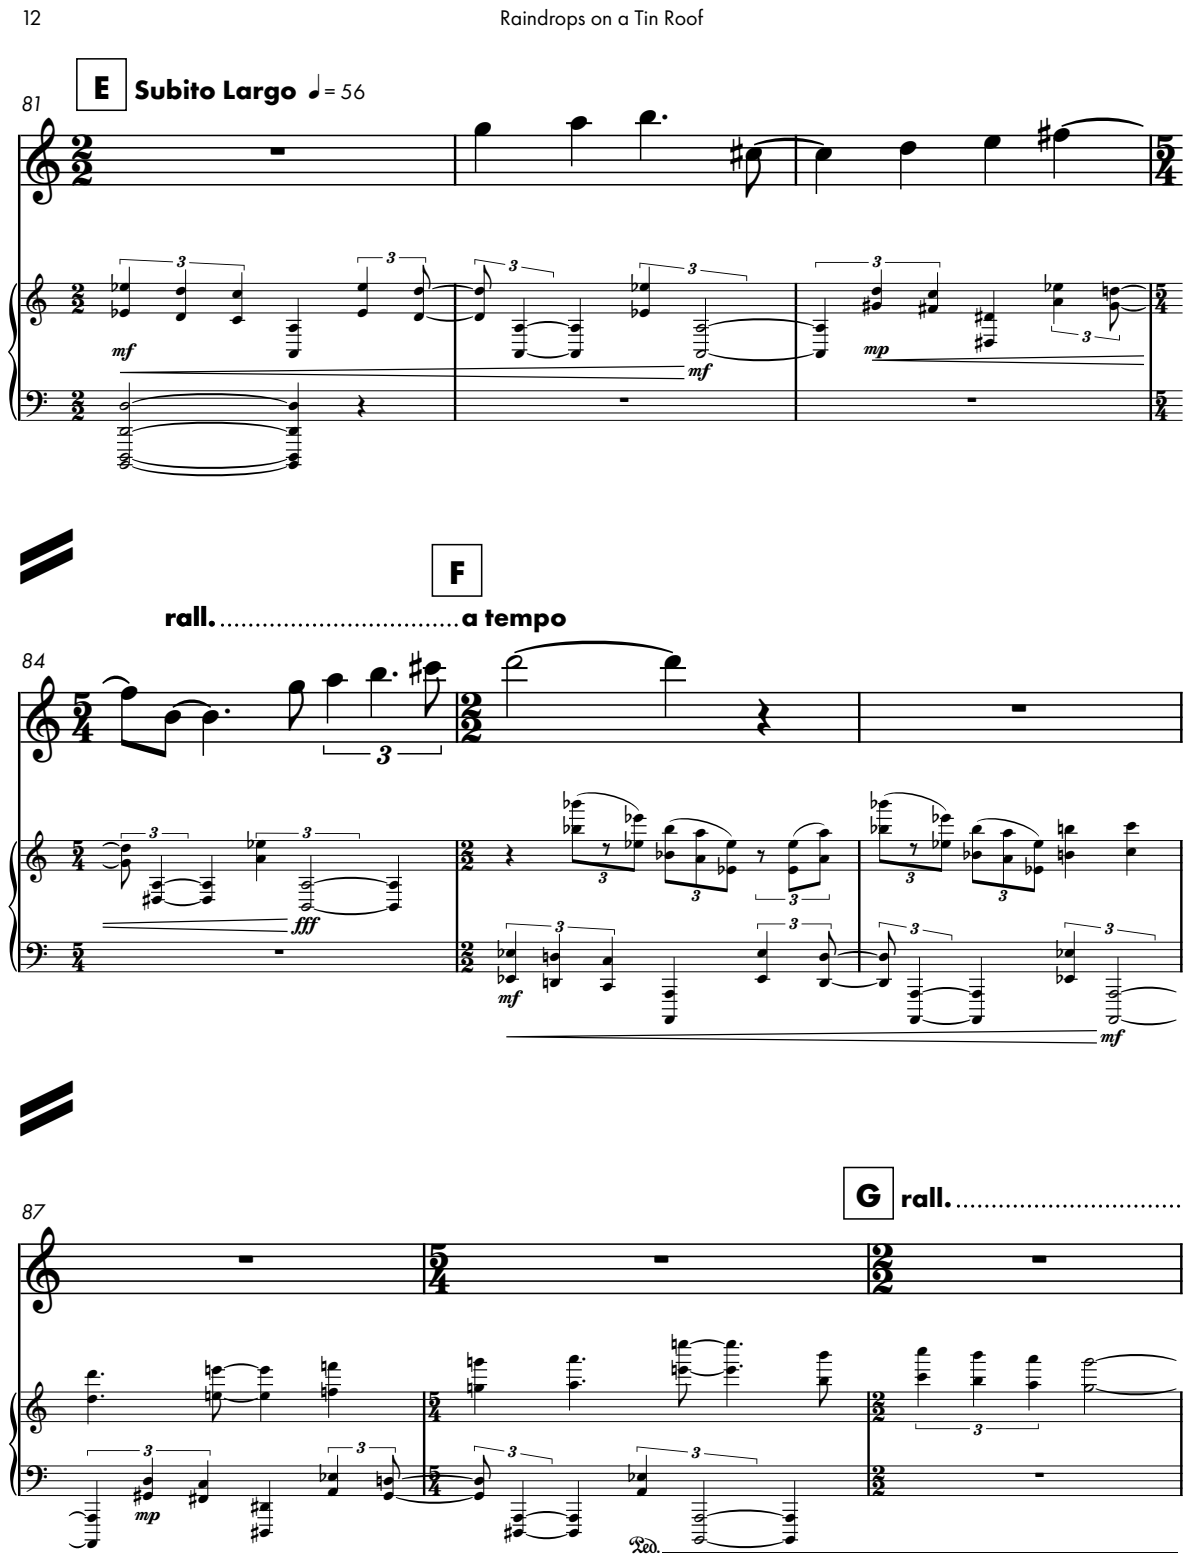
[picture p266: page 12]

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

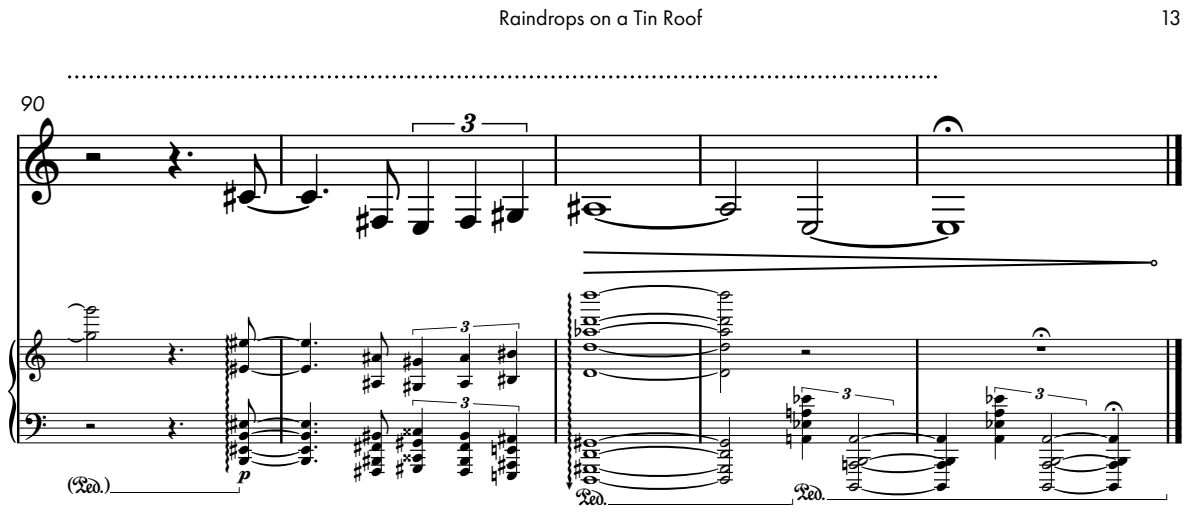
[picture p267: page 13]
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
