mbardin/Cyberinet/zMusic Composition Scores/scores/materials/raindrops/planning diagrams/raindrops - 2023-02-16.pdf

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

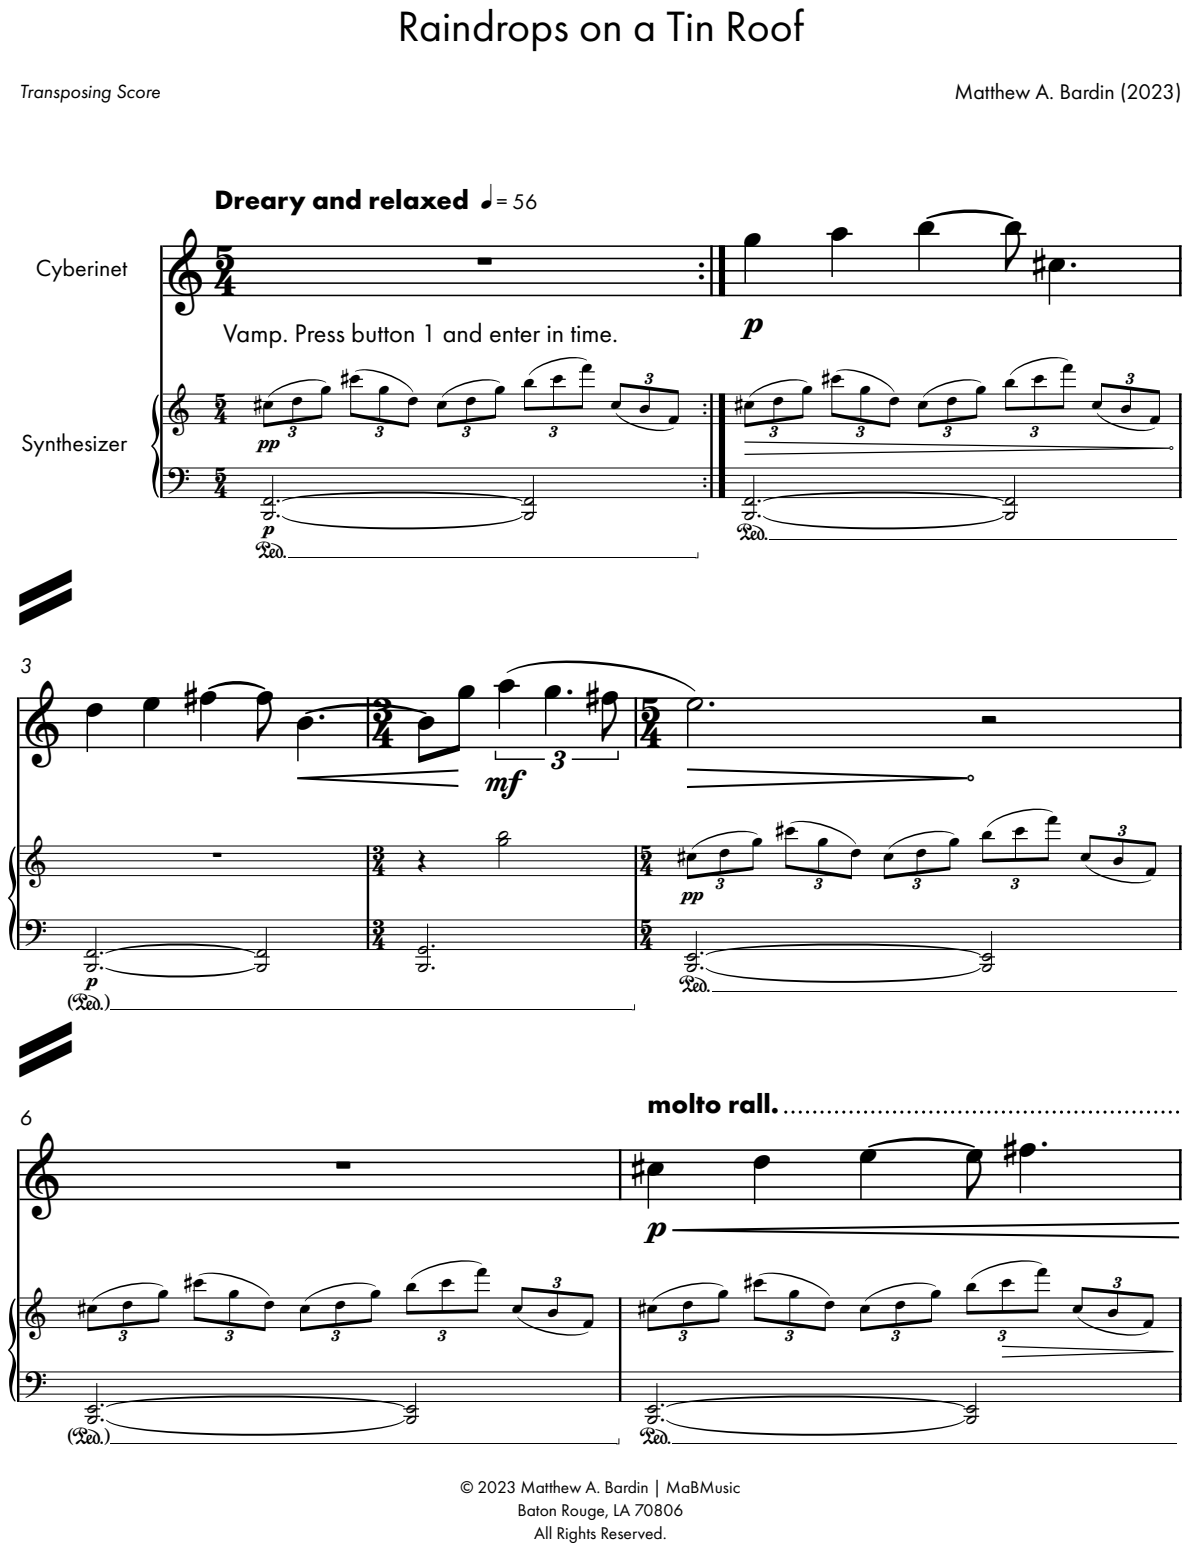
[picture p268: page 1]

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

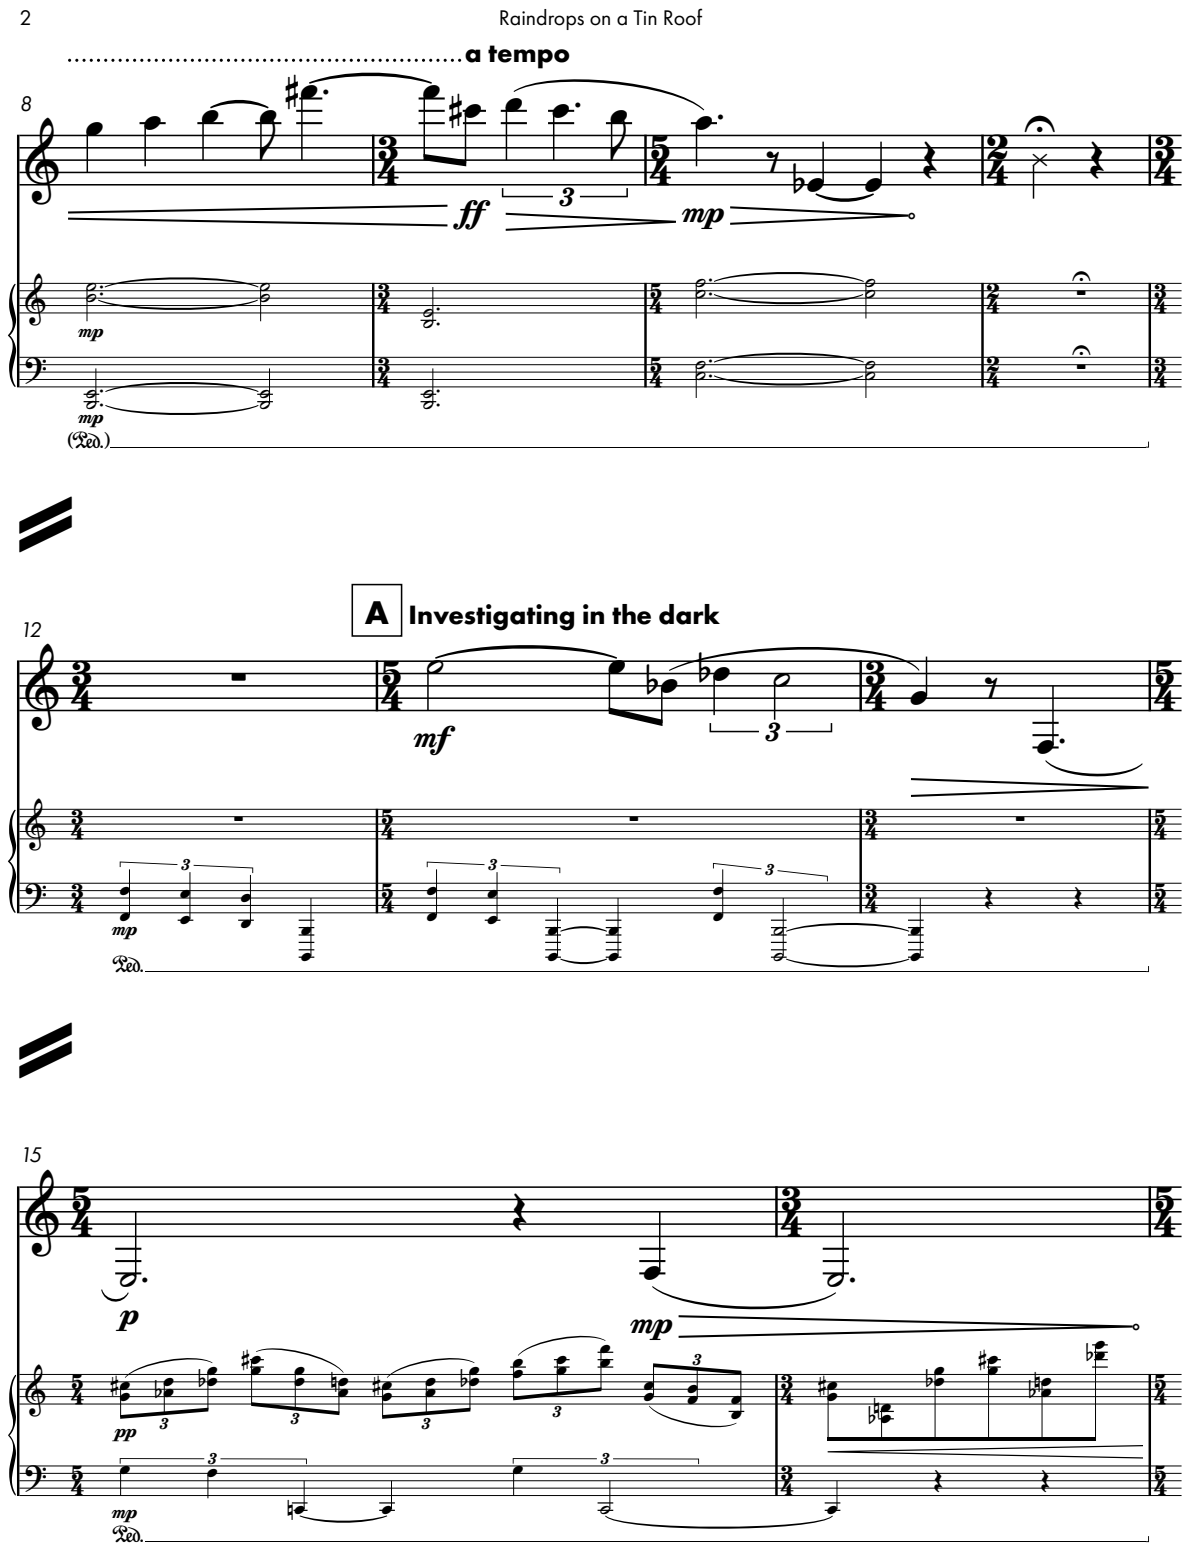
[picture p269: page 2]

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

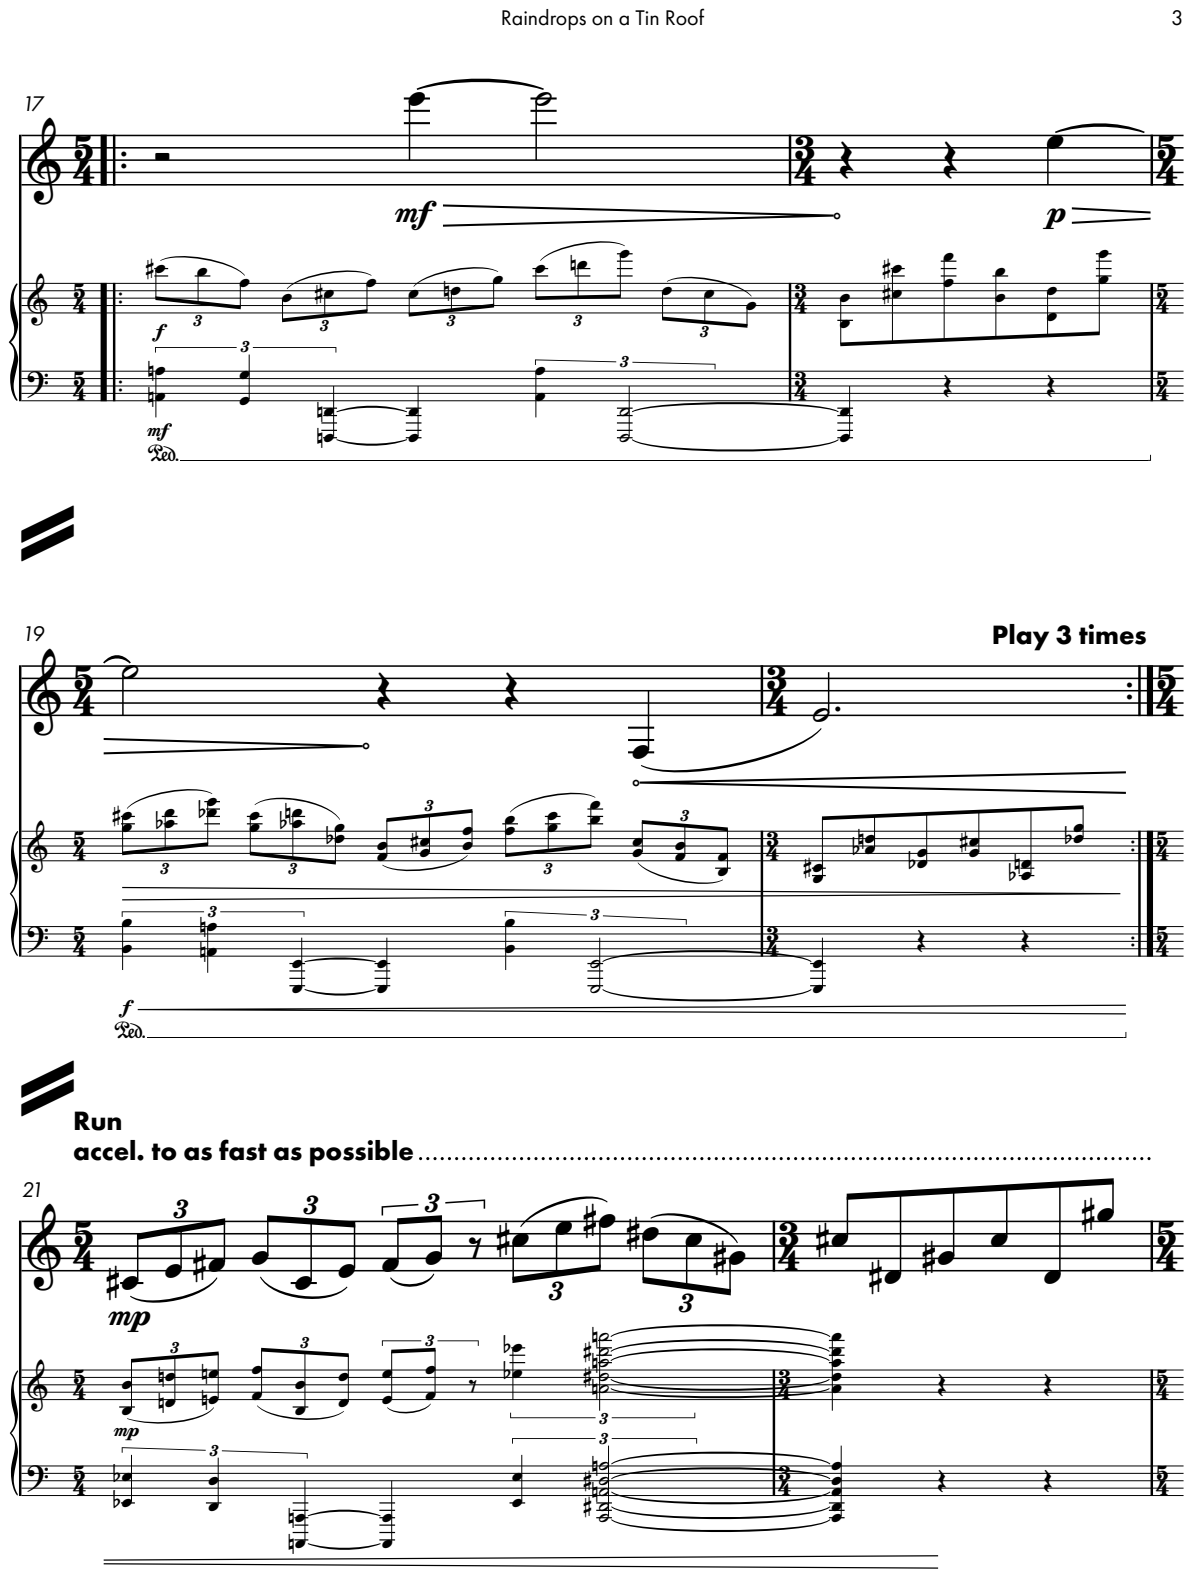
[picture p270: page 3]

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

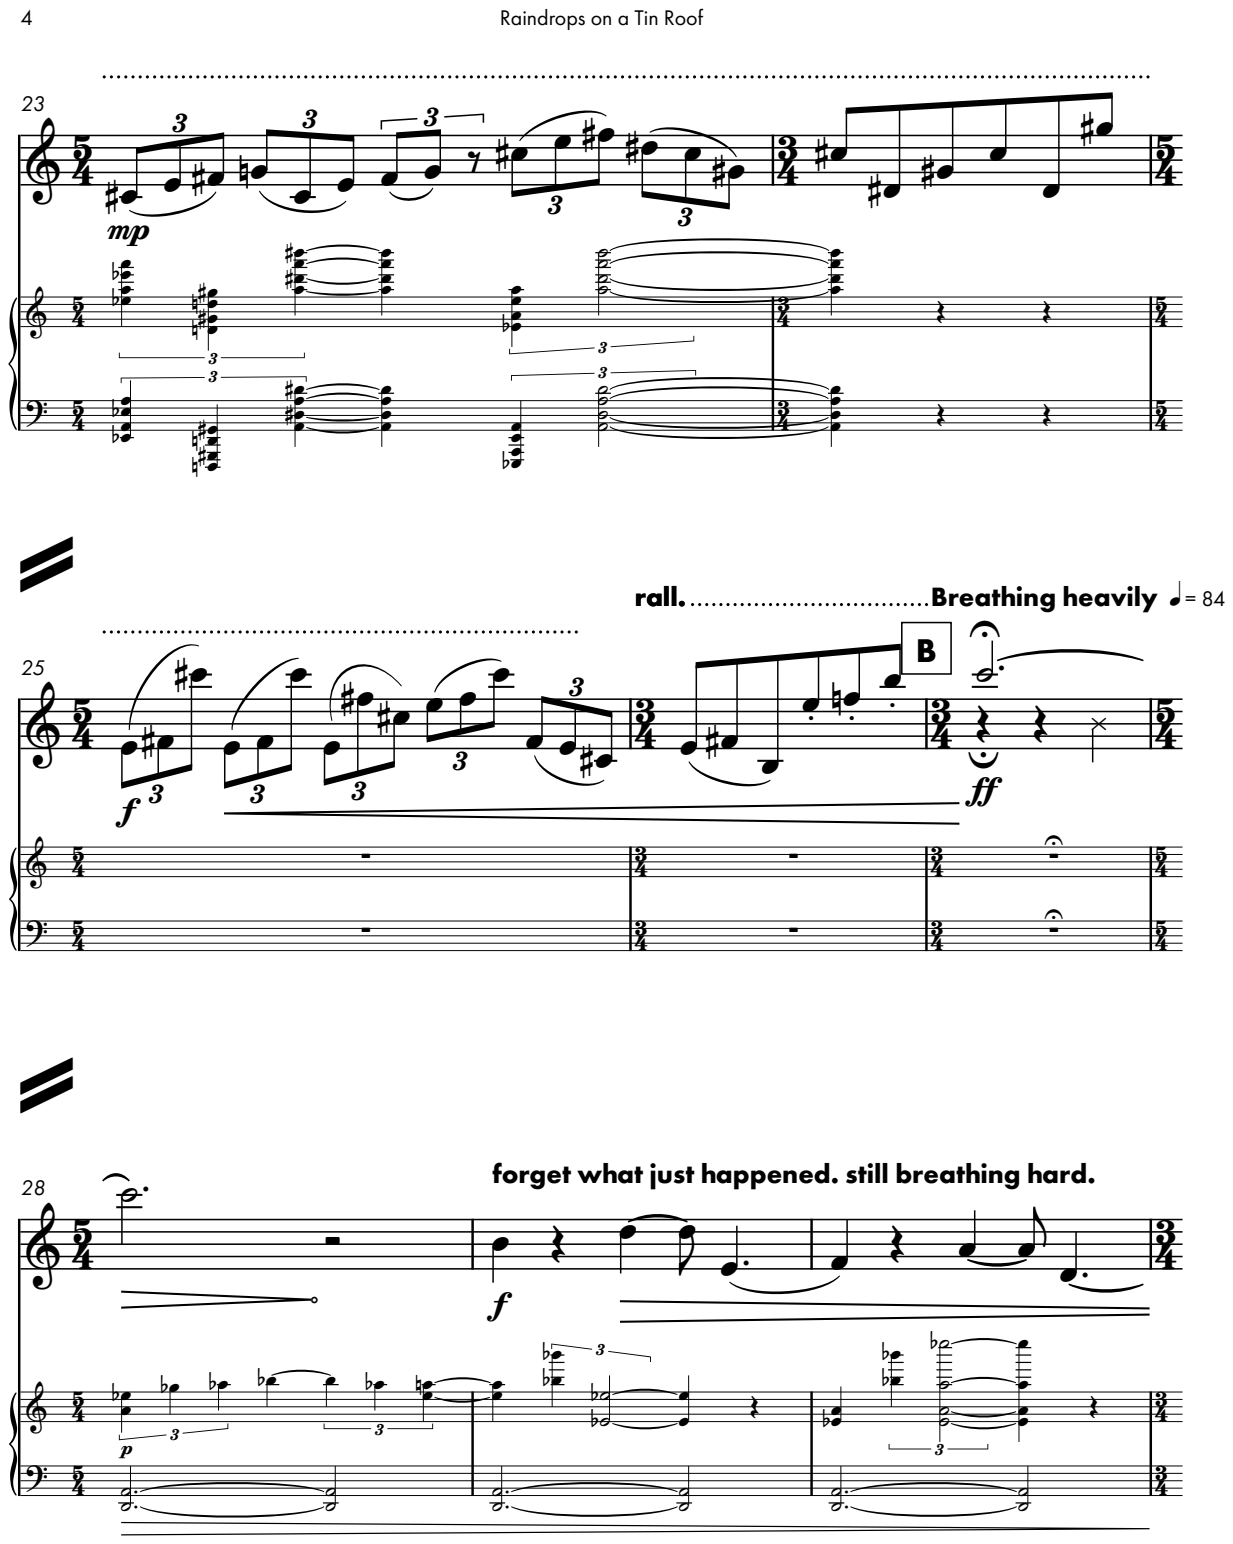
[picture p271: page 4]

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

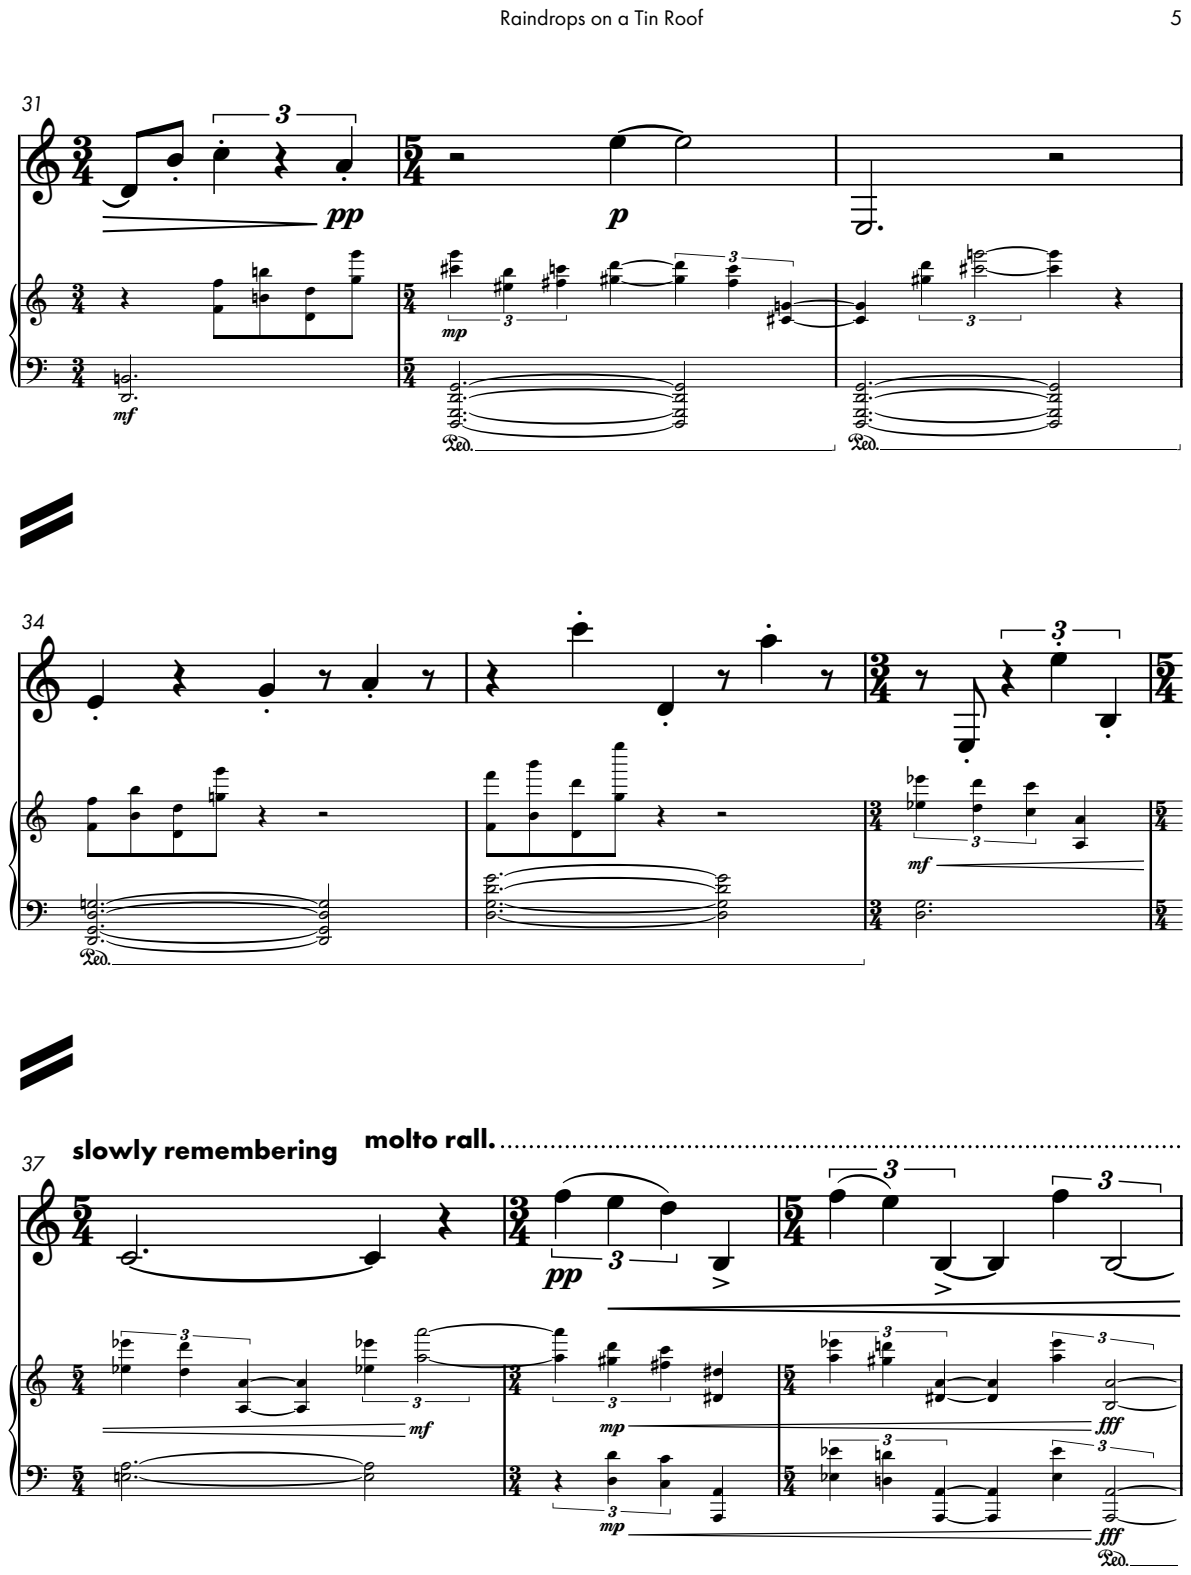
[picture p272: page 5]

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

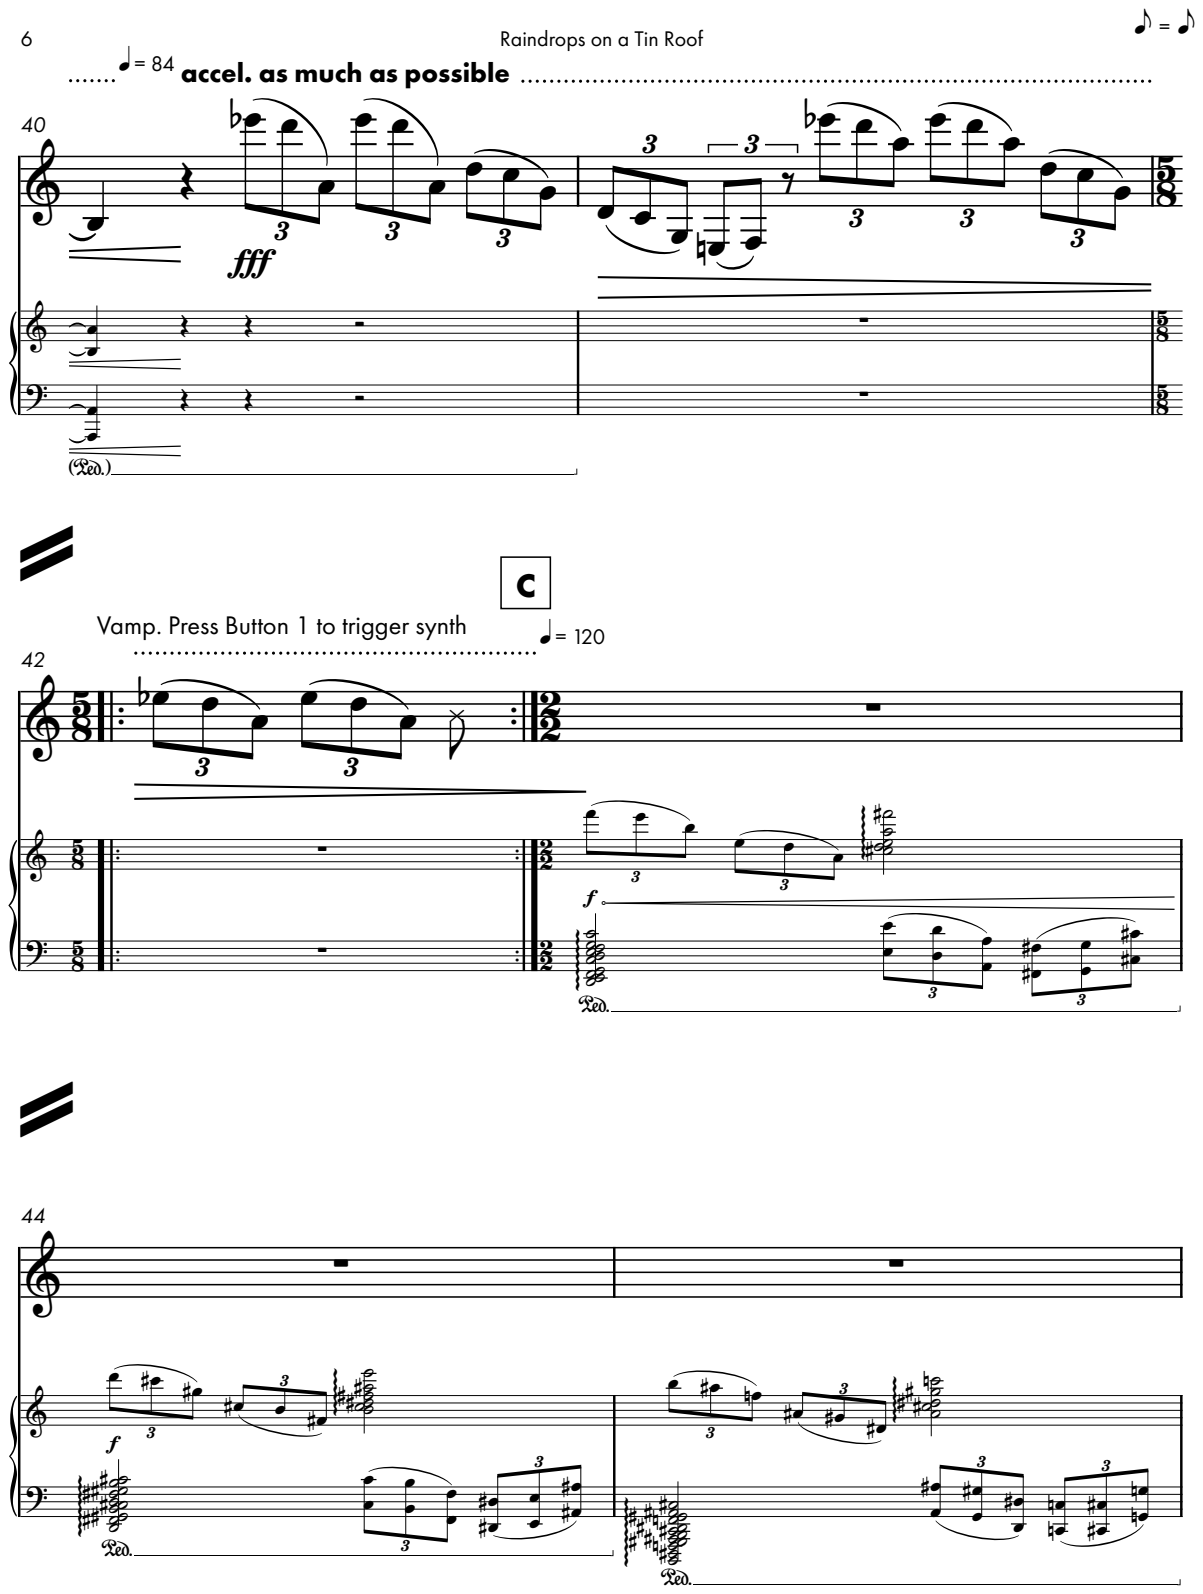
[picture p273: page 6]

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

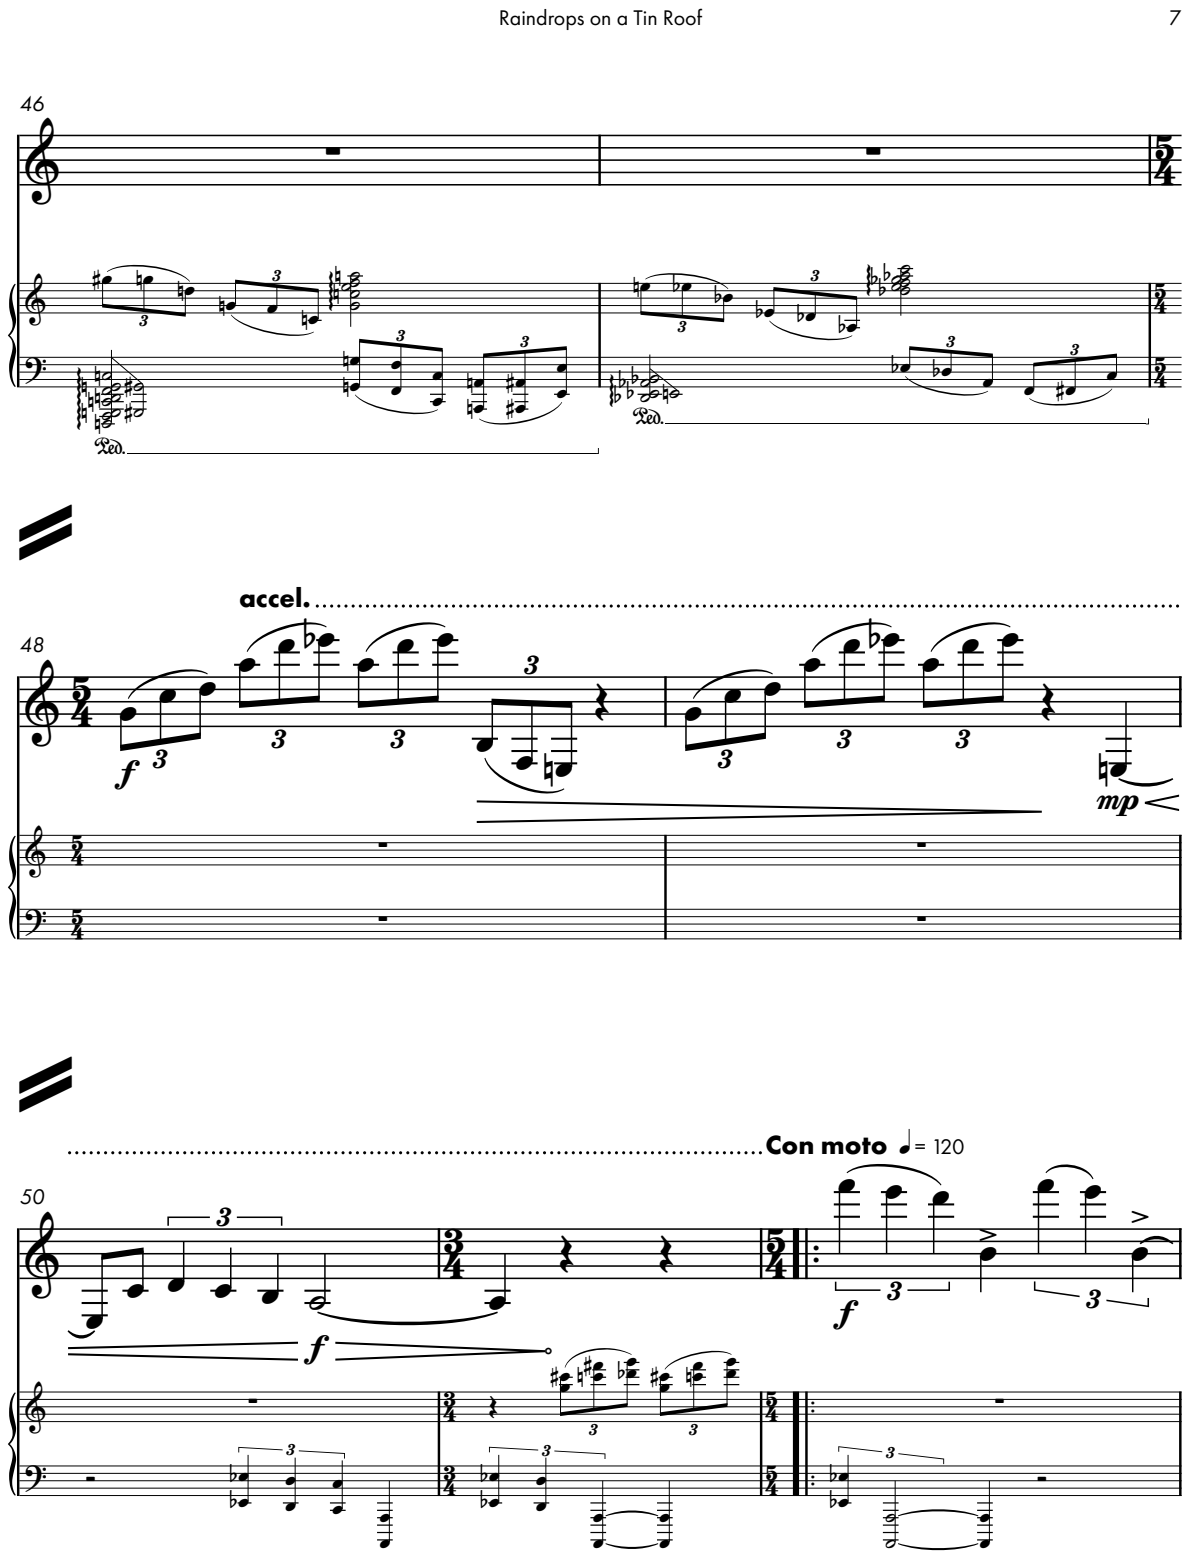
[picture p274: page 7]

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

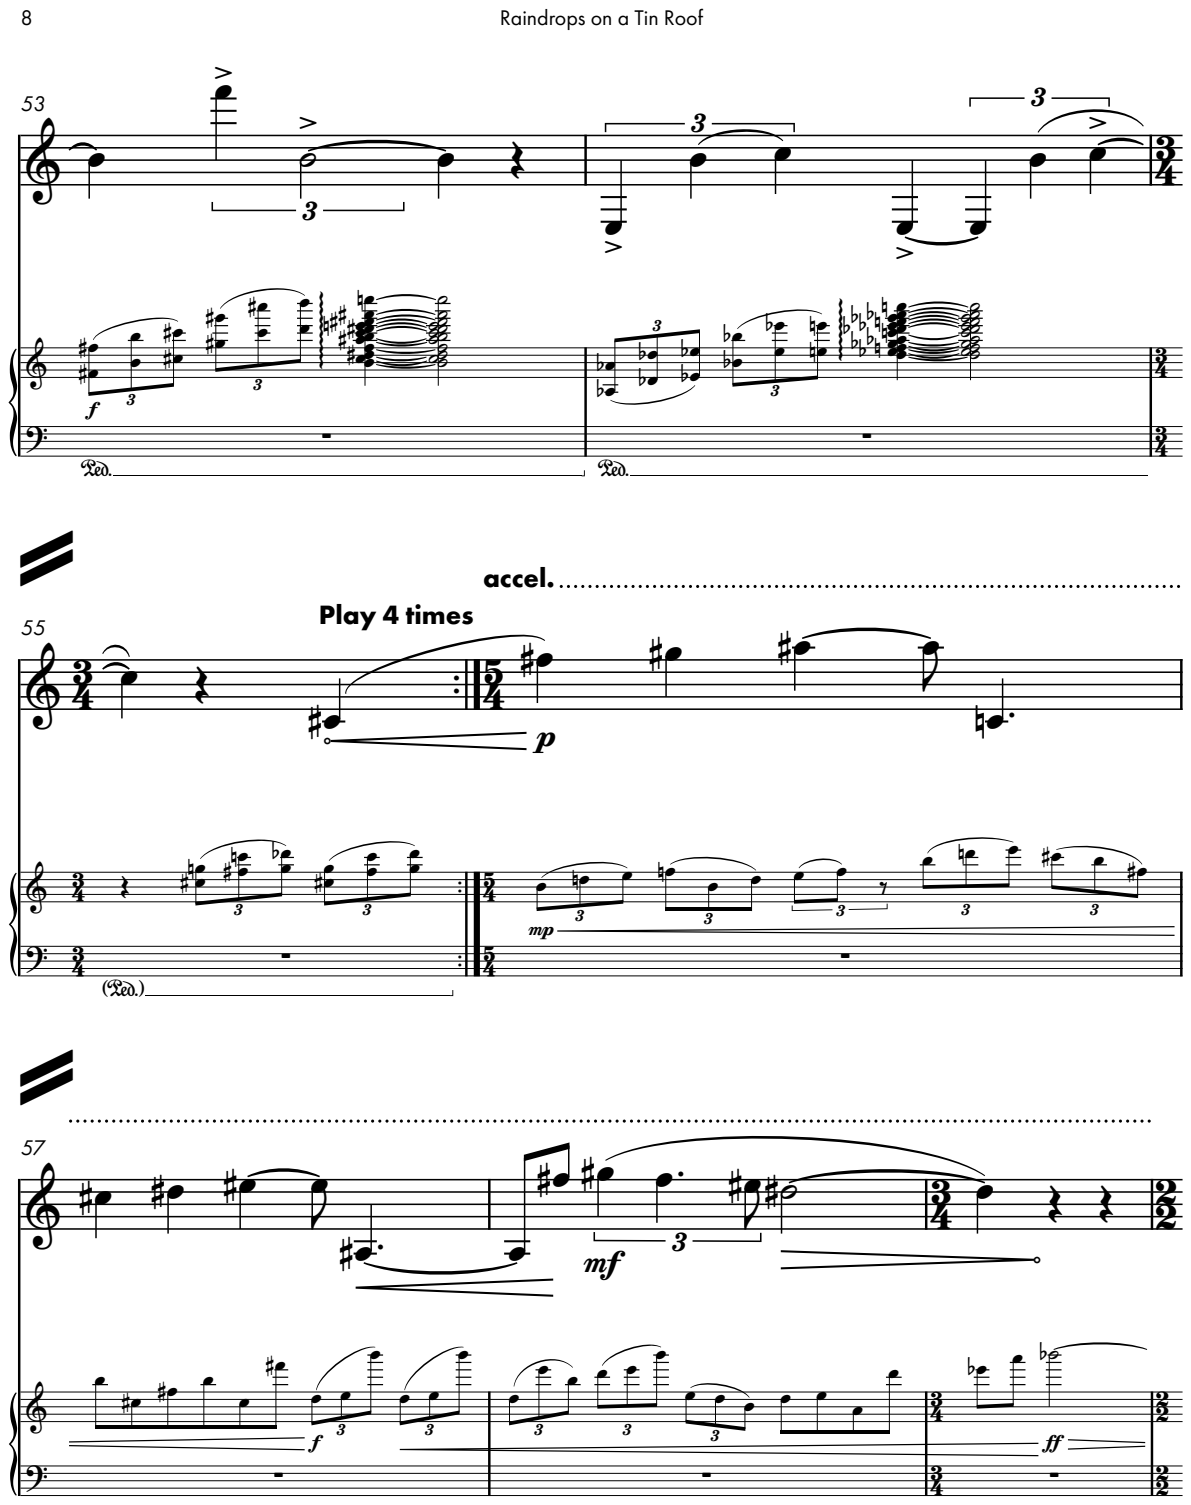
[picture p275: page 8]

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

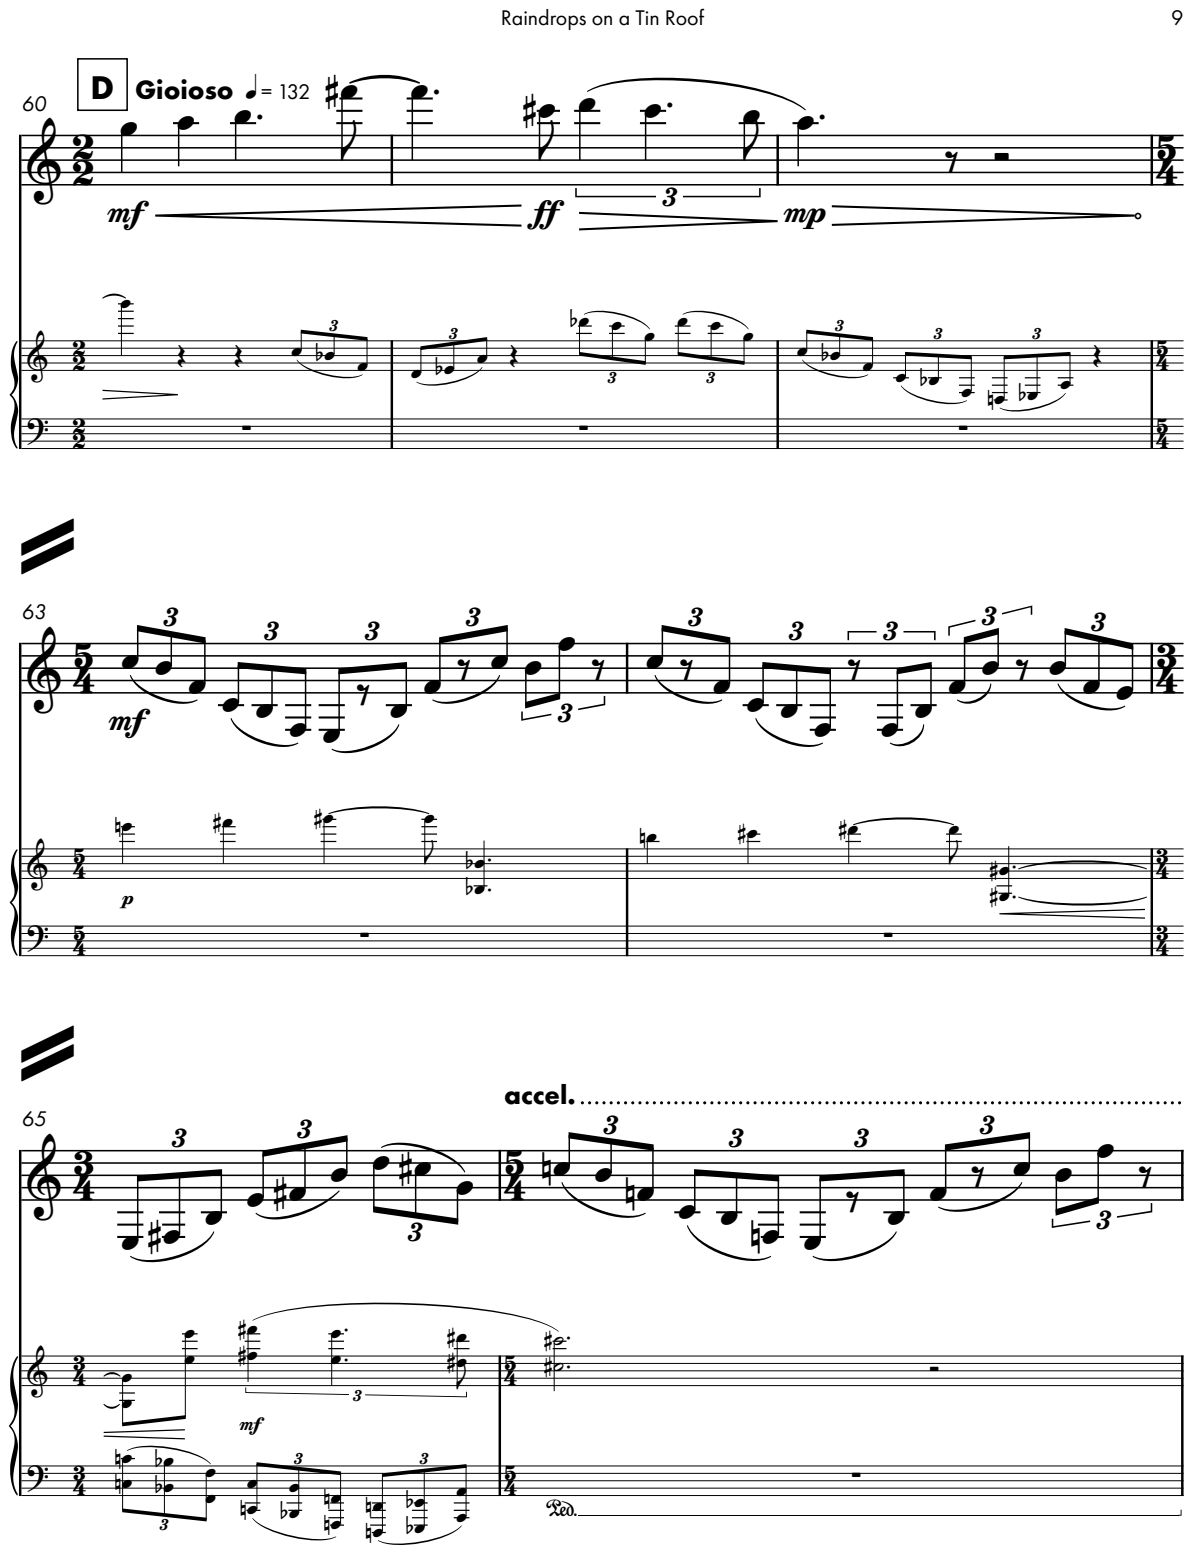
[picture p276: page 9]

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

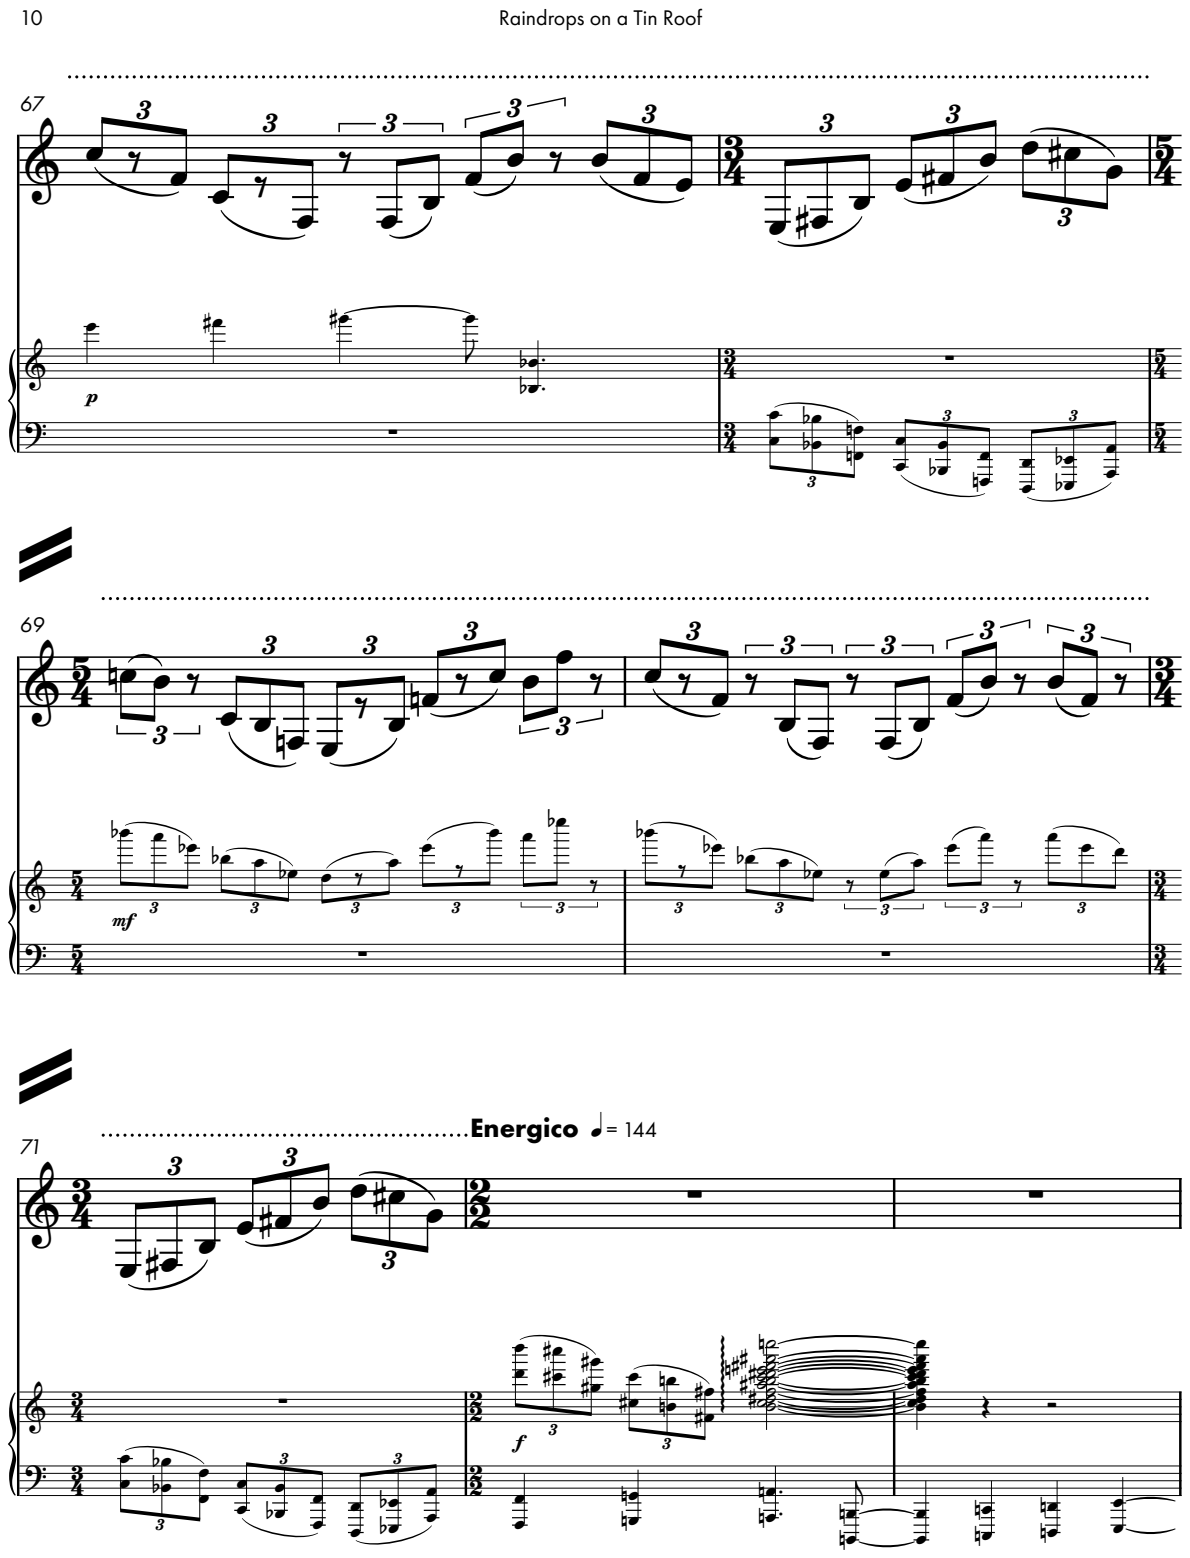
[picture p277: page 10]

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

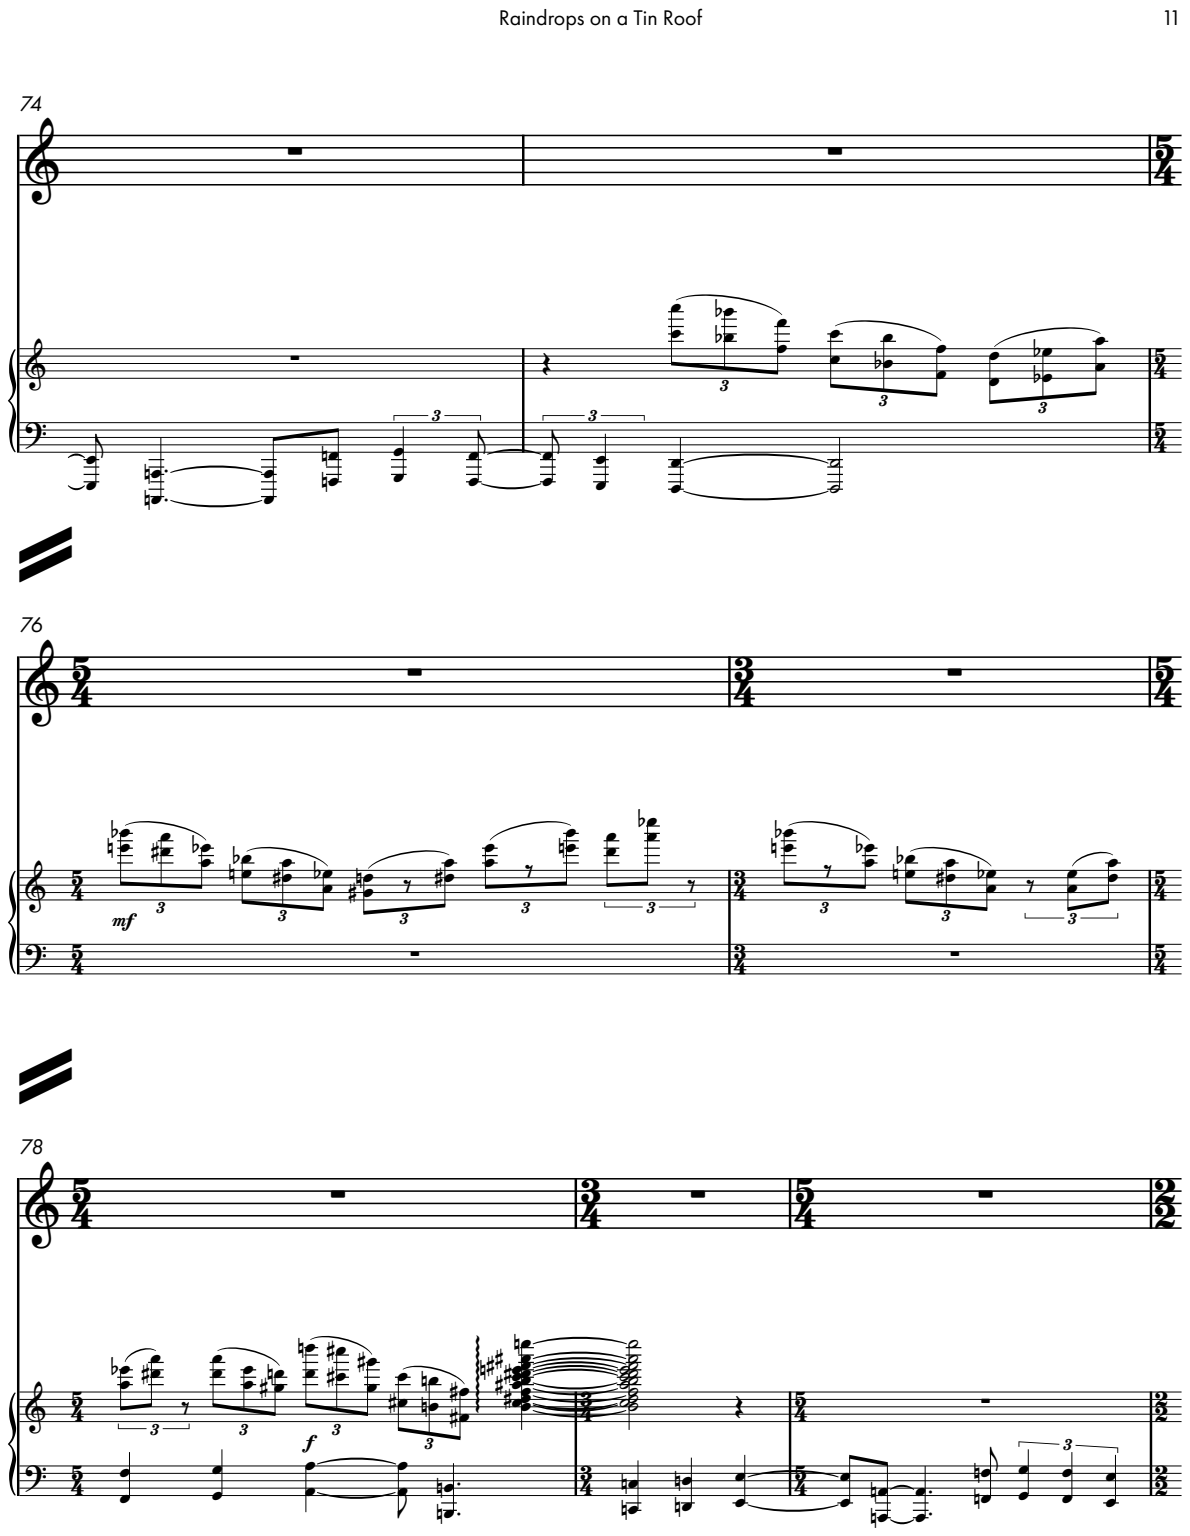
[picture p278: page 11]

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

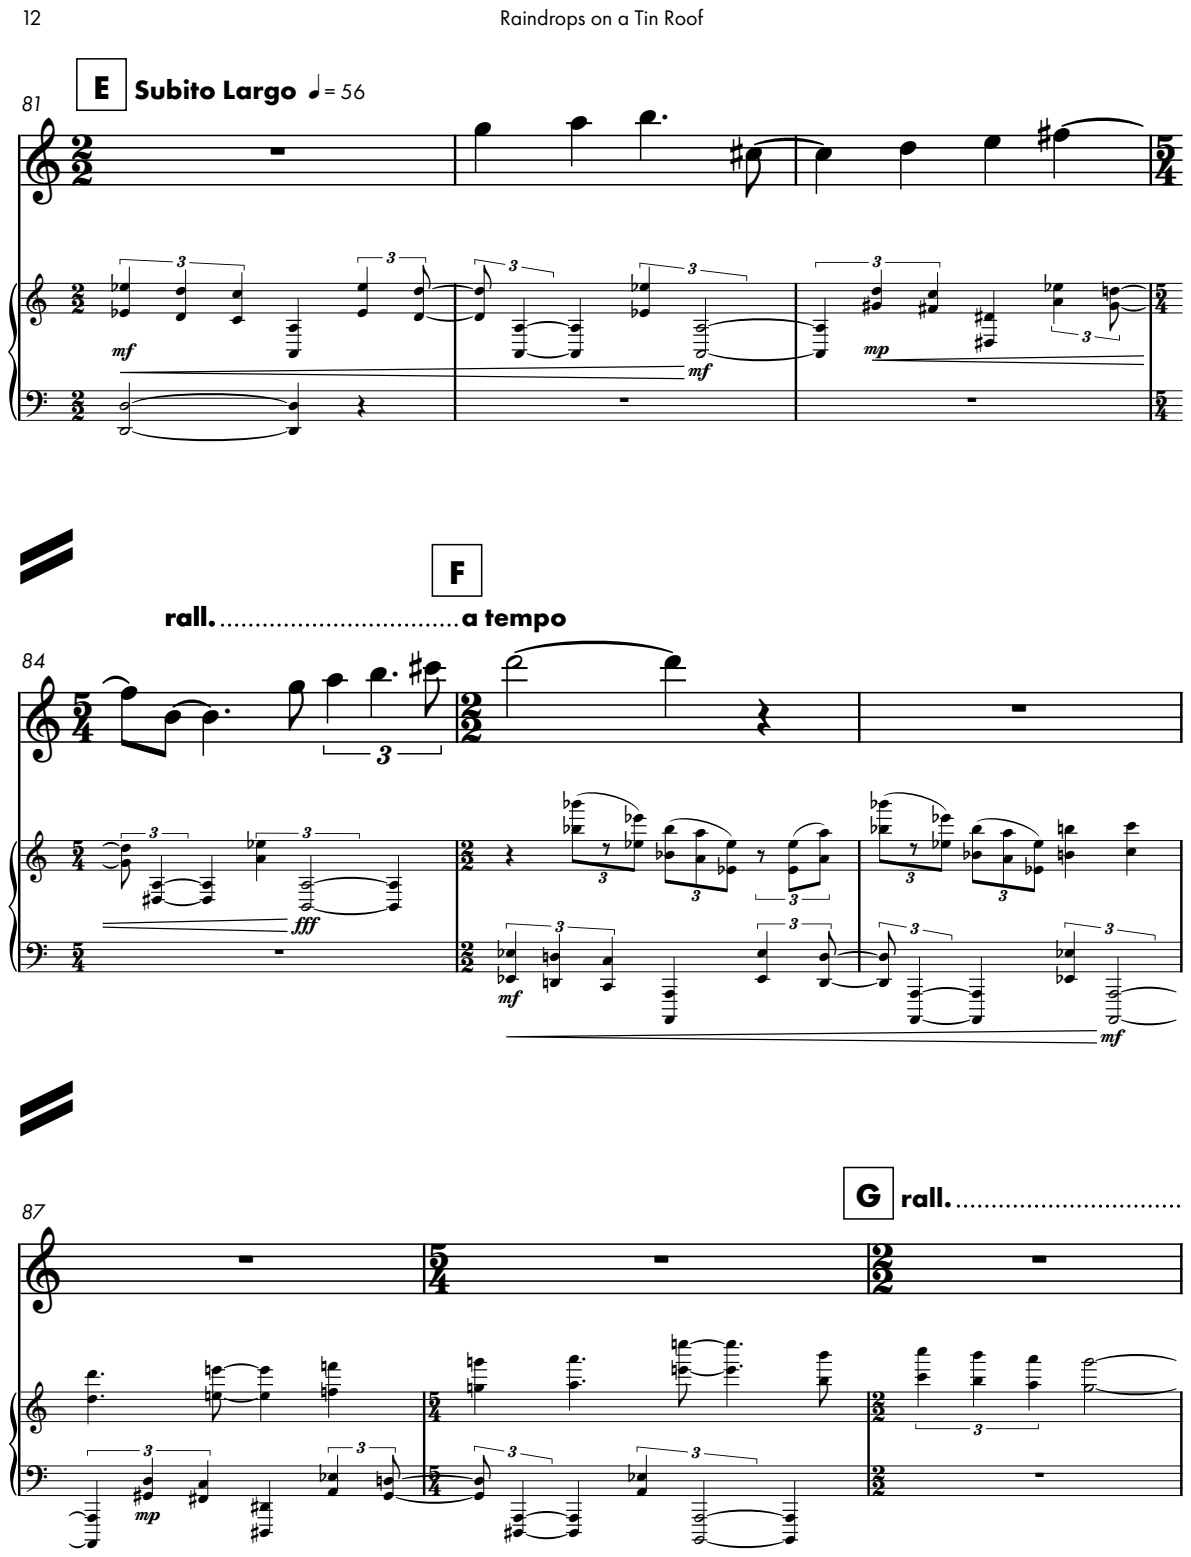
[picture p279: page 12]

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

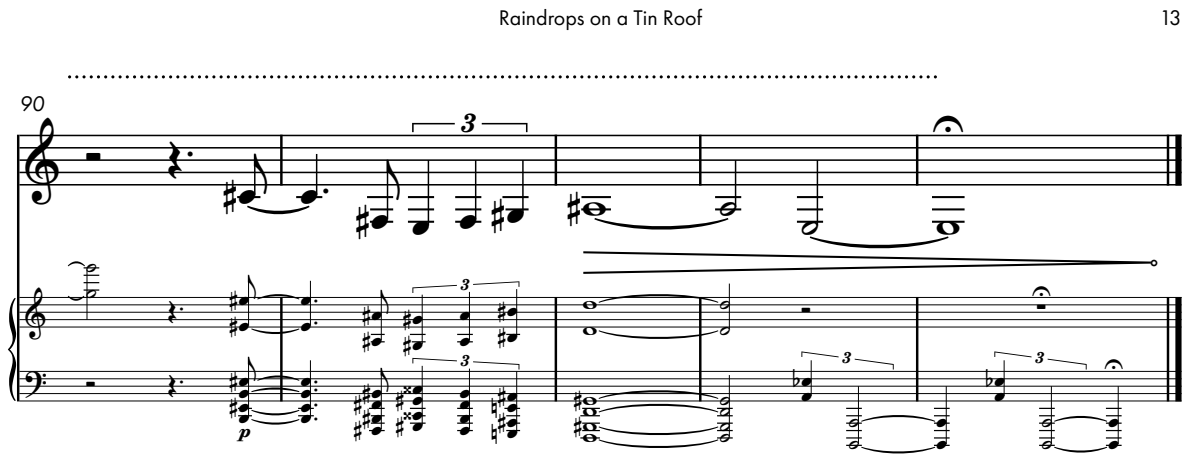
[picture p280: page 13]
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
