mbardin/Cyberinet/zMusic Composition Scores/scores/materials/raindrops/planning diagrams/raindrops - 2023-02-13.pdf

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

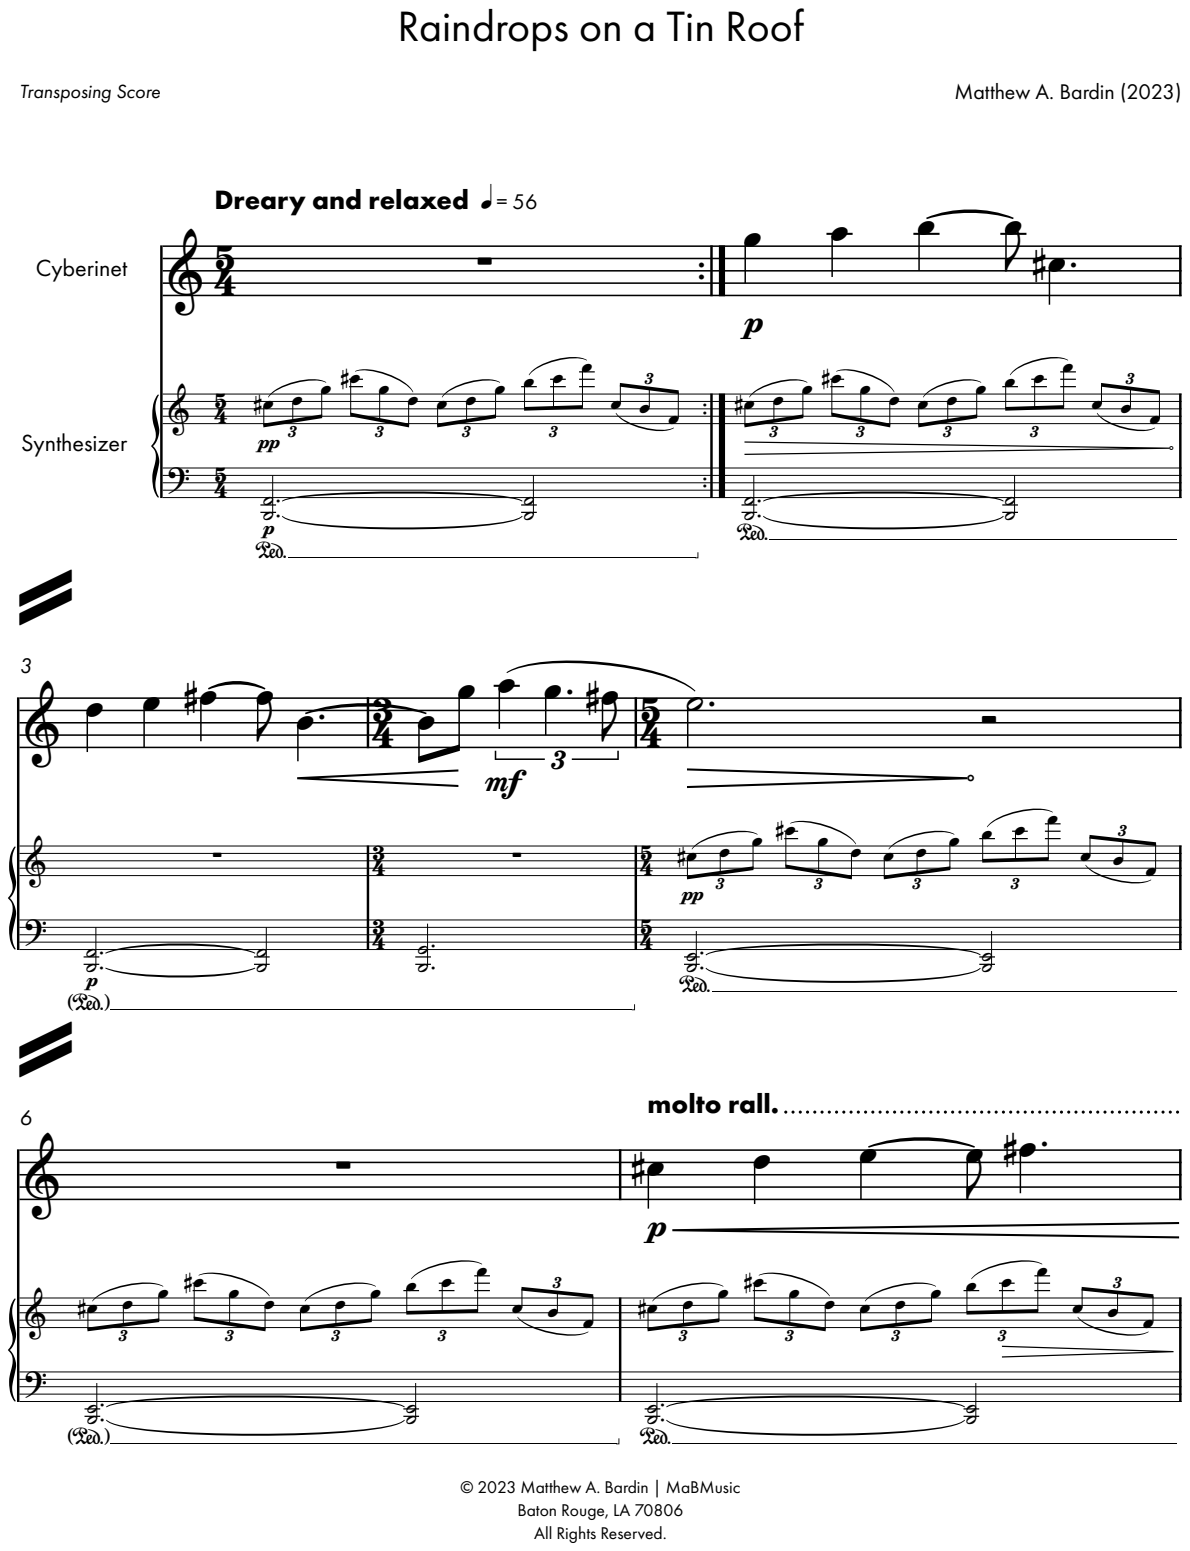
[picture p281: page 1]

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

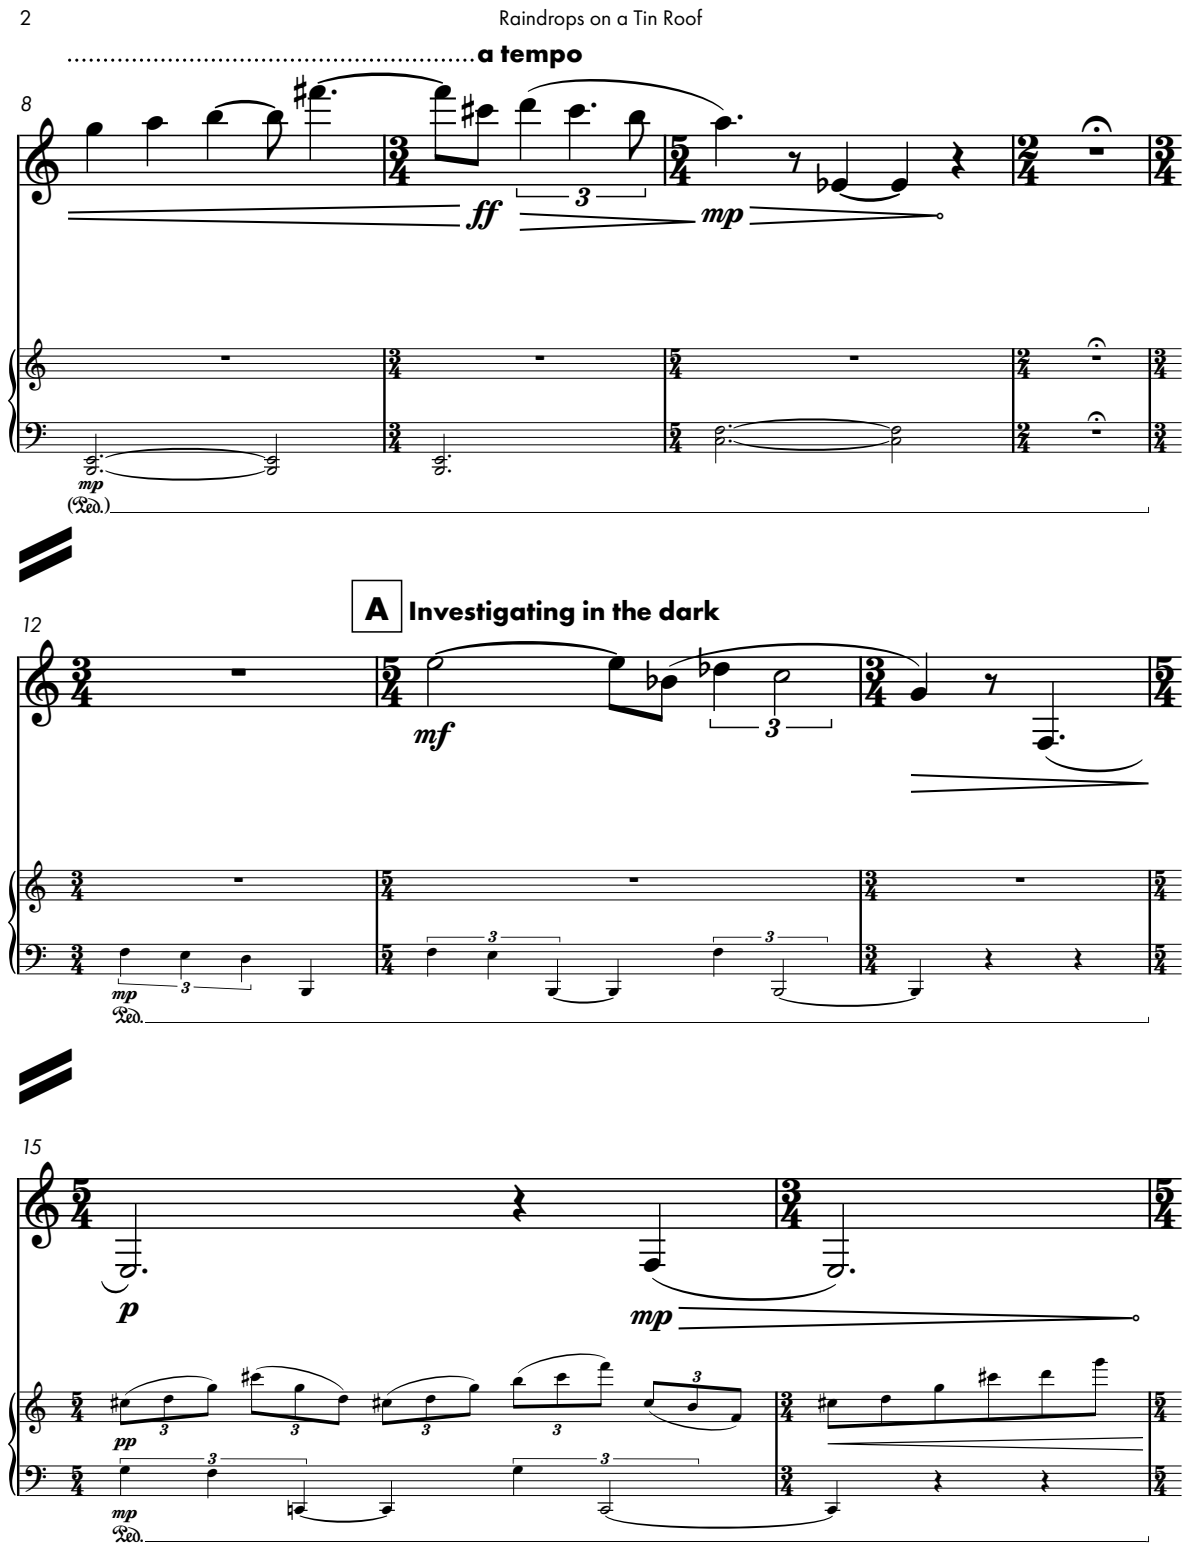
[picture p282: page 2]

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

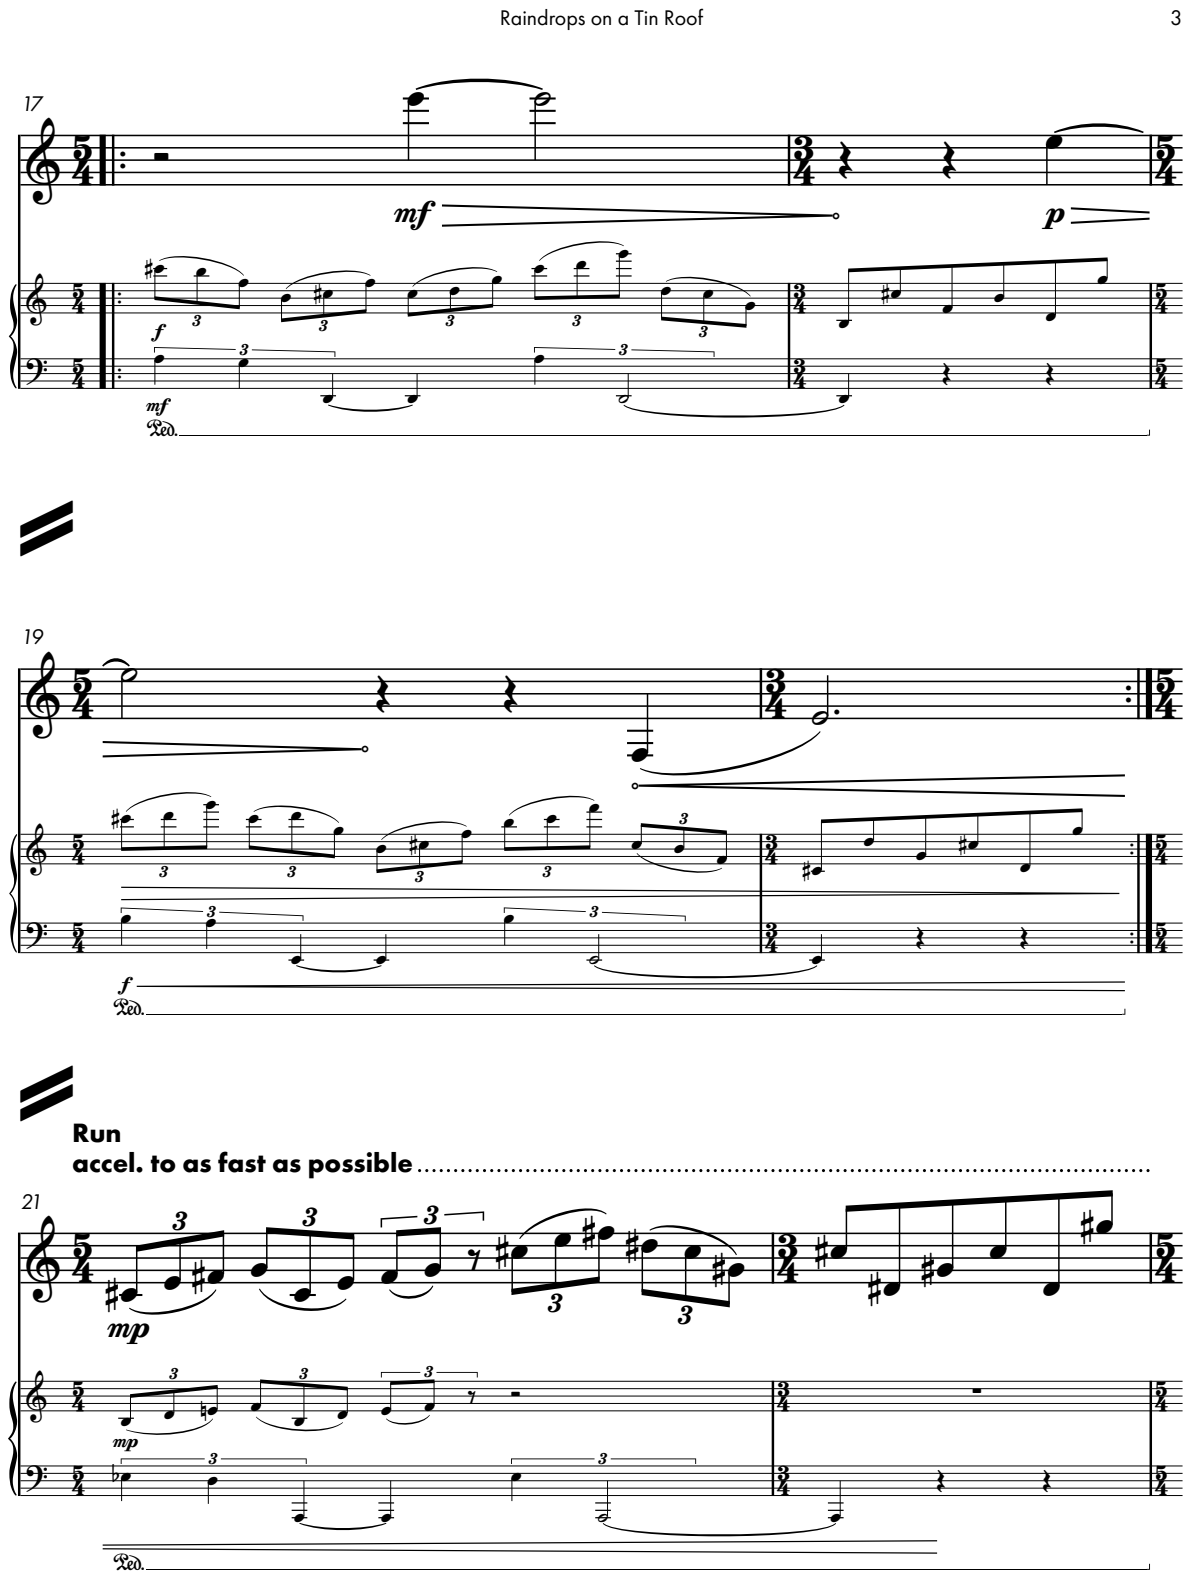
[picture p283: page 3]

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

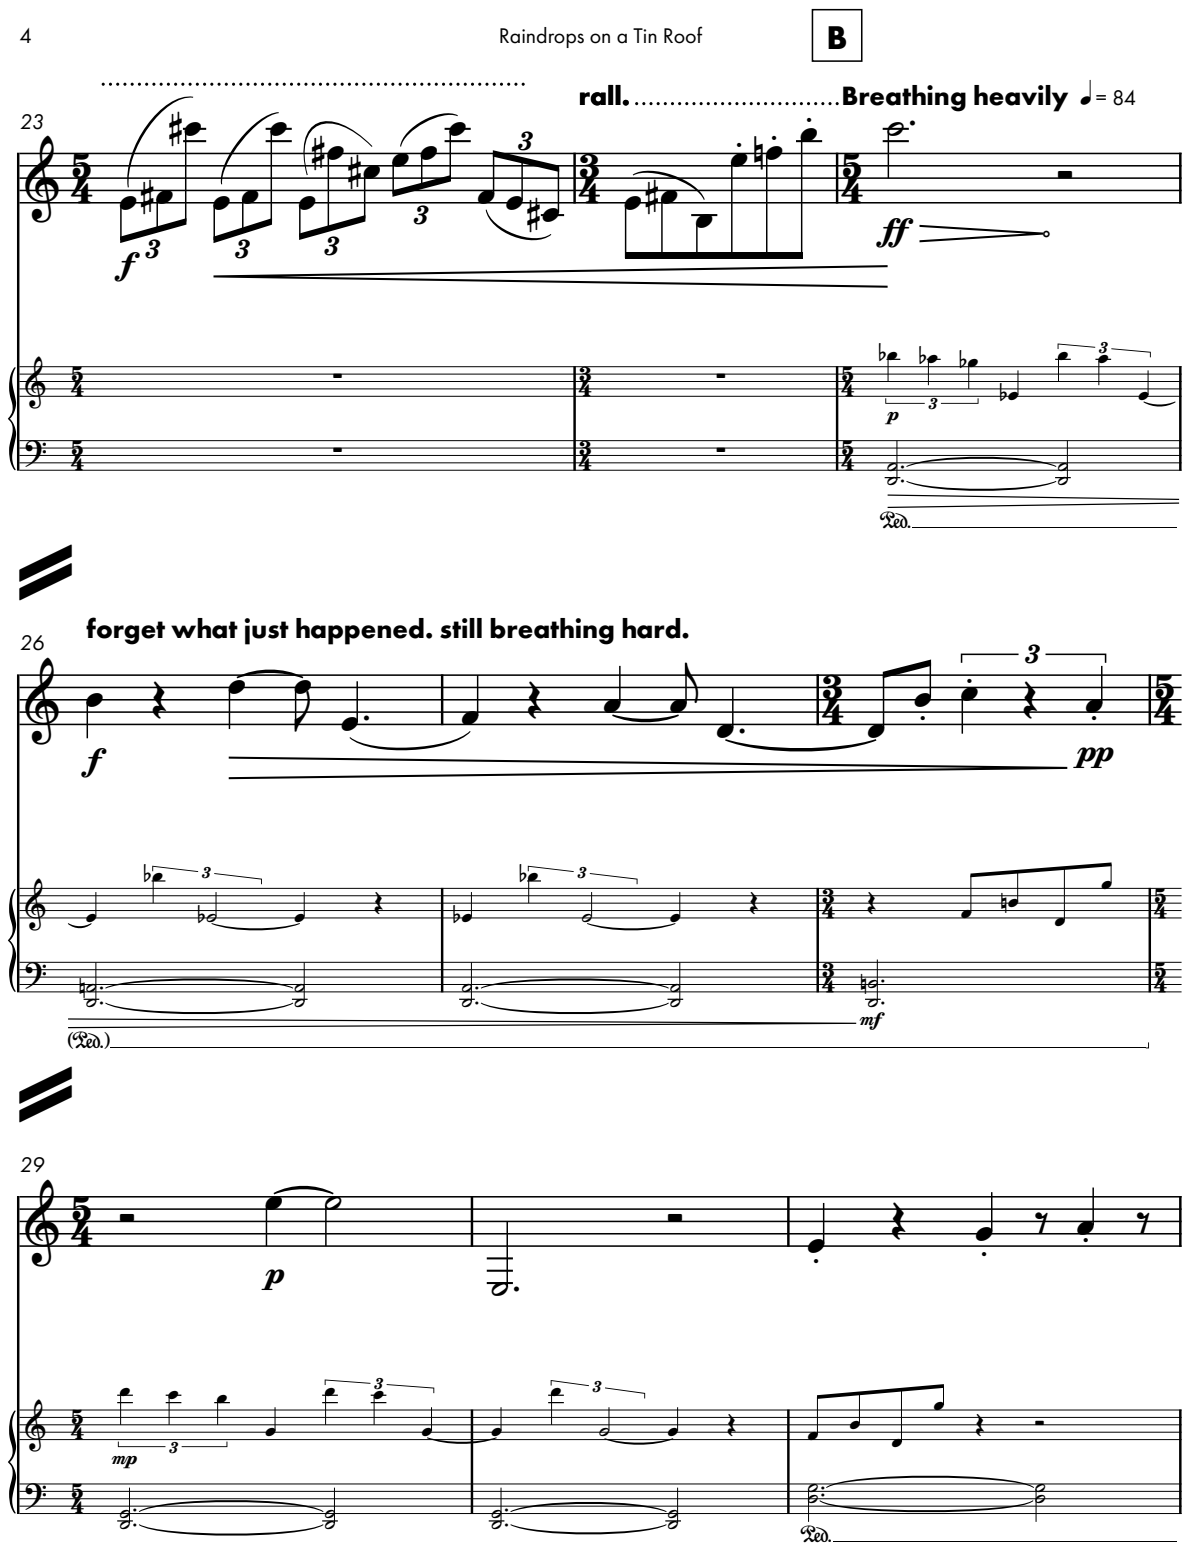
[picture p284: page 4]

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

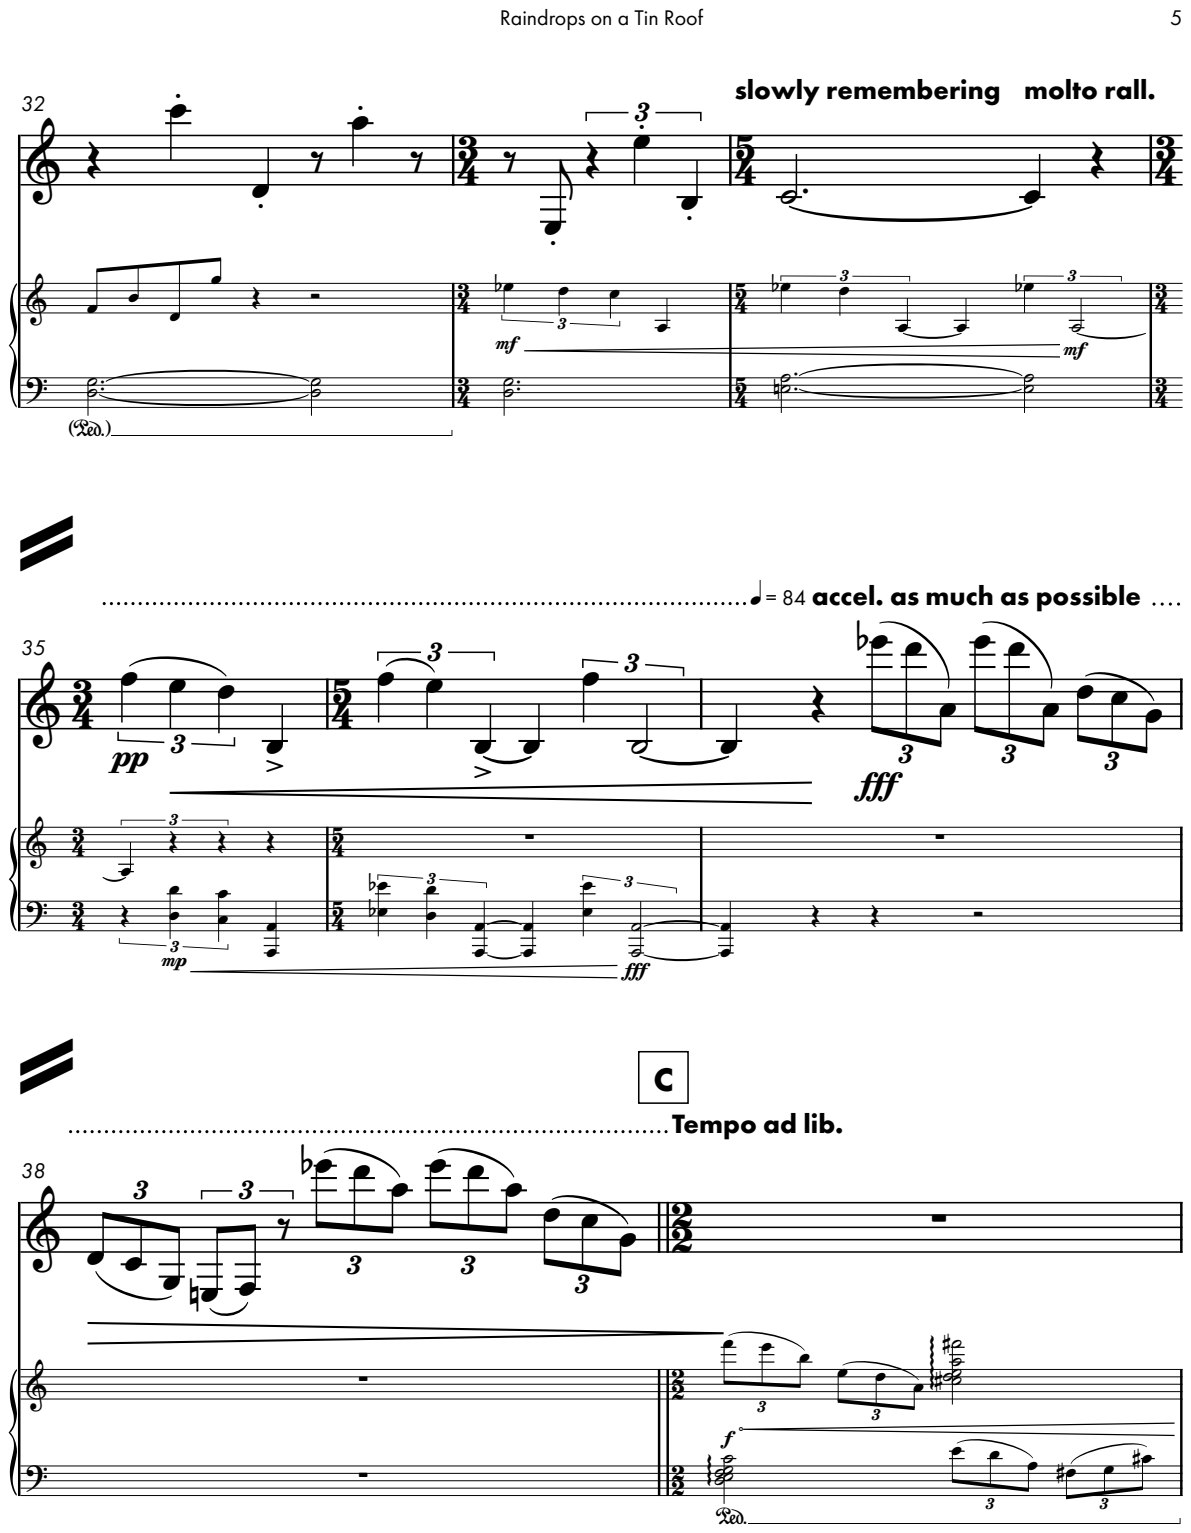
[picture p285: page 5]

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

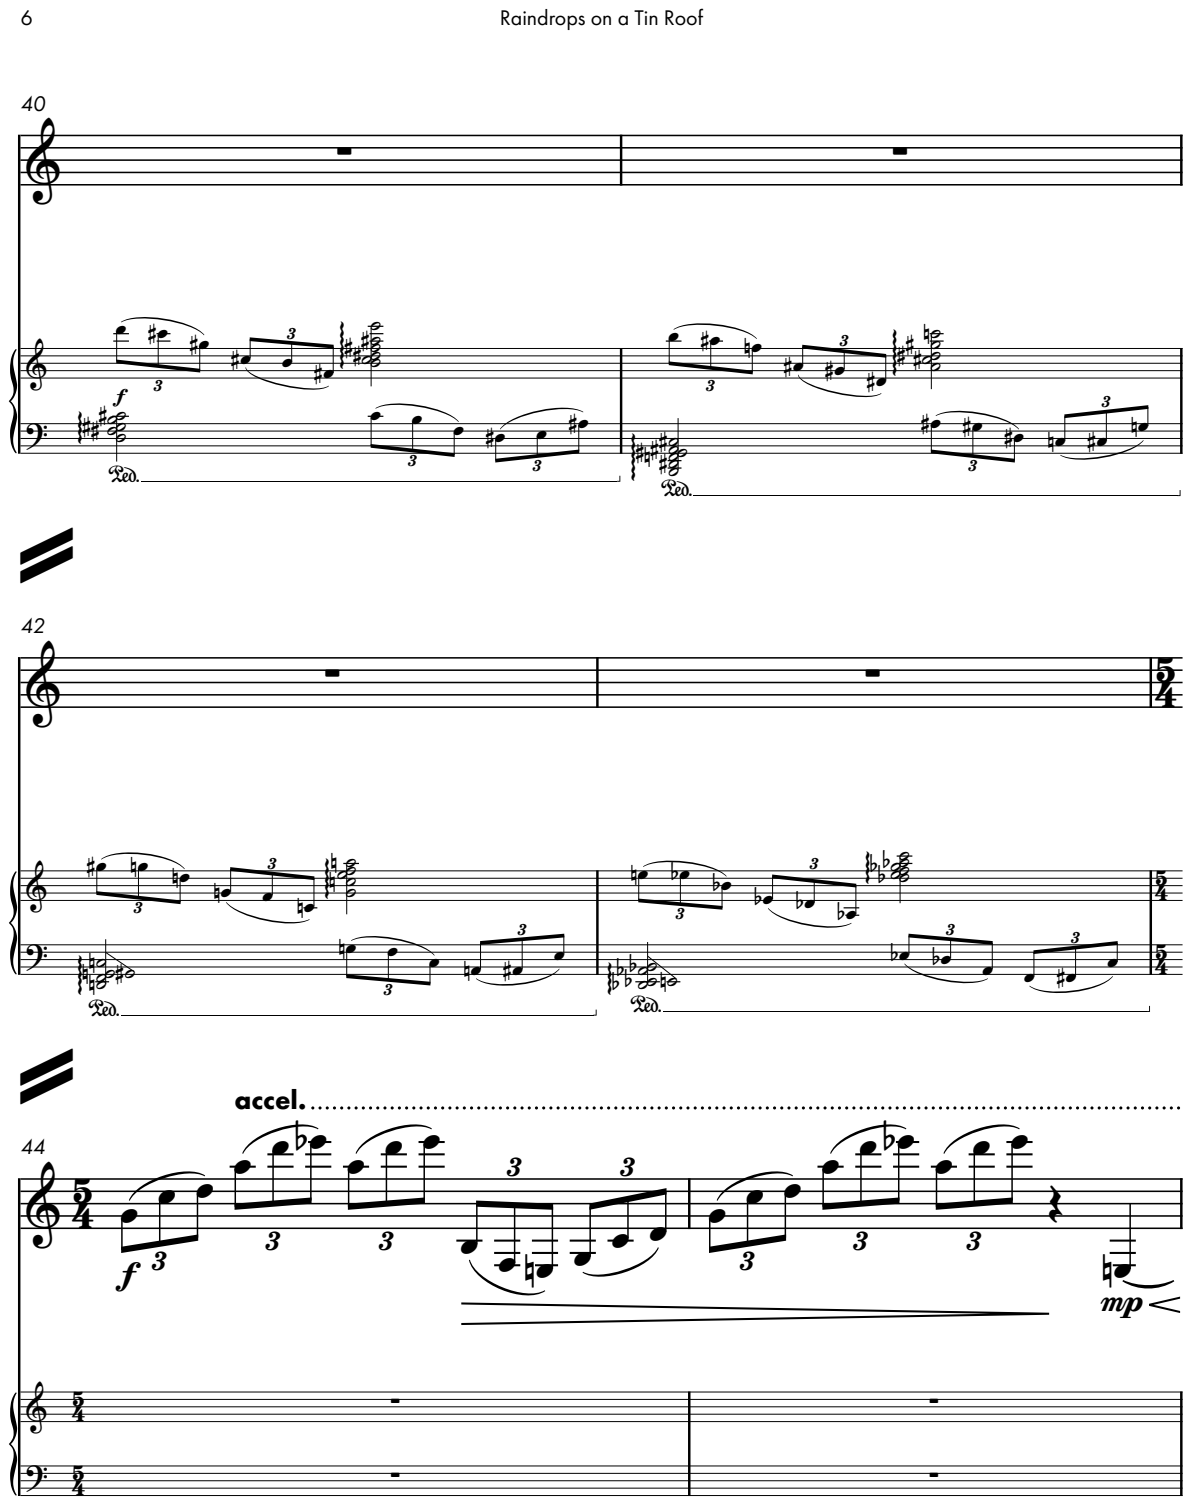
[picture p286: page 6]

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

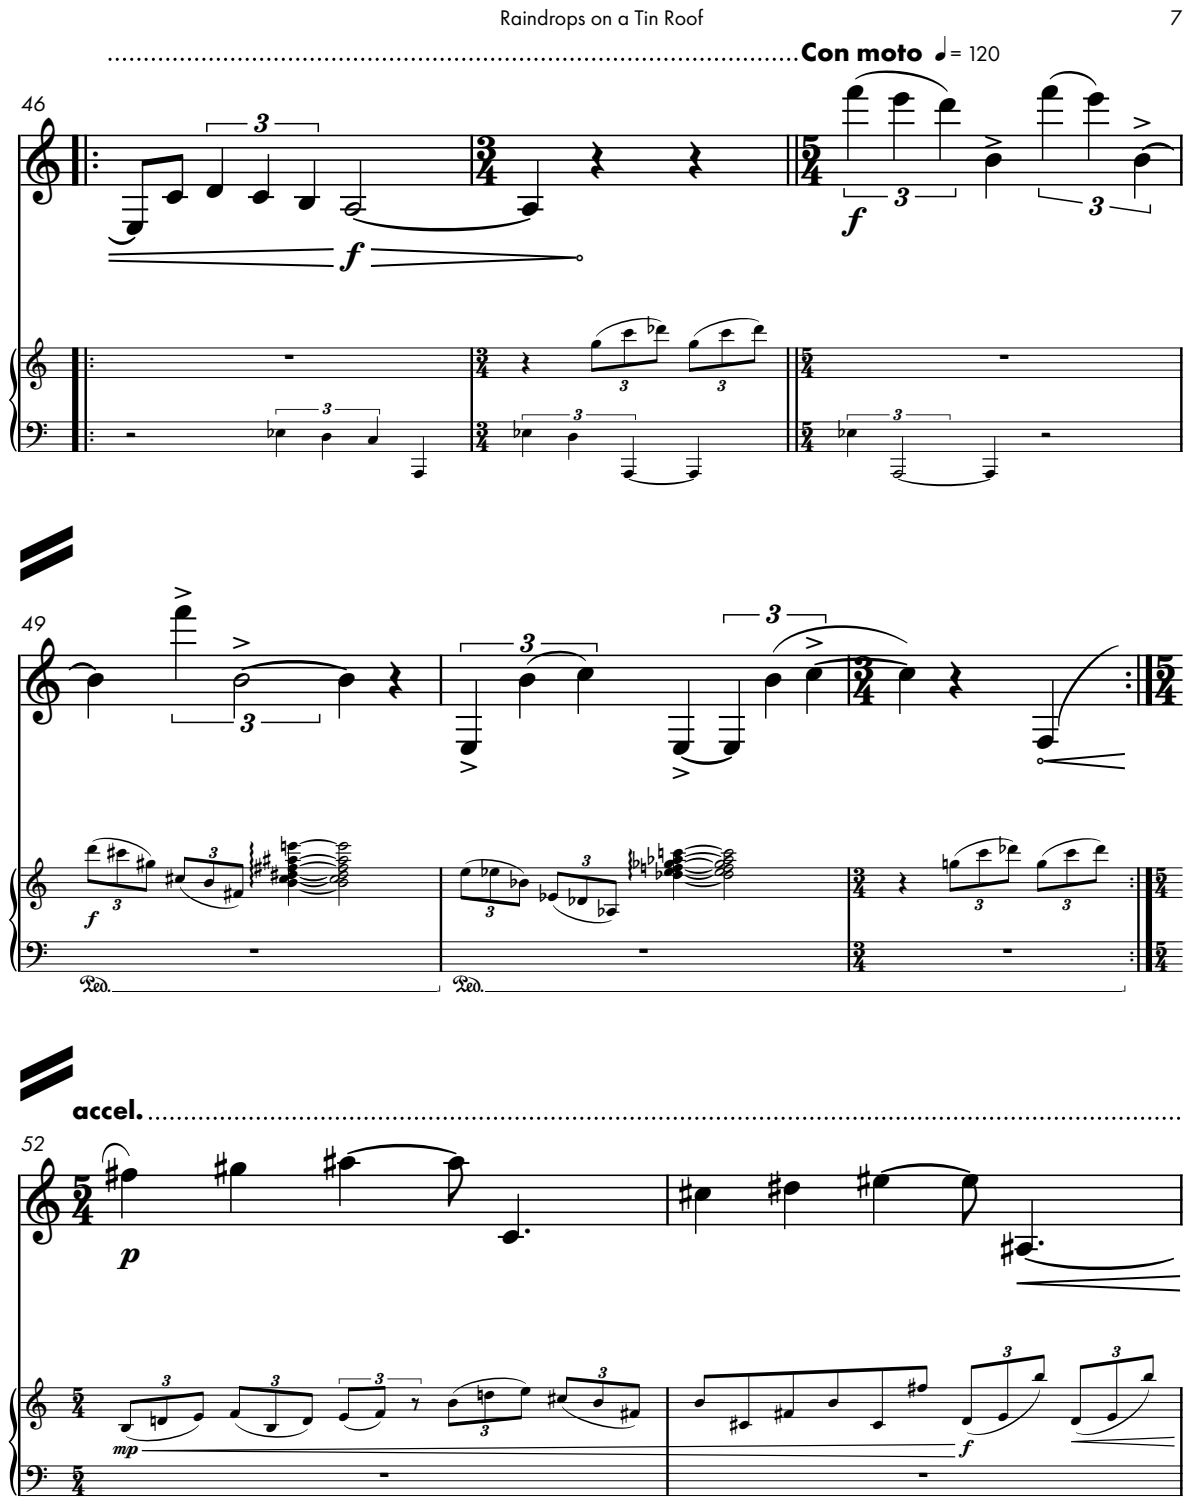
[picture p287: page 7]

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

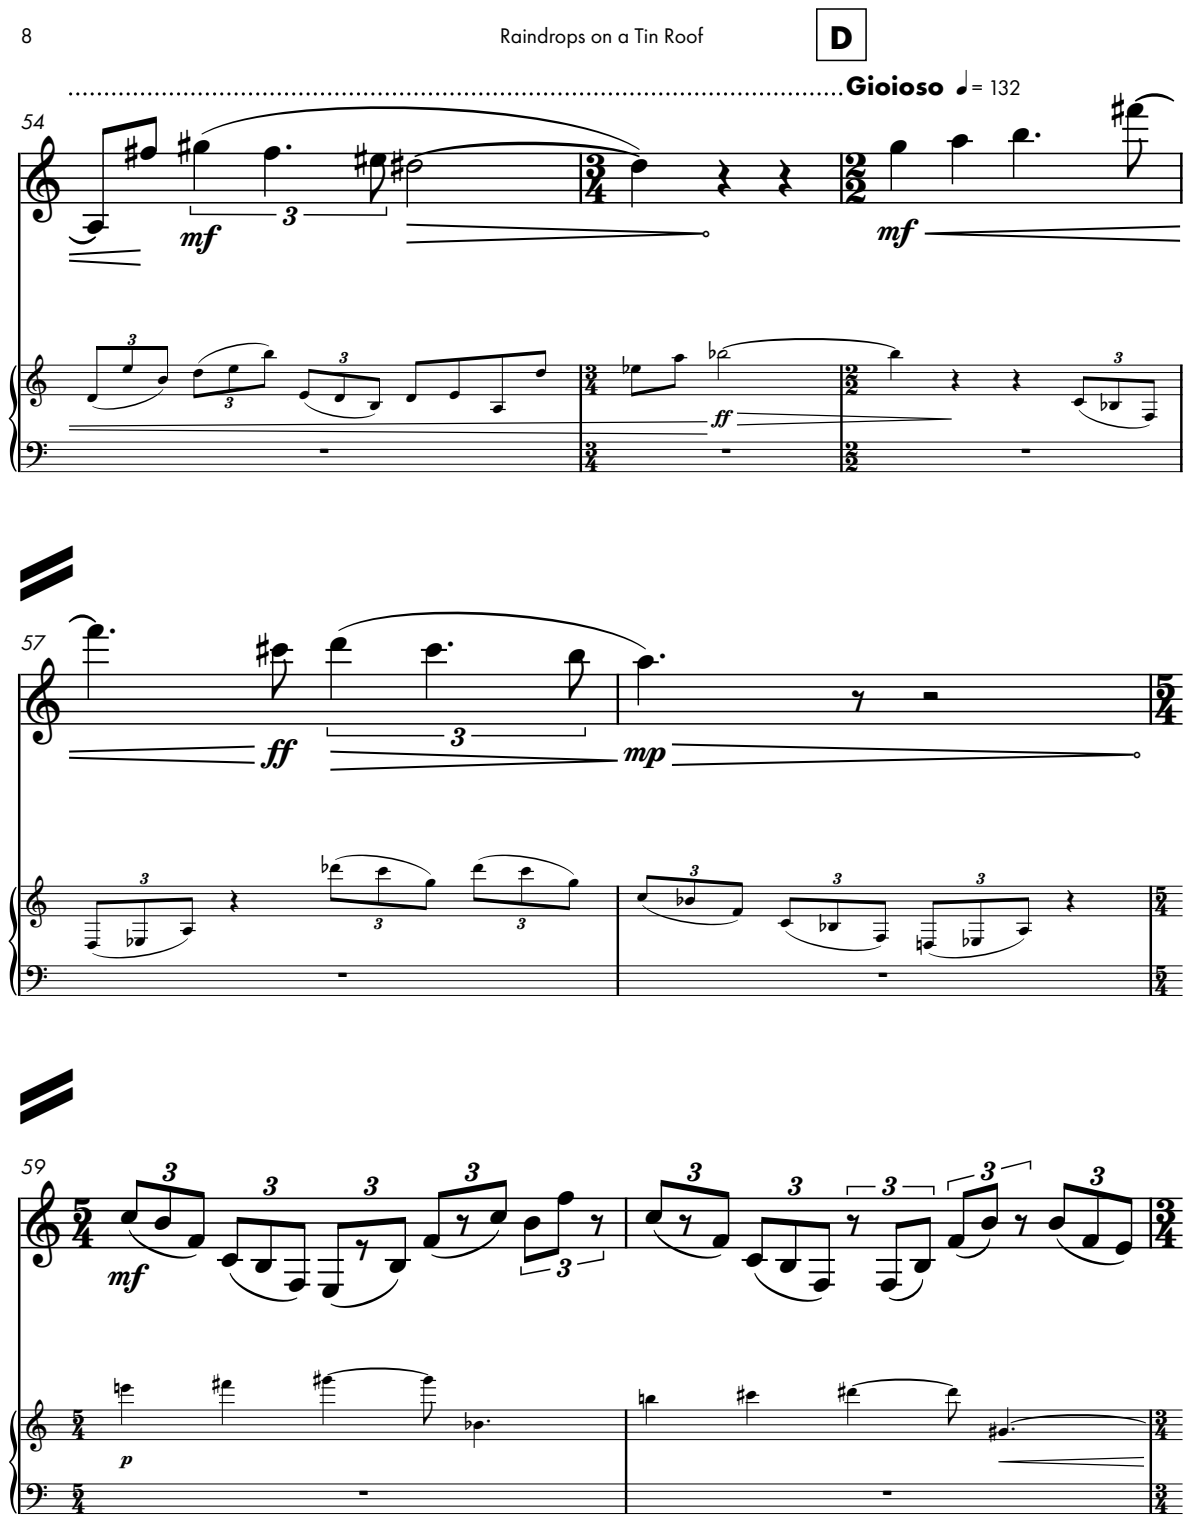
[picture p288: page 8]

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

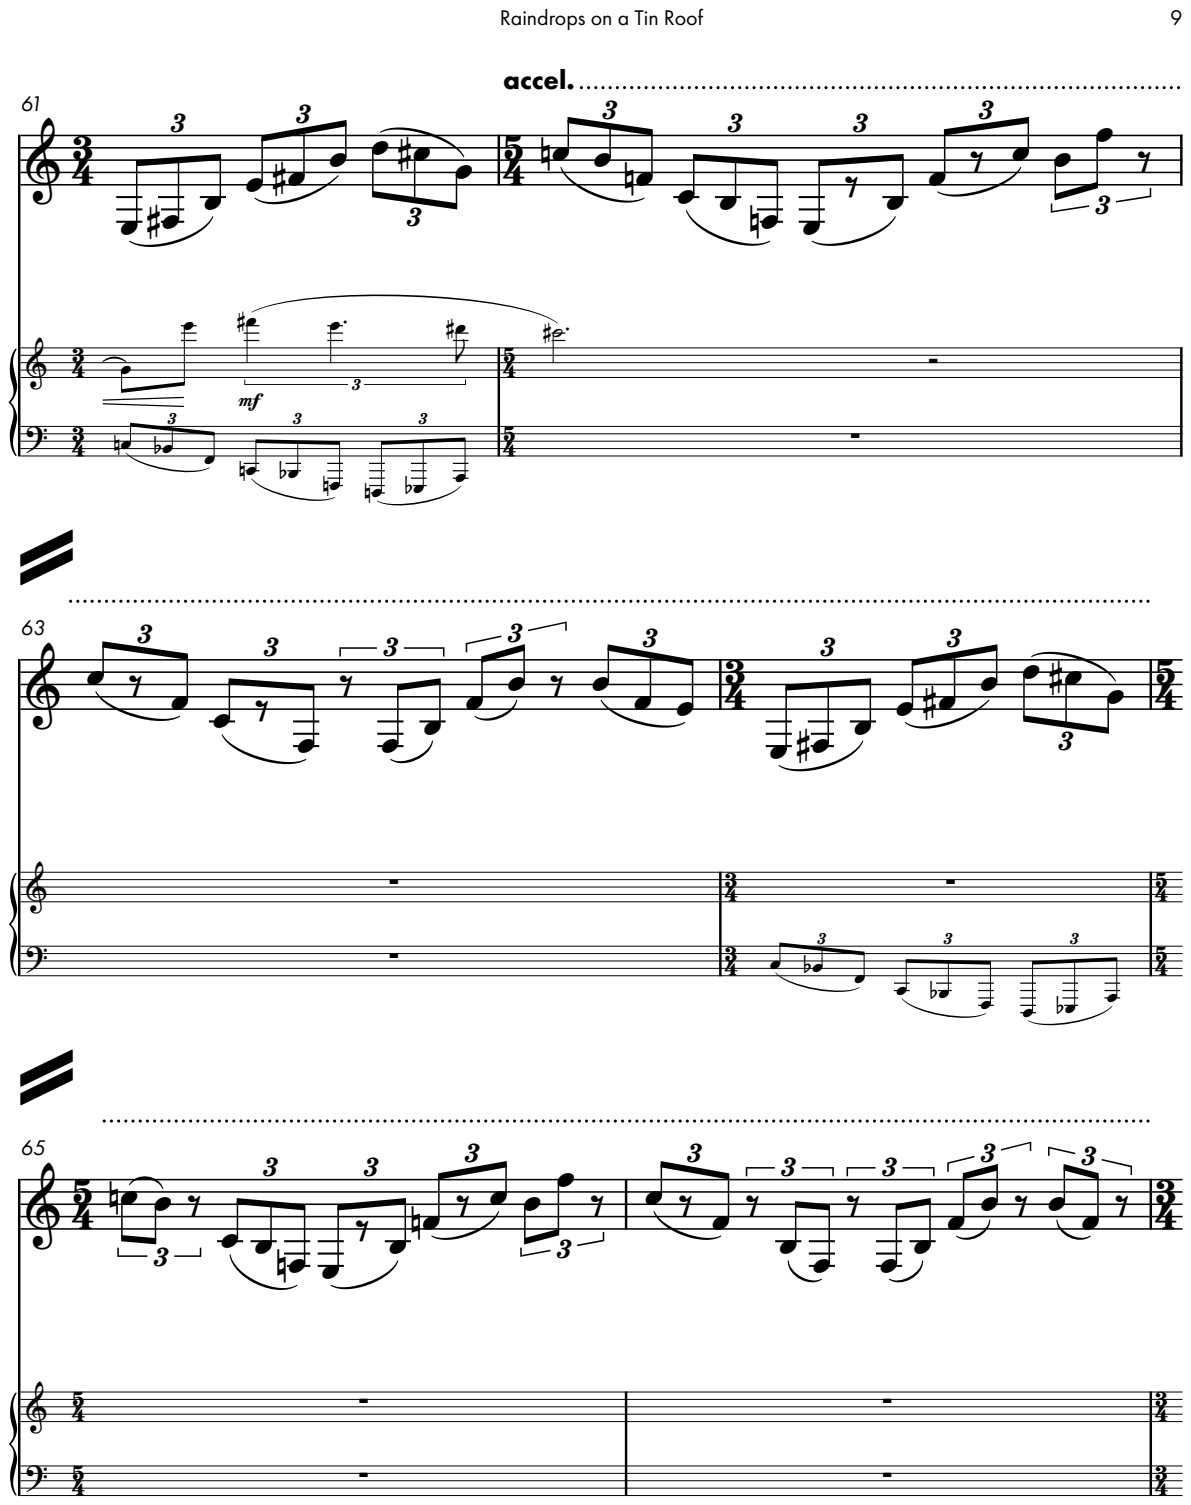
[picture p289: page 9]

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

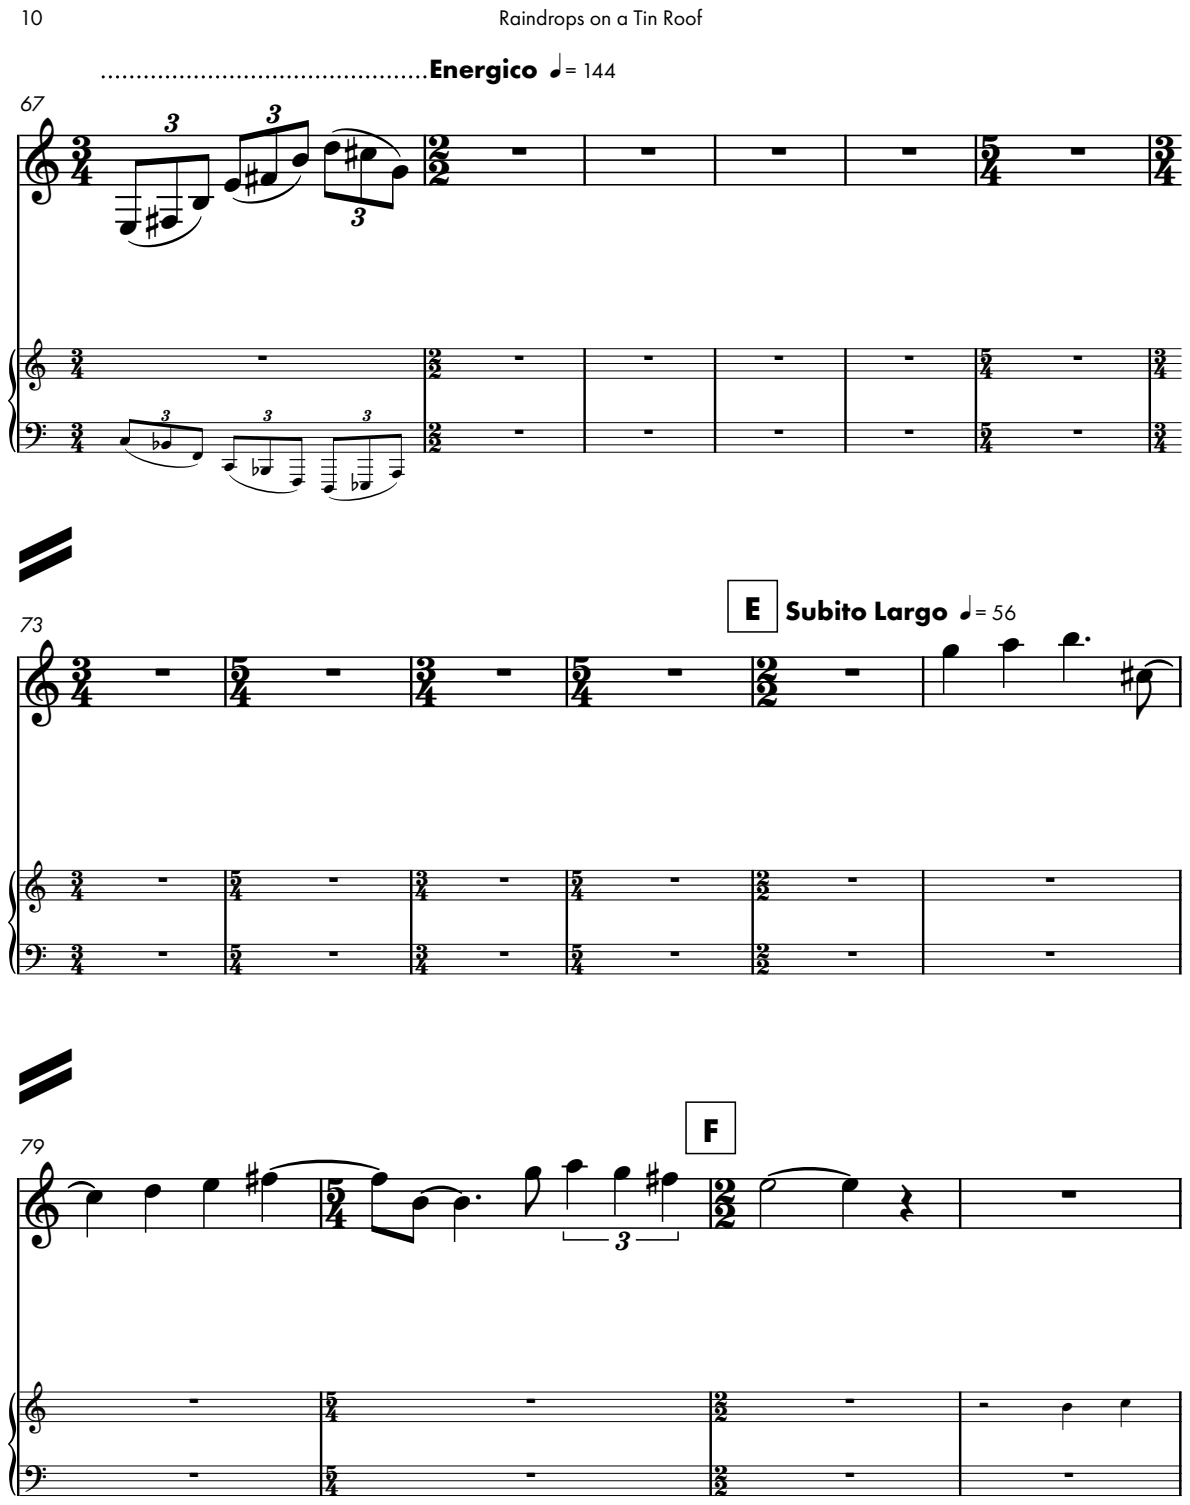
[picture p290: page 10]

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

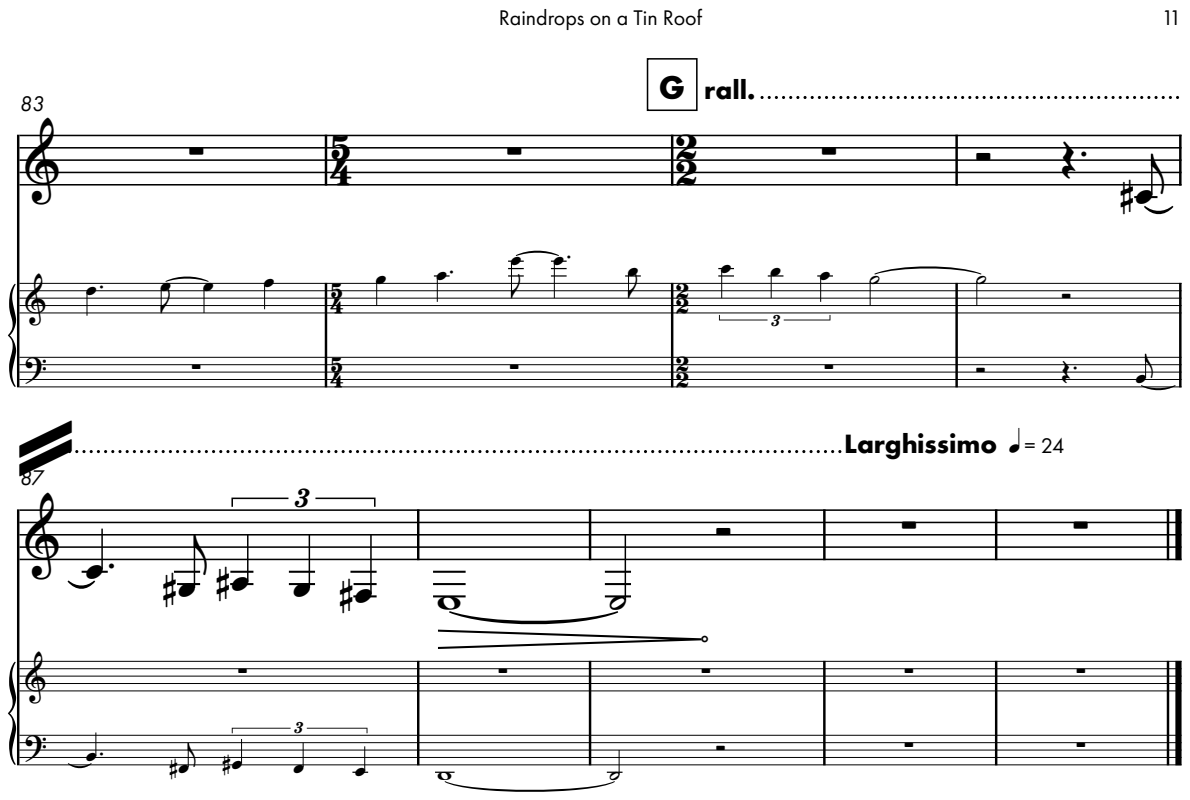
[picture p291: page 11]
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
