mbardin/Cyberinet/zMusic Composition Scores/scores/materials/raindrops/planning diagrams/WORK IN PROGRESS.pdf

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

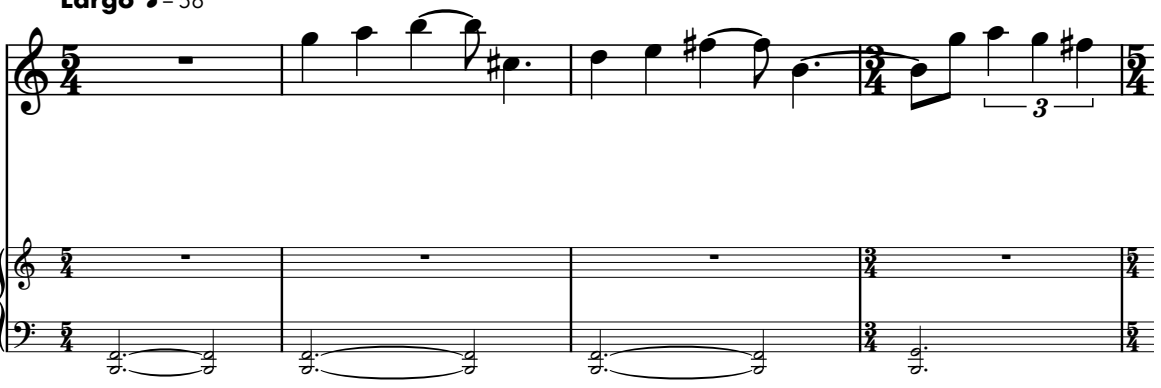
[picture p292: figure]
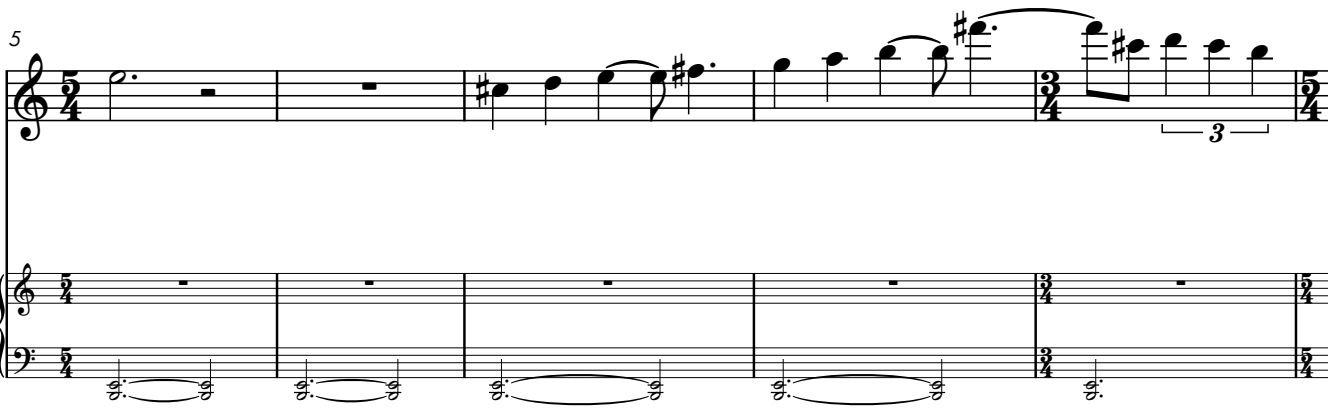
[picture p293: figure]
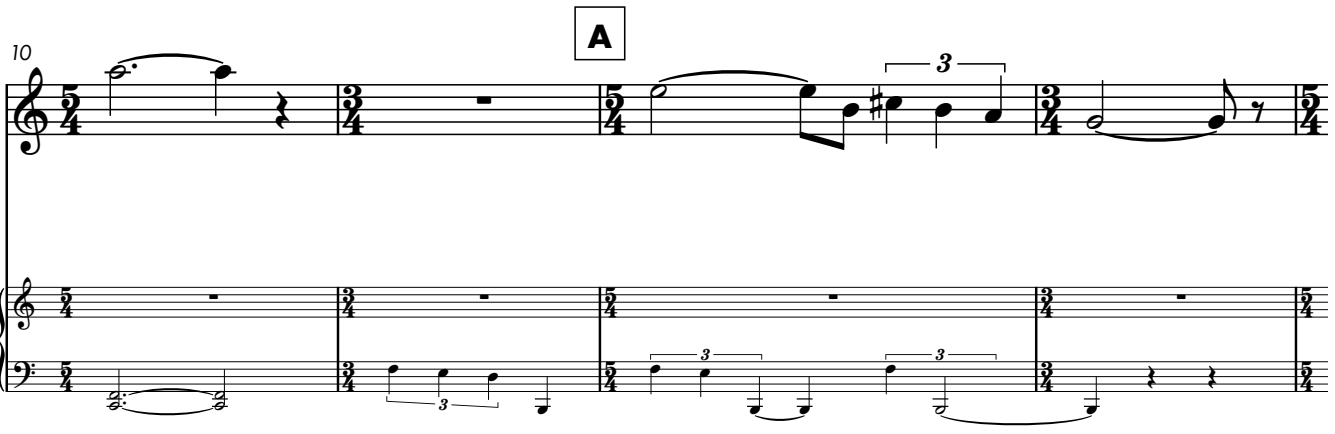
[picture p294: figure]

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

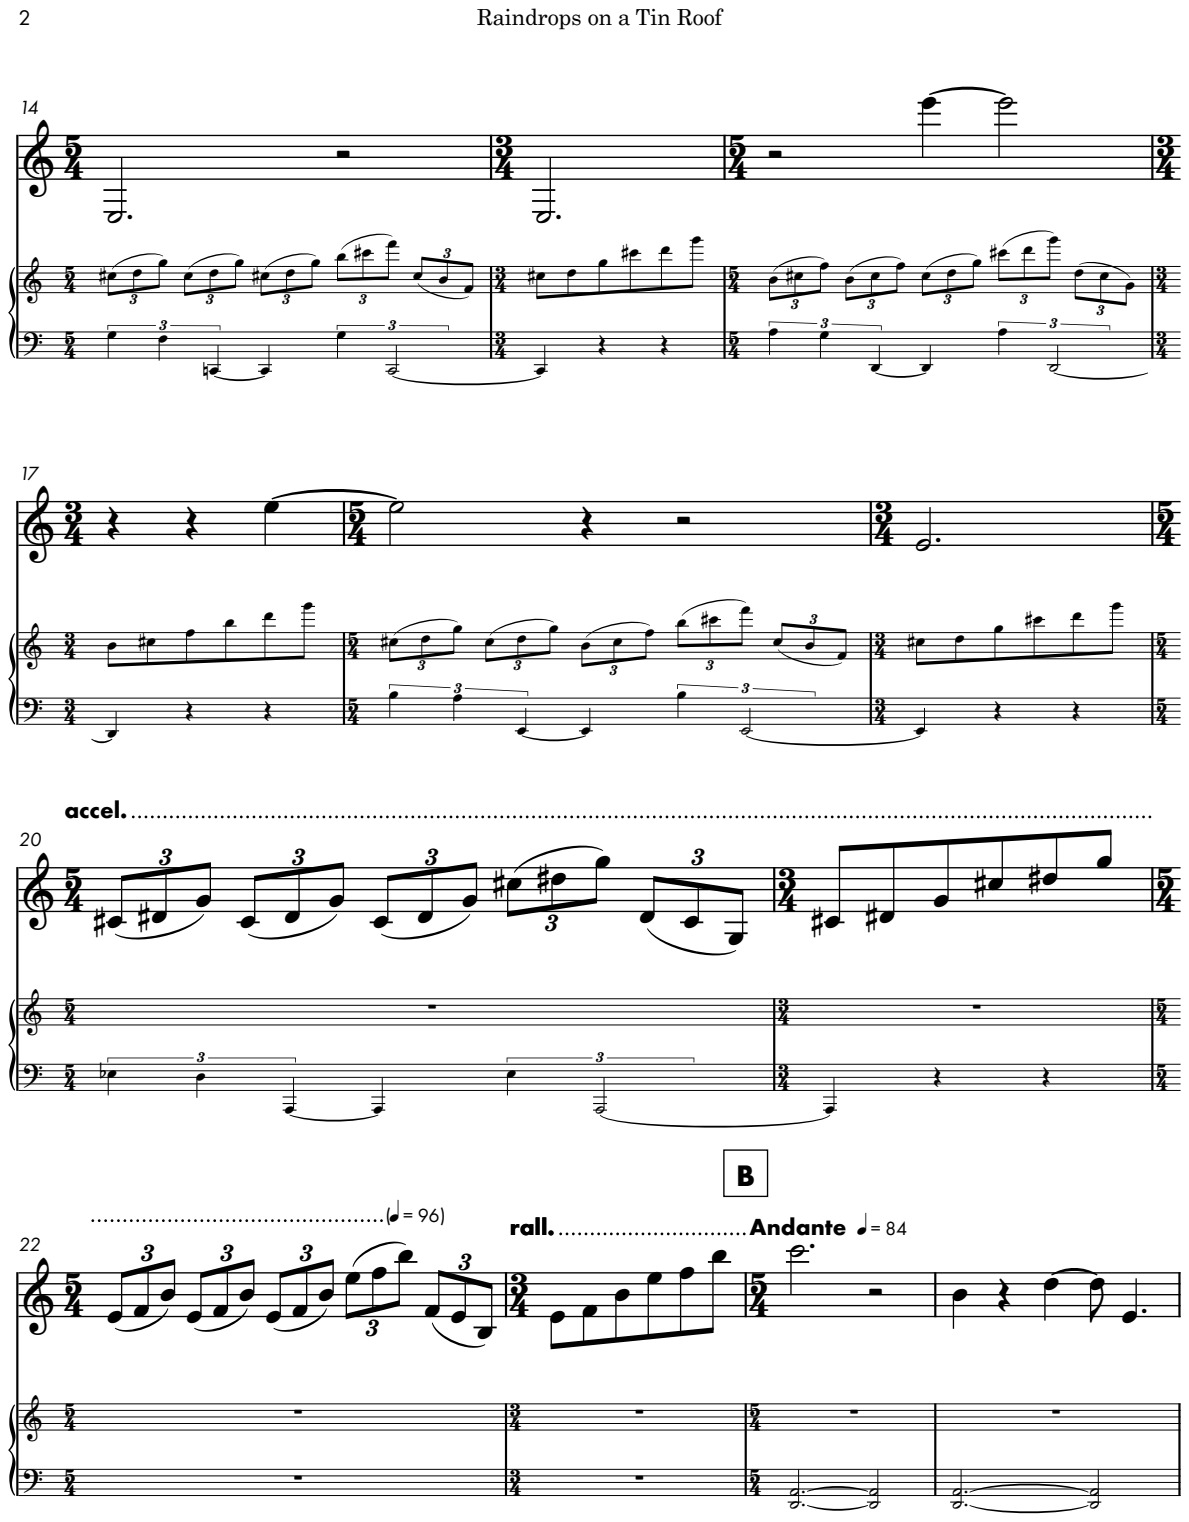
[picture p295: page 2]

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

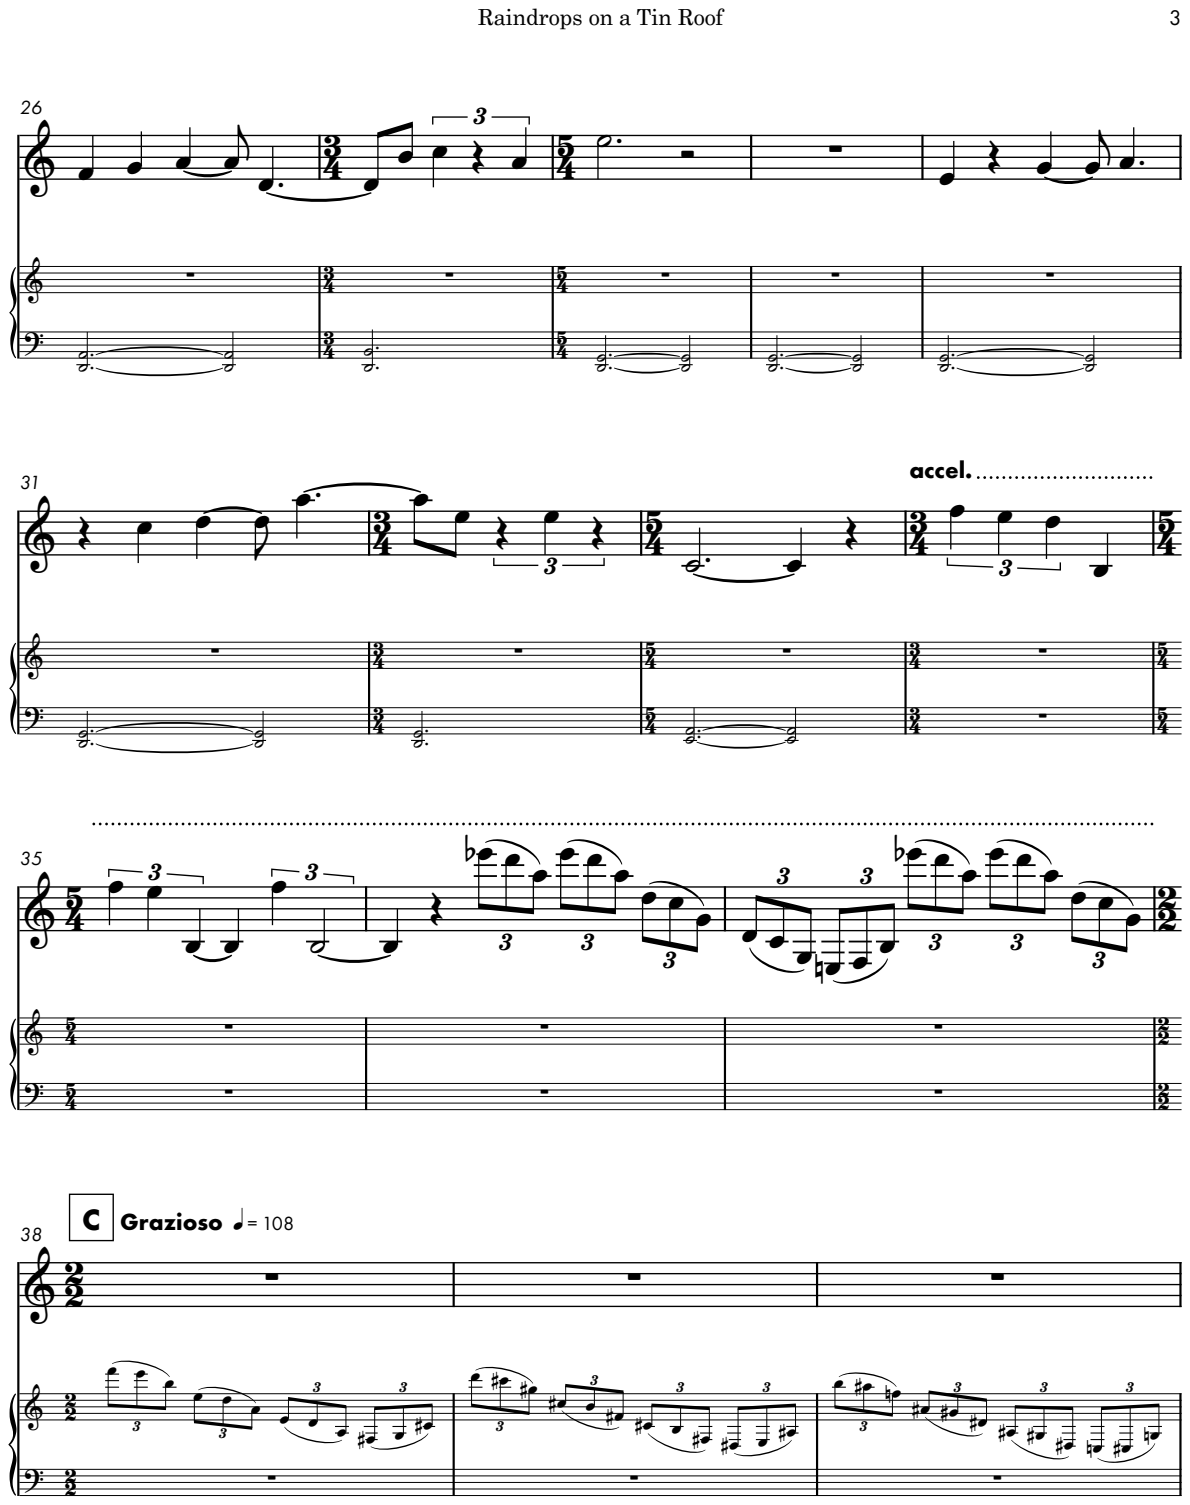
[picture p296: page 3]

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

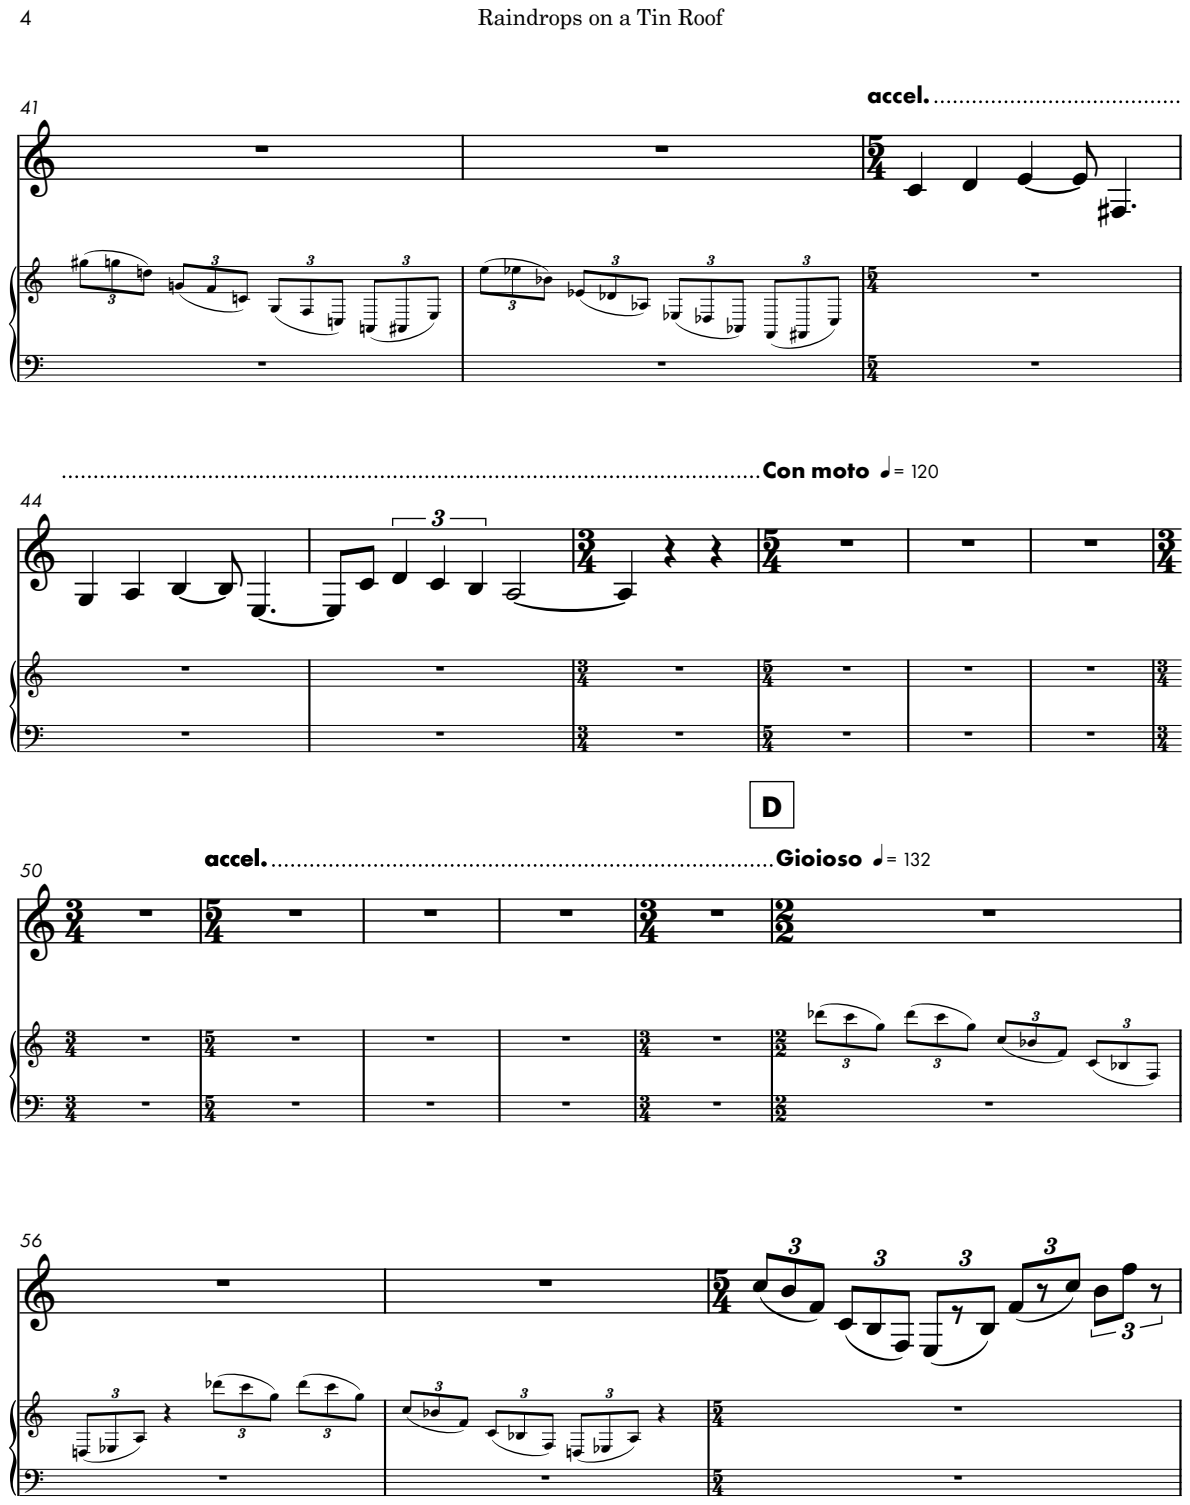
[picture p297: page 4]

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

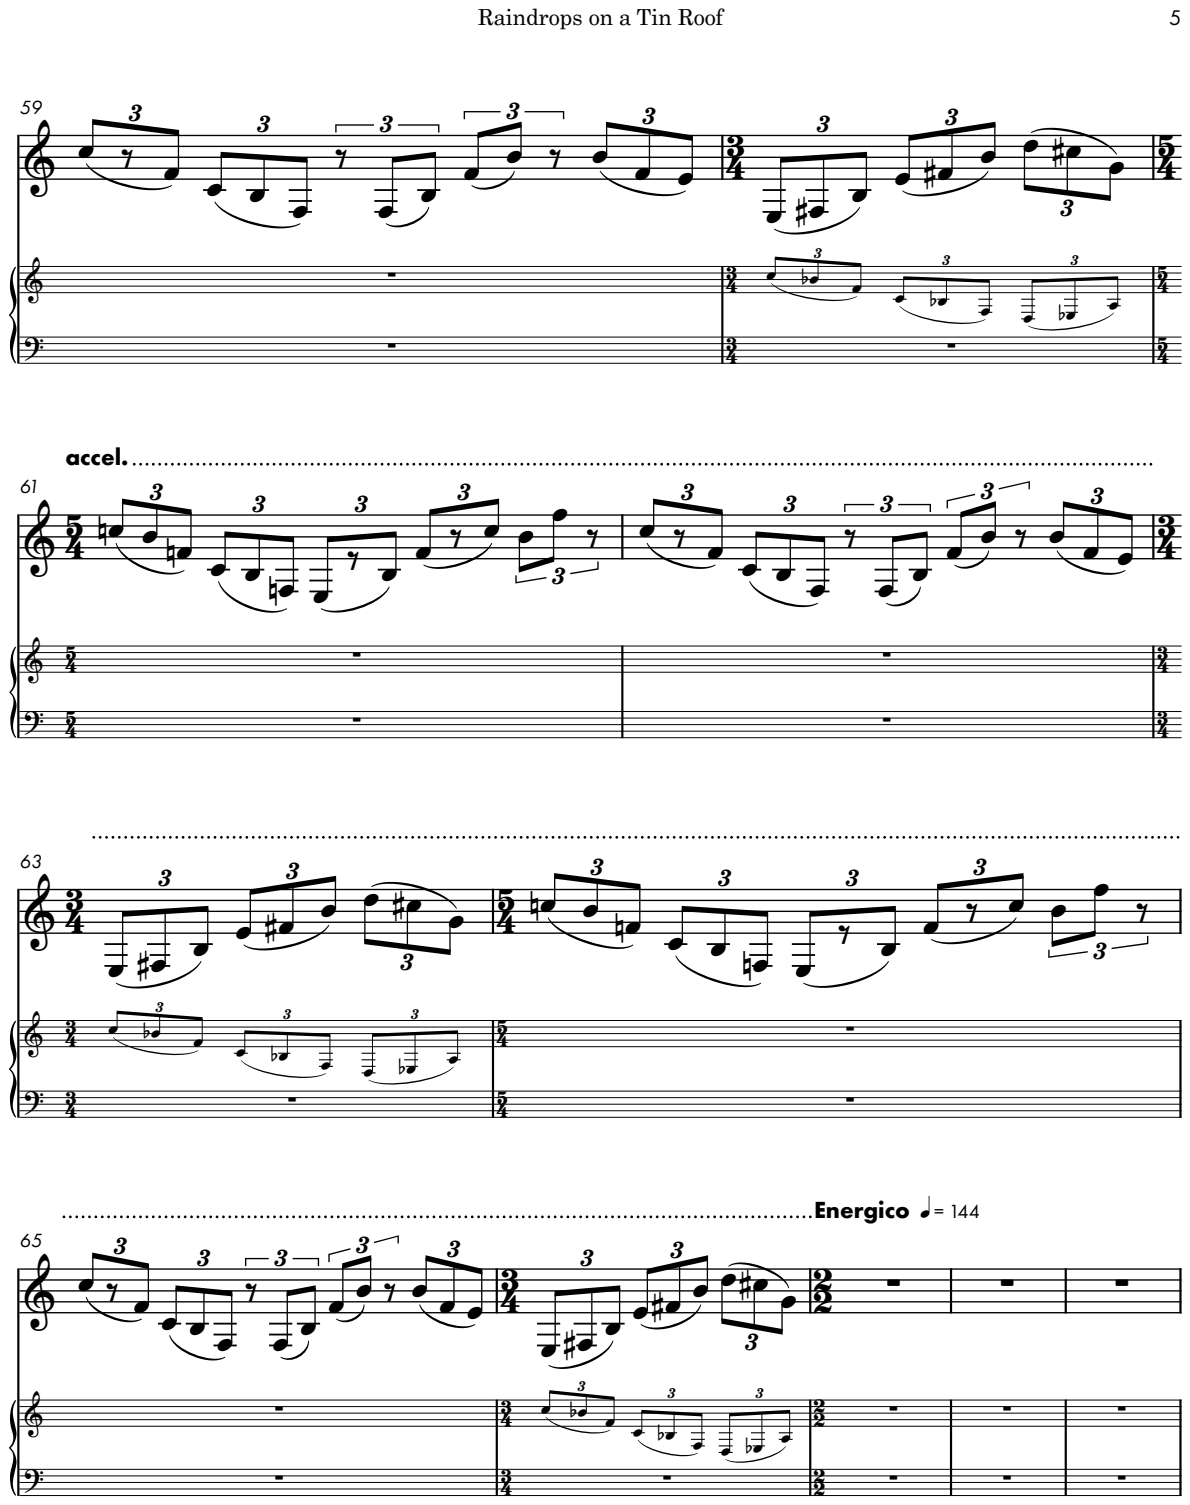
[picture p298: page 5]

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

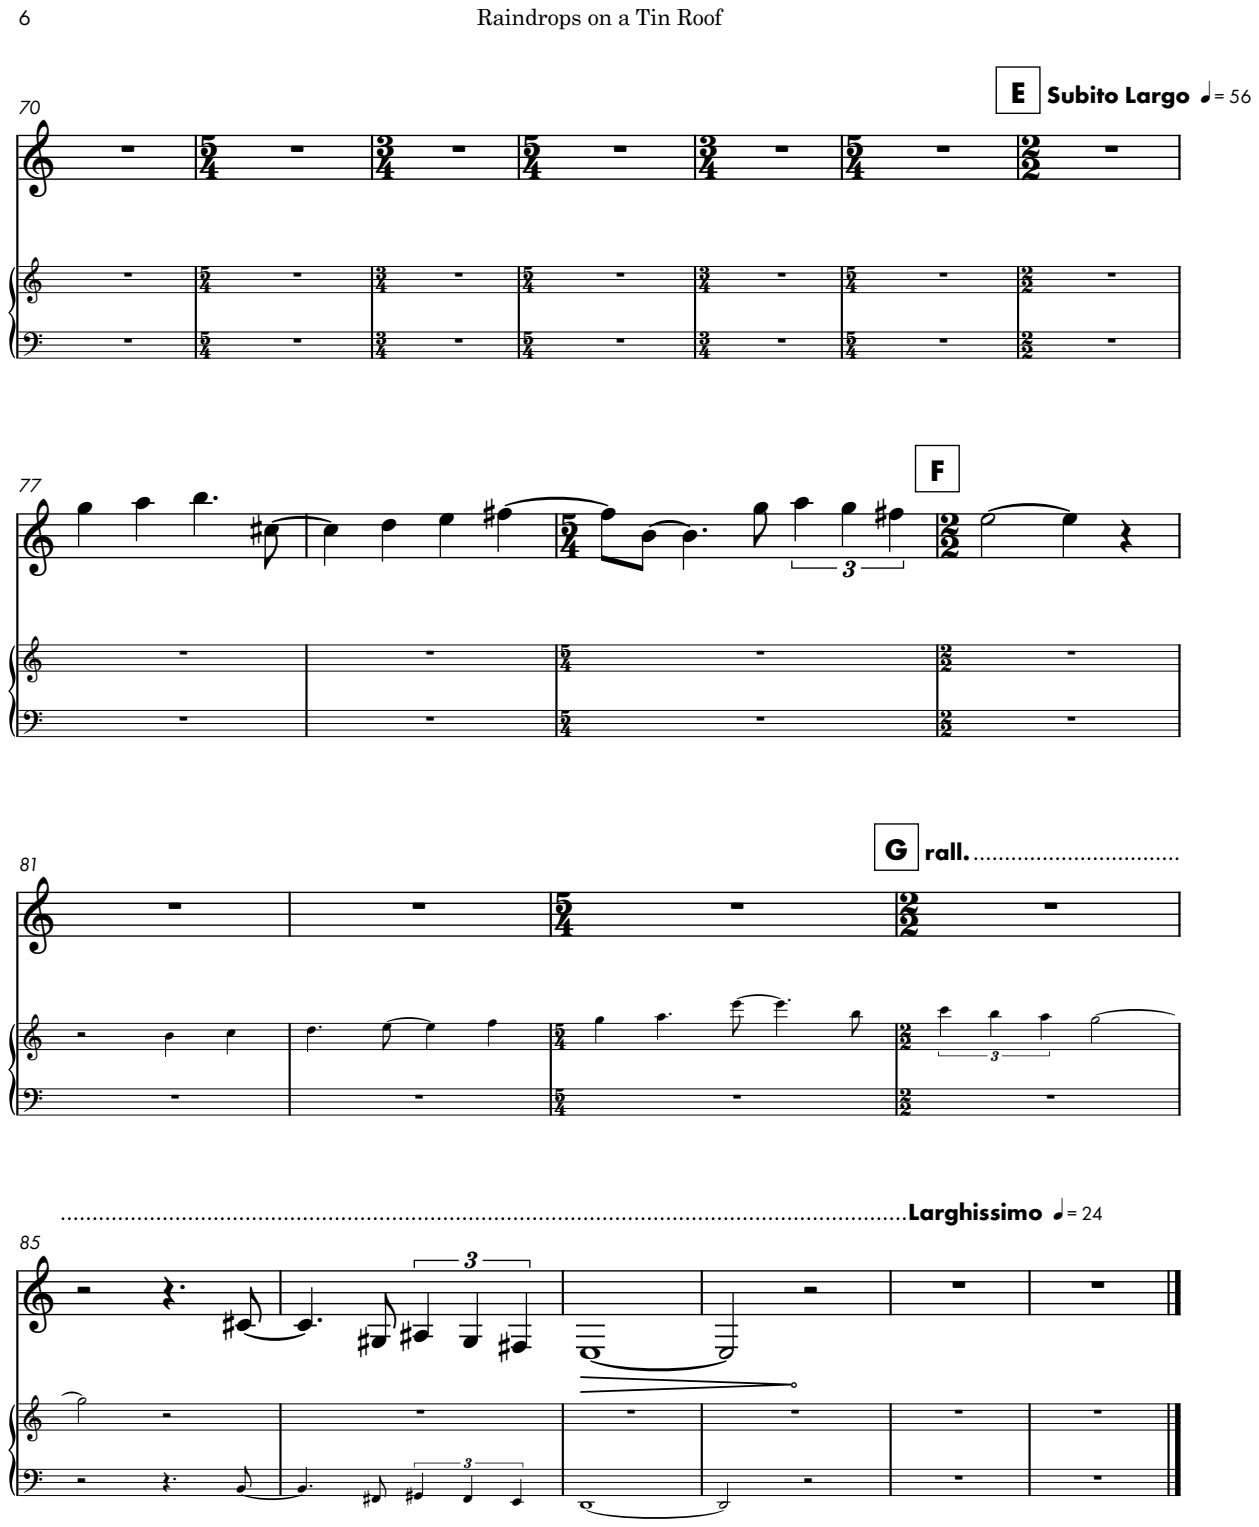
[picture p299: page 6]
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
