mbardin/Cyberinet/Music Composition Scores/raindrops/raindrops.pdf

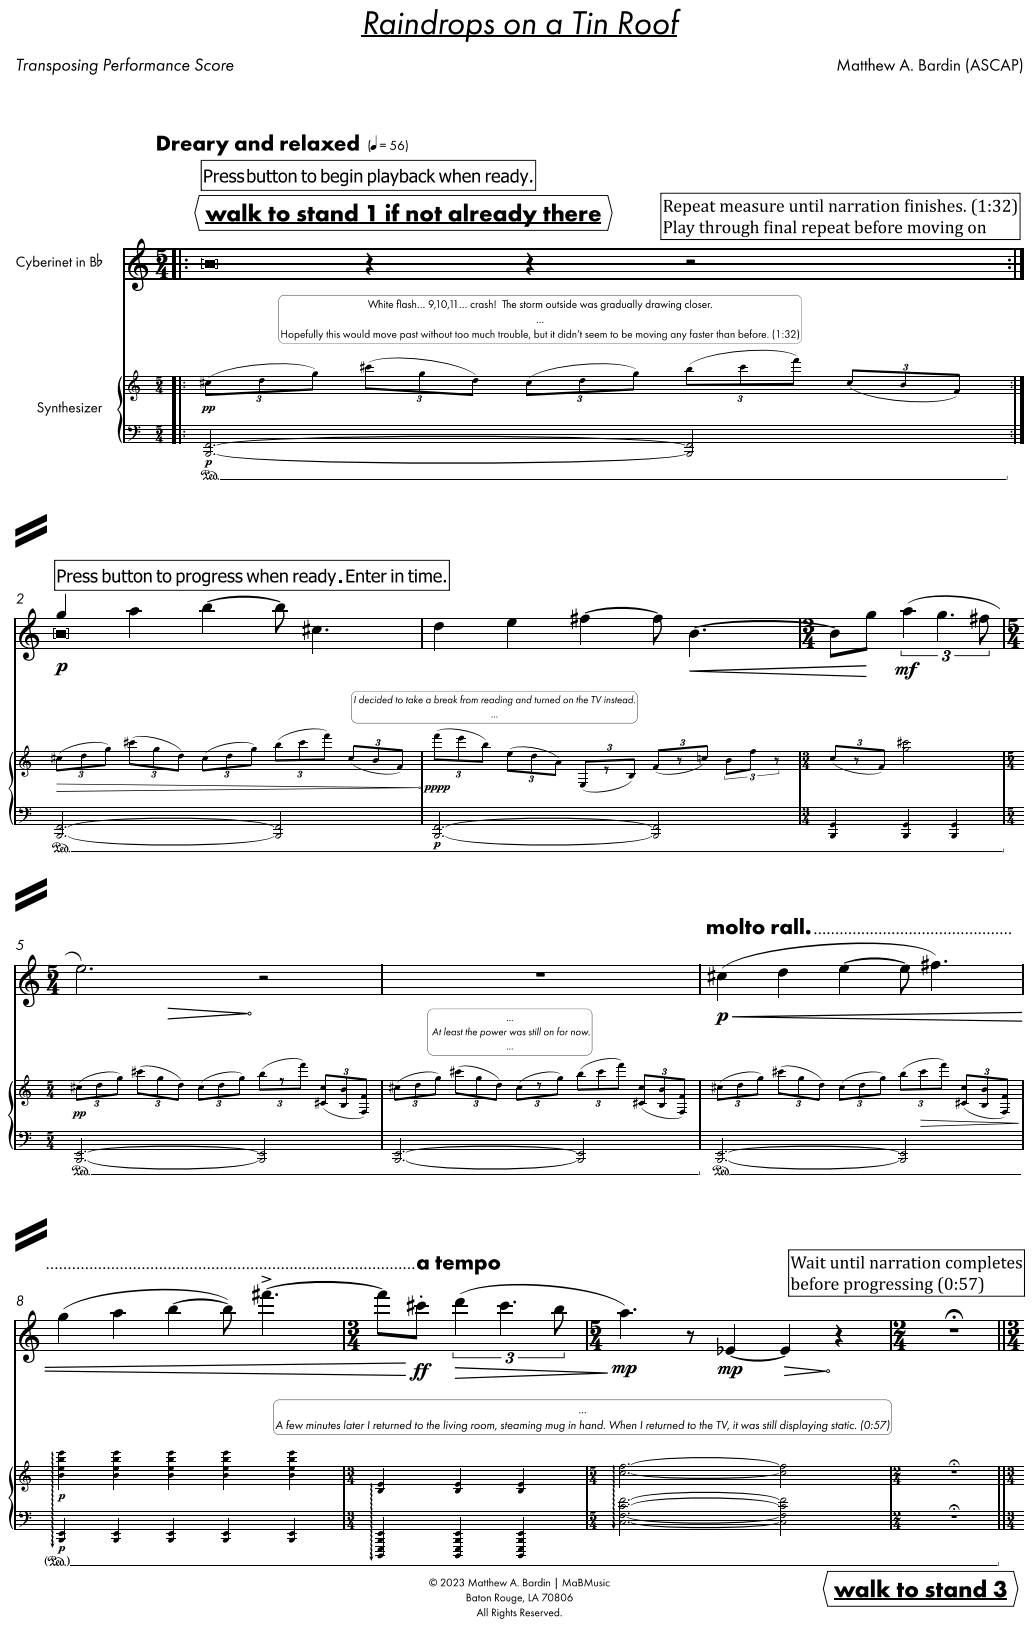
[picture p300: page 7]

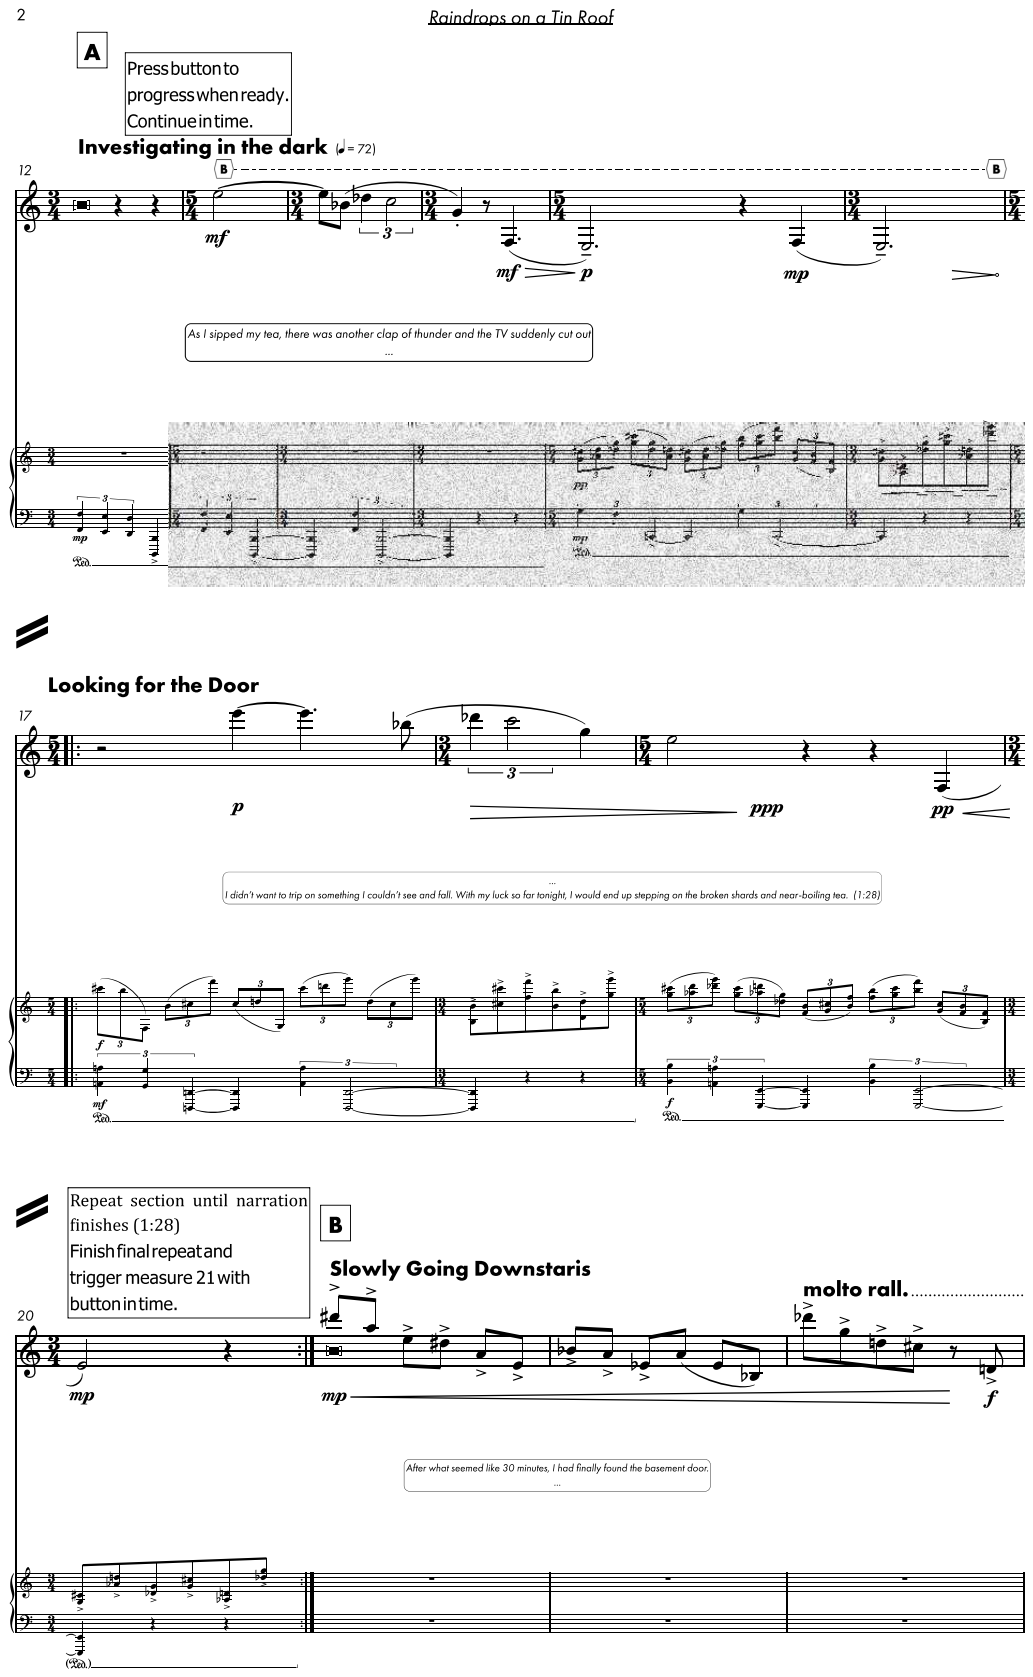
[picture p301: page 8]

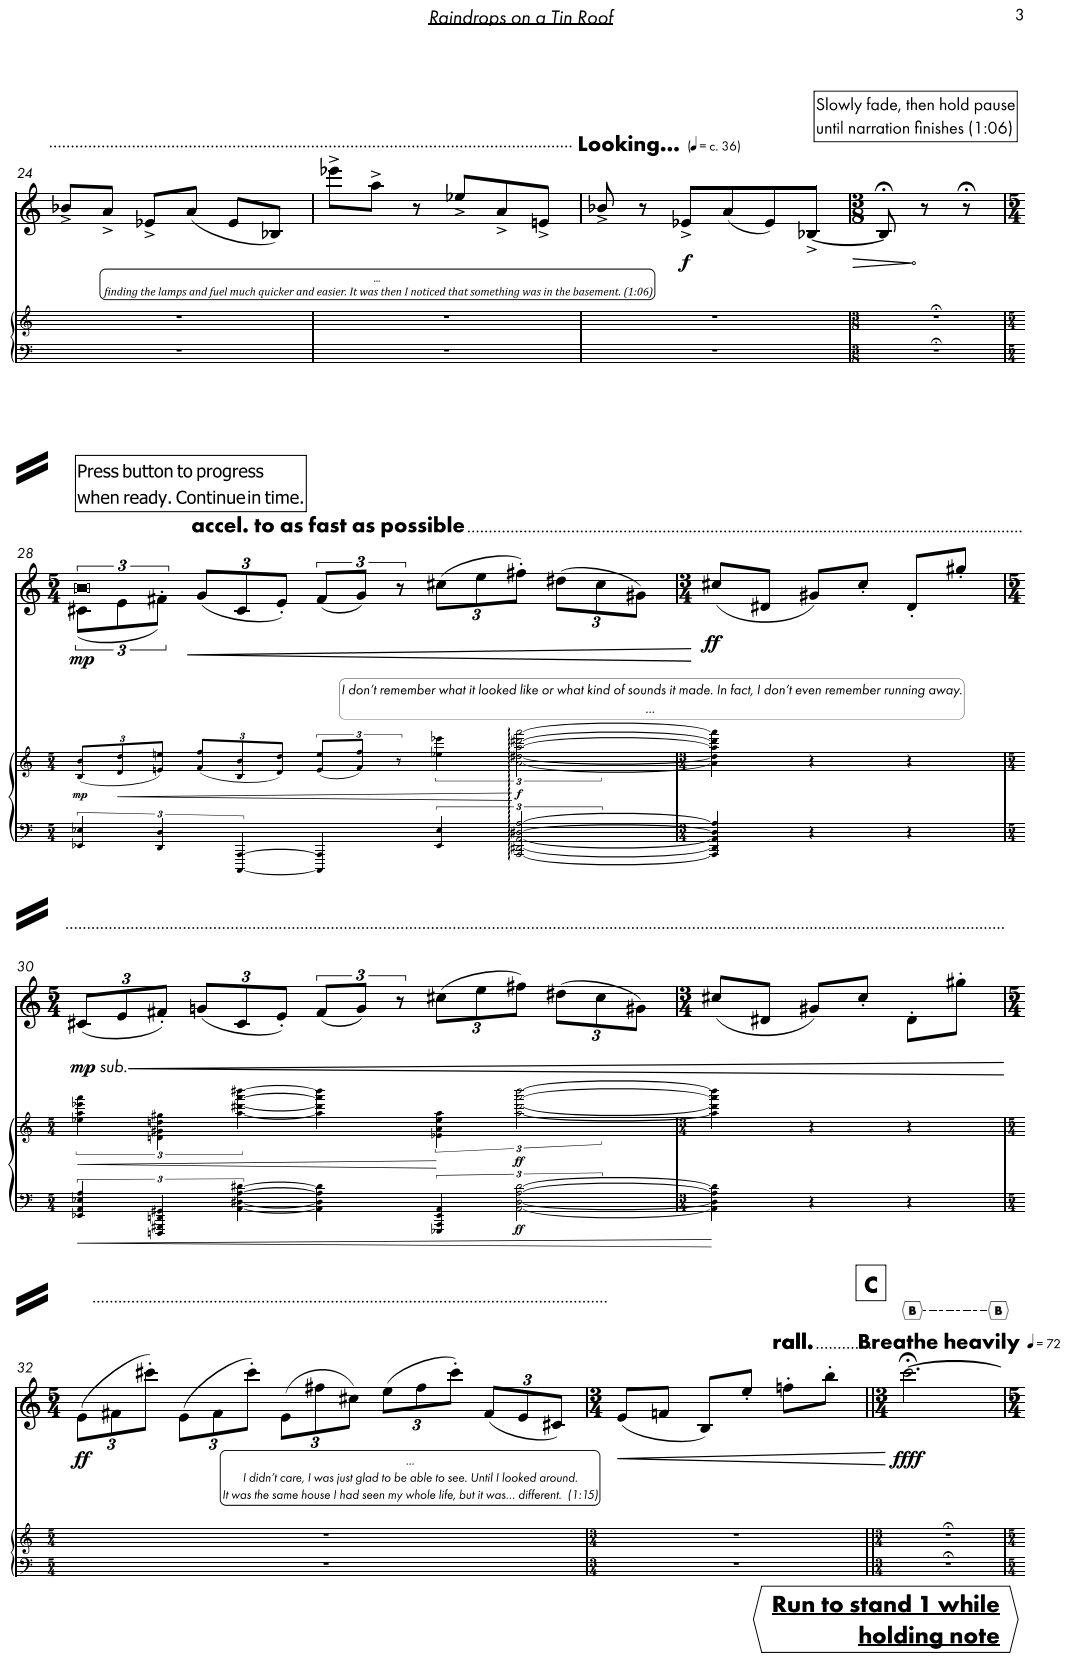
[picture p302: page 9]

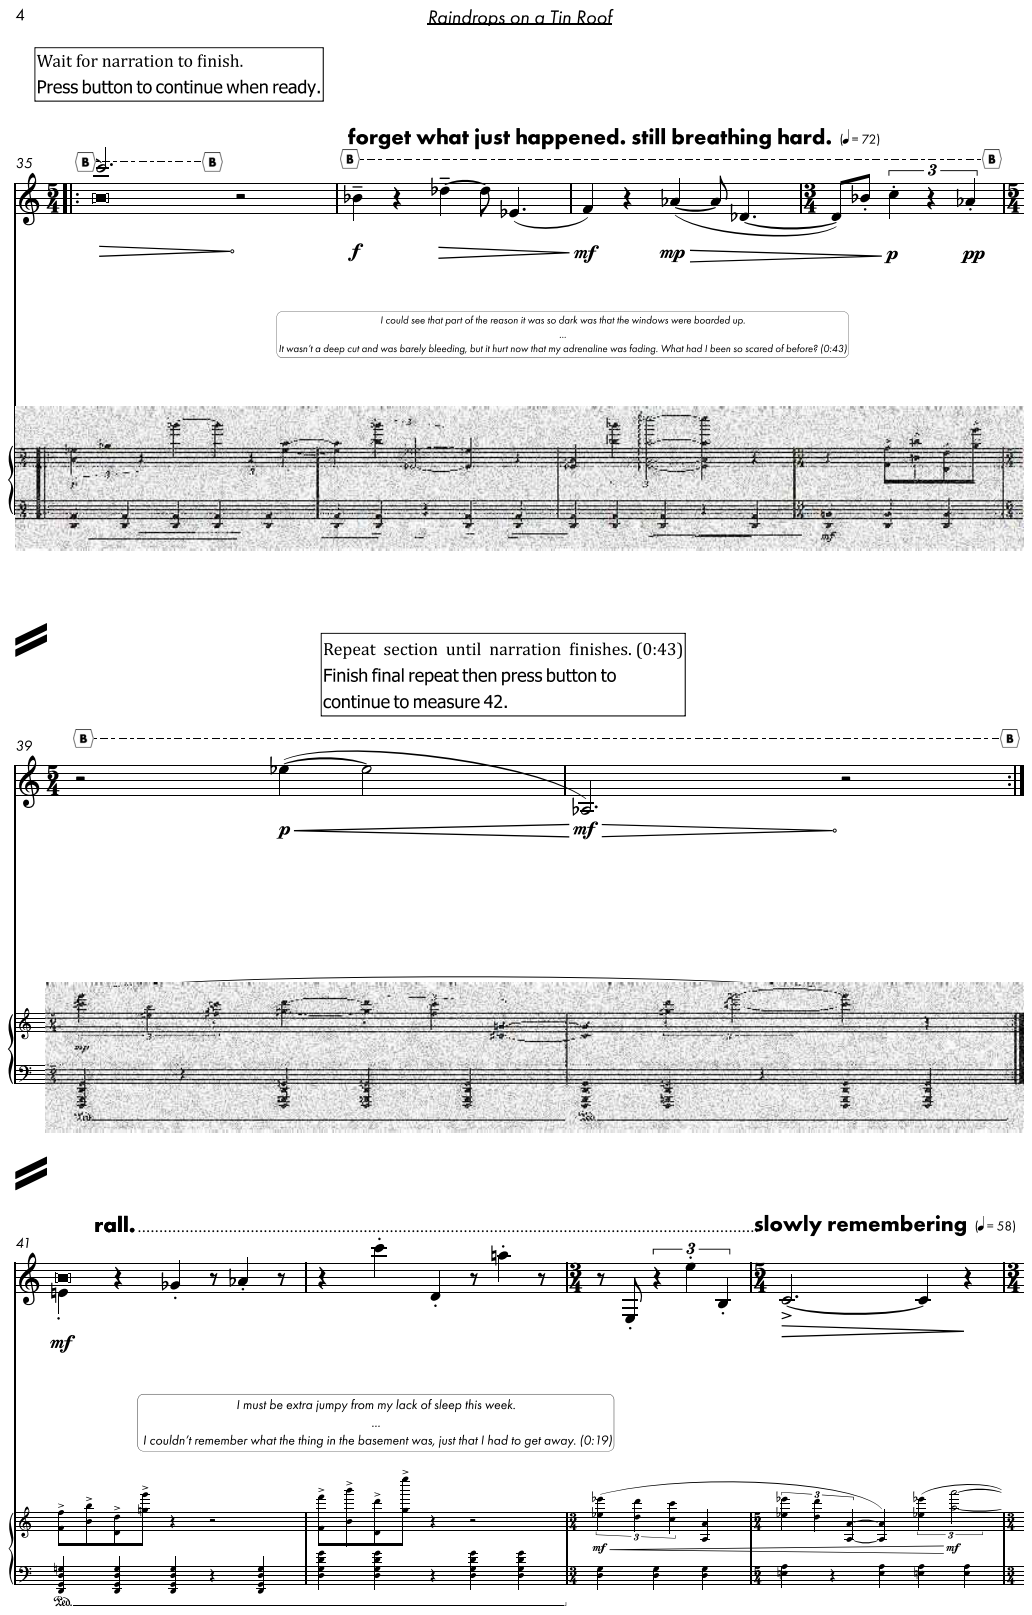
[picture p303: page 10]

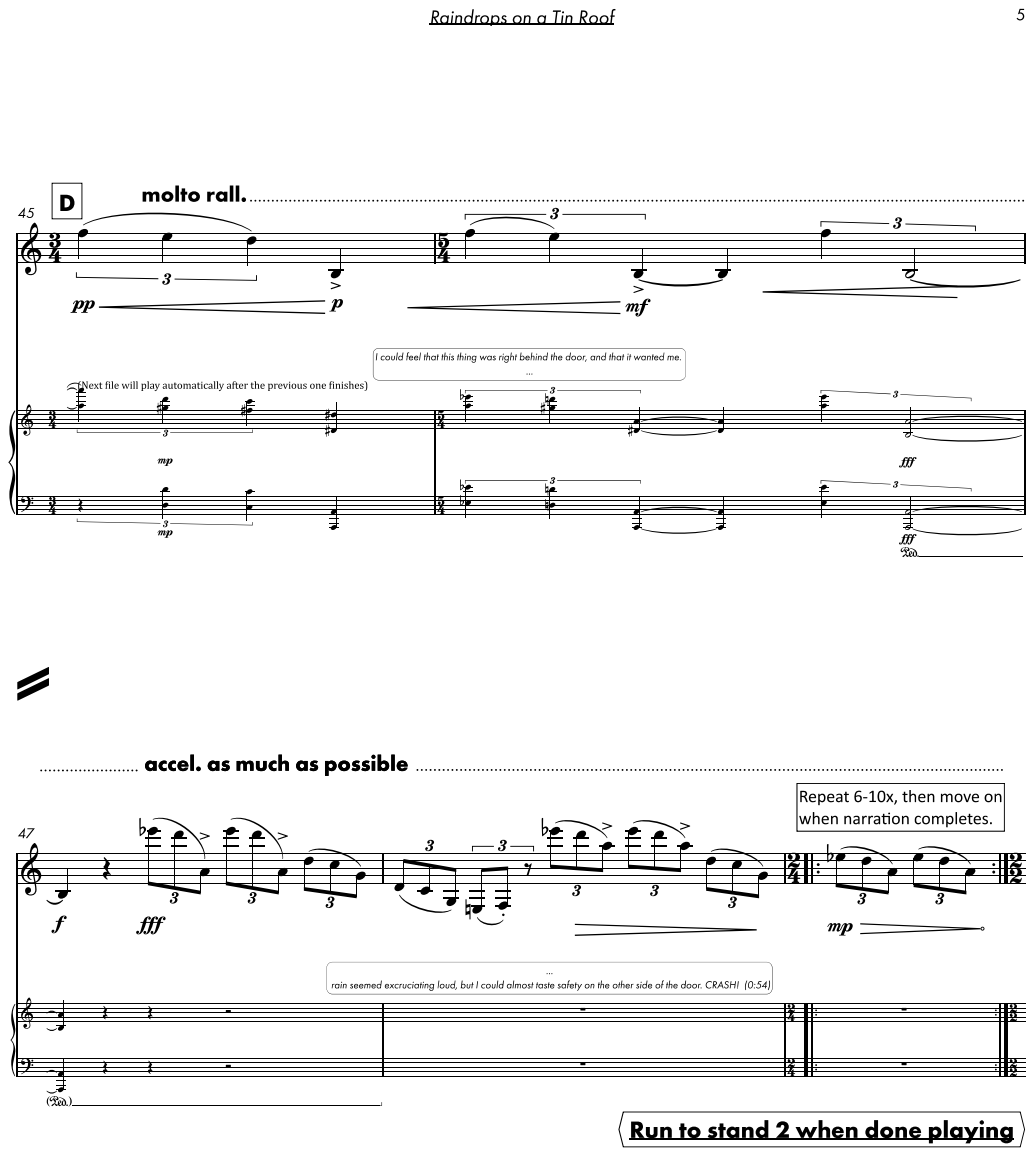
[picture p304: page 11]

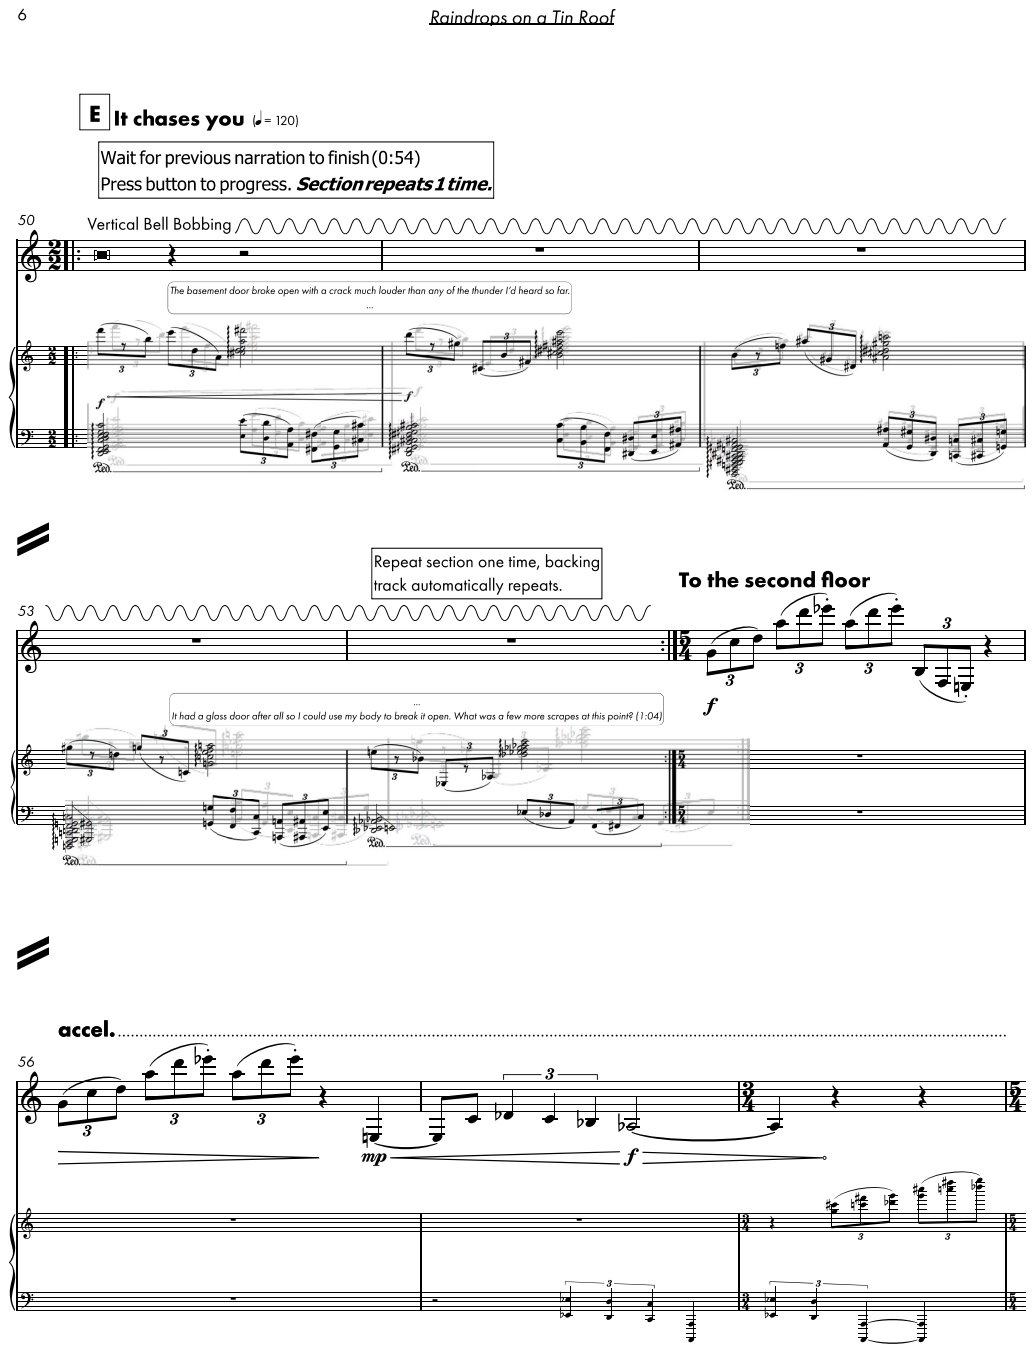
[picture p305: page 12]

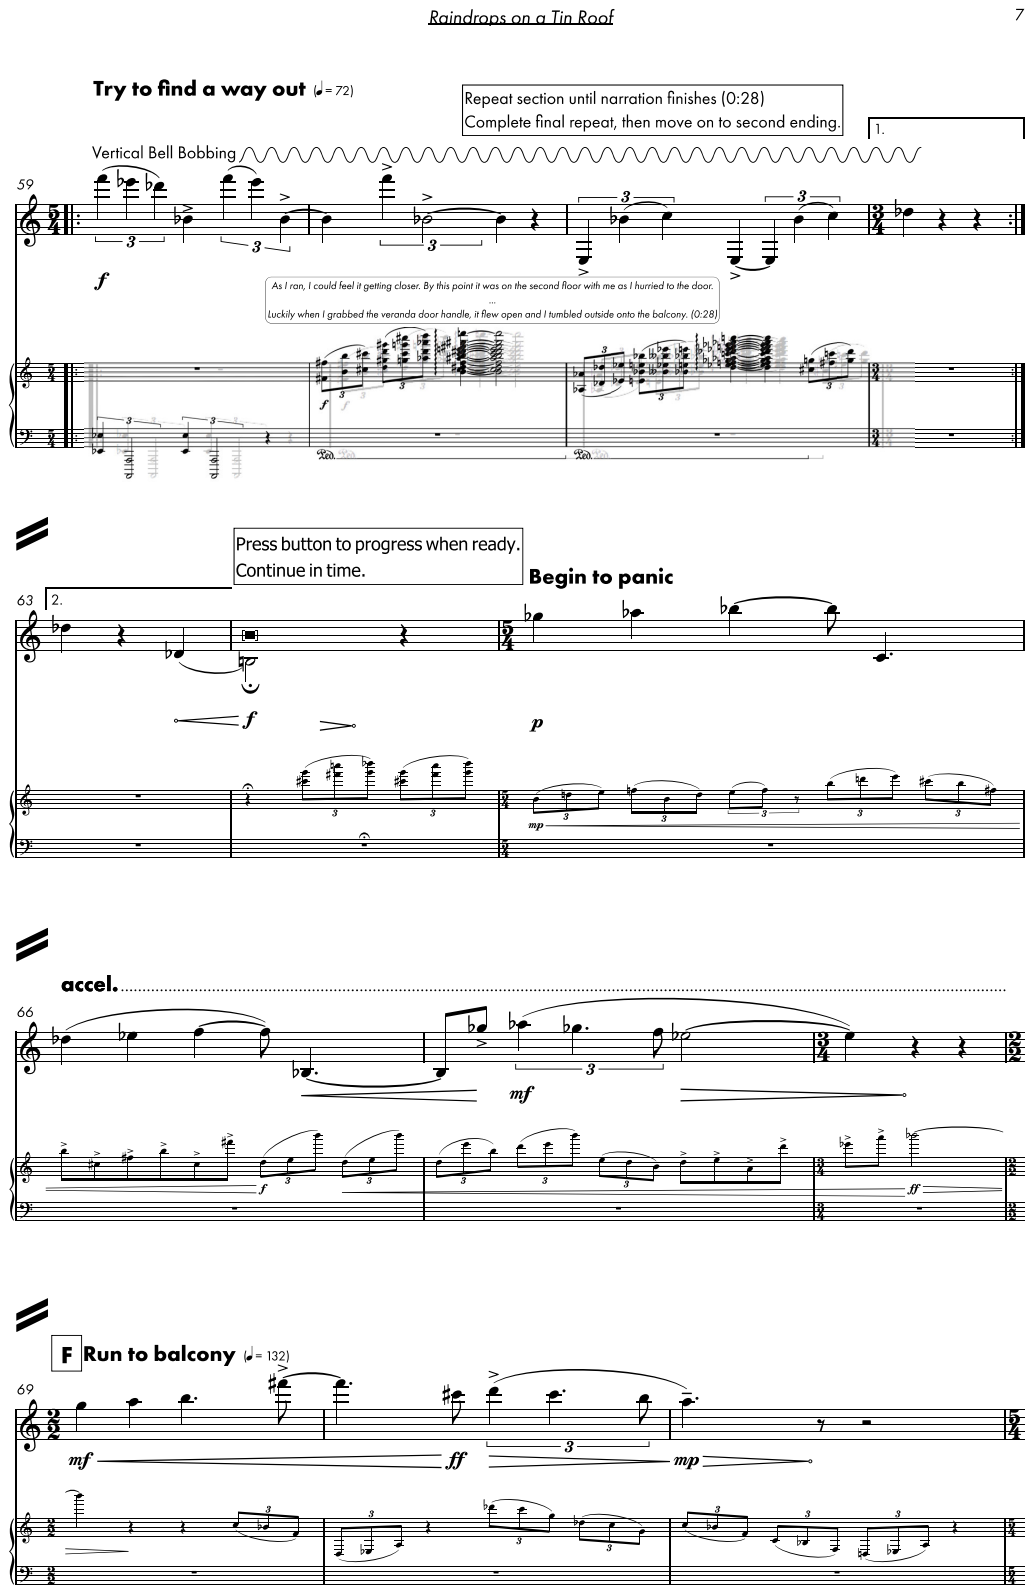
[picture p306: page 13]

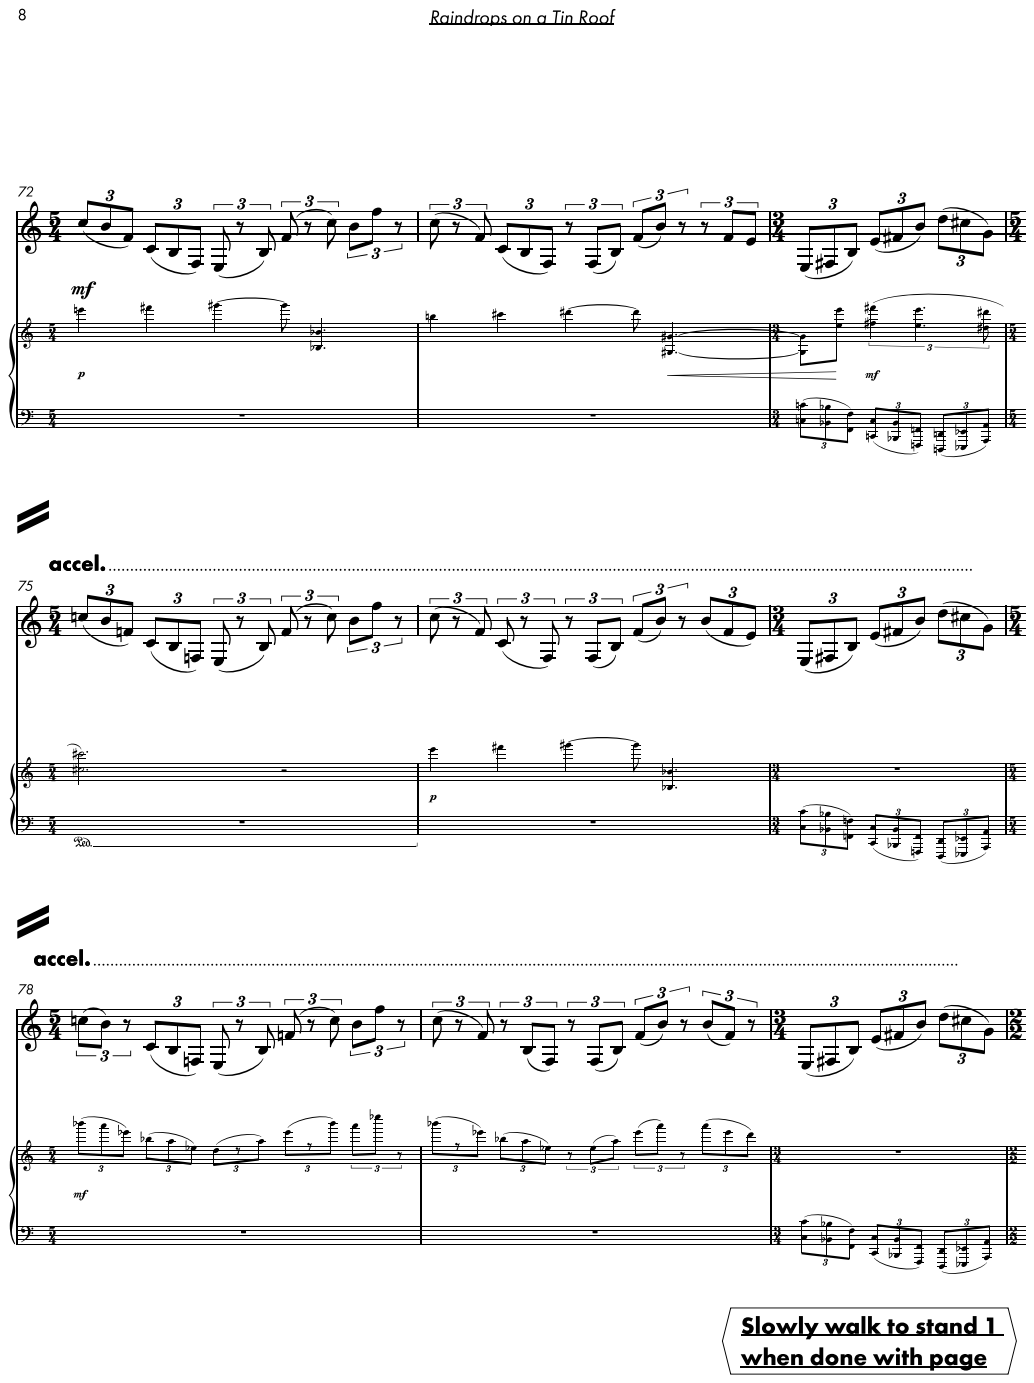
[picture p307: page 14]

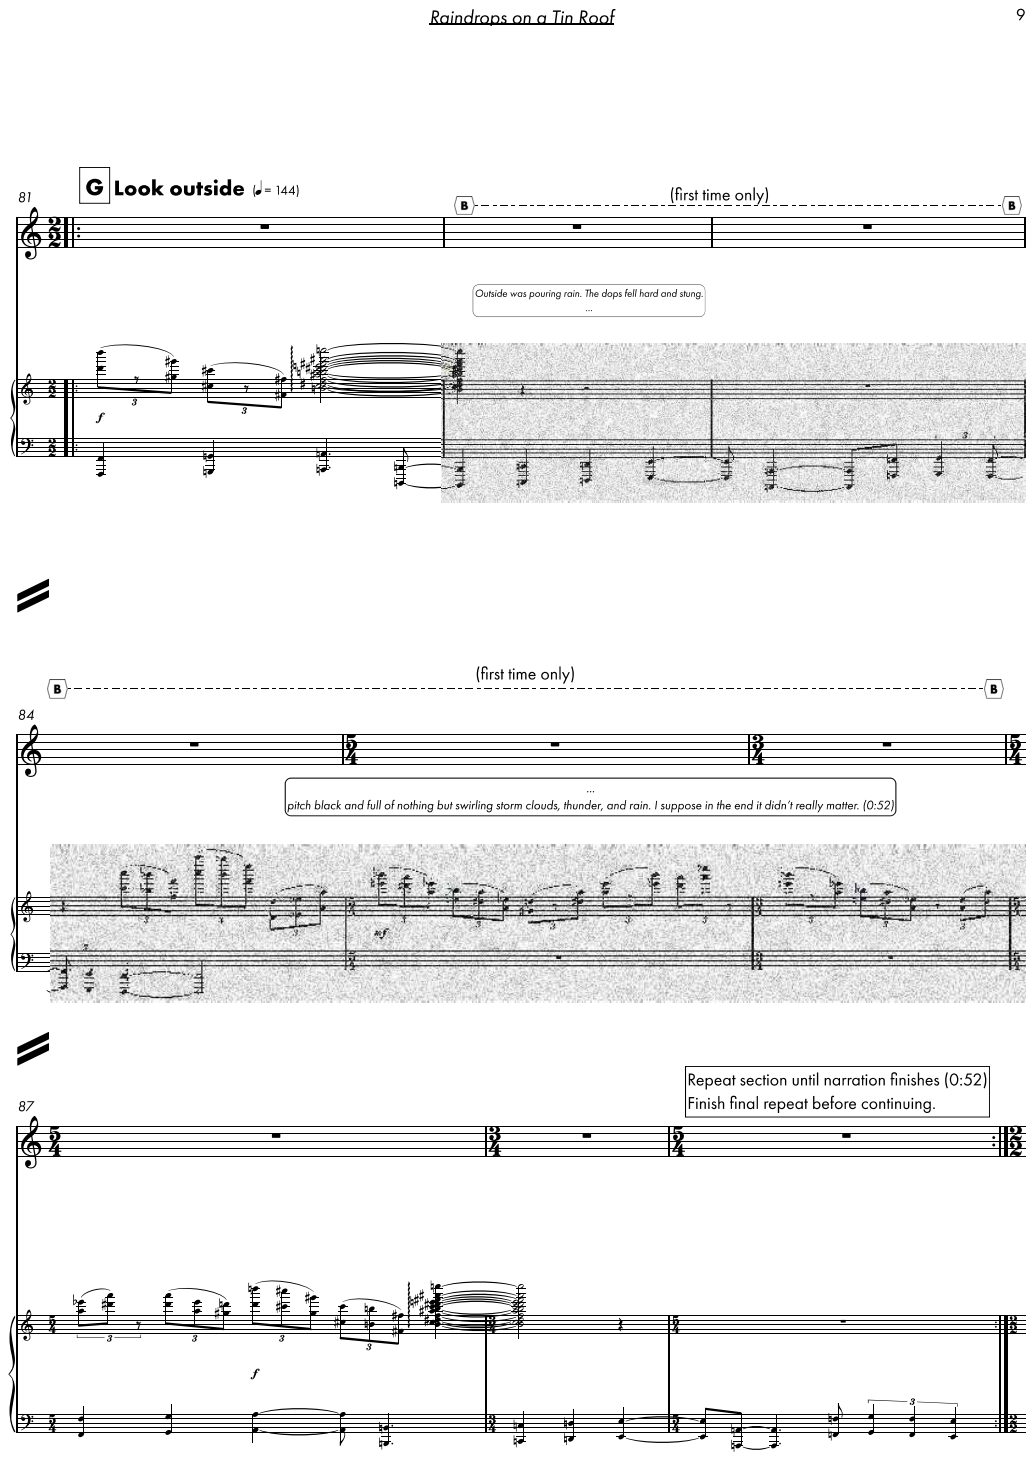
[picture p308: page 15]

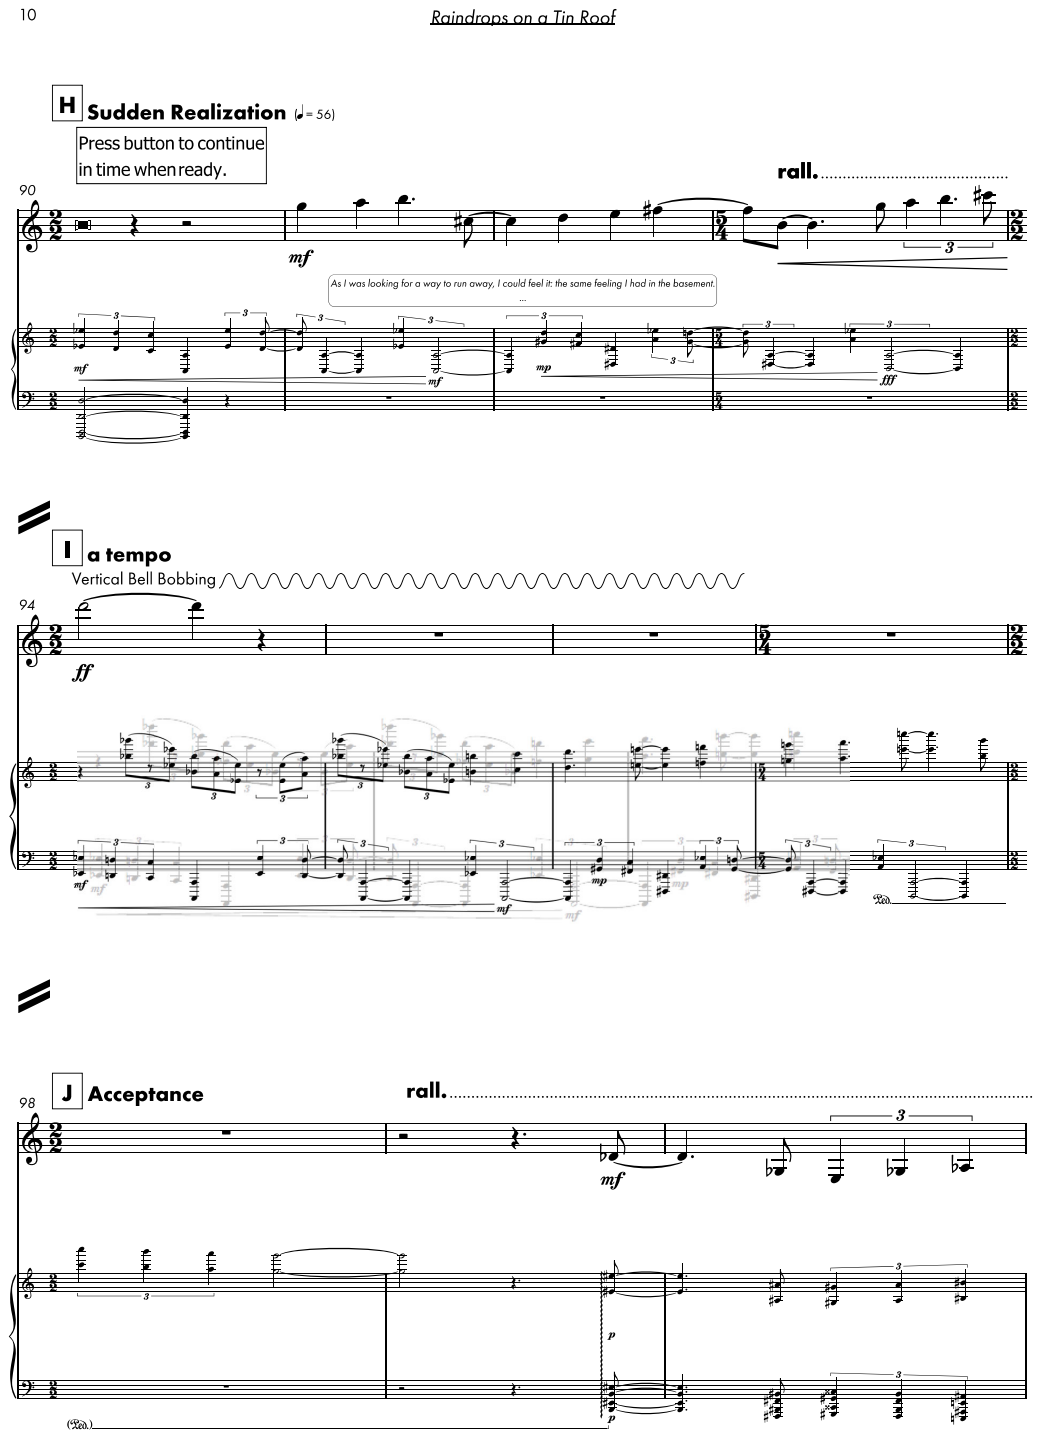
[picture p309: page 16]

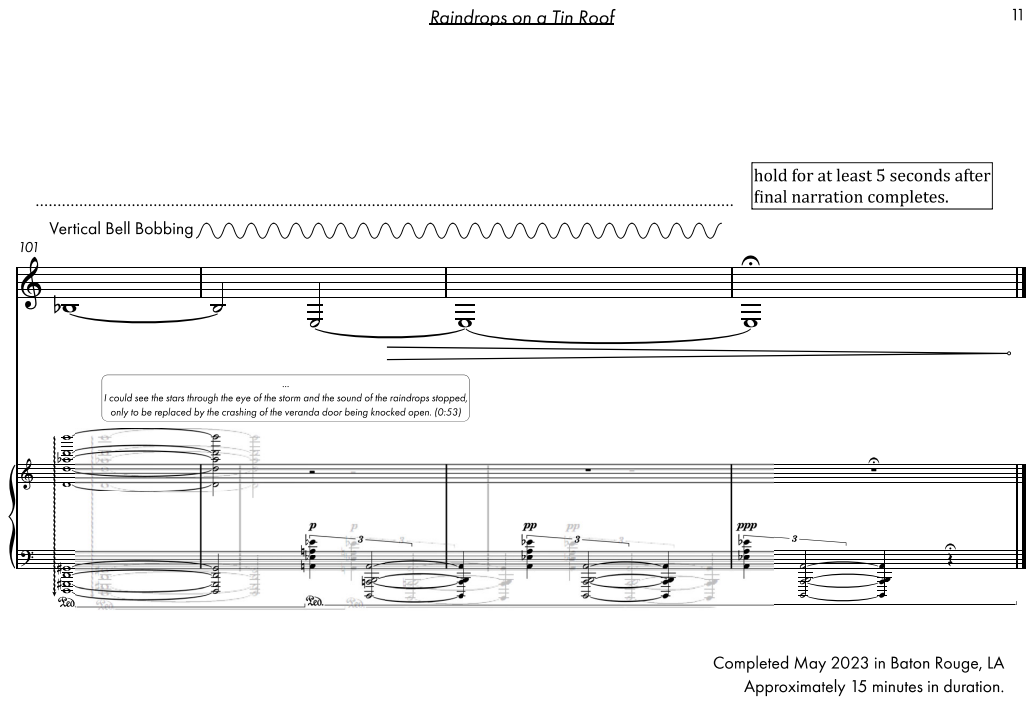
[picture p310: page 17]


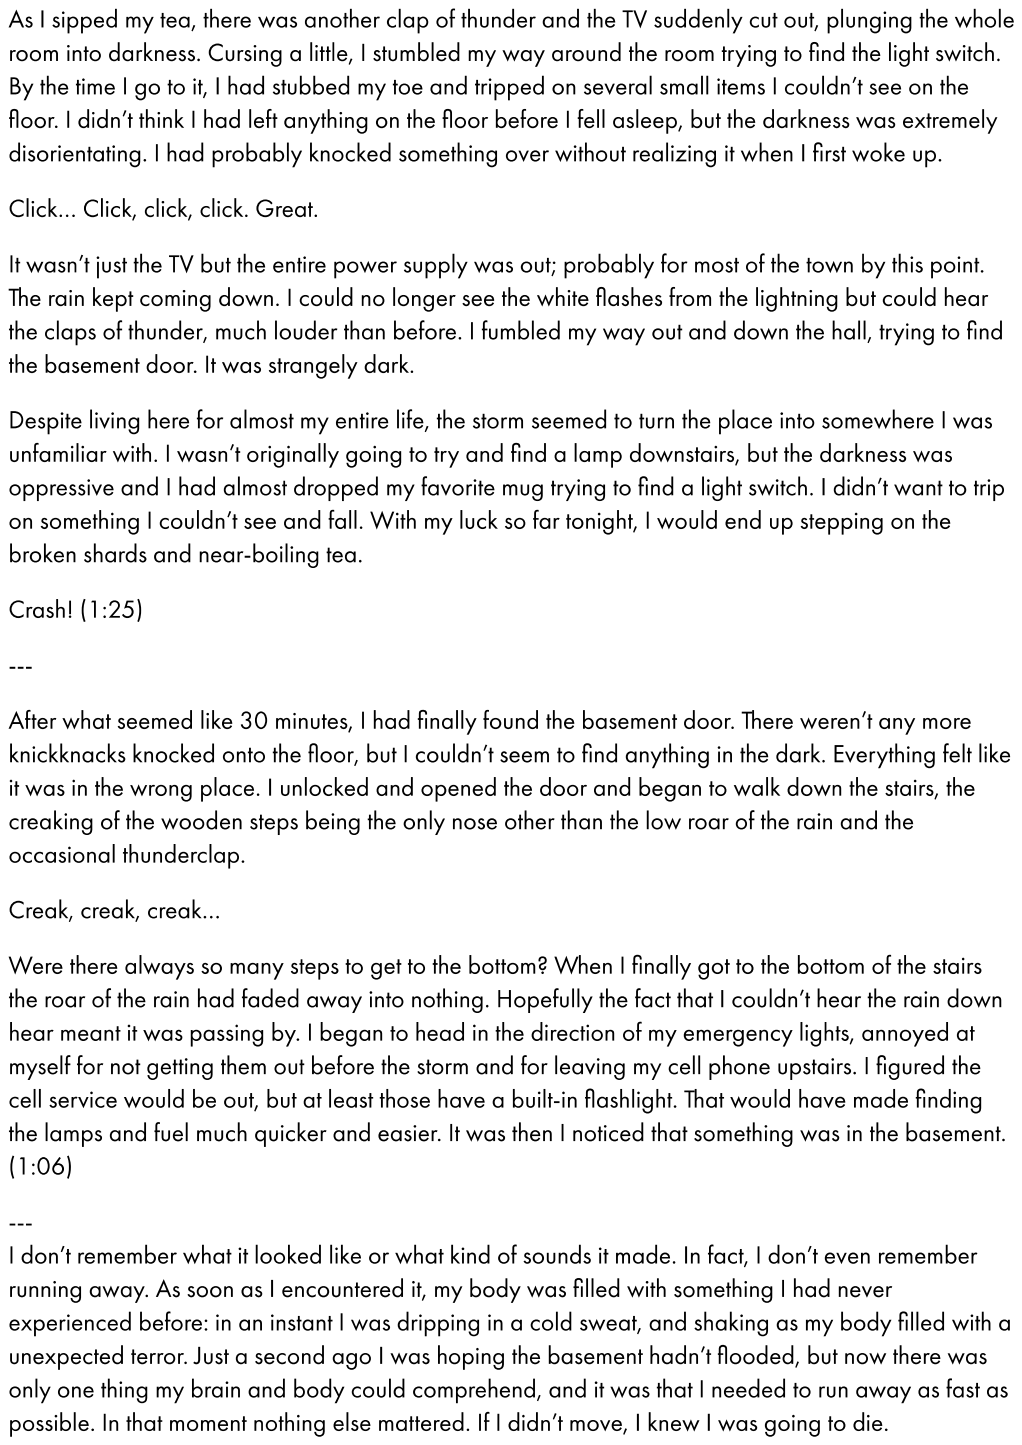
[picture p311: page 20]
