mbardin/Cyberinet/Music Composition Scores/New folder/puzzleFistCompleteDraft - 2023-05-20_Part10.pdf

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
