mbardin/Cyberinet/other documentation/photos/IMG_0043.JPG

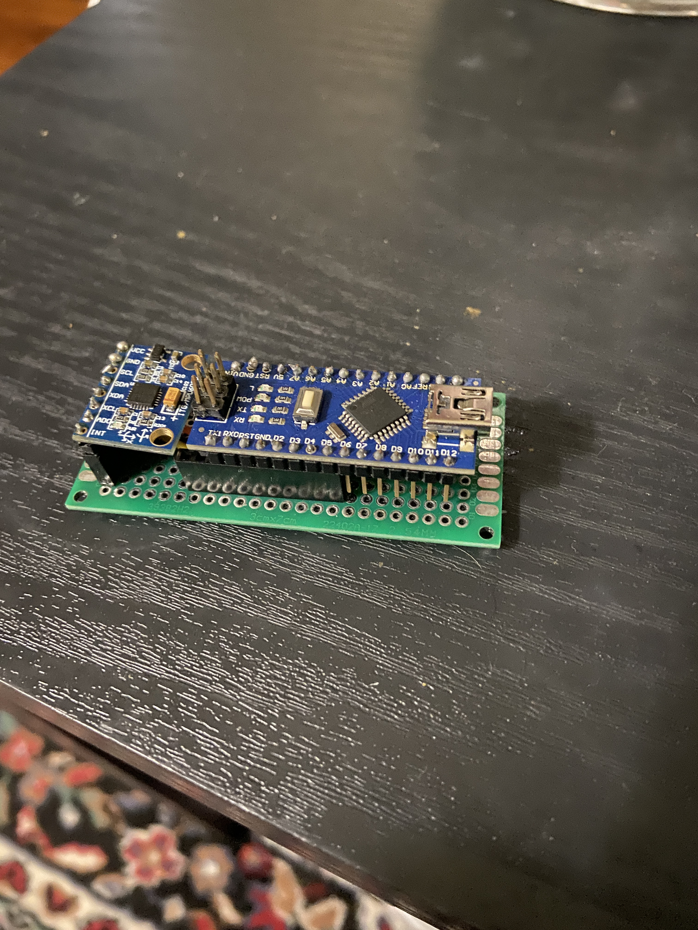
other documentation/photos/IMG_0043.JPG
