mbardin/Cyberinet/other documentation/photos/IMG_0044.JPG

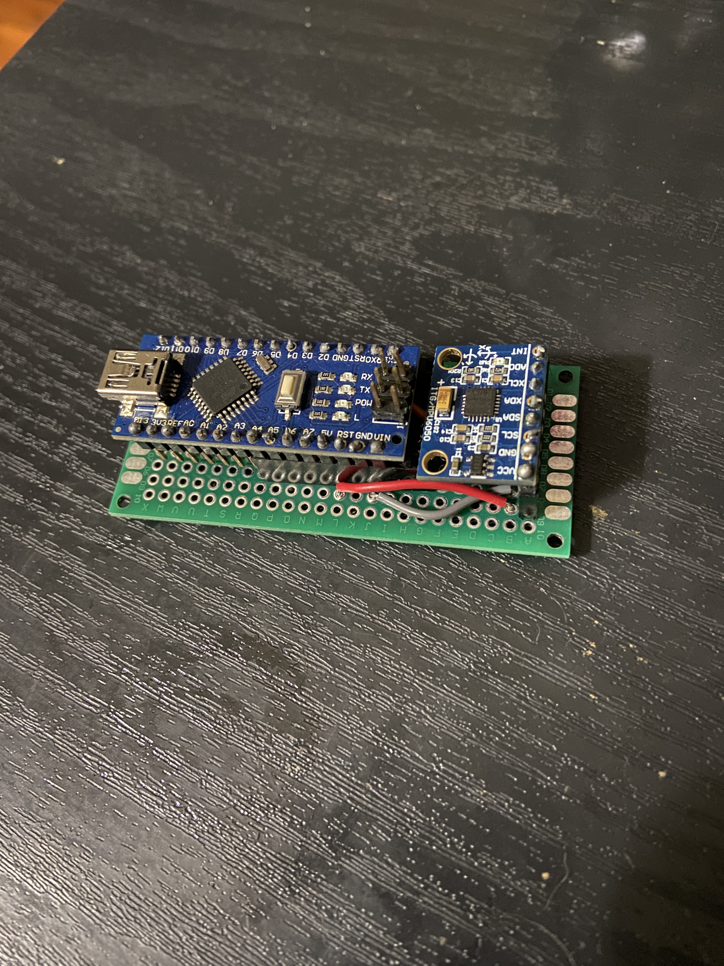
other documentation/photos/IMG_0044.JPG
