mbardin/Cyberinet/other documentation/photos/IMG_0050.JPG

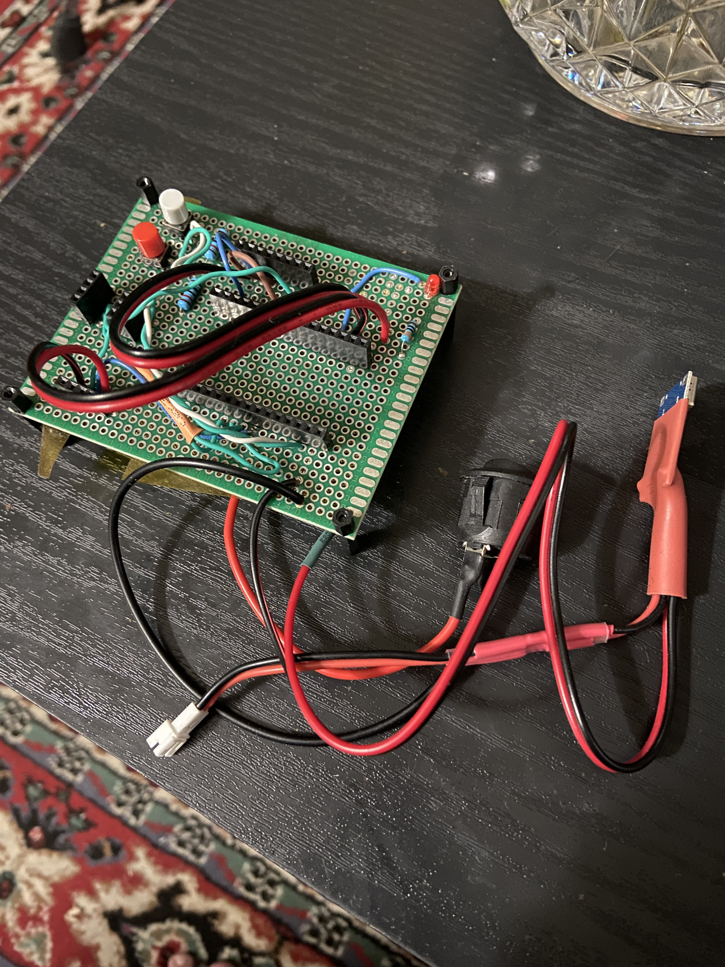
other documentation/photos/IMG_0050.JPG
