mbardin/Cyberinet/other documentation/photos/IMG_0051.JPG

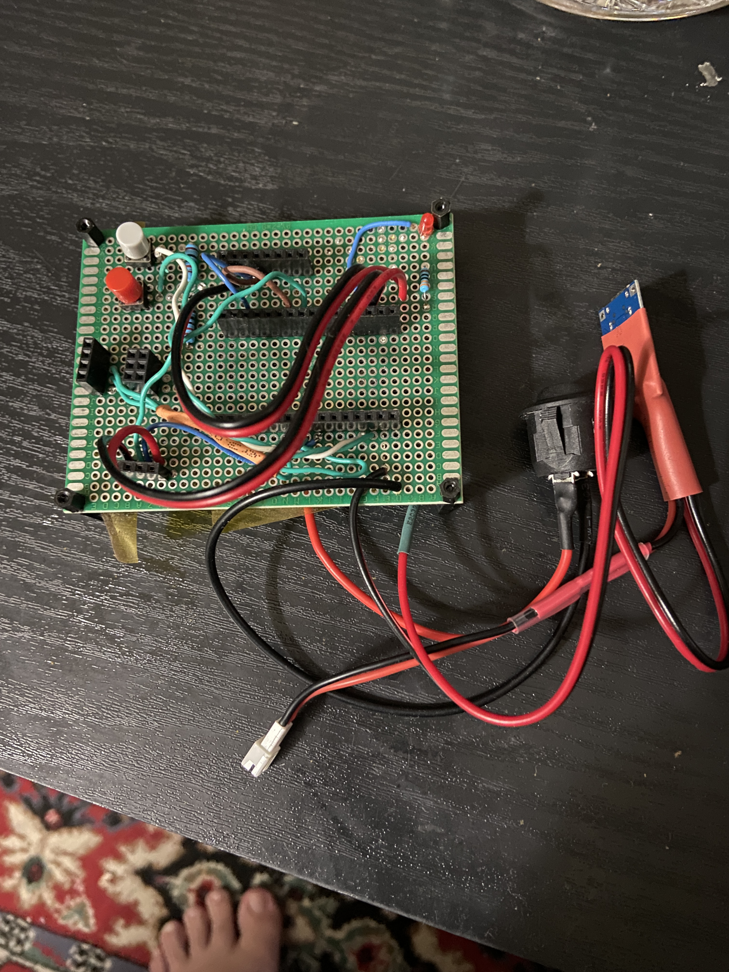
other documentation/photos/IMG_0051.JPG
