mbardin/Cyberinet/other documentation/photos/IMG_0052.JPG

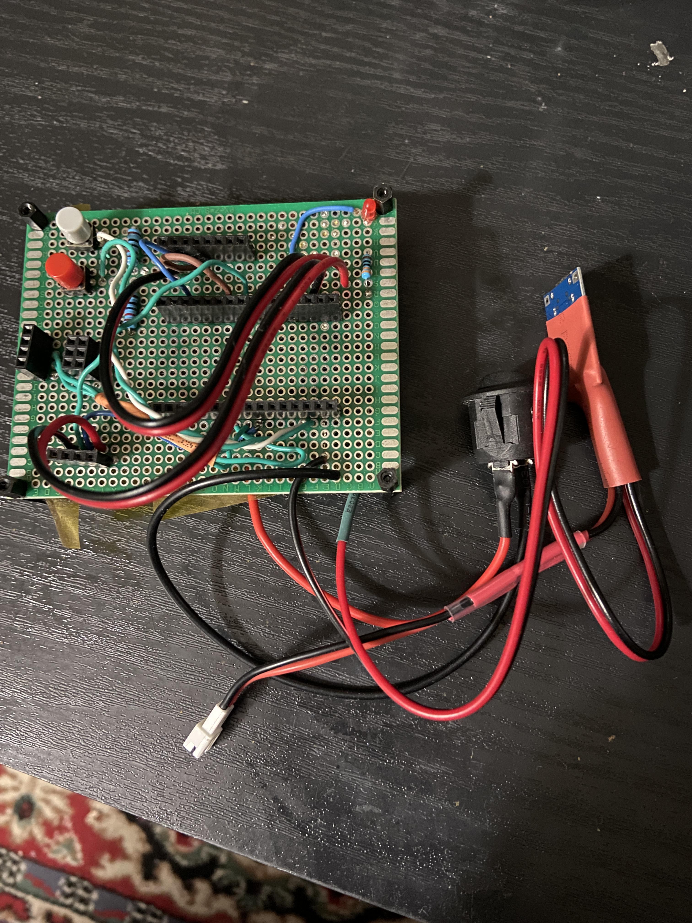
other documentation/photos/IMG_0052.JPG
