mbardin/Cyberinet/other documentation/photos/IMG_0822.JPG

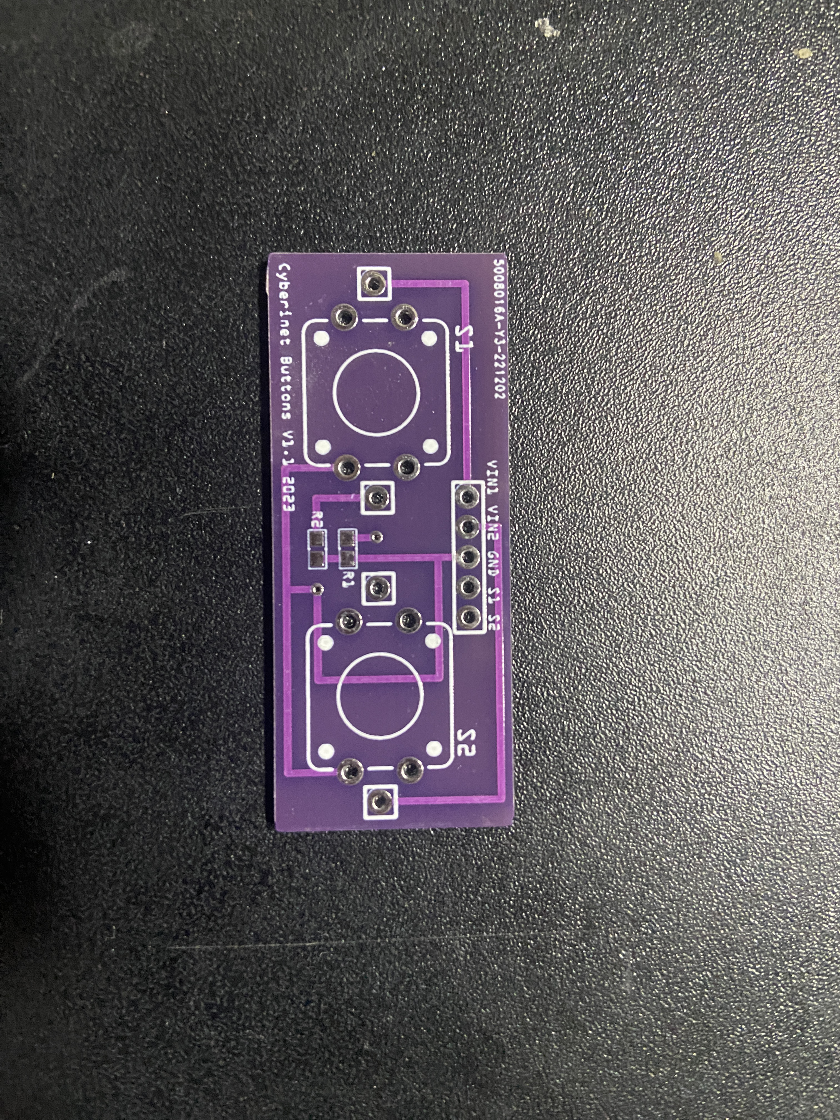
other documentation/photos/IMG_0822.JPG
