mbardin/Cyberinet/other documentation/photos/IMG_0823.JPG

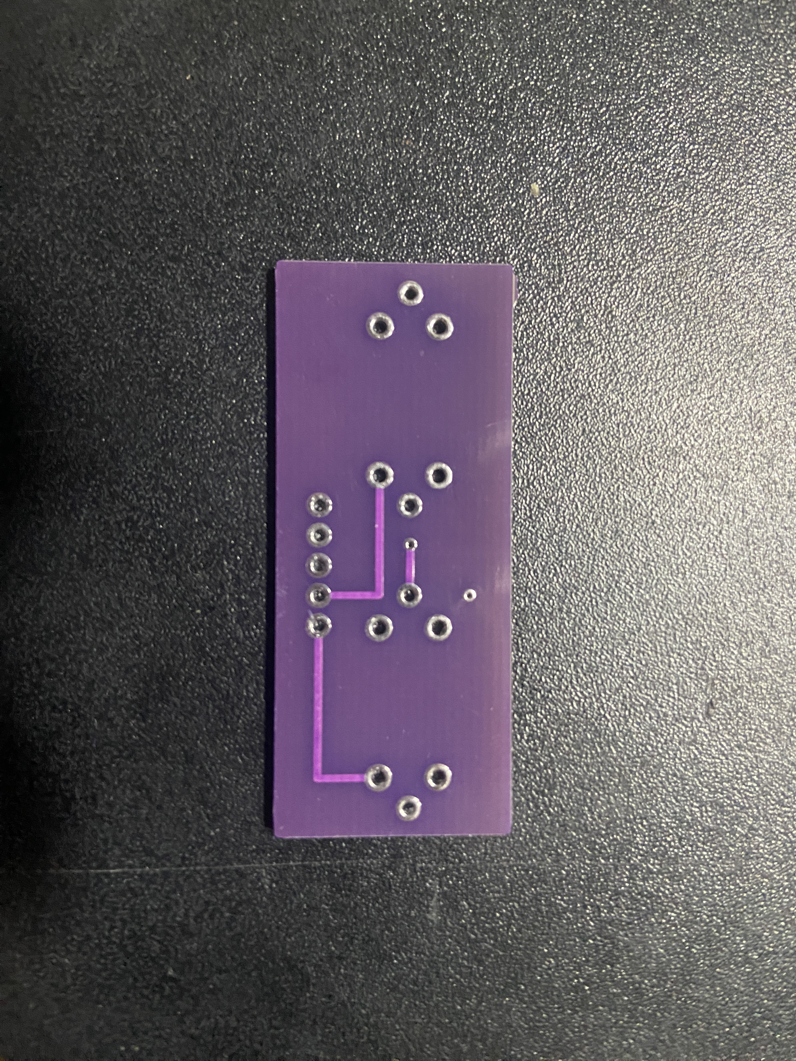
other documentation/photos/IMG_0823.JPG
