mbardin/Cyberinet/other documentation/photos/IMG_1207.JPG

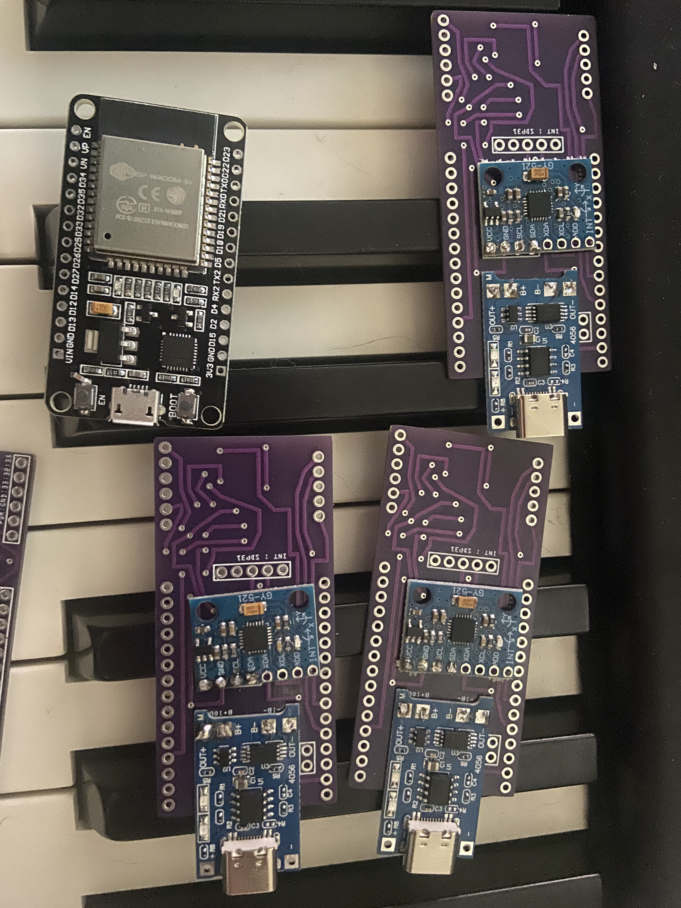
other documentation/photos/IMG_1207.JPG
