mbardin/Cyberinet/other documentation/photos/IMG_1209.JPG

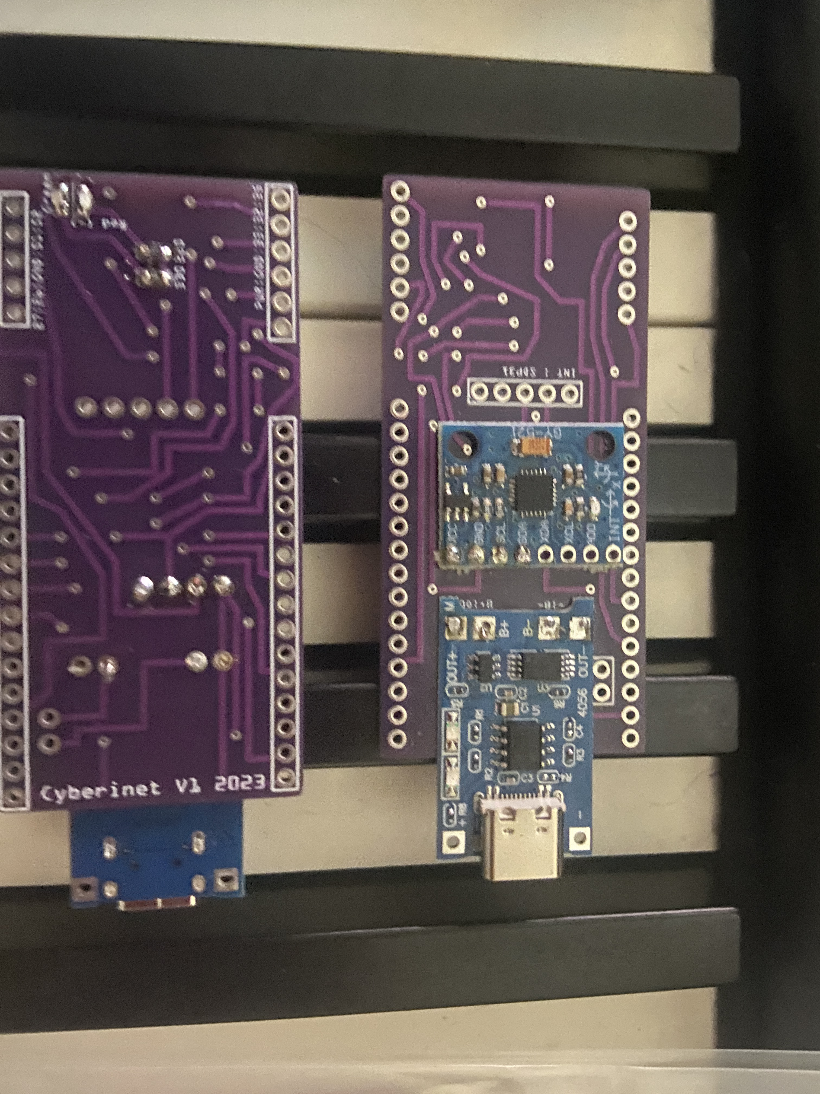
other documentation/photos/IMG_1209.JPG
