mbardin/Cyberinet/other documentation/photos/IMG_1226.JPG

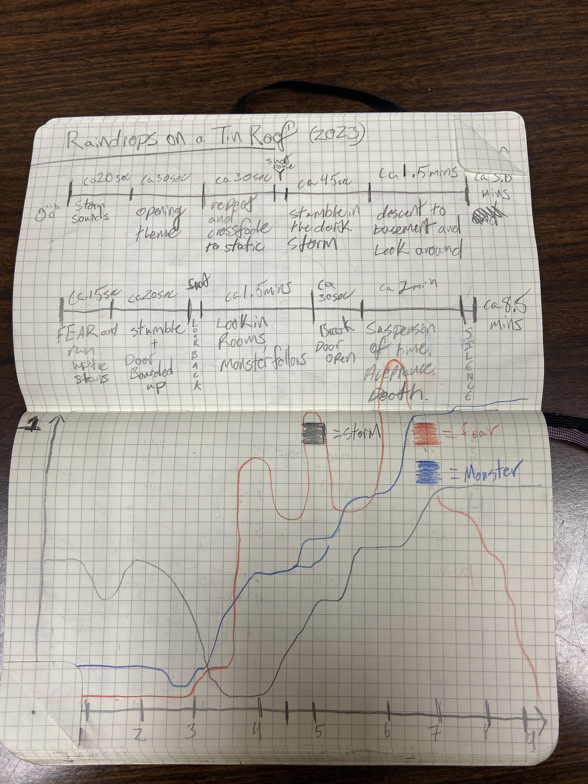
other documentation/photos/IMG_1226.JPG
