mbardin/Cyberinet/other documentation/photos/IMG_1266.JPG

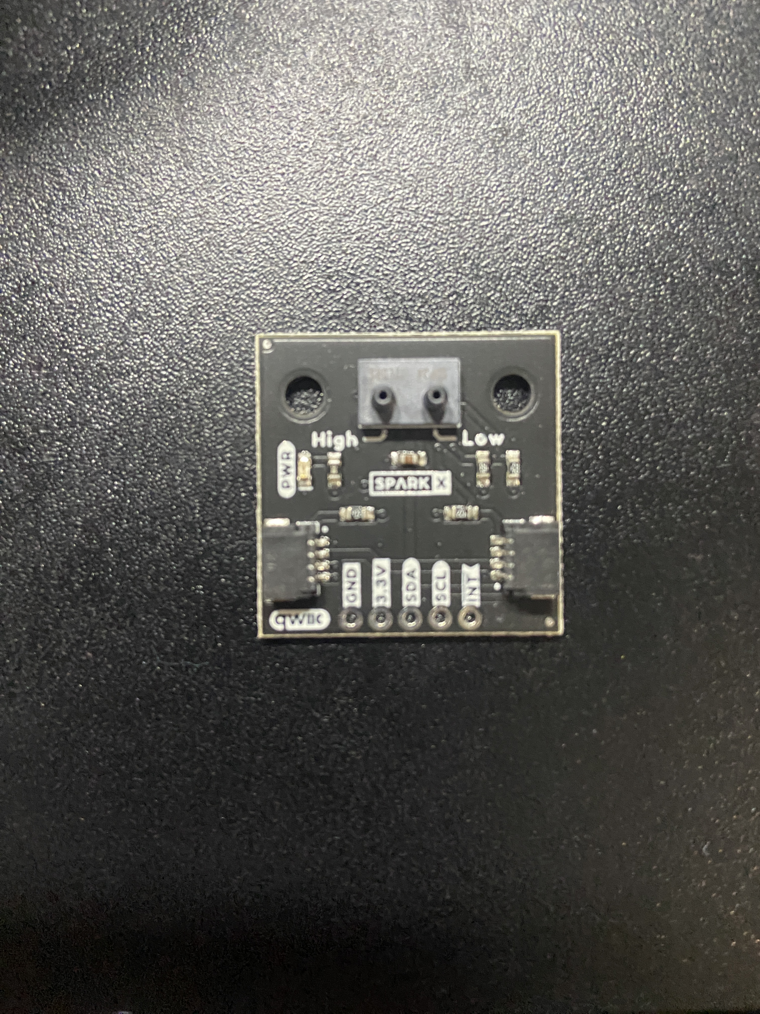
other documentation/photos/IMG_1266.JPG
