mbardin/Cyberinet/other documentation/photos/IMG_1268.JPG

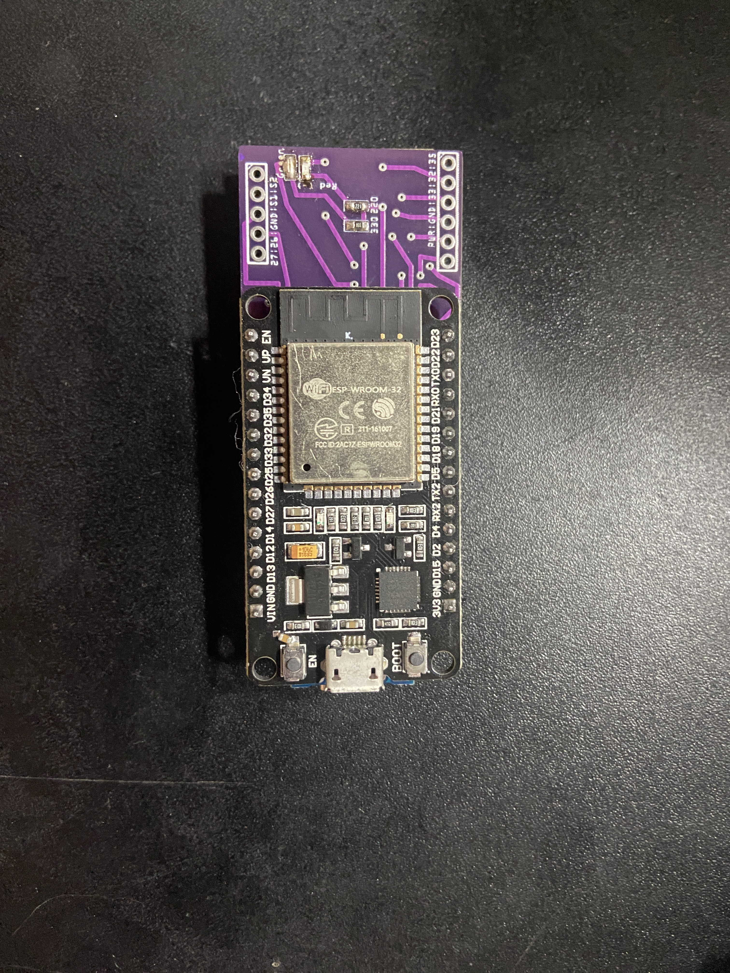
other documentation/photos/IMG_1268.JPG
