mbardin/Cyberinet/other documentation/photos/IMG_1269.JPG

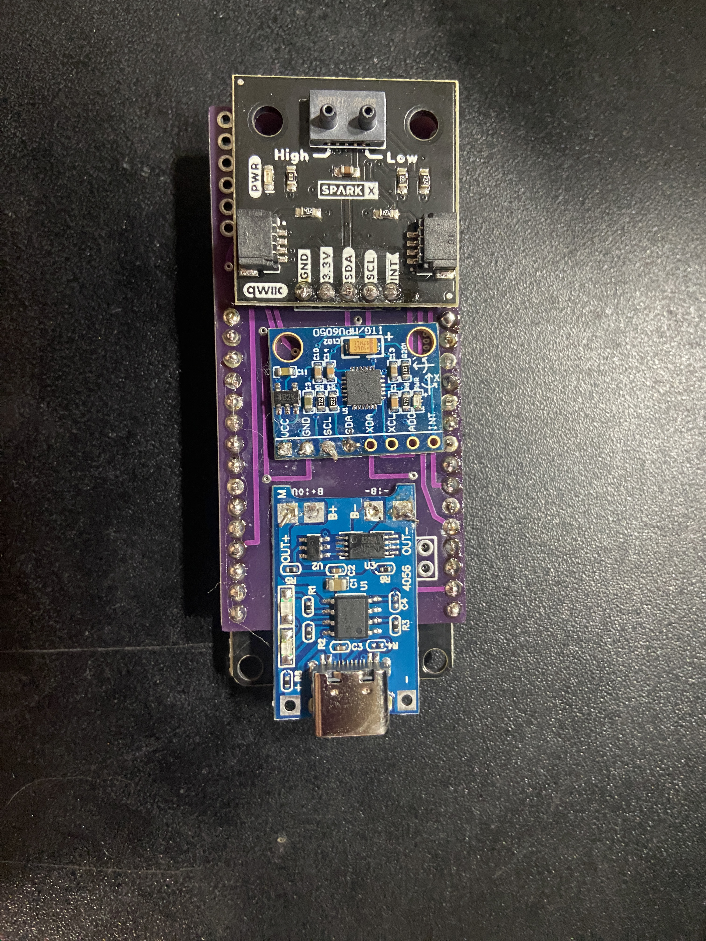
other documentation/photos/IMG_1269.JPG
